chili-chips-ba/openPCIE/0.doc/text/README.md

# Text versions of project documents

Plain-text (Markdown) versions of openPCIE documents that are otherwise only available as PDF, PowerPoint, draw.io or KiCad files. They let text-based tools, including the assistant on the openPCIE product page, read the content.

| File | Generated from |
|---|---|
| `openPCIE_backplane_presentation.md` | `1.pcb/0.doc/OpenPCIE backplane presentation.pptx` (slide text) |
| `PCBA_Functional_Test_Procedure.md` | `1.pcb/0.doc/PCBA_Functional_Test_Procedure_RevB_LaTeX_Source.zip` (LaTeX source of the RevB PDF) |
| `openpci2-backplane_BOM.md` | `1.pcb/openpci2-backplane/openpci2-backplane.kicad_sch` (`kicad-cli` BOM export) |
| `openPCIE-BlockDiagram.md` | `1.pcb/0.doc/openPCIE-BlockDiagram.drawio` (text labels) |

These files are generated; edit the source documents instead. Figures and images are not included.
