chili-chips-ba/openPCIE/5.sim/models/cosim/README.md

# _VProc_ and _mem_model_ Co-simulation Components

The _VProc_ virtual processor and the _mem_model_ sparse memory model (part of _pcievhost_) components form the heart of the co-simulation for the _openPCIE_  top level simulation test bench. The `soc_cpu.VProc` is based on the virtual processor and the memory used by the running programs has access to the memory model's space. Logic can also access the memory model's address space with a provided HDL component. This component is also used in the PCIE interface driver block, and the code running on the _pcievhost_ VIP's _VProc_ also has access to the same memory via the API. Thus, these components are tied together tightly.

## _VProc_

The _VProc_ virtual processor is a VIP co-simulation component that allows a natively compiled user program to be “run” on an HDL processor component instantiated in the logic. C/C++ APIs are provided to initiate read and write transactions on the _VProc_ HDL bus, and for the
advancing simulation time.

<p align="center">VProc virtual processor</p>

_VProc_ has a generic memory mapped bus and this would normally be wrapped in a module to convert this to a standard bus or interconnect protocol, such as AXI or Avalon but, for _openPCIE_, the `soc_cpu.VPROC.picorv32` wrapper converts it to picorv32's native memory interface (`mem_valid`/`mem_ready`) with some simple logic. Multiple _VProc_ test programs components can be instantiated, each with a unique “node” number.

Since the simulator is _Vivado_, the connection between software and HDL is done using the SystemVerilog DPI-C interface. The details of connection between the HDL and running user code won’t be discussed here but suffice it to say that the user program is running in its own thread and the _VProc_ layer software provides both the API and the means to synchronise the user program with the simulation, keeping both in lock-step but allowing the user program to be free flowing code. For each instantiated _VProc_ node the user code has a specific “main” entry point of the form `VUserMain<n>`, where `<n>` is the _VProc_’s node number: e.g. `VUserMain0`, which must have C linkage for DPI requirements. The user programs are compiled into a library and, along with a _VProc_ code library, are linked into a shared object, _VProc.so_, which is loaded by the simulator at run time. There are both C and C++ low level APIs available to user programs and abbreviated versions are shown below.

<p align="center">VProc C and C++ API summary</p>

As well as basic read and write transactions methods, there is also a “tick” method. User programs run infinitely fast with respect to simulation time, so simulation time is advanced when a transaction method is called but can also be advanced with the `tick` method without a memory access transaction. Using these APIs directly gives the means to construct pure test programs that can run on the `soc_cpu.VPROC` component to drive the CSR registers in the core logic and instigate operations. A very simple program of this nature is shown below.

<p align="center">A simple VProc test program</p>

## _mem_model_

The _openPCIE_ test bench makes use of the [mem_model](https://github.com/wyvernSemi/mem_model) co-simulation component HDL. This consists of a sparse memory model , written in C as part of the [_pcievhost_](https://github.com/wyvernSemi/pcievhost) IP, with co-simulation capabilities via a `mem_model` HDL component with various Avalon style ports for memory mapped, burst and write functions. Code running in _VProc_ can access the C model directly via an API, with an abbreviated version shown below.

<p align="center">mem_model C API summary</p>

The write functions take `address` and `data` parameters and, for wider words, a little-endian flag (`le`) to select between endian
modes. The read functions take an `address` and (where appropriate) an `le` parameter and return the read value. All functions have a `node` parameter. Note that the “node” in the API functions is not the same as for _VProc_ but refers to individual address spaces. In almost all use cases this will be the same and is 0.

This model can also be accessed from the HDL using the `mem_model` HDL component, which may be instantiated any number of times, but always accesses the same memory. This allows multiple _VProc_ virtual processors and the simulated test bench logic to access a common memory space.

<p align="center">mem_model HDL component</p>

## VProc and mem_model integration into _openPCIE_

The `5.sim/models/cosim` directory contains library code for the *VProc* virtual processor and *mem_model* sparse memory model co-simulation verification IP, suitable for the Vivado logic simulation environment (other simulators are not supported at this time). This directory contains the HDL modules for the two components. The files that get compiled are `f_VProc.v` and `mem_model.sv`, which pull in the rest (`f_mem_model.v` and the Verilog header files) through `` `include`` inclusions. Thus only these two need to be listed and this directory included in the search path, which is what [`5.sim/tb.prj`](../../tb.prj) does:

```
sv work models/cosim/mem_model.sv
sv work models/cosim/f_VProc.v
```

The DPI software for both the models is pre-compiled into a static library as `lib/libcosimlnx.a` (with a `lib/libcosimwin.a` version for use with the MSYS2/mingw64 environment on Windows). The headers for the models are placed in the `include/` directory. To use the  models' APIs, the user code must include either the  `VProcClass.h` header for the *VProc* C++ API, or `VUser.h` for the *VProc* C API, and the `mem.h` header for the memory model C API. Note that the `VUser.h` and `mem.h` inclusions must be wrapped as C linkage if included in code that will be compiled as C++. E.g.:

```
extern "C" {
#include "VUser.h"
#include "mem.h"
}
```

This is only applicable when writing natively compiled simulation test code. When compiling the application code natively for *VProc*, the headers will be included correctly by the co-simulation hardware abstraction layer (HAL).

## More Information

More information on using these co-simulation models can be found in the [*VProc* manual](https://github.com/wyvernSemi/vproc/blob/master/doc/VProc.pdf) and [*mem_model* manual](https://github.com/wyvernSemi/mem_model/blob/main/doc/mem_model_manual.pdf).
