chili-chips-ba/openPCIE/5.sim/models/pcievhost/README.md

# The _pcievhost_ Verification IP

## Table of Contents

* [Introduction](#introduction)
* [The HDL Component](#the-hdl-component)
* [Link Traffic Display](#link-traffic-display)
* [The Pcie C Model](#the-pcie-c-model)
  * [Internal Architecture](#internal-architecture)
  * [User API Summary](#user-api-summary)
    * [Model Initialisation and Configuration](#model-initialisation-and-configuration)
    * [Transaction Layer Packet Generation](#transaction-layer-packet-generation)
    * [Data Link Layer Packet Generation](#data-link-layer-packet-generation)
    * [Ordered Set Generation](#ordered-set-generation)
    * [Internal Memory Access](#internal-memory-access)
    * [Internal Configuration Space Access](#internal-configuration-space-access)
    * [Receiving Data](#receiving-data)
* [Additionally Provided Functionality](#additionally-provided-functionality)
  * [C plus plus Support](#c-plus-plus-support)
  * [Running the Model as an Endpoint](#running-the-model-as-an-endpoint)
    * [Configuration Space Helper Structures](#configuration-space-helper-structures)
    * [Setting Up the Configuration Space](#setting-up-the-configuration-space)
  * [Model Limitations](#model-limitations)
    * [Endpoint Feature Limitations](#endpoint-feature-limitations)
    * [LTSSM Limitations](#ltssm-limitations)
    * [Model Verification](#model-verification)

## Introduction

The [_pcievhost_](https://github.com/wyvernSemi/pcievhost) VIP is a co-simulation element that runs a PCIe C model on a [_VProc_](https://github.com/wyvernSemi/vproc) virtual processor to drive lanes within a PCIe 1.1 or 2.0 link, with support for up to 16 lanes. The PCIe C model provides an API for generating PCIe traffic over the link with some additional helper functionality for modelling _some_ of the link training LTSSM features (not strictly part of the model). It also provides an internal sparse memory model as a target for MemRd and MemWr transactions and, when configured as an endpoint, a configuration space as a target for CfgRd and CfgWr transactions. Features of the API allow for the configuration space to be pre-programmed with valid configurations and a read-only mask overlay, though there is no support for 'special' functions like write one to clear etc.

More details of the model can be found in the [_Pcievhost_ manual](https://github.com/wyvernSemi/pcievhost/blob/master/doc/pcieVHost.pdf).

## The HDL component

A Verilog module for the _pcievhost_ model is provided in a `pcieVHost.v` file in the `5.sim/models/pcievhost/verilog/pcieVHost` directory. This is wrapped in some BFM Verilog, `pcieVHostPipex1.v`, in the same directory, which presents a single Link port, as PIPE TX and RX data signals. The diagram below shows the module's ports and parameters.

<p align=center>

</p>

The module's `pcieclk` clock and reset must be synchronous (i.e. the reset originate from the same clock domain) and the clock run at the PCIe raw bit rate $\div$ 10. So for GEN1 this is 250MHz (4000ps period) and GEN2 this is 500MHz (2000ps period). The module can convert from a sybol stream to wider PIPE widths of 16, 32 or 64, and these are converted between these widths and the symbol stream with internal logic and using a PIPE clock (`pclk`), which needs to be the `pcieclk` divided by the PIPE data width over 8. E.g. If a 64 bit PIPE data width, then the `pclk` frequency must be `pcieclk` / 8, or 31.25MHz (GEN1) or 62.5MHz (GEN2).

The model, by default, transfers 8b10b encoded data but can be configured in the software to generate unencoded and unscrambled data, where bits 7:0 are a byte value, and bit 8 is a 'K' symbol flag when set, and this configuration must be done for the _openpcie2-rc_ project.

The _pcieVHost_ component has four Parameters to configure the model. The first, `LinkWidth`, configures which lanes will be active and always starts from lane 0, defaulting to all 16 lanes. For _openpcie2-rc_, this is hardwired to 1 inside `pcieVHostPipex1`.  Note that the ports for the unused lanes are still present but can be left unconnected. The second parameter is `EndPoint`. This is used to enable endpoint features in the model and does so if set to a non-zero value, with 0 being the default setting. For _openpcie2-rc_, this should be set to 1. The thrid parameter is `NodeNum` which sets the node number of the internal _VProc_ component. Each instantiated _VProc_, whether part of a _pcievhost_ model, or not, must have a unique node number to associate itself with a particular user program. The default value for `NodeNum` is 8. Lastly, the `DataWidth` parameter sets the PIPE data port widths.

More details of the `PcieVhost` HDL component can be found in the [_pcievhost_ manual](https://github.com/wyvernSemi/pcievhost/blob/master/doc/pcieVHost.pdf).

## Link Traffic Display

The _pcievhost_ model has the capability to display link traffic to the console that the simulation is runing in, with control over the level of detail available, including disabling completely, and in which cycles it is turned on and off. It, by default, adds colour to distinguish between traffic flowing downstream from traffic flowing upstream, though the model can be configureed to disable this when, for example, runing in a GUI that can't interpret these formatting codes.

 A `ContDisps.hex` configuration file will be read by the software from a `hex` directory, below the local run directory. This allows control of displaying various PCIe layer data, from PHY, through DLL and TL, bit-mapped onto an 8 bit value. Each value is associated with a _decimal_ time stamp (in cycles) as to when the display value is enabled or not. A typical file might look like the following:

```
// Example ContDisps.hex file
// Copy to the appropriate test/hex directory, and edit as necessary.
//                      +8              +4              +2              +1
//  ,---> 11 - 8:    DispSwNoColour     DispSwEnIfEp   DispSwEnIfRc    DispSwTx
//  |,-->  7 - 4:    DispRawSym         DispPL         DispDL          DispTL
//  ||,->  3 - 0:    Unused             DispStop       DispFinish      DispAll
//  ||| ,-> Time (clock cycles, decimal)
//  ||| |                          
    370 000000000000
    002 009999999999
```
The file has two numbers on each active line, with the first hex number being the control values and the second a <u>decimal</u> value timestamp (in clock cycles) when the control should become active. For the controls, the top nibble controls enabling output for Endpoint and Root Complex links separately to allow for co-existence with other extenal link displays. So, bit 11 controls the colour formatting by enabling (when 0) or disabling (when 1). Disabling the formatting is useful if the output is sent to a simulator's GUI console which may not support the colour encoding and messes up the output. Bits 10 and 9 enable display if an endpoint end or root-complex end model respectively. By default, only received traffic is displayed but, if no other external traffic display is available, then transmitted data can be displayed if bit 8 is set.

The level of detail to display is controlled by bits 4 to 7. The bit 7 can enable display of raw data link data, without any processing, though generates a lot of output and is hard to interpret. Bits 6 dow to 4 control formatted output for the three main levels of PCIe traffic; namely physical, data link and transactions layers, bits 6 down to 4 controlling these respectively. The display will automatically indent higher layers if lower layers are enabled to allow easy distinguishing of the output.

The lowest nibble has some simulator control in bits 1 and 2, to either stop the simulation (without exiting) or finish the simulation (end and close). Bit 0 is a 'force all' control to display all layers of the link traffic, regardless of the other settings.

A fragment of some link display output, using the `ContDisps.hex` file example above, is shown in the diagram below:

<p align=center>
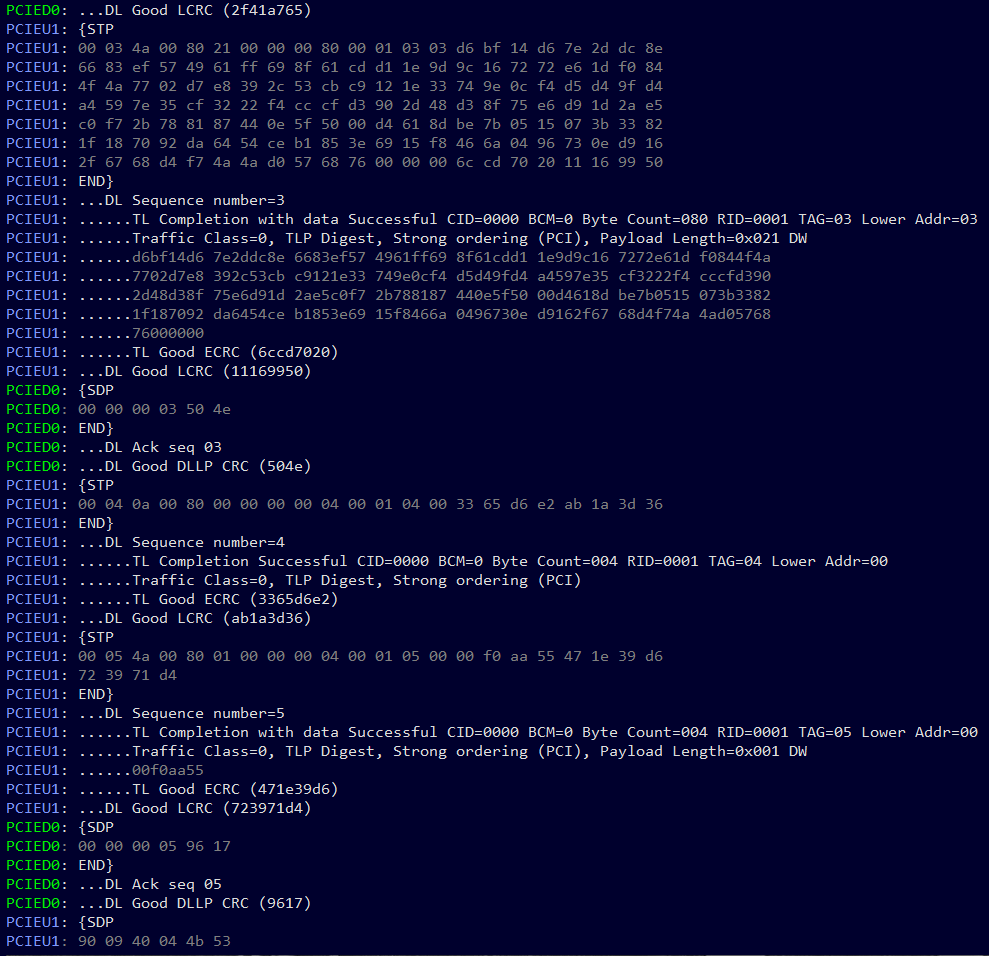
[picture p65: 5.sim/models/pcievhost/images/pcie_disp_terminal.png]

</p>

More details on the link display can be found in the [_pcievhost_ manual](https://github.com/wyvernSemi/pcievhost/blob/master/doc/pcieVHost.pdf).

## The PCIe C Model

### Internal Architecture

The diagram below summarises the core PCIe model functionality, along with the connection to a logic simulation via the _VProc_ co-simulation component.

<p align=center>
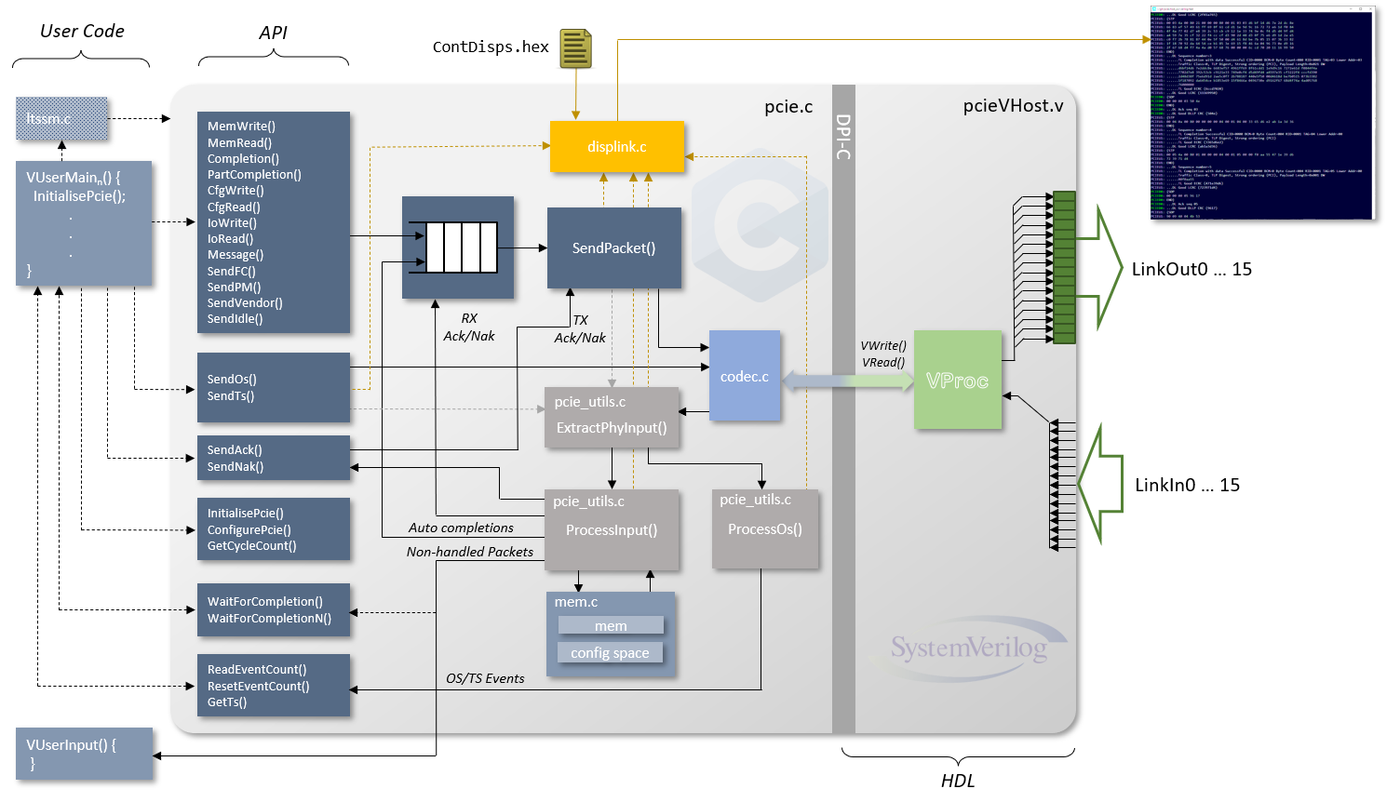
[picture p66: 5.sim/models/pcievhost/images/pcievhost_architecture.png]

</p>

On the left of the diagram are the two user supplied functions. The `VUserMain`<i>n</i> function is the main entry point for user code and this has access to the [model's API](#user-api-summary). Optionally, a user callback function can be registered (`VUserInput` in the diagram) that gets called to with non-handled packets (e.g. read completions) that are received over the link.

The left column of boxes are the various API functions available, categorised by function. The first group generate TLP or DLLP packets that get queued, before being sent to `SendPacket`. The non-automatic sending of ACKs and NAKs bypass the queue and are sent straight to the `SendPacket` function. The `SendPacket` function itself sends its TLP or DLLP packets to the `codec` which scrambles and encodes the data and drives the output on the link.

The `codec` code also process input data, decoding and descrambling, passing on to `ExtractPhyInput`. Training sequences and other ordered set data is sent to `ProcessOs` whilst TLPs and DLLPs are sent to `ProcessInput`. The API can read received OS event counts from the `ProcessOs` function. `ProcessInput` has access to the internal memory for MemRd and MemWr TLPs and (for endpoints) the config space for CfgRd and CfgWr TLPs. It will automatically generate (valid) completions for reads and add to the queue. All other TLPs are sent to any registed user callback.

### User API Summary

The _pcievhost_ model is a highly complex model and the API is quite large to match this. This document can only summarise the main features and usage and reference to the [_Pcievhost_ manual](https://github.com/wyvernSemi/pcievhost/blob/master/doc/pcieVHost.pdf) _must_ be made for the finer details of argumets and usage. The information below refers to the low level C model's API but a C++ class (`pcieModelClass`) is also provided which wraps the functions up into class methods which are slightly easier to use.

#### Model Initialisation and Configuration

| **API Function** | **Description** |
|---|---|
| `InitialisePcie` | Initialise the model |
| `ConfigurePcie` | Configure the model |
| `ConfigurePcieLtssm`  | Configure the model's LTSSM (part of the external LTSSM model, API defined in `ltssm.h`)|
| `PcieSeed` | Seed internal random number generator |

The `InitailsePcie` is called before any other function to initialise the model. The user can supply a pointer to a callback function which will be called with data for all unhandled received packets. Optionally a user supplied pointer may also be gived which is returned when the callback is called, allowing a user to store away key information for cross checking, verification or any other purpose. The model does not process this pointer itself.

The model is highly configurable with many different parameters which may be set, one at a time, using the `ConfigurePcie` and `ConfigurePcieLtssm` functions that take a type and, where applicable, value argument. .

##### Configuration via ConfigurePcie

The following table shows the valid configuration `type` settings and expected `value` for the use with the `ConfigurePcie(type, value)` function.

| **TYPE** |**VALUE**|**UNITS**| **Description** |
|---|---|---|---|
| CONFIG_FC_HDR_RATE | yes | cycles  | Rx Header consumption rate (default 4) |
| CONFIG_FC_DATA_RATE | yes | cycles  | Rx Data consumption rate (default 4) |
| CONFIG_ENABLE_FC | no | | Enable auto flow control (default) |
| CONFIG_DISABLE_FC | no | | Disable auto flow control |
| CONFIG_ENABLE_ACK | yes | cycles  | Enable auto acknowledges with processing rate (default rate 1) |
| CONFIG_DISABLE_ACK | no | | Disable auto acknowledges |
| CONFIG_ENABLE_MEM | no | | Enable internal memory (default) |
| CONFIG_DISABLE_MEM | no | | Disable internal memory |
| CONFIG_ENABLE_SKIPS | yes | cycles  | Enable regular Skip ordered sets, with interval (default interval 1180) |
| CONFIG_DISABLE_SKIPS | no | | Disable regular Skip ordered sets |
| CONFIG_DISABLE_SCRAMBLING | no | | Disable data scrambling |
| CONFIG_ENABLE_SCRAMBLING | no | | Enable data scrambling (default) |
| CONFIG_DISABLE_8B10B | no | | Disable 8b10b encoding and decoding |
| CONFIG_ENABLE_8B10B | no | | Enable 8b10b encoding and decoding (default) |
| CONFIG_DISABLE_ECRC_CMPL | no | | Disable ECRC auto-generation on completions for requests with ECRCs |
| CONFIG_ENABLE_ECRC_CMPL | no | | Enable ECRC auto-generation on completions for requests with ECRCs (default) |
| CONFIG_ENABLE_UR_CPL | no | | Enable auto unsupported request completions (default) |
| CONFIG_DISABLE_UR_CPL | no | | Disable auto unsupported request completions |
| CONFIG_ENABLE_INTERNAL_MEM | no | | Enable internal memory (default) |
| CONFIG_DISABLE_INTERNAL_MEM | no | | Disable internal memory (packets passed to user callback if registered) |
| CONFIG_ENABLE_DISPLINK_COLOUR  | no | | Enable colour formatting of link display output (default) |
| CONFIG_DISABLE_DISPLINK_COLOUR | no | | Disable colour formatting of link display output |
| CONFIG_POST_HDR_CR† | yes | credits | Initial advertised posted header credits (default 32) |
| CONFIG_POST_DATA_CR† | yes | credits | Initial advertised posted data credits (default 1K) |
| CONFIG_NONPOST_HDR_CR† | yes | credits | Initial advertised non-posted header credits (default 32) |
| CONFIG_NONPOST_DATA_CR† | yes | credits | Initial advertised non-posted data credits (default 1) |
| CONFIG_CPL_HDR_CR† | yes | credits | Initial advertised completion header credits (default ∞) |
| CONFIG_CPL_DATA_CR† | yes | credits | Initial advertised non-posted data credits (default ∞) |
| CONFIG_CPL_DELAY_RATE† | yes | cycles  | Auto completion delay rate (default 0) |
| CONFIG_CPL_DELAY_SPREAD† | yes | cycles  | Auto completion delay randomised spread (default 0) |

† Call immediately after `InitialisePcie()` to take effect from time 0

##### Configuration via ConfigurePcieLtssm

The following table shows the valid configuration `type` settings and expected `value` for use with the `ConfigurePcieLtssm(type, value)` function.

| **TYPE** |**VALUE**| **UNITS** | **Description** |
|---|---|---|---|
| CONFIG_LTSSM_LINKNUM†† |  yes | integer | Training sequence advertised link number (default 0) |
| CONFIG_LTSSM_N_FTS†† |  yes | integer | Training sequence number of fast training sequences (default 255) |
| CONFIG_LTSSM_TS_CTL†† |  yes | integer | Five bit TS control field (default 0) |
| CONFIG_LTSSM_DETECT_QUIET_TO†† |  yes | cycles | Detect quiet timeout (default 1500/6M, depending if `LTSSM_ABBREVIATED` defined or not) |
| CONFIG_LTSSM_POLL_ACTIVE_TO_COUNT†† |  yes | cycles | Polling active TX count (default 16/1024, depending if `LTSSM_ABBREVIATED` defined or not)|
| CONFIG_LTSSM_ENABLE_TESTS†† |  yes | bit mask  | Enable LTSSM test exceptions (default 0) |
| CONFIG_LTSSM_FORCE_TESTS†† |  yes | bit mask  | Force LTSSM test exceptions (default 0) |
| CONFIG_LTSSM_DISABLE_DISP_STATE†† |  yes | integer | Disable display of LTSSM state to console (default 0 = display state) |

†† Call before calling `InitLink()` to take effect in training sequences.

Further details of model configuration are to be found in the [_pcievhost_ manual](https://github.com/wyvernSemi/pcievhost/blob/master/doc/pcieVHost.pdf)

Internally, the model can generate random data and the generator can be seeded with `PcieSeed`. The internal code uses `PcieRand` to generate randome data, but this is also available as part of the API. Finally, the model keeps a count of cycles internally, and the value may be retrieved with `GetCycleCount`.

#### Transaction Layer Packet Generation

| **API Function** | **Description** |
|---|---|
| `MemWrite` | Generate a memory write transaction |
| `MemRead` | Generate a memory read transaction |
| `Completion` | Generate a Completion transaction |
| `PartCompletion` | Generate a partial completion transaction |
| `CfgWrite` | Generate a configuration space write transaction |
| `CfgRead` | Generate a configuration space read transaction  |
| `IoWrite` | Generate an IO write transaction |
| `IoRead` | Generate an IO read transaction |
| `Message` | Generation a message transaction |

The above functions are called with varying arguments (see the [_pcievhost_ manual](https://github.com/wyvernSemi/pcievhost/blob/master/doc/pcieVHost.pdf) for details) and all have a 'digest' version (e.g. `MemWriteDigest`) which have an additional argument to select whether a digest (i.e. an ECRC) is generated or not, with the above functions defaulting to generating a digest. There are also 'delay' versions of the `Completion` and `PartCompletion` function which will not send out the packets immediately but after some delay as configured during the model initialisation.

A user program can also wait for a completion to arrive, or a number of completions, with the `WaitForCompletion` and `WaitForCompletionN` functions.

#### Data Link Layer Packet Generation

| **API Function** | **Description** |
|---|---|
| `SendAck` | Send an acknowledgement packet |
| `SendNak` | Send an not-acknowledgement packet |
| `SendFC` | Send a flow control packet |
| `SendPM` | Send a power manegement packet |
| `SendVendor` | Send a vendor specific packet |

#### Ordered Set Generation

| **API Function** | **Description** |
|---|---|
| `SendIdle` | Send idle symbols on all active lanes |
| `SendOs` | Send an ordered set down all active lanes |
| `SendTs` | Send a training sequence ordered set on all active lanes | 

These functions generate ordered sets on the link lanes, with `SendTs` automatically generating lane numbers if not called to generate `PAD`. Internally the model keeps counts of the reception of training sequences on each lane and these can be read using the `ReadEventCount` function and, if required, the counts may be reset with `ResetEventCount`. To fetch the last training sequence processed on a given lane, the `GetTS` function can be used.

#### Internal Memory Access

| **API Function** | **Description** |
|---|---|
| `WriteRamByte` | Write a byte to internal memory |
| `WriteRamHWord` | Write a 16-bit half-word to internal memory |
| `WriteRamWord` | Write a 32-bit word to internal memory |
| `WriteRamDWord` | Write a 64-bit double word to internal memory |
| `ReadRamByte` | Read a byte from internal memory |
| `ReadRamHWord` | Read a 16-bit half-word from internal memory |
| `ReadRamWord` | Read a 32-bit word from internal memory |
| `ReadRamDWord` | Read a 64-bit double word from internal memory |
| `WriteRamByteBlock` | Write a block of bytes to internal memory  |
| `ReadRamByteBlock`  | Read a block of bytes from internal memory |

The _pcievhost_ model has an internal sparse memory model which can support a full 64-bit address space. This is used as a target for received MemWr and MemRd transactions. As well as accessing this space via PCIe transactions, the memory model has its own API functions to do reads and writes of bytes, 16-bit words, and 32-bit words, as well as reading and writing of multiple byte blocks.

#### Internal Configuration Space Access

| **API Function** | **Description** |
|---|---|
| `WriteConfigSpace` | Write a 32-bit value to the configuration space |
| `ReadConfigSpace` | Write a 32-bit value from the configuration space |
| `WriteConfigSpaceMask` | Write a 32-bit mask value to the configuration space mask (bits set to 1 become read only over PCIe) |
| `ReadConfigSpaceMask`  | Read a 32-bit value from the configuration space mask |

If a _pcievhost_ is configured as an endpoint it then has an internal 4096 by 32-bit configuration memory. By default this is blank, but CfgWr and CfgRd transactions can access this space. To configure this space the `WriteConfigSpace` (and its `ReadConfigSpace` counterpart) can be used to set up an valid configuration space settings. A shadow mask memory is also available, which defaults to all 0s, to set any number of bits to be read only. There is a one-to-one correspondence to the main configuration memory, but if a mask bit is set, then the corresponding config space bit becomes read only when accessed over the link with CfgWr transactions. The mask memory is set using the `WriteConfigSpaceMask` and can be inspected with `ReadConfigSpaceMask`.

#### Receiving Data

If a user callback function was registered when `InitialisePcie()` was called this will be invoked with any received packet that the model did not handle itself. The most common of these will be completion packets received for a memory or configuration read. When the callback is invoked the packet, via a point of type `pPkt_t` is passed in along with a status and, if a user pointer was passed in when registering the callback, this is also passed in.

The `status` value is bit map of error flags ORed together. The following table lists the possible bit seeting types, with `PKT_STATUS_GOOD` being a valueo fo 0.

|**Status Value** | **Packet type** |
|---|---|
|PKT_STATUS_GOOD | all |
|PKT_STATUS_BAD_LCRC | TLP and DLLP |
|PKT_STATUS_BAD_ECRC | TLP |
|PKT_STATUS_UNSUPPORTED | TLP completion  |
|PKT_STATUS_NULLIFIED | TLP |

The received packet is passed in with a pointer to a structure as defined below:

```C
typedef struct  pkt_struct {
    pPkt_t      NextPkt;     // Pointer to next packet to be sent
    PktData_t   *data;       // Pointer to a raw data packet, terminated by -1
    int         seq;         // DLL sequence number for packet (-1 for DLLP)
    int         Retry;
    uint32_t    TimeStamp;
    uint32_t    ByteCount;
} sPkt_t;
```
The `NextPtr` can be ignored by the callback, but the `data` argument is a pointer to a set of byte values representing the whole raw packet. Each byte value is of `PktData_t` type, which is not an 8-bit type, so cannot be overlaid as an array of `char`, for instance. The last byte in teh packet is followed by a -1 to mark the end of the data. The `seq` field gives the sequence number of the received packet and the `Retry` field is a count ofthe number of retries for the packet that have already occured. A `Timestamp` field provides a clock cycle count for the time the packet was fuly received and passed to the callback. Finally, a `ByteCount` gives the size of the payload for the packet (in bytes), which can be 0.

A set of helper macros are avilable to process the raw packet data. To extract the payload data, for example the `GET_TLP_PAYLOAD_PTR(pkt)` returns a pointer to the beginning of the payload data (if any), taking care of whether the packet has a 3 or 4 word header. Using this, along with the `ByteCount` value, the data can be extracted from the packet. Some highlights from the set of available macros are given below :

|**Macro** |**Description** |
|---|---|
| GET_TLP_TYPE(pkt) | Get the type code of the TLP packet (as defined in `pci_express.h`) |
| GET_TLP_ADDRESS(pkt) | Get a TLP's address of as `uint64_t` |
| GET_TLP_FBE(pkt) | Get a TLP packet's first byte enable value |
| GET_TLP_LBE(pkt) | Get aTLP packet's last byte enable value |
| GET_TLP_RID(pkt) | Get a TLP packet's requester ID |
| GET_TLP_TAG(pkt) | Get a TLP packet's tag value |
| TLP_HAS_DIGEST(pkt)  | Flag if a TLP has an ECRC digest |
| TLP_IS_POSTED(pkt) | Flag if a TLP is a posied request |

The TLP packet types defined (in `pci_express.h`) are as shown in the table below:
| **TYPE** | **Description** |
|---|---|
|TL_MRD32 | A memory read request with a 32-bit address |
|TL_MRD64 | A memory read request with a 64-bit address |
|TL_MRDLCK32 | A locked memory read request with a 32-bit address |
|TL_MRDLCK64 | A locked memory read request with a 64-bit address |
|TL_MWR32 | A memory write with a 32-bit address |
|TL_MWR64 | A memory write with a 64-bit address |
|TL_IORD | A memory I/O read request |
|TL_IOWR | A memory I/O write |
|TL_CFGRD0 | A Type 0 configuration space read request |
|TL_CFGWR0 | A Type 0 configuration space write |
|TL_CFGRD1 | A Type 1 configuration space read request |
|TL_CFGWR1 | A Type 1 configuration space write |
|TL_MSG | A message with no payload |
|TL_MSGD | A message with payload |
|TL_CPL | A completion with no payload |
|TL_CPLD | A completion with payload |
|TL_CPLLK | A locked access completion with no payload |
|TL_CPLDLK | A locked access completion with payload |

Once a packet has been processed it is <u>vital</u> that the packet passed in to the callback is freed. A `DISCARD_PACKET(pkt)` macro is provided for this purpose, freeing all required memory. This is usually the last line of the callback function as all data will be lost at this point. If any of the data is to be retained it must be copied from the packet before calling this macro. This is what the optional user point might be used for (if one registered on the call to `InitialisePcie()`), where it it might be a point to a queue, and the relevant parts of the packeted added to the queue to be processed by the main part of the program.

A simple example callback function for a _pcievhost_ configured as a root complex, is shown below:

```C
 void VUserInput_0(pPkt_t pkt, int status, void* usrptr)
{
    int idx;

    // Is a DLLP
    if (pkt->seq == DLLP_SEQ_ID)
    {
        DebugVPrint("---> VUserInput_0 received DLLP\n");
    }
    // A TLP
    else
    {
        DebugVPrint("---> VUserInput_0 received TLP sequence %d of %d bytes at %d\n",
                       pkt->seq, GET_TLP_LENGTH(pkt->data), pkt->TimeStamp);

        // If a completion, extract the TPL payload data and display
        if (pkt->ByteCount)
        {
            // Get a pointer to the start of the payload data
            pPktData_t payload = GET_TLP_PAYLOAD_PTR(pkt->data);

            // Display the data
            DebugVPrint("---> ");
            for (idx = 0; idx < pkt->ByteCount; idx++)
            {
                DebugVPrint("%02x ", payload[idx]);
                if ((idx % 16) == 15)
                {
                    DebugVPrint("\n---> ");
                }
            }

            if ((idx % 16) != 0)
            {
                DebugVPrint("\n");
            }
        }
    }

    // Once packet is finished with, the allocated space *must* be freed.
    // All input packets have their own memory space to avoid overwrites
    // with shared buffers.
    DISCARD_PACKET(pkt);
}
```
An equivalent callback function for a _pcievhost_ configured as an endpoint woUld be much simpler, or even one not registered at all if the model has all the internal memory and auto-completion features enabled (the default). If a callback is registered, only unhandled packets would be sent to the function, such as message packets and I/O access packets.

## Additionally Provided Functionality

The _pcievhost_ model was originally designed as a Root Complex PCIe 1.1 and 2.0 traffic generator, with the API features as described above. In that sense it did not have higher level features. In particular it did not have link training and status state machine (LTSSM) features or data link layer initialistion code. <i><b>Partial</b></i> implementations now form part of the model for demonstration and education purposes. These use the API from above to go through an abbreviated link training and a DLL initialisation using the following API functions:

| **API Function** | **Description** |
|---|---|
| `InitLink` | Go through an LTSSM link training sequence (part of the separate LTSSM model, defined in `ltssm.h`) |
| `InitFC` | Initialise DLL flow control credits |

These functions only provide enough functionality to go through an initialisation that has no exception conditions. The LTSSM also only goes through one training sequence and can't, as yet, go through the Recovery state, and retrain at a higher generation (i.e. from GEN1 to GEN2). The LTSSM has various states that are long to execute due to various TS event counts and cycle times. The model's demonstration `ltssm.c` code can be complied for an 'abbreviated' power up by defining `LTSSM_ABBREVIATED` when compiling the code. This reduces the `Polling.Active` TX count from 1024 to 16 and the `Detect.Quite` timeout count from 12ms to 1500 cycles.

All the hooks are in place for the other paths through the LTSSM, but these are not implemented and the LTSSM was never meant to be part of the _pcievhost_ model but provided as a guide to coding one and as a reference example. The DLL initialisation is simpler and there are no outstanding features for the implementation at this time. Again,this is demonstration and example code only.

### C plus plus Support

In addition to the C API functions described above, there is support for C++ via an API class, declared in `pcieModelClass.h` (the implementation is compiled into the supplied library), called `pcieModelClass`, that wraps up the low level C functions. It is basically a one-to-one mapping of the C functions to methods in the class, but with some defaulted values and the need to supply the node number abstracted away, being set on construction of the class object. Note that the LTSSM model is implemented in separate source files (`ltssm.c` and `ltssm.h`) and the API for this (consisting of the `ConfigurePcieLtssm()` and `initLink()` functions) is not part of `pcieModeClass`.

```C++
class pcieModelClass
{
public:
               pcieModelClass       (const unsigned nodeIn) : node (nodeIn) {};

    // TLP generation
    pPktData_t memWrite             (const uint64_t addr, const PktData_t *data, const int length, const int tag,
                                     const uint32_t rid, const bool queue = false, const bool digest = false);

    pPktData_t memRead              (const uint64_t addr, const int length, const int tag, const uint32_t rid,
                                    const bool queue = false, const bool digest = false);

    pPktData_t completion           (const uint64_t addr, const PktData_t *data, const int status, const int fbe, const int lbe,
                                     const int length,  const int tag, const uint32_t cid, const uint32_t rid,
                                     const bool queue = false, const bool digest = false);

    pPktData_t partCompletion       (const uint64_t addr, const PktData_t *data, const int status, const int fbe, const int lbe,
                                     const int rlength, const int length, const int tag, const uint32_t cid, const uint32_t rid,
                                     const bool queue = false, const bool digest = false);

    pPktData_t cfgWrite             (const uint64_t addr, const PktData_t *data, const int length, const int tag,
                                    const uint32_t rid, const bool queue = false, const bool digest = false);

    pPktData_t cfgRead              (const uint64_t addr, const int length, const int tag, const uint32_t rid,
                                     const bool queue = false, const bool digest = false);

    pPktData_t ioWrite              (const uint64_t addr, const PktData_t *data, const int length, const int tag,
                                     const uint32_t rid, const bool queue = false, const bool digest = false);

    pPktData_t ioRead               (const uint64_t addr, const int length, const int tag, const uint32_t rid,
                                     const bool queue = false, const bool digest = false);

    pPktData_t message              (const int code, const PktData_t *data, const int length, const int tag, const uint32_t rid,
                                    const bool queue = false, const bool digest = false);

    // Flow control initialisation
    void       initFc               (void);

    // Queue flushing
    void       sendPacket           (void)

    // Dllps
    void       sendAck              (const int seq);
    void       sendNak              (const int seq);
    void       sendFC               (const int type,  const int vc,    const int hdrfc, const int datafc, const bool queue);
    void       sendPM               (const int type,  const bool queue = false);

    void       sendVendor           (const bool queue = false);
    void       sendVendor           (const int data,  const bool queue = false);

    // Physical layer Ordered sets etc.
    void       sendIdle             (const int ticks = 1);
    void       sendOs               (const int type);
    void       sendTs               (const int identifier, const int lane_num, const int link_num, const int n_fts,
                                     const int control, const bool is_gen2 = false);

    void       waitForCompletion    (const uint32_t count = 1);
    void       initialisePcie       (const callback_t    cb_func, void *usrptr);
    void       registerOsCallback   (const os_callback_t cb_func);
    uint32_t   getCycleCount        (void);
    void       configurePcie        (const config_t type, const int value = 0);

    // Physical layer event routines
    int        resetEventCount      (const int type);
    int        readEventCount       (const int type, uint32_t *ts_data);
    TS_t       getTS                (const int lane);

    // Miscellaneous support routines
    uint32_t   pcieRand             (void);
    void       pcieSeed             (const uint32_t seed);
    void       setTxEnabled         (void);
    void       setTxDisabled        (void);
    void       getPcieVersionStr    (char* sbuf, const int bufsize);

    // Memory access
    void       writeRamByteBlock    (const uint64_t addr, const PktData_t* const data, const int fbe, const int lbe,
                                     const int length);
    int        readRamByteBlock     (const uint64_t addr, PktData_t* const data, const int length);

    void       writeRamByte         (const uint64_t addr, const uint32_t data);
    void       writeRamHWord        (const uint64_t addr, const uint32_t data, const int little_endian = 0);
    void       writeRamWord         (const uint64_t addr, const uint32_t data, const int little_endian = 0);
    void       writeRamDWord        (const uint64_t addr, const uint64_t data, const int little_endian = 0);
    uint32_t   readRamByte          (const uint64_t addr);
    uint32_t   readRamHWord         (const uint64_t addr, const int little_endian = 0);
    uint32_t   readRamWord          (const uint64_t addr, const int little_endian = 0);
    uint64_t   readRamDWord         (const uint64_t addr, const int little_endian = 0);

    // Configuration space access
    void       writeConfigSpace     (const uint32_t addr, const uint32_t data);
    uint32_t   readConfigSpace      (const uint32_t addr);
    void       writeConfigSpaceMask (const uint32_t addr, const uint32_t data);
    uint32_t   readConfigSpaceMask  (const uint32_t addr);

private:
    unsigned node;
};
```

### Running the Model as an Endpoint

The _pcievhost_ VIP was originally designed to generate PCIe traffic as a root complex. The addition of endpoint features was to allow a target for the main root complex model to be tested. This mainly consisted of the addition of a configuration space memory and for out generation of completions for both the internal memory model and  the configuratiion space. As such, the user program on the end point does not need to do very much if it does not need to instigate transactions but only respond. The code fragment below shows an abbreviated program running on a _pcievhost_ model.

```C
#include <stdio.h>
#include <stdlib.h>
#include "pcieModelClass.h"
#include "ltssm.h"

static void VUserInput_1(pPkt_t pkt, int status, void* usrptr)
{
  /* Do stuff here with input */
}

static void ConfigureType0PcieCfg (pcieModelClass *pcie)
{
  /* Initialise the configuration space and mask here */
}

extern "C" void VUserMain1(int node)
{
    // Create a pcie model API object for this node 
    pcieModelClass *pcie = new pcieModelClass(node);

    // Initialise PCIe VHost, with input callback function and no user pointer.
    pcie->initialisePcie(VUserInput_1, NULL);

    // Configure the model for PIPE operation
    pcie->configurePcie(CONFIG_DISABLE_SCRAMBLING);
    pcie->configurePcie(CONFIG_DISABLE_8B10B);

    // Configure LTSSM for full timings (longer link training simulation time)
    ConfigurePcieLtssm(CONFIG_LTSSM_DETECT_QUIET_TO,      6000000, node);
    ConfigurePcieLtssm(CONFIG_LTSSM_POLL_ACTIVE_TO_COUNT, 1024,    node);

    // Make sure the link is out of electrical idle
    VWrite(LINK_STATE, 0, 0, node);

    // Use node number as seed
    pcie->pcieSeed(node);

    // Construct an endpoint PCIe configuration space
    ConfigureType0PcieCfg(pcie);

    // Initialise the link for 16 lanes
    InitLink(16, node);

    // Initialise flow control
    pcie->initFc();

    // Send out idles forever
    while (true)
    {
        pcie->sendIdle(100);
    }
}
```

Here the model is initialised, registering a user callback function (`VUserInput_1`) for receiving data. The model is then configured with any required settings to override defaults, before configuring the LTSSM. A low level _VProc_ API call is made to get the link out of electrical idle state before configuring the model. After this a seed is set for random data generation before calling a local function to set up the endpoint configuration space. The link training is then invoked before initialising the DLL flow control. From this point on, a loop continuously calls `SendIdle` for sending idles over the link. The model will respond to received transactions, overriding the idles with, for example, completions for MemRd transactions, and all the DLL ACKs and flow control DLLP packets etc. In this sense, unless transactions are to be instigated from the endpoint, no further programming is required.

#### Configuration Space Helper Structures

The _pcievhost_ model provides some basic helper structures to allow the building up of a valid endpoint Type 0 configuration space, in the `pci_express.h` header. These are limited to the PCI compatible region and comprise the minimal capability structures. For each type of capability a structure is defined with each of the fields, and a matching uinion is also defined with the structure and an array of 32-bit words to metch the size of the capability.

| **Structure** | **Union** | **Description** |
|---|---|---|
| `cfg_spc_type0_struct_t` | `cfg_spc_type0_t` | Type 0 configuration space |
| `cfg_spc_pcie_caps_struct_t` | `cfg_spc_pcie_caps_t` | PCIe capabilities |
| `cfg_spc_msi_caps_struct_t` | `cfg_spc_msi_caps_t` | Message Signalled Interrupt cpabilities | 
| `cfg_spc_pwr_mgmnt_caps_struct_t` | `cfg_spc_pwr_mgmnt_caps_t`  | Power Management capabilities |

The individual fields of the structure can be filled in and then the word buffer used with `WriteConfigSpace` to update the model. The next section provides examples of their use.

#### Setting Up the Configuration Space

In the previous example for an endpoint program the `ConfigureType0PcieCfg` function was left blank for brevity purposes. By default, the configuration space acts just like a 4K &times; 32bit memory space initilaised to 0. Configurations writes will have all bits written to the word addressed and subsequent reads will read back the value written. In order to configure for a model of a real configuration space the pcie model's API provides the aforementions methods and some structures to aid constructing capabilities. The use of thmode's features does require understanding of PCIe configuration space requirements but an example is given below for a <u>minimal</u> Type 0 configuration space for a proprietary network card with no PCIe extended capabilities. For more information about PCIe configurations spaces see the [PCIe Primer](https://drive.google.com/file/d/1CECftcznLwcKDADtjpHhW13-IBHTZVXx) Part 4).

```C
static void ConfigureType0PcieCfg (pcieModelClass *pcie)
{
    unsigned        next_cap_ptr = 0;
    
    // -------------------------------------
    // PCI compatible header
    // -------------------------------------
    
    cfg_spc_type0_t     type0;
    cfg_spc_type0_t     type0_mask;
    cfg_spc_pcie_caps_t pcie_caps;
    cfg_spc_pcie_caps_t pcie_caps_mask;
    cfg_spc_msi_caps_t  msi_caps;
    cfg_spc_msi_caps_t  msi_caps_mask;
    pwr_mgmnt_caps_t    pwr_mgmnt_caps;
    pwr_mgmnt_caps_t    pwr_mgmnt_caps_mask;

    // Default to all zeros and read-only
    for (int idx = 0; idx < (CFG_PCI_HDR_SIZE_BYTES/4); idx++)
    {
        type0.words[idx]      = 0x00000000;
        type0_mask.words[idx] = 0xffffffff;
    }

    next_cap_ptr += CFG_PCI_HDR_SIZE_BYTES;

    // Construct PCI compatible structure value, and set writable bits where appropriate
    type0.type0_struct.vendor_id               = 0x14fc;
    type0.type0_struct.device_id               = 0x0002;
    type0.type0_struct.command                 = 0x0006;     type0_mask.type0_struct.command = 0xfab8;
    type0.type0_struct.status                  = 0x0010;
    type0.type0_struct.revision_id             = 0x01;
    type0.type0_struct.prog_if                 = 0x00;       // don't care
    type0.type0_struct.subclass                = 0x80;       // other
    type0.type0_struct.class_code              = 0x02;       // network controller
    type0.type0_struct.cache_line_size         = 0x00;       type0_mask.type0_struct.cache_line_size = 0x00; 
    type0.type0_struct.bar[0]                  = 0x00000008; type0_mask.type0_struct.bar[0]          = 0x00000fff; // 32-bit, prefetchable, 4K
    type0.type0_struct.bar[1]                  = 0x00000008; type0_mask.type0_struct.bar[1]          = 0x000003ff; // 32-bit, prefetchable, 1K
    type0.type0_struct.bar[2]                  = 0x00000000;
    type0.type0_struct.bar[3]                  = 0x00000000;
    type0.type0_struct.bar[4]                  = 0x00000000;
    type0.type0_struct.bar[5]                  = 0x00000000;
    type0.type0_struct.expansion_rom_base_addr = 0x00000000; type0_mask.type0_struct.expansion_rom_base_addr = 0x000007fe;
    type0.type0_struct.capabilities_ptr        = next_cap_ptr;

    // Update config space and mask with values
    for (int idx = 0; idx < (CFG_PCI_HDR_SIZE_BYTES/4); idx++)
    {
        pcie->writeConfigSpace     (next_cap_ptr - CFG_PCI_HDR_SIZE_BYTES + idx*4, type0.words[idx]);
        pcie->writeConfigSpaceMask (next_cap_ptr - CFG_PCI_HDR_SIZE_BYTES + idx*4, type0_mask.words[idx]);
    }
    
    // -------------------------------------
    // PCIe capability
    // -------------------------------------

    // Default to all zeros and read-only
    for (int idx = 0; idx < (CFG_PCIE_CAPS_SIZE_BYTES/4); idx++)
    {
        pcie_caps.words[idx]      = 0x00000000;
        pcie_caps_mask.words[idx] = 0xffffffff;
    }

    next_cap_ptr += CFG_PCIE_CAPS_SIZE_BYTES;

    pcie_caps.pcie_caps_struct.cap_id         = 0x10;
    pcie_caps.pcie_caps_struct.next_cap_ptr   = next_cap_ptr;
    pcie_caps.pcie_caps_struct.device_caps    = 0x00000001;   // max payload = 256 bytes
    pcie_caps.pcie_caps_struct.device_control = 0x2810;       pcie_caps_mask.pcie_caps_struct.device_control = 0x0000;
    pcie_caps.pcie_caps_struct.link_caps      = 0x0003fc12;   
    pcie_caps.pcie_caps_struct.link_control   = 0x0000;       pcie_caps_mask.pcie_caps_struct.link_control   = 0xf004;
    pcie_caps.pcie_caps_struct.link_status    = 0x0091;       
    pcie_caps.pcie_caps_struct.link_control2  = 0x0002;       pcie_caps_mask.pcie_caps_struct.link_control2  = 0xe06f;

    for (int idx = 0; idx < (CFG_PCIE_CAPS_SIZE_BYTES/4); idx++)
    {
        pcie->writeConfigSpace     (next_cap_ptr - CFG_PCIE_CAPS_SIZE_BYTES + idx*4, pcie_caps.words[idx]);
        pcie->writeConfigSpaceMask (next_cap_ptr - CFG_PCIE_CAPS_SIZE_BYTES + idx*4, pcie_caps_mask.words[idx]);
    }
    
    // -------------------------------------
    // MSI capability
    // -------------------------------------

    // Default to all zeros and read-only
    for (int idx = 0; idx < (CFG_MSI_CAPS_SIZE_BYTES/4); idx++)
    {
        msi_caps.words[idx]      = 0x00000000;
        msi_caps_mask.words[idx] = 0xffffffff;
    }

    next_cap_ptr += CFG_MSI_CAPS_SIZE_BYTES;

    msi_caps.msi_caps_struct.cap_id           = 0x05;
    msi_caps.msi_caps_struct.next_cap_ptr     = next_cap_ptr;
    msi_caps.msi_caps_struct.mess_control     = 0x0080;     msi_caps_mask.msi_caps_struct.mess_control = 0xff8e;
    msi_caps.msi_caps_struct.mess_addr_lo     = 0x00000000; msi_caps_mask.msi_caps_struct.mess_addr_lo = 0x00000003;
    msi_caps.msi_caps_struct.mess_addr_hi     = 0x00000000; msi_caps_mask.msi_caps_struct.mess_addr_hi = 0x00000000;
    msi_caps.msi_caps_struct.mess_data        = 0x0000;     msi_caps_mask.msi_caps_struct.mess_data    = 0x0000;
    msi_caps.msi_caps_struct.mask             = 0x00000000; msi_caps_mask.msi_caps_struct.mask         = 0x00000000;
    msi_caps.msi_caps_struct.pending          = 0x00000000;

    for (int idx = 0; idx < (CFG_MSI_CAPS_SIZE_BYTES/4); idx++)
    {
        pcie->writeConfigSpace     (next_cap_ptr - CFG_MSI_CAPS_SIZE_BYTES + idx*4, msi_caps.words[idx]);
        pcie->writeConfigSpaceMask (next_cap_ptr - CFG_MSI_CAPS_SIZE_BYTES + idx*4, msi_caps_mask.words[idx]);
    }

    // -------------------------------------
    // Power managment capability
    // -------------------------------------

    // Default to all zeros and read-only
    for (int idx = 0; idx < (CFG_PWR_MGMT_CAPS_SIZE_BYTES/4); idx++)
    {
        pwr_mgmnt_caps.words[idx]      = 0x00000000;
        pwr_mgmnt_caps_mask.words[idx] = 0xffffffff;
    }

    next_cap_ptr += CFG_PWR_MGMT_CAPS_SIZE_BYTES;

    pwr_mgmnt_caps.pwr_mgmnt_caps_struct.cap_id                        = 0x01;
    pwr_mgmnt_caps.pwr_mgmnt_caps_struct.next_cap_ptr                  = 0x00; // last capability
    pwr_mgmnt_caps.pwr_mgmnt_caps_struct.pwr_mgmnt_caps                = 0x0003;
    pwr_mgmnt_caps.pwr_mgmnt_caps_struct.pwr_mgmnt_control_status      = 0x0008;
    pwr_mgmnt_caps_mask.pwr_mgmnt_caps_struct.pwr_mgmnt_control_status = 0xe0fc;

    for (int idx = 0; idx < (CFG_PWR_MGMT_CAPS_SIZE_BYTES/4); idx++)
    {
        pcie->writeConfigSpace     (next_cap_ptr - CFG_PWR_MGMT_CAPS_SIZE_BYTES + idx*4, pwr_mgmnt_caps.words[idx]);
        pcie->writeConfigSpaceMask (next_cap_ptr - CFG_PWR_MGMT_CAPS_SIZE_BYTES + idx*4, pwr_mgmnt_caps_mask.words[idx]);
    }
}
```

### Model Limitations

The _pcievhost_ model was originally conceived as a PCIe traffic pattern generator for driving an endpoint design to bridge the gap in development before a commercial sign-off VIP was made available to compliance check the implementation. The API reflects this functionality, allowing any combination of PHY, DLL and TLP patterns to be generated in order to drive an endpoint DUT. It is not a model of a root complex or an endpoint implementation, and user code must be written to drive sequences of patterns for meaningful and valid communication. Beyond this various additional functions are provided _in a limited capacity_.

#### Endpoint Feature Limitations

Endpoint features have been added to provide a target for the original _pcievhost_ model to be tested. These include an internal memory model as a target for MemRd and MemWr transactions and a configurations space as a target for CfgRd and CfgWr transactions. The configuration space can be programed, using the API, with valid config space patterns and a mask programmed to make various bits read-only. More sophisticaled register bit operatoins, such as write one to clear, are not supported.

The configurations space, by default, has no programmed pattern and must be configured in the user program running on the model using the API functions (see the example in the [Setting Up the Configuration Space](#setting-up-the-configuration-space) section).

#### LTSSM Limitations

The link training and status state machine (LTSSM) does not form part of the _pcievhost_ model proper. A _limited_ implementation is provide, as an example, in the `ltssm.c` file, and this provides enough functionality to go from electrical idle to the L0 powered up state for a given generation speed. What it does not currently do is:

  * Support any expection, error or timeout roots through the LTSSM
  * Support switching speeds through Recovery and retrain automatically
  * Switch to lower power states
  * Switch to directed states such as Disabled, Loopback or Hot Reset
  * Auto reverse lanes
  * Auto invert lane polarity
  * Auto limit link width

Hooks for all of these states are present in the code, but would need development for a full implementation. Lane width is controlled through a parameter and fixed for simulation. For GEN1 to GEN2 switching a means would also be needed to switch clock speeds at the appropriate sub-state in the LTSSM.

#### Model Verification

The _pcievhost_ model's original deployment was to drive an endpoint implementation which operated as a 16 lane GEN1 device, or an 8 lane GEN2 device. Almost all testing has been done at these widths and speeds. Support for different widths are fully implemented and tested using two _pcieVHost_ modules back to back, one as an RC and the other as an EP.
