chili-chips-ba/openPCIE/0.doc/artwork/pcie2rootc.phex.pdf

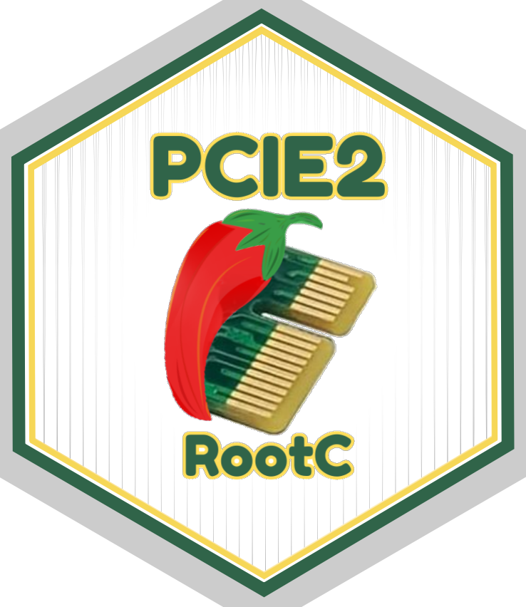
[picture p101: figure]
