chili-chips-ba/openPCIE/0.doc/artwork/openpcie.sticker.png

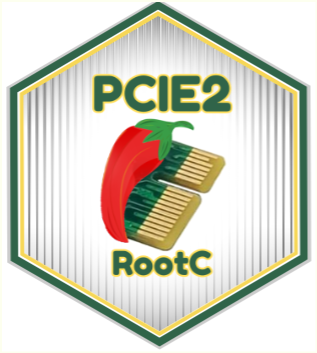
0.doc/artwork/openpcie.sticker.png
