chili-chips-ba/openPCIE/0.doc/artwork/pcie2rootc.BW.png

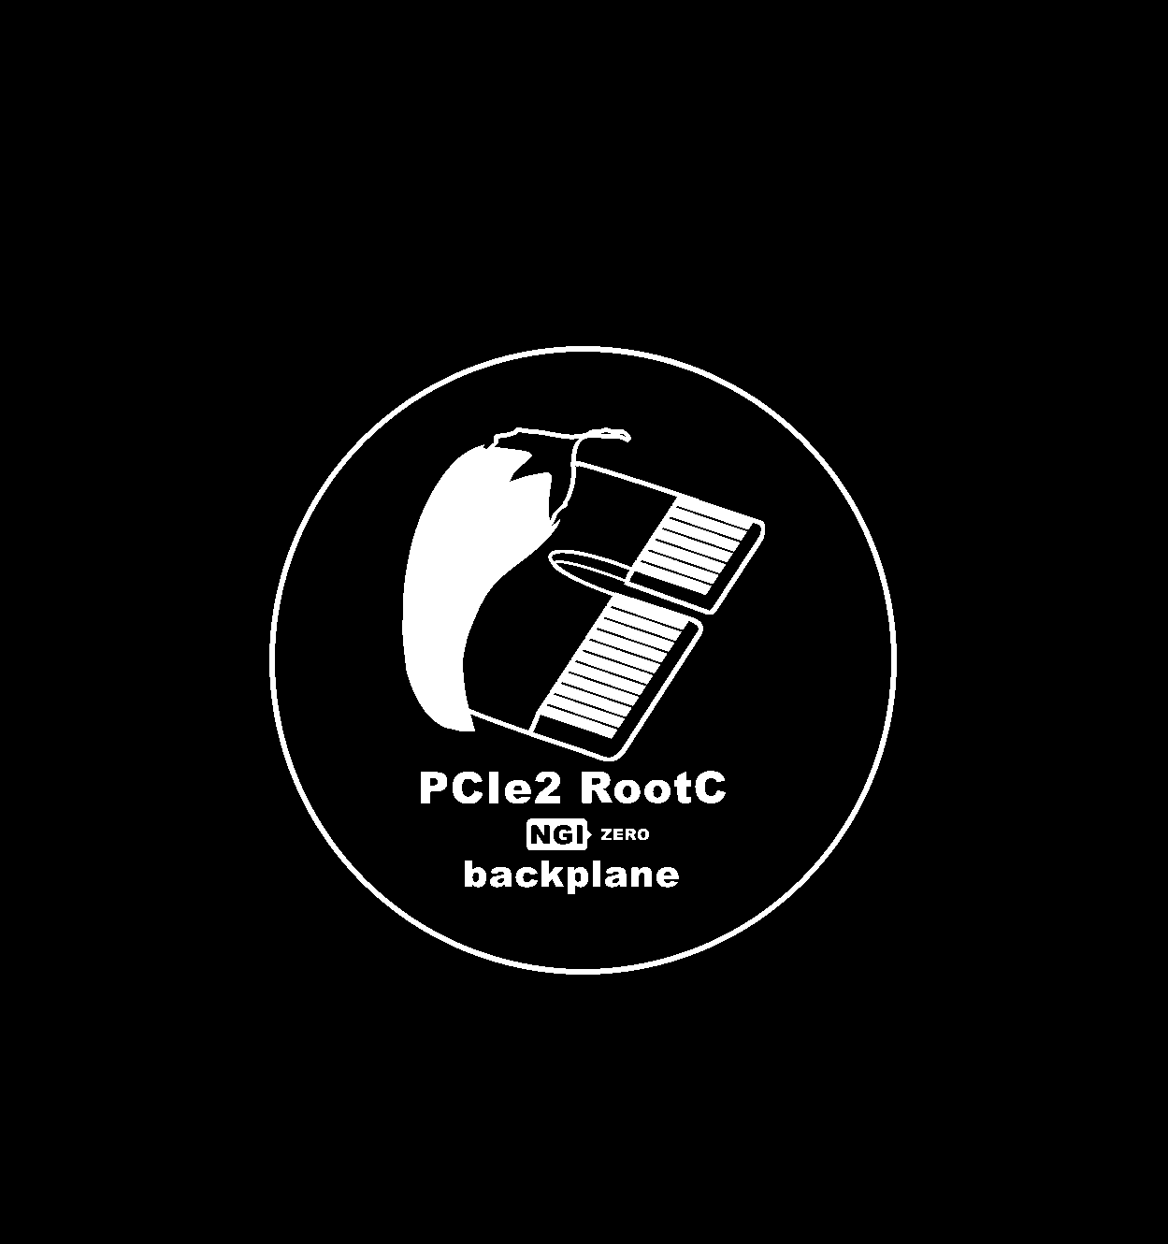
0.doc/artwork/pcie2rootc.BW.png
