chili-chips-ba/openPCIE/0.doc/artwork/pcie2rootc.hex.2.png

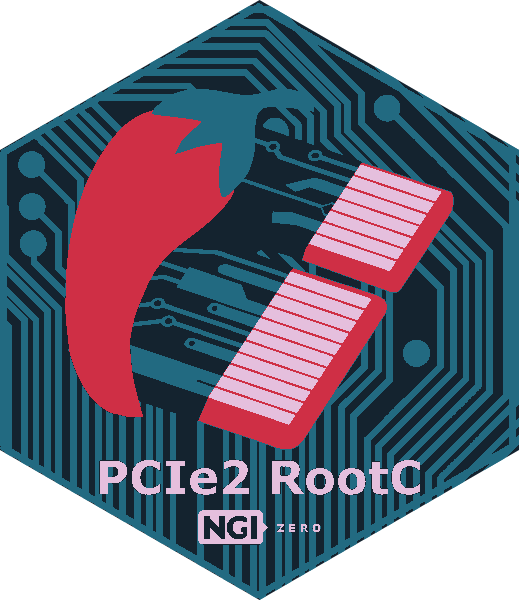
0.doc/artwork/pcie2rootc.hex.2.png
