chili-chips-ba/openPCIE/0.doc/artwork/pcie-edge-connector.png

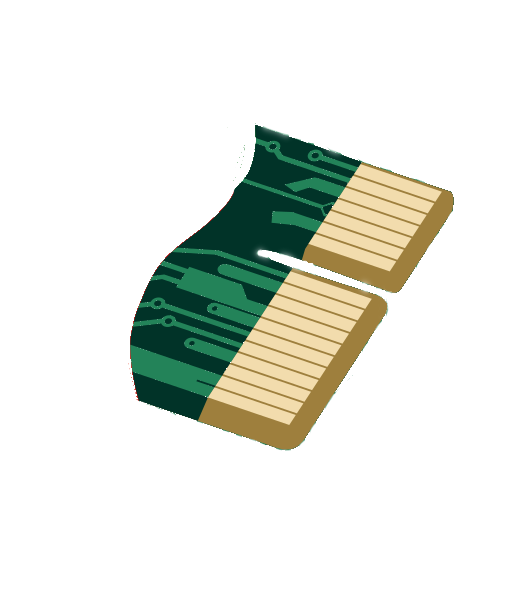
0.doc/artwork/pcie-edge-connector.png
