chili-chips-ba/openPCIE/0.doc/pictures/Physical Address fc500000 Assigned to PCIe Device.png

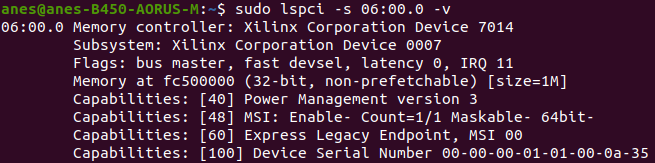
0.doc/pictures/Physical Address fc500000 Assigned to PCIe Device.png
