chili-chips-ba/openPCIE/1.pcb/0.doc/images/2.Conn--No-restrictions.jpg

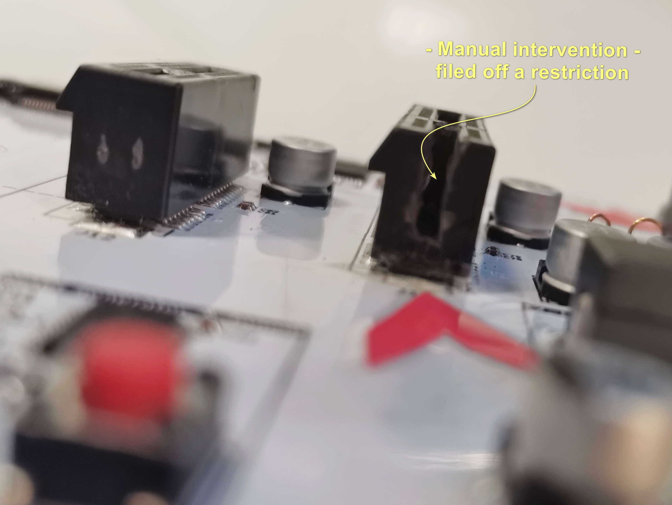
1.pcb/0.doc/images/2.Conn--No-restrictions.jpg
