chili-chips-ba/openPCIE/1.pcb/0.doc/images/ASM1184e-1-current-without-clock.jpg

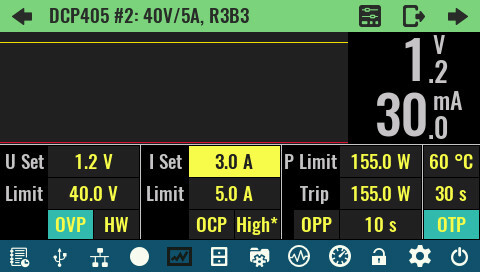
1.pcb/0.doc/images/ASM1184e-1-current-without-clock.jpg
