chili-chips-ba/openPCIE/1.pcb/0.doc/images/ASM1184e-3-temp-with-external-1V2.PNG

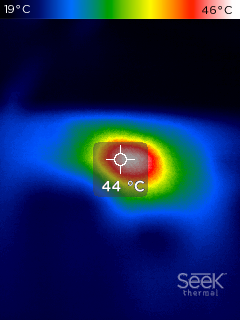
1.pcb/0.doc/images/ASM1184e-3-temp-with-external-1V2.PNG
