chili-chips-ba/openPCIE/1.pcb/0.doc/images/ASM1184e-4--Lifted-LDO-leg.jpg

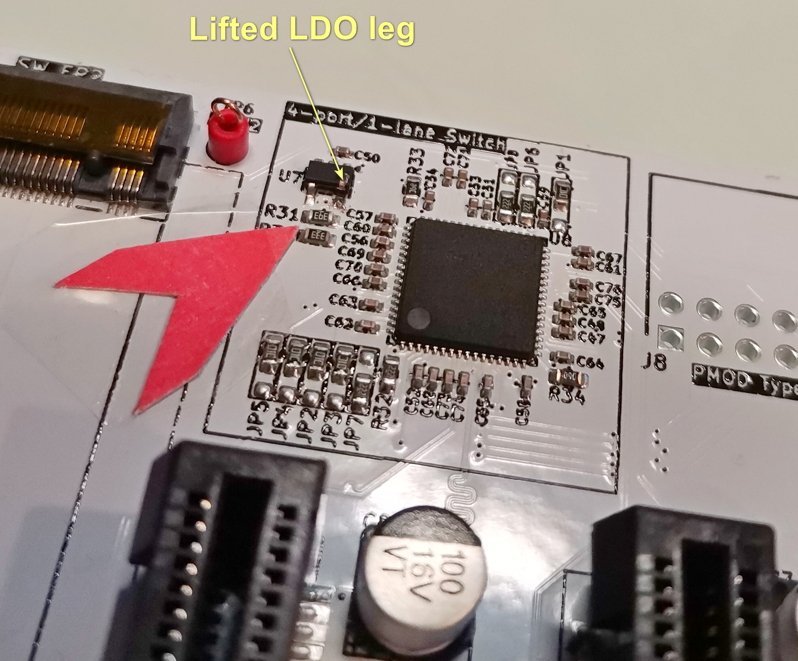
1.pcb/0.doc/images/ASM1184e-4--Lifted-LDO-leg.jpg
