chili-chips-ba/openPCIE/1.pcb/0.doc/images/ASM1184e-5--New-1V2-supply.jpg

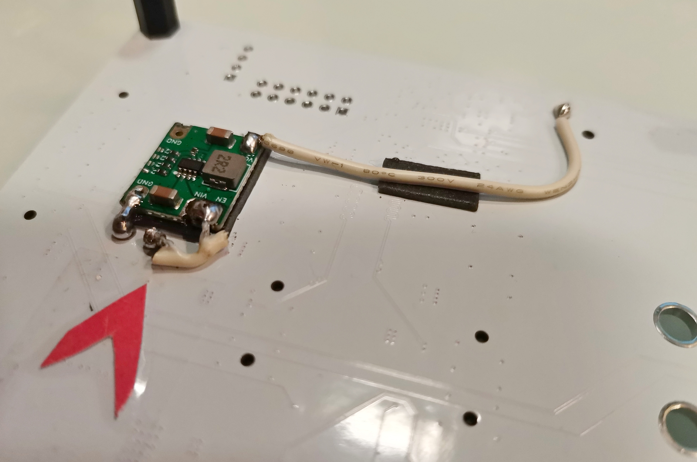
1.pcb/0.doc/images/ASM1184e-5--New-1V2-supply.jpg
