chili-chips-ba/openPCIE/1.pcb/0.doc/images/ASM1184e-bad-breakout.png

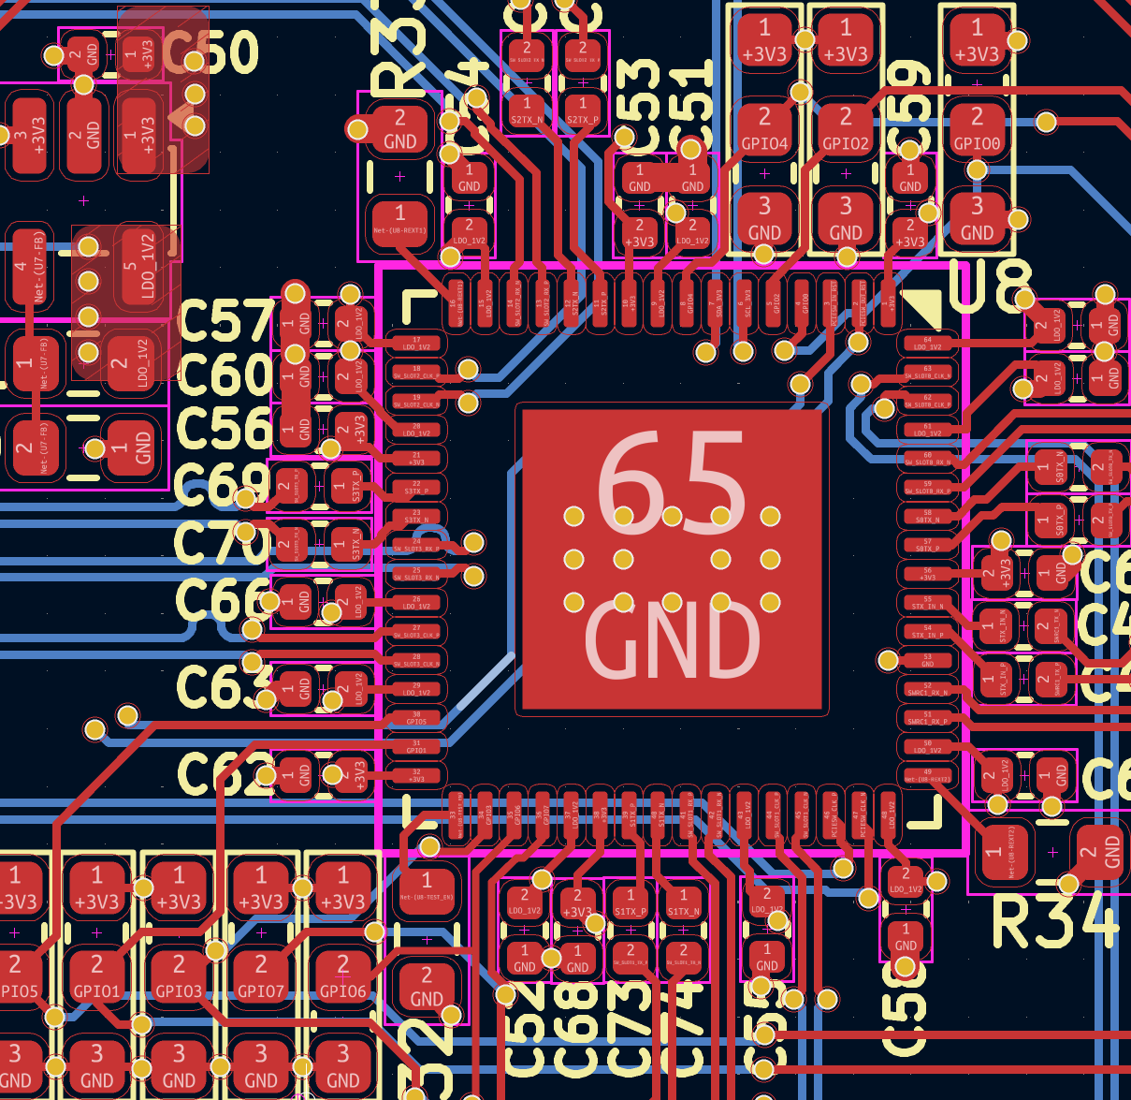
1.pcb/0.doc/images/ASM1184e-bad-breakout.png
