chili-chips-ba/openPCIE/1.pcb/0.doc/images/ASM1184e-chip.JPG

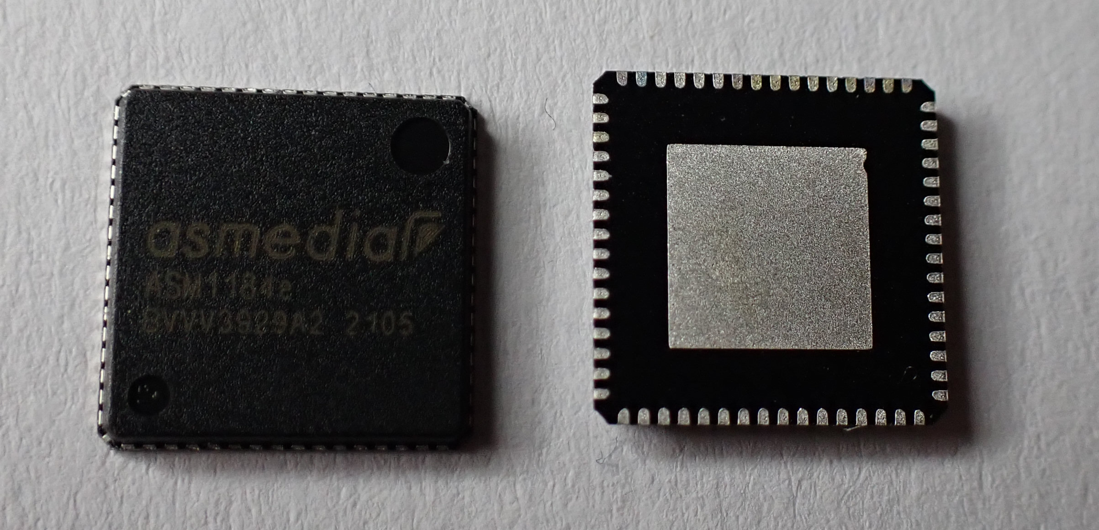
1.pcb/0.doc/images/ASM1184e-chip.JPG
