chili-chips-ba/openPCIE/1.pcb/0.doc/images/ASM1184e-good-breakout.png

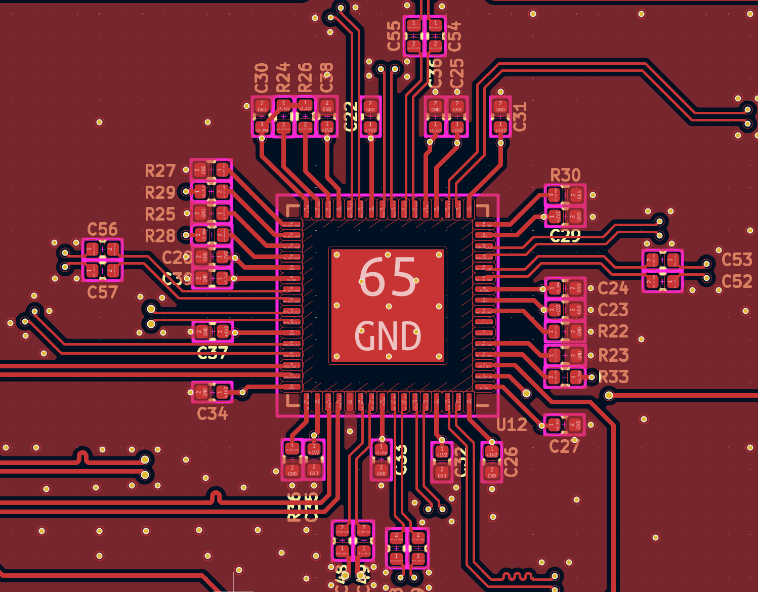
1.pcb/0.doc/images/ASM1184e-good-breakout.png
