chili-chips-ba/openPCIE/1.pcb/0.doc/images/ASM1184e-heat-sink-is-not-enough.jpg

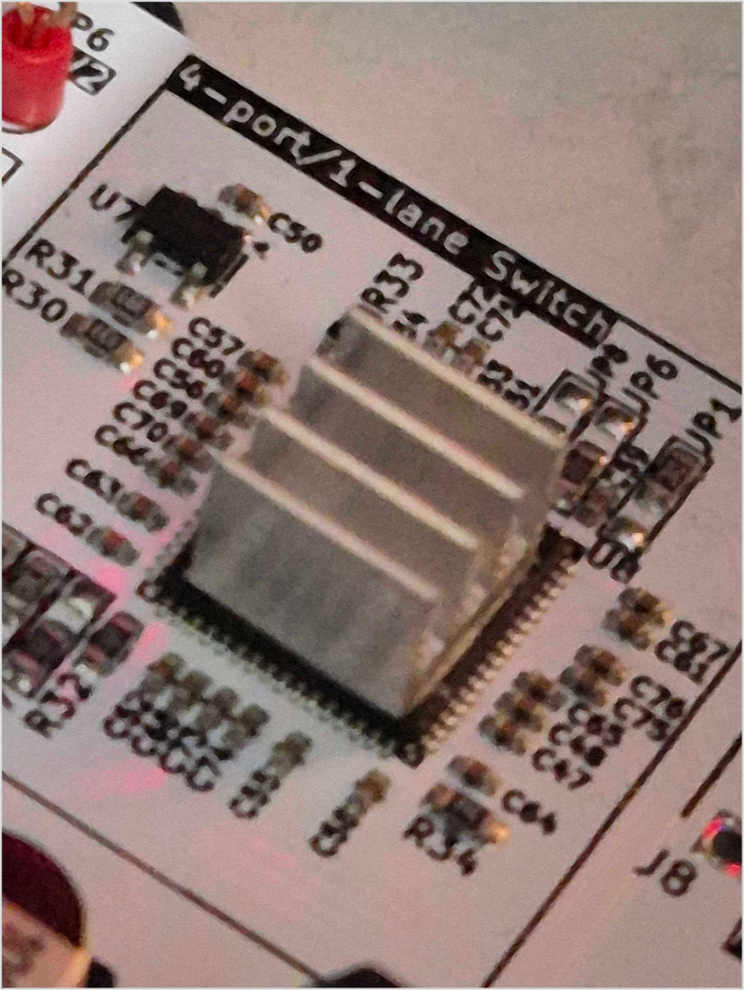
1.pcb/0.doc/images/ASM1184e-heat-sink-is-not-enough.jpg
