chili-chips-ba/openPCIE/1.pcb/0.doc/images/ASM1184e-temp-1-without-clock.PNG

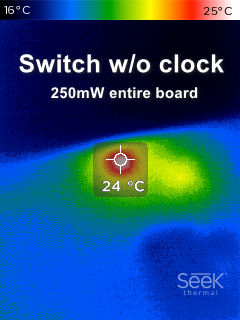
1.pcb/0.doc/images/ASM1184e-temp-1-without-clock.PNG
