chili-chips-ba/openPCIE/1.pcb/0.doc/images/ASM1184e-temp-2-with-clock.1st-round.PNG

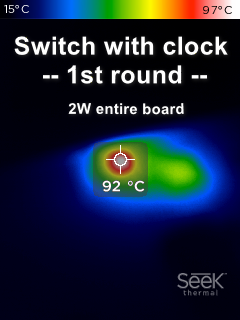
1.pcb/0.doc/images/ASM1184e-temp-2-with-clock.1st-round.PNG
