chili-chips-ba/openPCIE/1.pcb/0.doc/images/ASM1184e-temp-3-with-clock.2nd-round.PNG

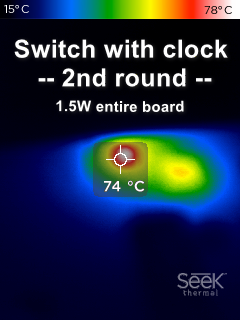
1.pcb/0.doc/images/ASM1184e-temp-3-with-clock.2nd-round.PNG
