chili-chips-ba/openPCIE/1.pcb/0.doc/images/ASM1184e-temp-4-LDO-is-hotter.PNG

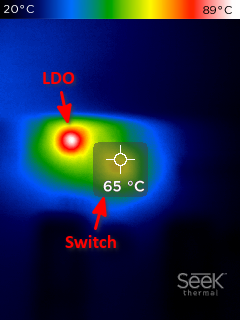
1.pcb/0.doc/images/ASM1184e-temp-4-LDO-is-hotter.PNG
