chili-chips-ba/openPCIE/1.pcb/0.doc/images/CM4-IO-with-PCIE-M2.jpg

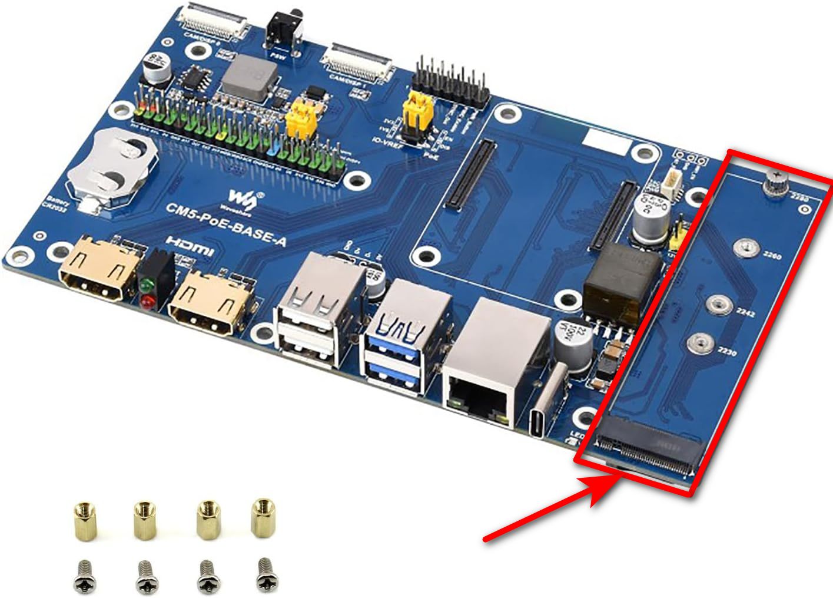
1.pcb/0.doc/images/CM4-IO-with-PCIE-M2.jpg
