chili-chips-ba/openPCIE/1.pcb/0.doc/images/Conn-open-end-PCIE-Slot.png

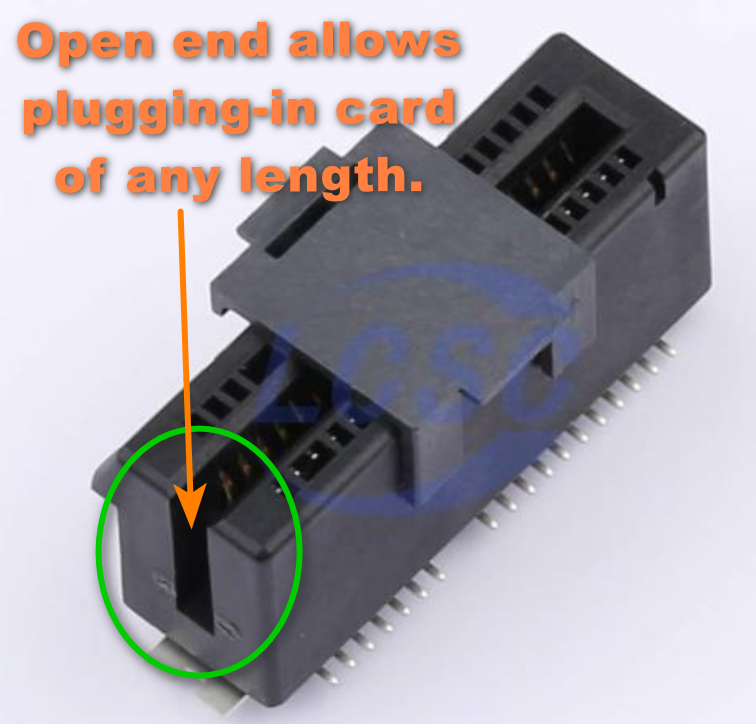
1.pcb/0.doc/images/Conn-open-end-PCIE-Slot.png
