chili-chips-ba/openPCIE/1.pcb/0.doc/images/incident-and-reflected-wave-ems.png

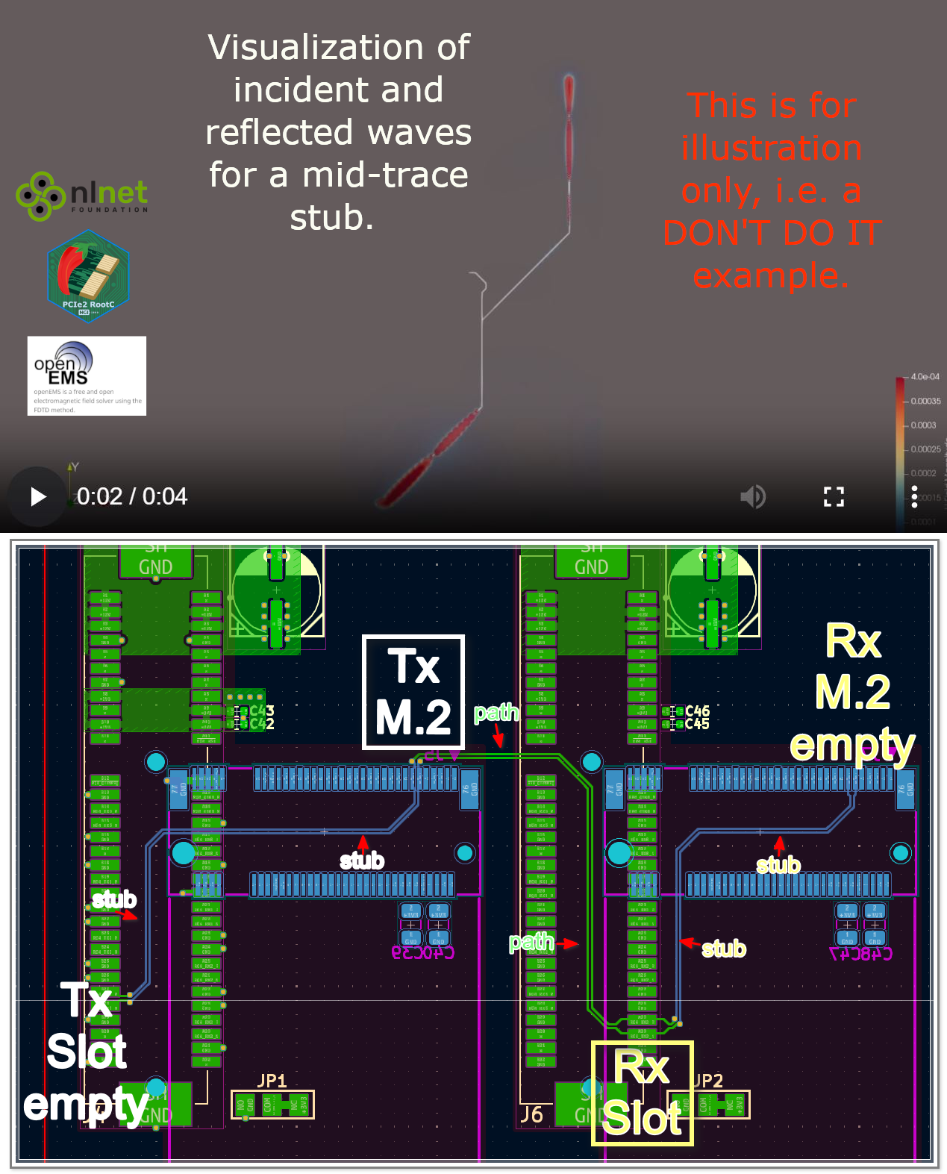
1.pcb/0.doc/images/incident-and-reflected-wave-ems.png
