chili-chips-ba/openPCIE/1.pcb/0.doc/images/Mini360-BuckModule.jpg

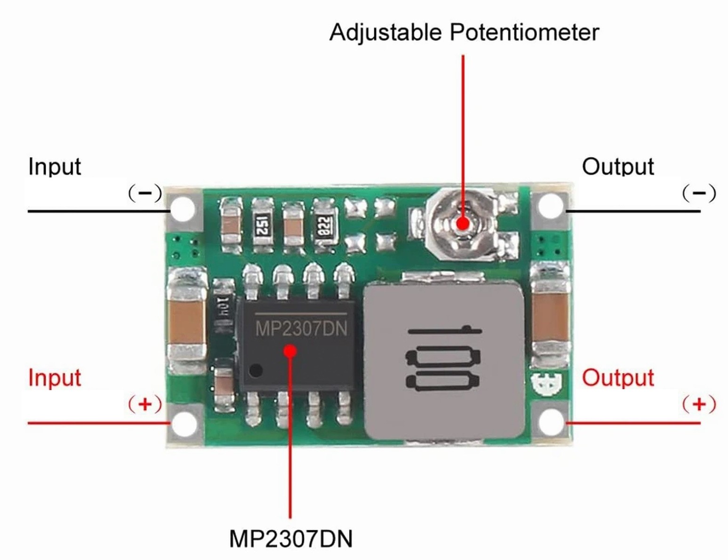
1.pcb/0.doc/images/Mini360-BuckModule.jpg
