chili-chips-ba/openPCIE/1.pcb/0.doc/images/OCuLink.1.JPG

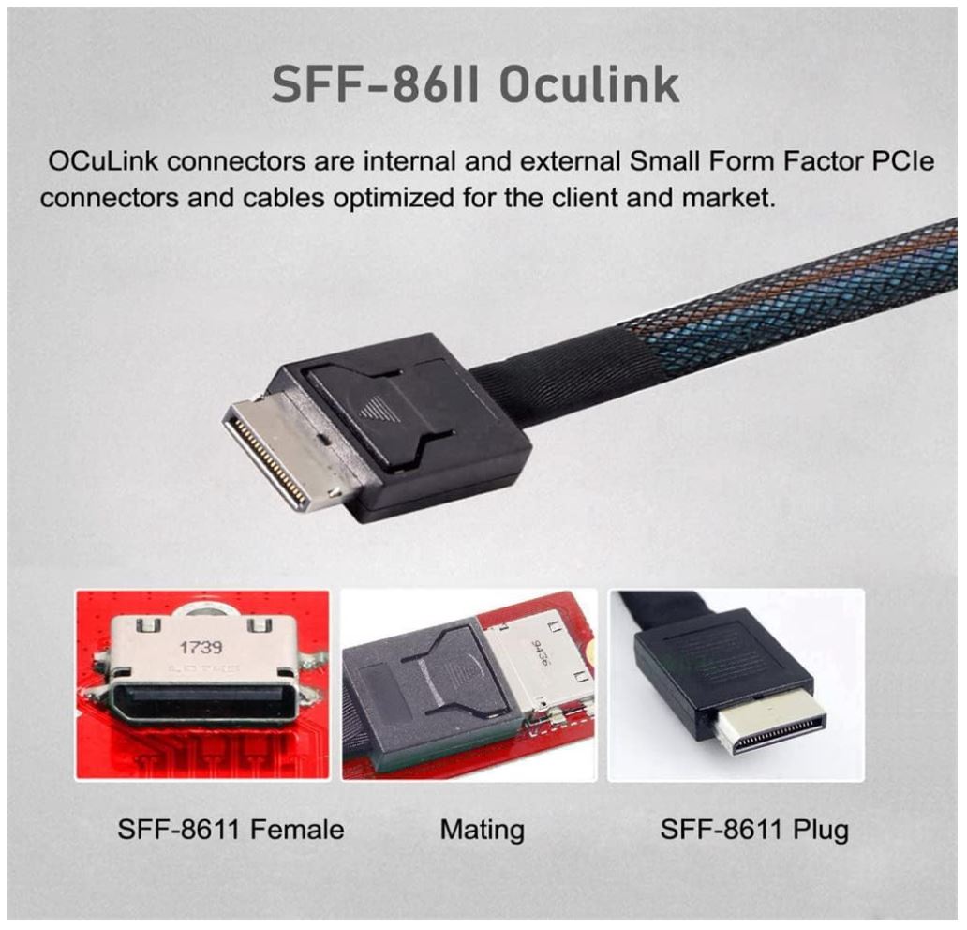
1.pcb/0.doc/images/OCuLink.1.JPG
