chili-chips-ba/openPCIE/1.pcb/0.doc/images/Proto.2026-01-07.1.jpg

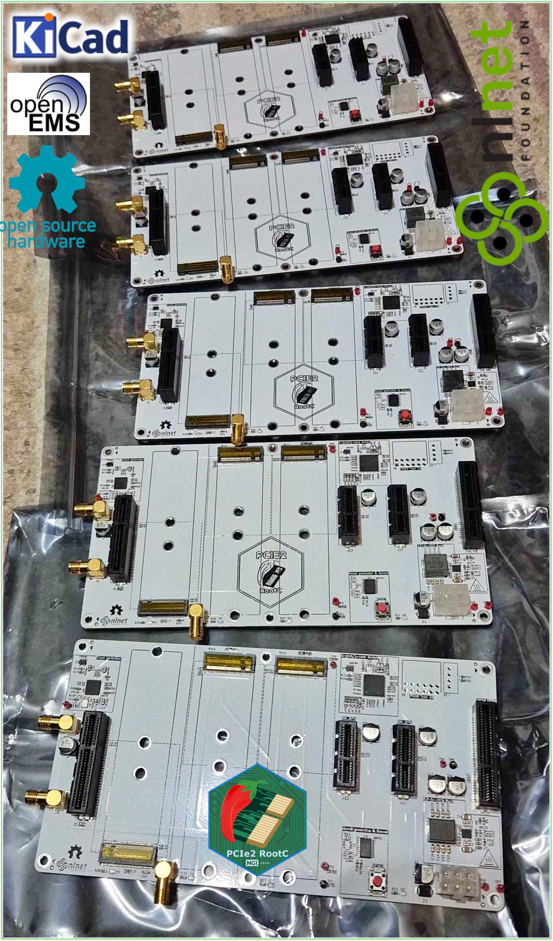
1.pcb/0.doc/images/Proto.2026-01-07.1.jpg
