chili-chips-ba/openPCIE/1.pcb/0.doc/images/Proto.2026-01-07.2.png

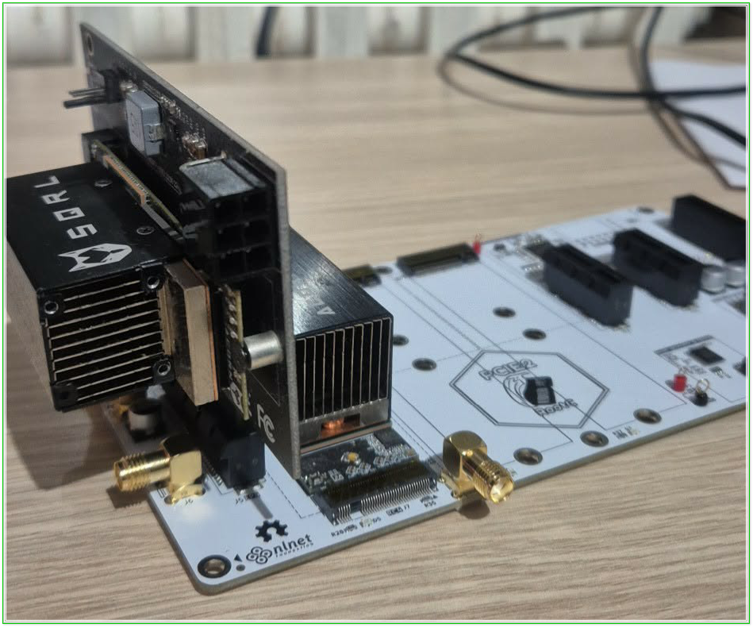
1.pcb/0.doc/images/Proto.2026-01-07.2.png
