chili-chips-ba/openPCIE/1.pcb/0.doc/images/Proto.2026-01-12.DirecTalk.jpg

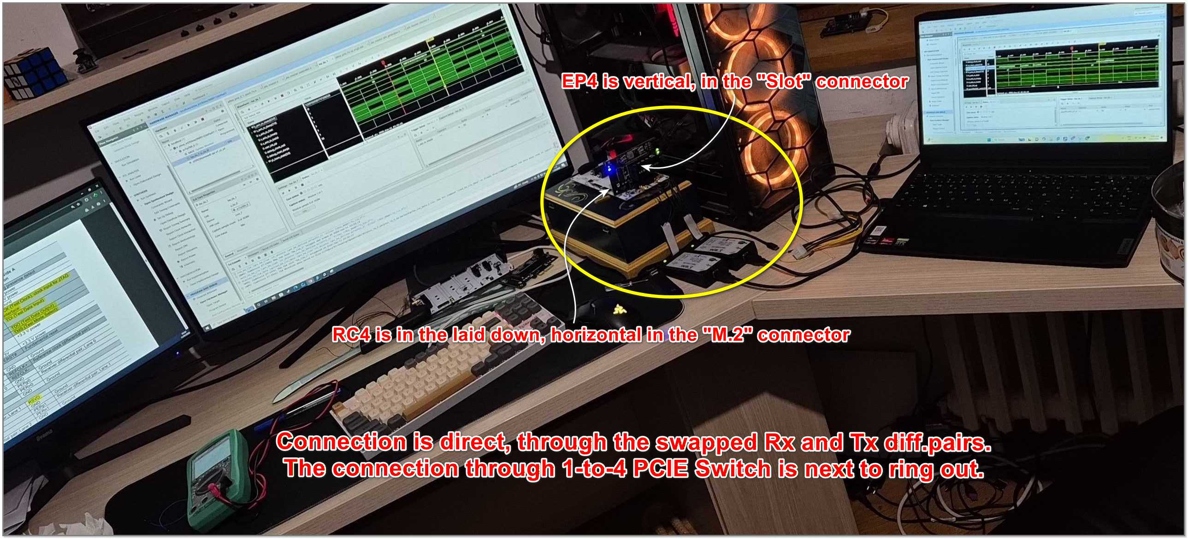
1.pcb/0.doc/images/Proto.2026-01-12.DirecTalk.jpg
