chili-chips-ba/openPCIE/1.pcb/0.doc/images/RPI5-PCIE.JPG

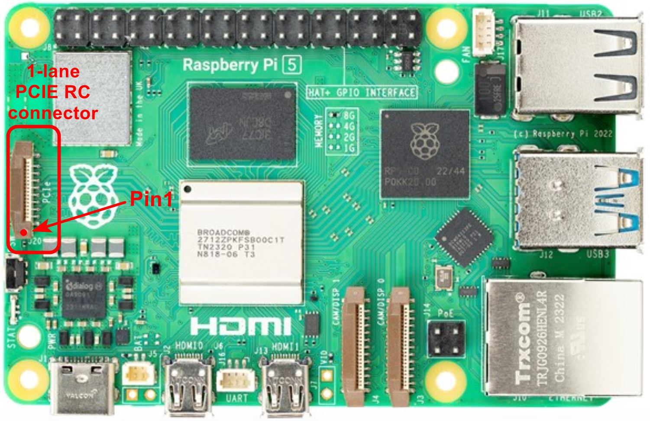
1.pcb/0.doc/images/RPI5-PCIE.JPG
