chili-chips-ba/openPCIE/1.pcb/0.doc/openPCIE3-backplane.DiodesInc.png

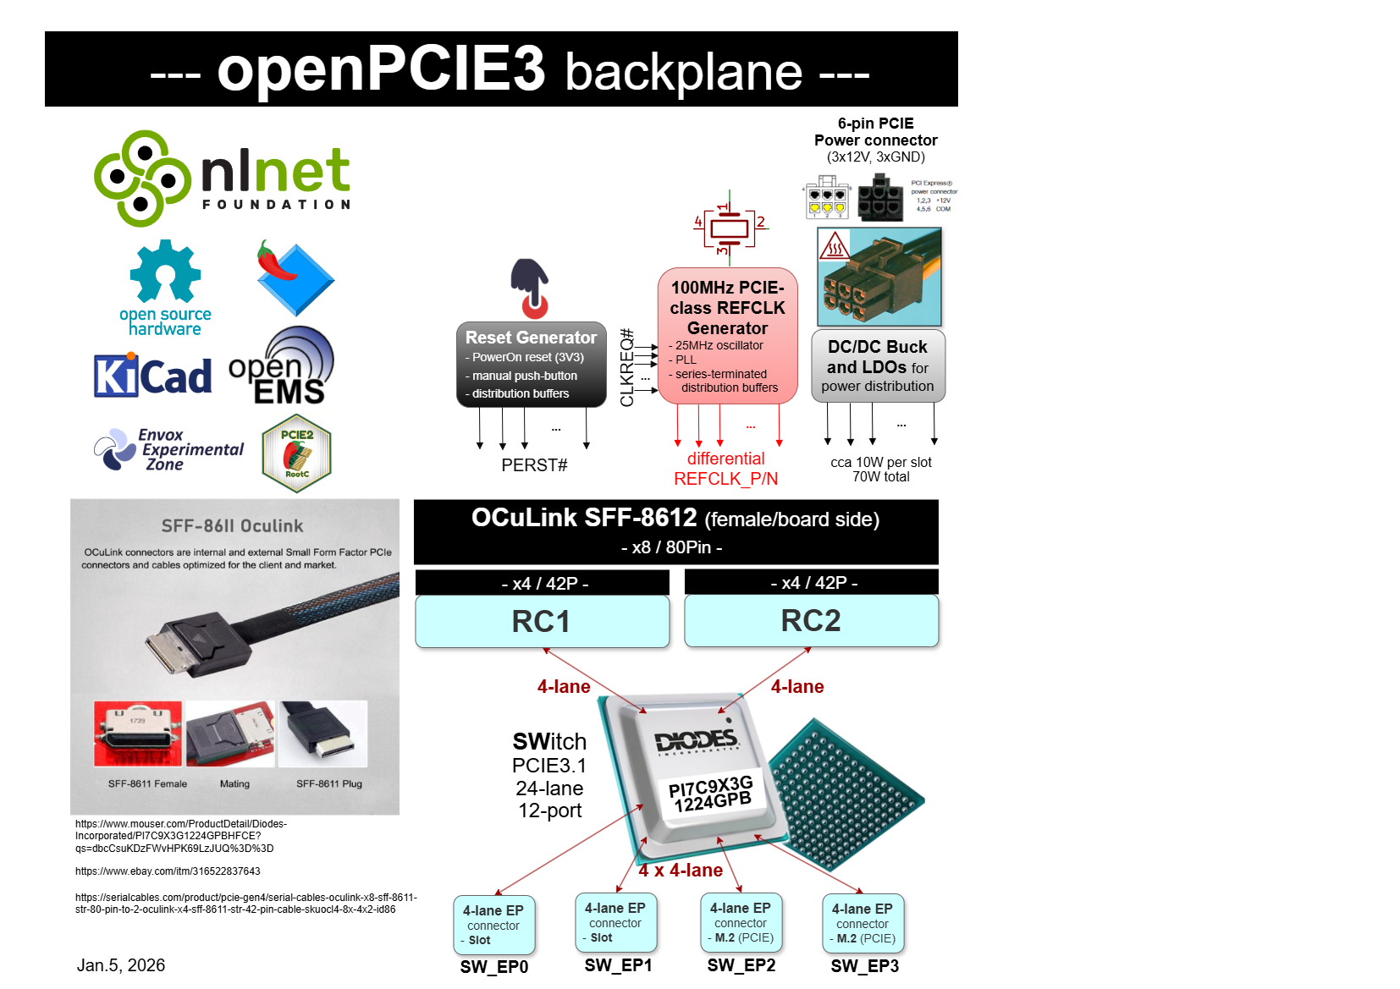
1.pcb/0.doc/openPCIE3-backplane.DiodesInc.png
