chili-chips-ba/openPCIE/1.pcb/KiCad-library/chili-chips-lib/3dmodels/WLCSP9_1P2X1P2_ONS.step

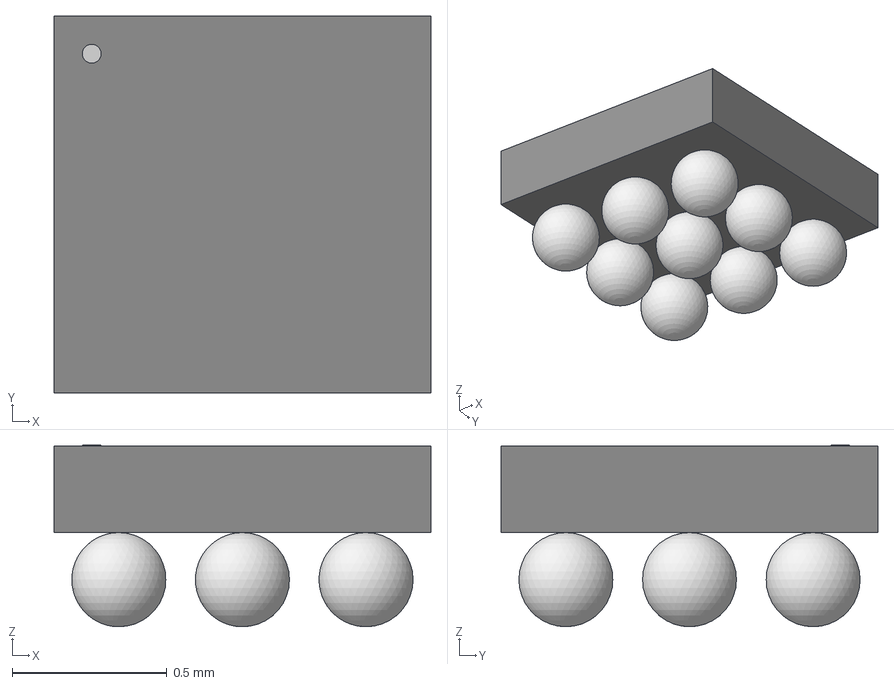
[picture p147: CAD file, 2026-09-09]
1.pcb/KiCad-library/chili-chips-lib/3dmodels/WLCSP9_1P2X1P2_ONS.step
1.22 x 1.22 x 0.587 mm
