chili-chips-ba/openPCIE/1.pcb/KiCad-library/EEZ-Kicad-libraries/3dmodels/FUSE_20x5mm.step

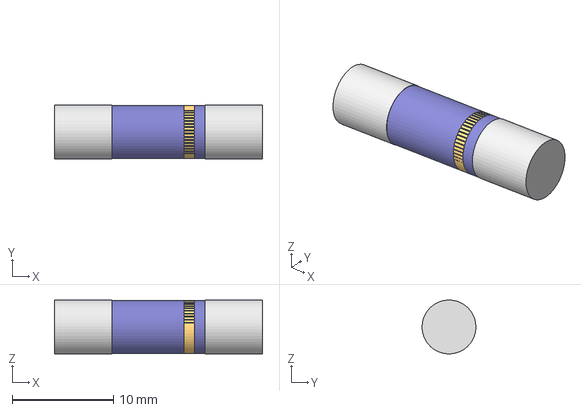
[picture p148: CAD file, 2026-10-06]
1.pcb/KiCad-library/EEZ-Kicad-libraries/3dmodels/FUSE_20x5mm.step
20.5 x 5.31 x 5.30 mm
