chili-chips-ba/openPCIE/1.pcb/KiCad-library/chili-chips-lib/3dmodels/SOD882_NEX.step

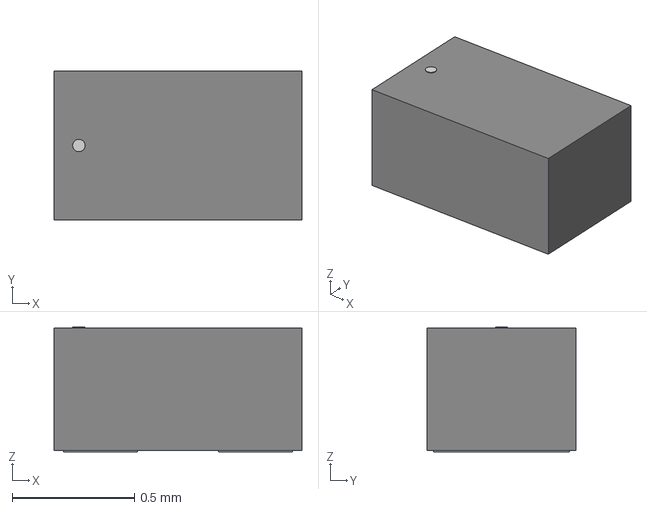
[picture p149: CAD file, 2026-09-09]
1.pcb/KiCad-library/chili-chips-lib/3dmodels/SOD882_NEX.step
1.02 x 0.61 x 0.511 mm
