chili-chips-ba/openPCIE/1.pcb/KiCad-library/EEZ-Kicad-libraries/3dmodels/PW0024A.stp

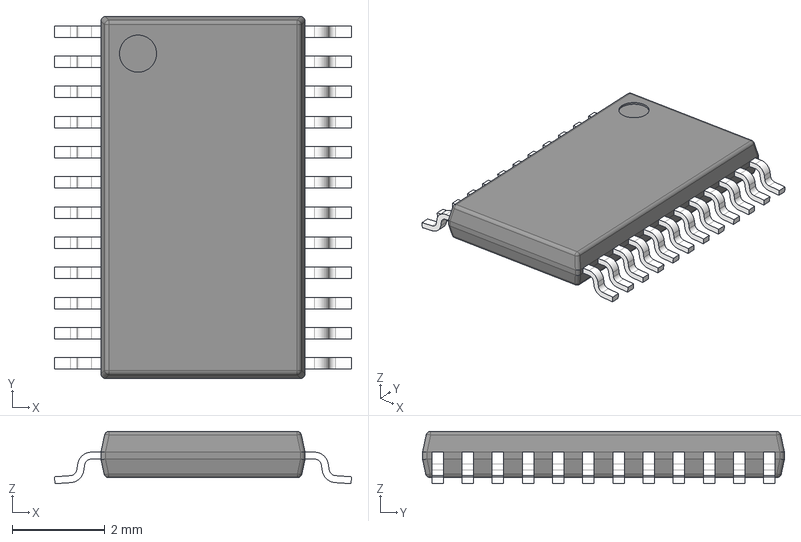
[picture p150: CAD file, 2026-10-06]
1.pcb/KiCad-library/EEZ-Kicad-libraries/3dmodels/PW0024A.stp
6.40 x 7.80 x 1.13 mm
BODY-TSSOP
LEAD-TSSOP x 24
PIN1
