chili-chips-ba/openPCIE/1.pcb/KiCad-library/chili-chips-lib/3dmodels/MPL-AL5030-1R5.stp

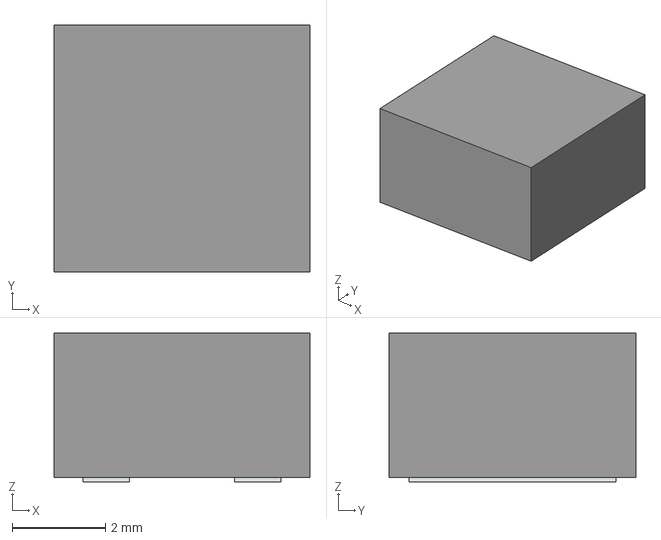
[picture p151: CAD file, 2026-09-09]
1.pcb/KiCad-library/chili-chips-lib/3dmodels/MPL-AL5030-1R5.stp
5.50 x 5.30 x 3.20 mm
Pins
