chili-chips-ba/openPCIE/1.pcb/KiCad-library/chili-chips-lib/3dmodels/USON-8L_3X2_APY.step

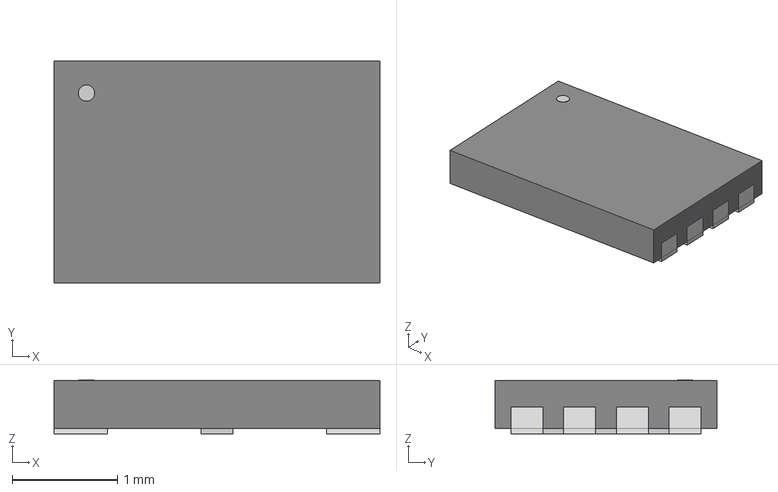
[picture p152: CAD file, 2026-09-09]
1.pcb/KiCad-library/chili-chips-lib/3dmodels/USON-8L_3X2_APY.step
3.10 x 2.11 x 0.511 mm
