chili-chips-ba/openPCIE/1.pcb/KiCad-library/EEZ-Kicad-libraries/3dmodels/SOIC127P600X265-16N.step

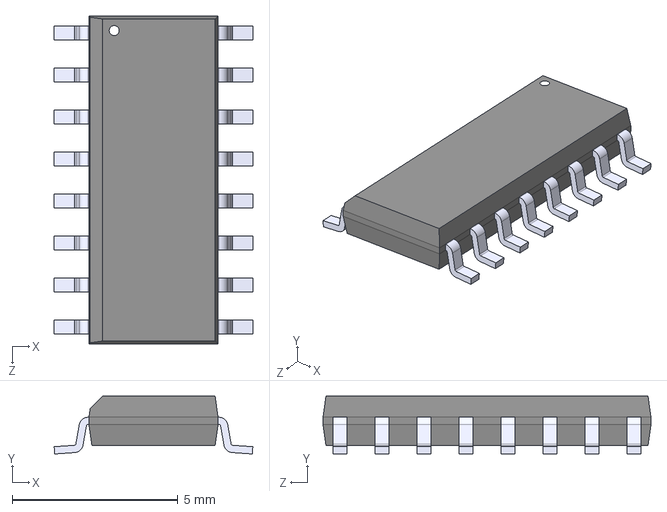
[picture p153: CAD file, 2026-10-06]
1.pcb/KiCad-library/EEZ-Kicad-libraries/3dmodels/SOIC127P600X265-16N.step
6.00 x 1.75 x 9.90 mm
