chili-chips-ba/openPCIE/1.pcb/KiCad-library/chili-chips-lib/3dmodels/DRL0006A.stp

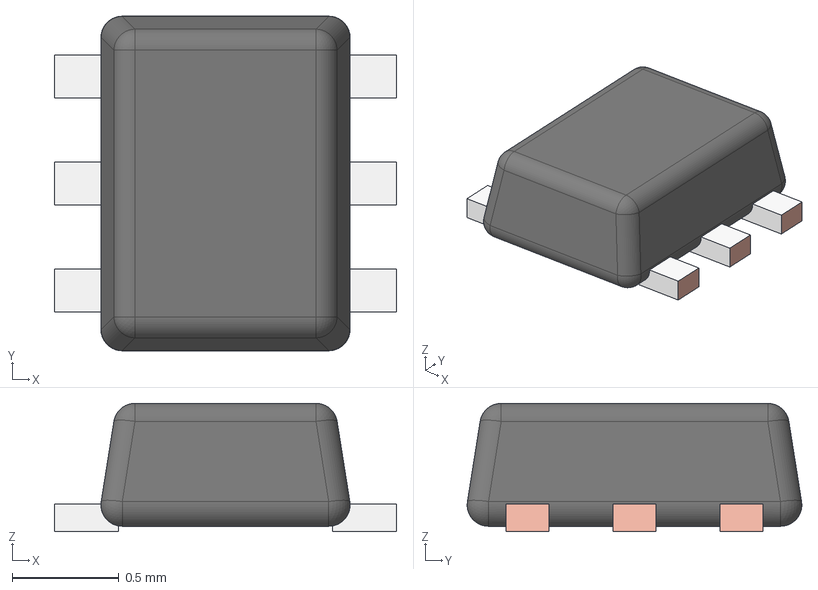
[picture p154: CAD file, 2026-09-09]
1.pcb/KiCad-library/chili-chips-lib/3dmodels/DRL0006A.stp
1.60 x 1.57 x 0.6 mm
FRAME-DRL0006A
BODY-SOT
PIN1-ID
