chili-chips-ba/openPCIE/1.pcb/KiCad-library/EEZ-Kicad-libraries/3dmodels/SOD-323_1P8X1P35_ONS.step

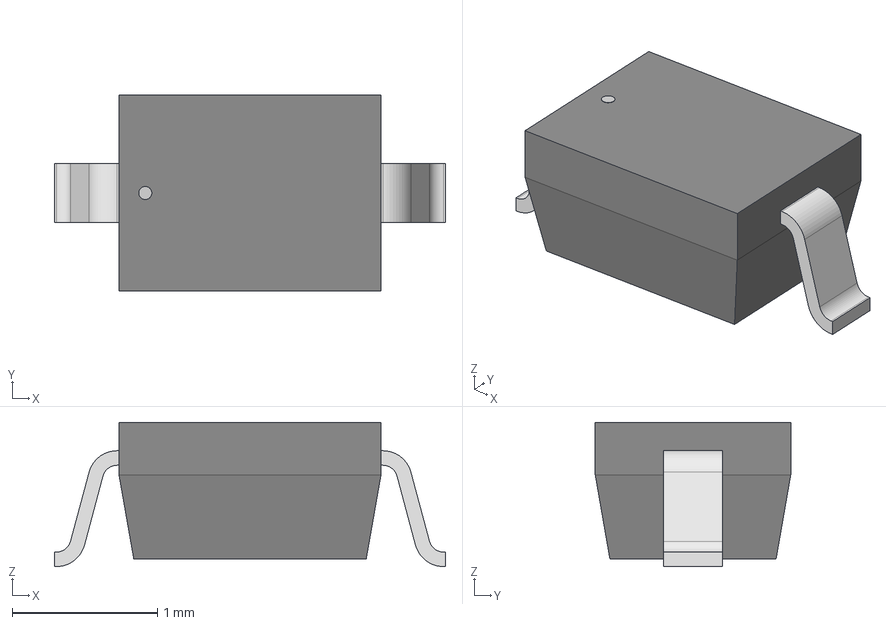
[picture p155: CAD file, 2026-10-06]
1.pcb/KiCad-library/EEZ-Kicad-libraries/3dmodels/SOD-323_1P8X1P35_ONS.step
2.69 x 1.35 x 0.993 mm
