chili-chips-ba/openPCIE/1.pcb/KiCad-library/chili-chips-lib/3dmodels/SP0201B-ULC-01UTG.stp

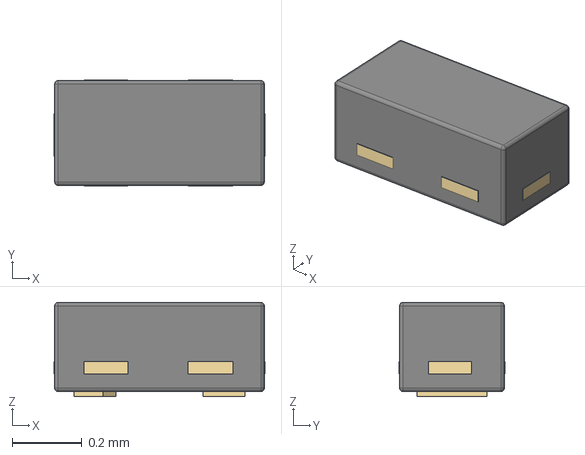
[picture p156: CAD file, 2026-09-09]
1.pcb/KiCad-library/chili-chips-lib/3dmodels/SP0201B-ULC-01UTG.stp
0.604 x 0.303 x 0.27 mm
