chili-chips-ba/openPCIE/1.pcb/KiCad-library/chili-chips-lib/3dmodels/TS3USB30ERSWR.step

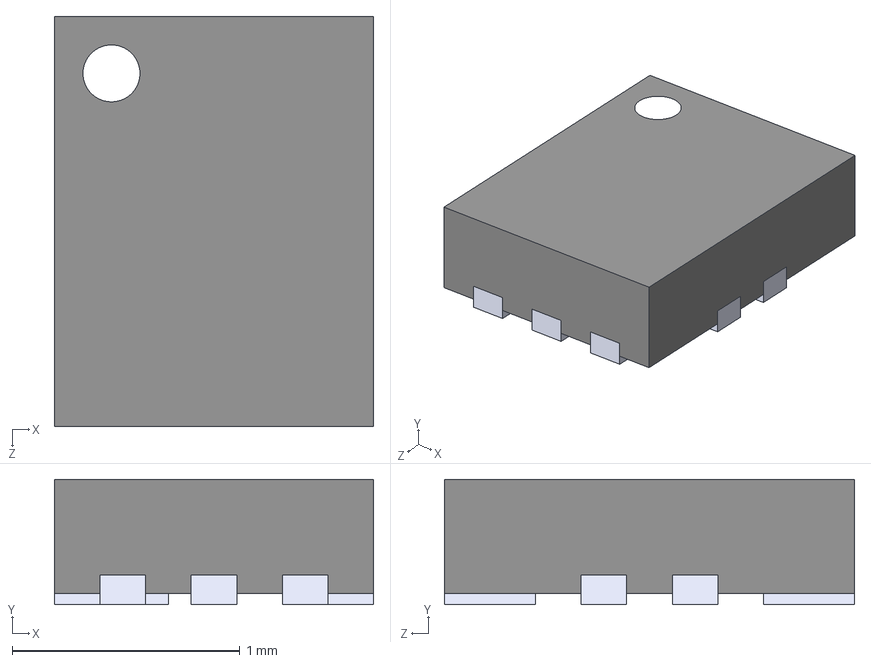
[picture p157: CAD file, 2026-09-09]
1.pcb/KiCad-library/chili-chips-lib/3dmodels/TS3USB30ERSWR.step
1.40 x 0.55 x 1.80 mm
