chili-chips-ba/openPCIE/1.pcb/KiCad-library/EEZ-Kicad-libraries/3dmodels/RUK0020B.stp

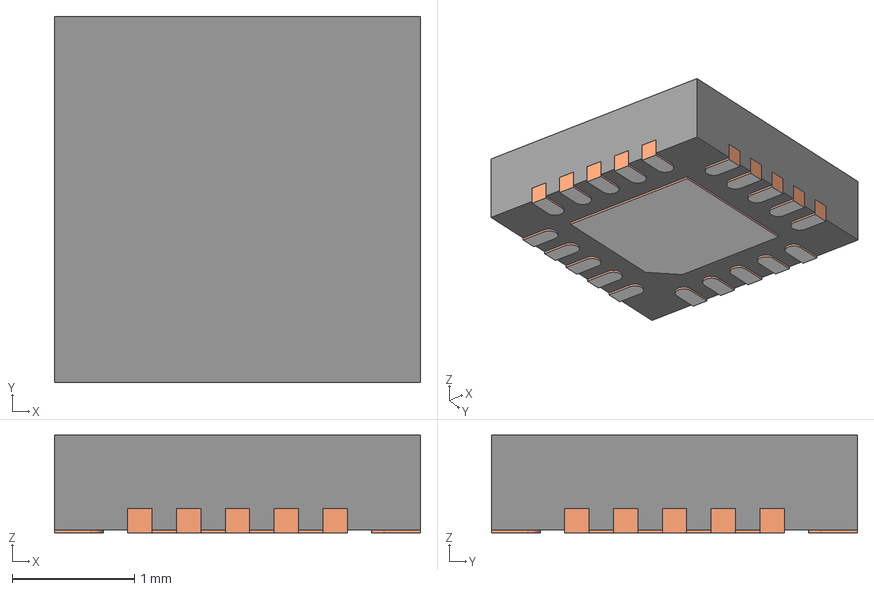
[picture p158: CAD file, 2026-10-06]
1.pcb/KiCad-library/EEZ-Kicad-libraries/3dmodels/RUK0020B.stp
3.00 x 3.00 x 0.8 mm
BODY-QFN
FRAME-RUK0020B
PIN1-ID
