chili-chips-ba/openPCIE/1.pcb/KiCad-library/chili-chips-lib/3dmodels/ECAP8X12_5.stp

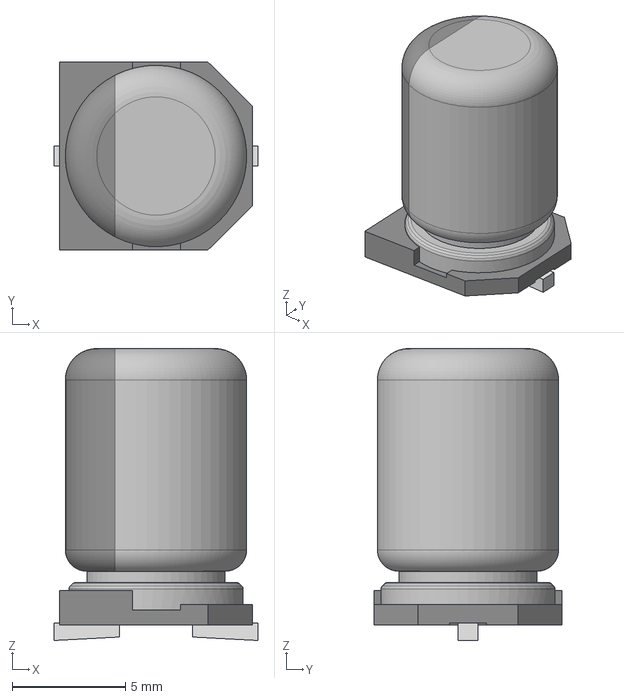
[picture p159: CAD file, 2026-09-09]
1.pcb/KiCad-library/chili-chips-lib/3dmodels/ECAP8X12_5.stp
9.00 x 8.30 x 12.9 mm
