chili-chips-ba/openPCIE/1.pcb/KiCad-library/chili-chips-lib/3dmodels/HUQFN16_2_4x1_6x0_5_NXP.step

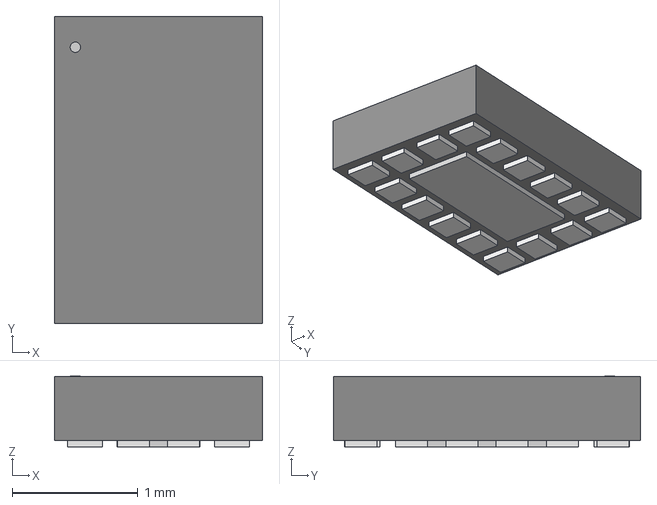
[picture p160: CAD file, 2026-09-09]
1.pcb/KiCad-library/chili-chips-lib/3dmodels/HUQFN16_2_4x1_6x0_5_NXP.step
1.65 x 2.44 x 0.561 mm
