chili-chips-ba/openPCIE/1.pcb/KiCad-library/EEZ-Kicad-libraries/3dmodels/USB1135-15-9-L-B.stp

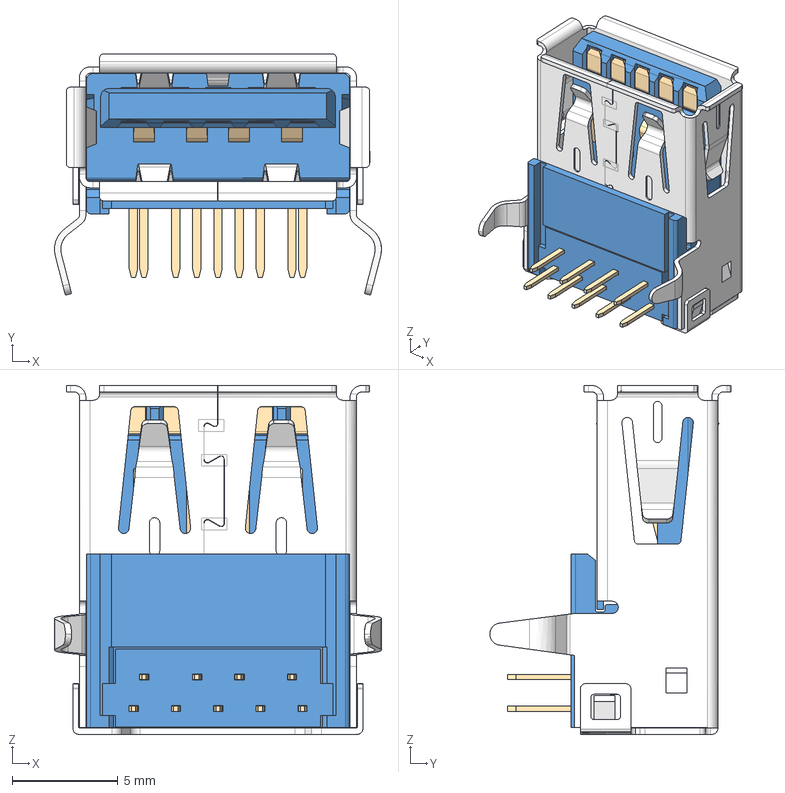
[picture p161: CAD file, 2026-10-06]
1.pcb/KiCad-library/EEZ-Kicad-libraries/3dmodels/USB1135-15-9-L-B.stp
15.5 x 11.4 x 16.5 mm
USB1135-15-9-L-B_PART5
USB1135-15-9-L-B_PART4
USB1135-15-9-L-B_PART3
USB1135-15-9-L-B_PART2
USB1135-15-9-L-B_PART1
