chili-chips-ba/openPCIE/1.pcb/KiCad-library/chili-chips-lib/3dmodels/RQY0009A.stp

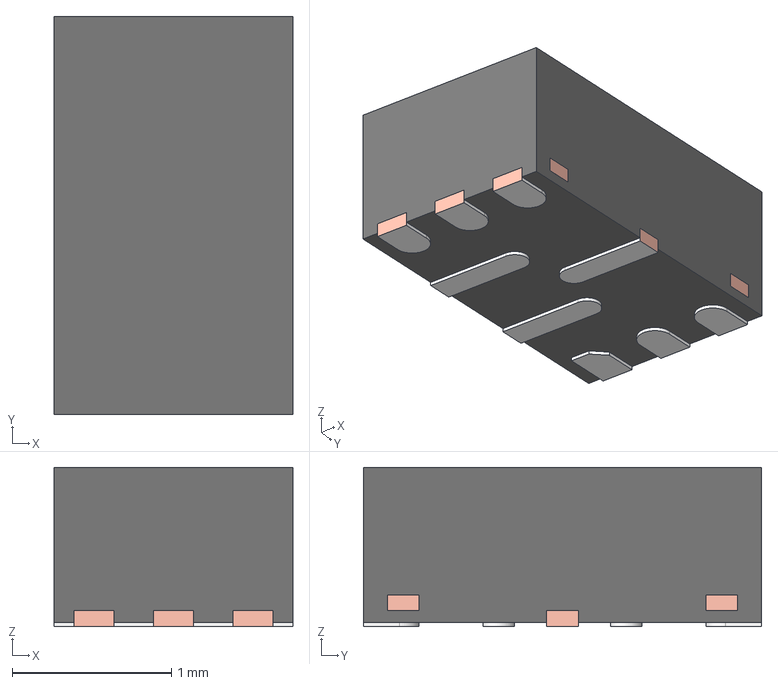
[picture p162: CAD file, 2026-09-09]
1.pcb/KiCad-library/chili-chips-lib/3dmodels/RQY0009A.stp
1.50 x 2.50 x 1.00 mm
FRAME
MOLD
