chili-chips-ba/openPCIE/1.pcb/KiCad-library/EEZ-Kicad-libraries/3dmodels/SOT23-5L_STM.step

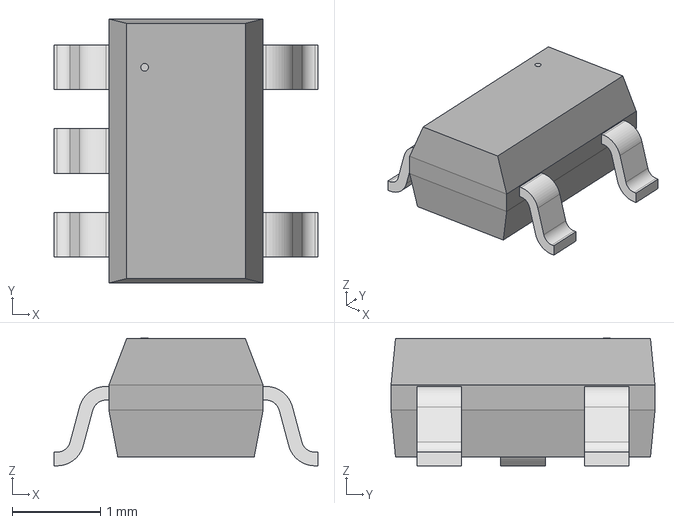
[picture p163: CAD file, 2026-10-06]
1.pcb/KiCad-library/EEZ-Kicad-libraries/3dmodels/SOT23-5L_STM.step
3.00 x 3.00 x 1.45 mm
