chili-chips-ba/openPCIE/1.pcb/KiCad-library/chili-chips-lib/3dmodels/DQE8.STEP

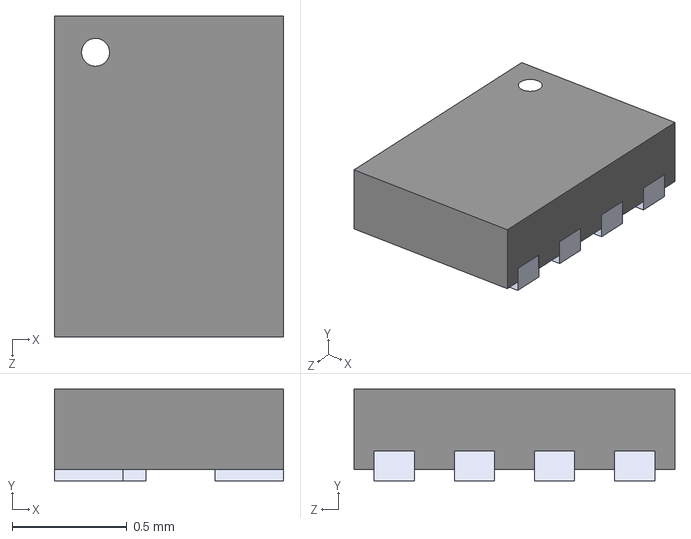
[picture p164: CAD file, 2026-09-09]
1.pcb/KiCad-library/chili-chips-lib/3dmodels/DQE8.STEP
1.00 x 0.4 x 1.40 mm
