chili-chips-ba/openPCIE/1.pcb/KiCad-library/EEZ-Kicad-libraries/3dmodels/L_0805_2012Metric.step

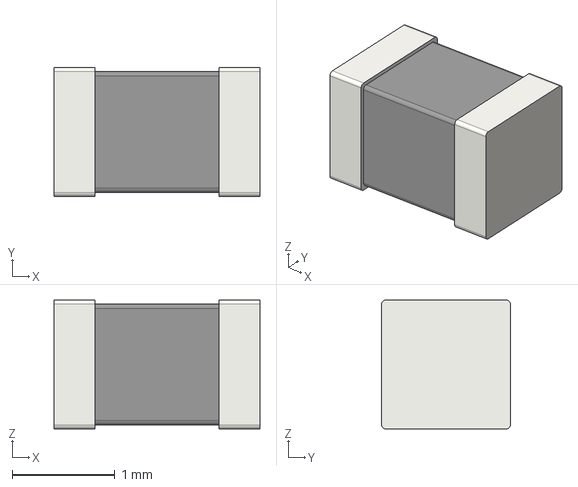
[picture p165: CAD file, 2026-10-06]
1.pcb/KiCad-library/EEZ-Kicad-libraries/3dmodels/L_0805_2012Metric.step
2.00 x 1.25 x 1.25 mm
