chili-chips-ba/openPCIE/1.pcb/KiCad-library/chili-chips-lib/3dmodels/LED_LM301Z_SAM.step

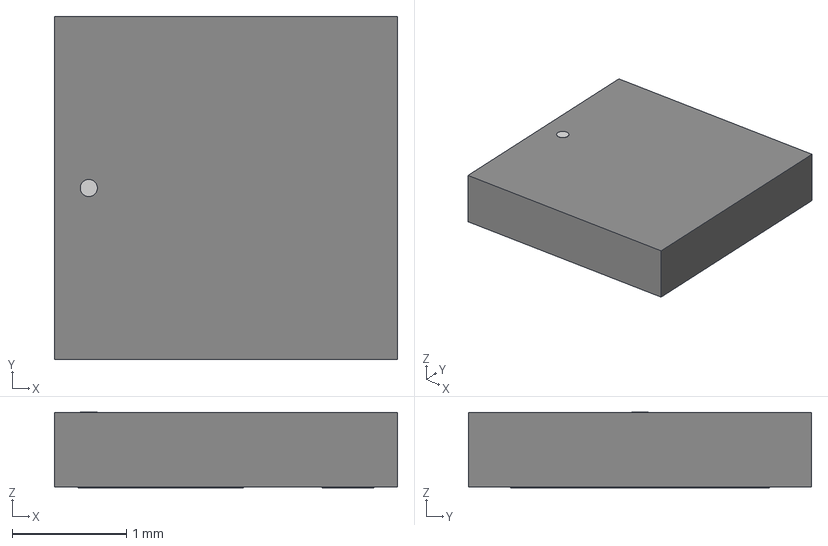
[picture p166: CAD file, 2026-09-09]
1.pcb/KiCad-library/chili-chips-lib/3dmodels/LED_LM301Z_SAM.step
3.00 x 3.00 x 0.663 mm
