chili-chips-ba/openPCIE/1.pcb/KiCad-library/EEZ-Kicad-libraries/3dmodels/SOP65P490X110-8N.step

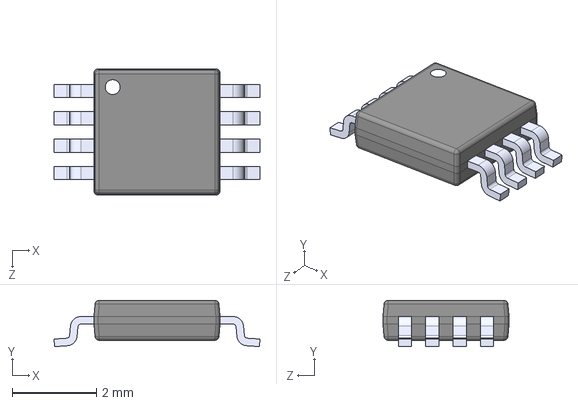
[picture p167: CAD file, 2026-10-06]
1.pcb/KiCad-library/EEZ-Kicad-libraries/3dmodels/SOP65P490X110-8N.step
4.90 x 1.10 x 3.00 mm
