chili-chips-ba/openPCIE/1.pcb/KiCad-library/chili-chips-lib/3dmodels/SOT-23-3.step

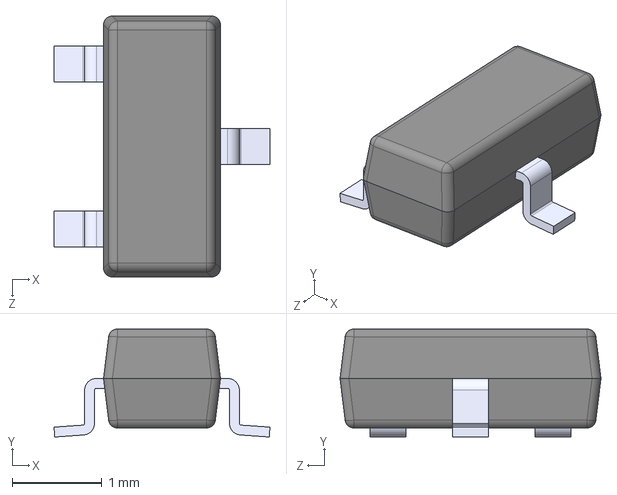
[picture p168: CAD file, 2026-09-09]
1.pcb/KiCad-library/chili-chips-lib/3dmodels/SOT-23-3.step
2.40 x 1.20 x 2.90 mm
