chili-chips-ba/openPCIE/1.pcb/KiCad-library/chili-chips-lib/3dmodels/ABM8G-30.000MHZ-18-D2Y-T.step

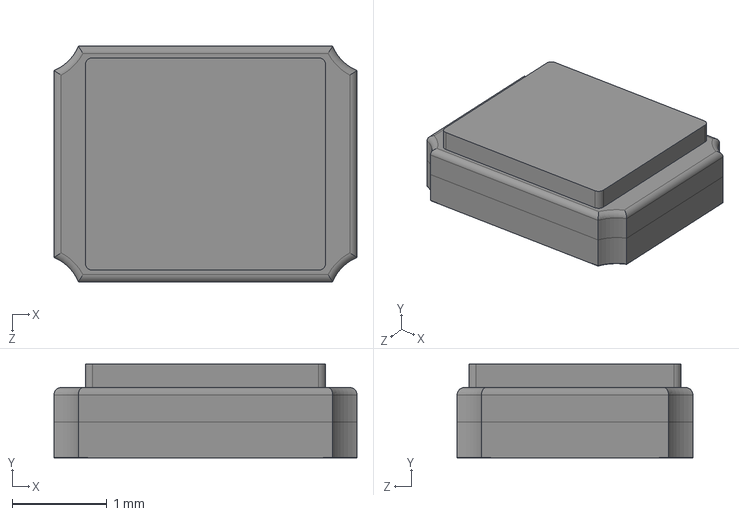
[picture p170: CAD file, 2026-09-09]
1.pcb/KiCad-library/chili-chips-lib/3dmodels/ABM8G-30.000MHZ-18-D2Y-T.step
3.20 x 0.991 x 2.49 mm
