chili-chips-ba/openPCIE/1.pcb/KiCad-library/EEZ-Kicad-libraries/3dmodels/sdr0403.stp

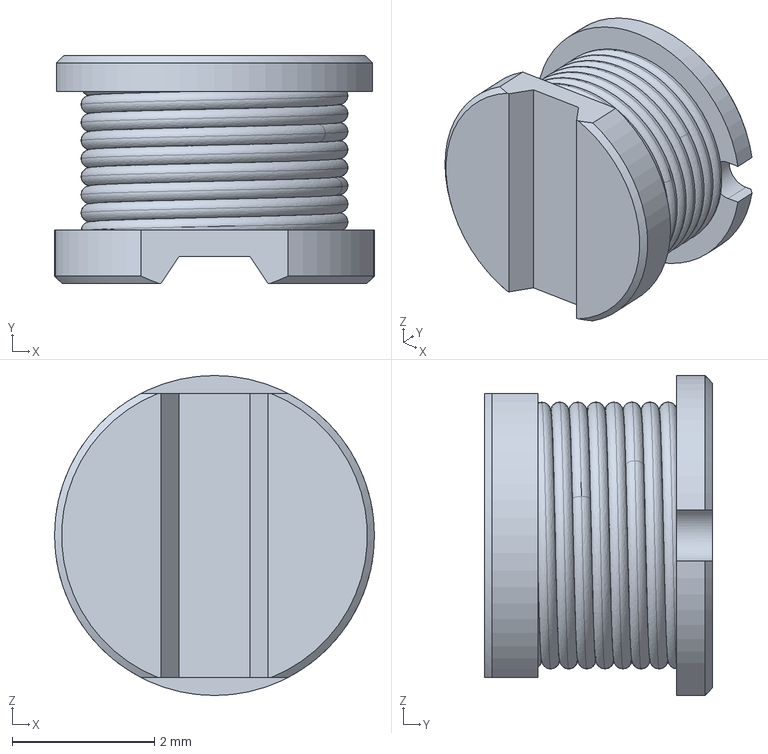
[picture p171: CAD file, 2026-10-06]
1.pcb/KiCad-library/EEZ-Kicad-libraries/3dmodels/sdr0403.stp
4.50 x 3.20 x 4.50 mm
