chili-chips-ba/openPCIE/1.pcb/KiCad-library/chili-chips-lib/3dmodels/TSX-3225_25.0000MF20X-AJ3.step

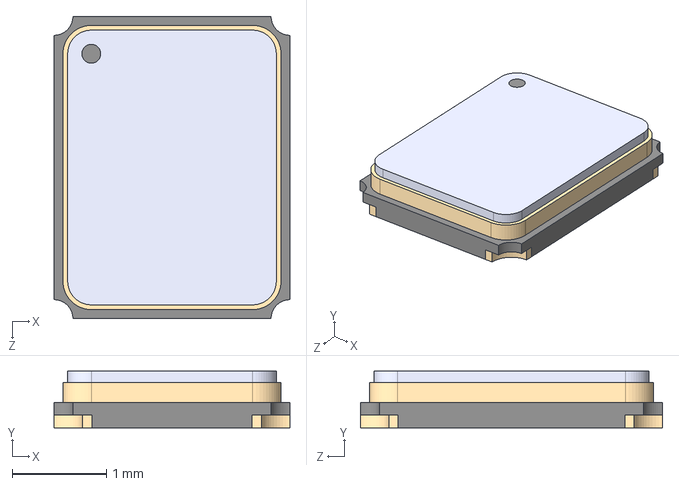
[picture p172: CAD file, 2026-09-09]
1.pcb/KiCad-library/chili-chips-lib/3dmodels/TSX-3225_25.0000MF20X-AJ3.step
2.50 x 0.6 x 3.20 mm
