chili-chips-ba/openPCIE/1.pcb/KiCad-library/EEZ-Kicad-libraries/3dmodels/TL1100CF160Q--3DModel-STEP-56544.STEP

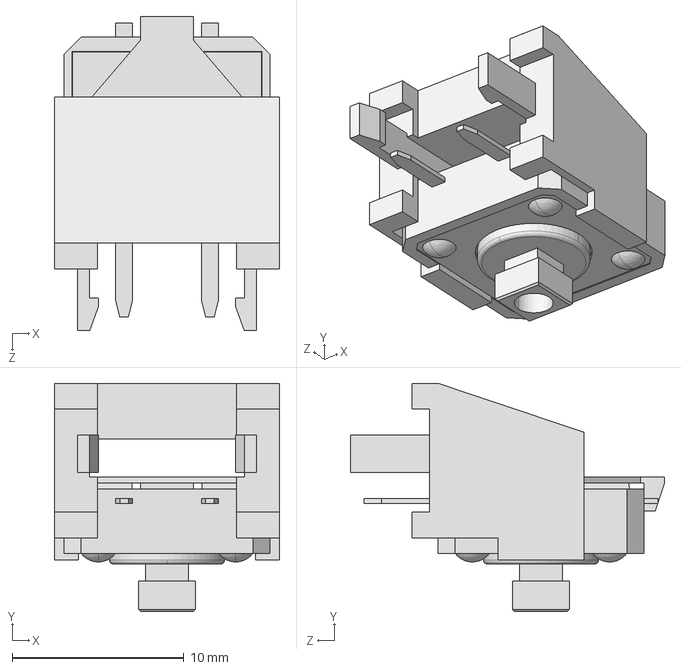
[picture p173: CAD file, 2026-10-06]
1.pcb/KiCad-library/EEZ-Kicad-libraries/3dmodels/TL1100CF160Q--3DModel-STEP-56544.STEP
13.1 x 13.3 x 18.3 mm
