chili-chips-ba/openPCIE/1.pcb/KiCad-library/EEZ-Kicad-libraries/3dmodels/EEE-FK1H470P.STEP

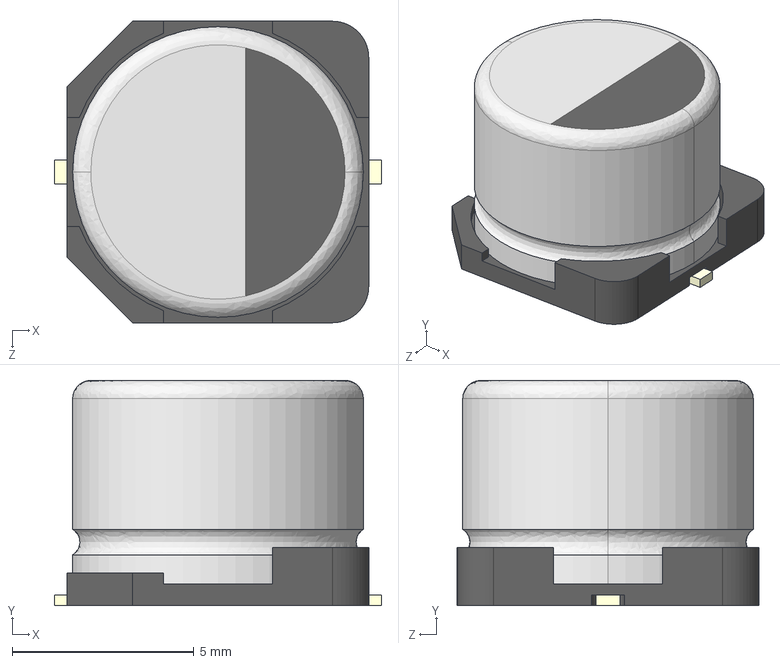
[picture p174: CAD file, 2026-10-06]
1.pcb/KiCad-library/EEZ-Kicad-libraries/3dmodels/EEE-FK1H470P.STEP
9.00 x 6.20 x 8.30 mm
