chili-chips-ba/openPCIE/1.pcb/KiCad-library/chili-chips-lib/3dmodels/DRY0006A.stp

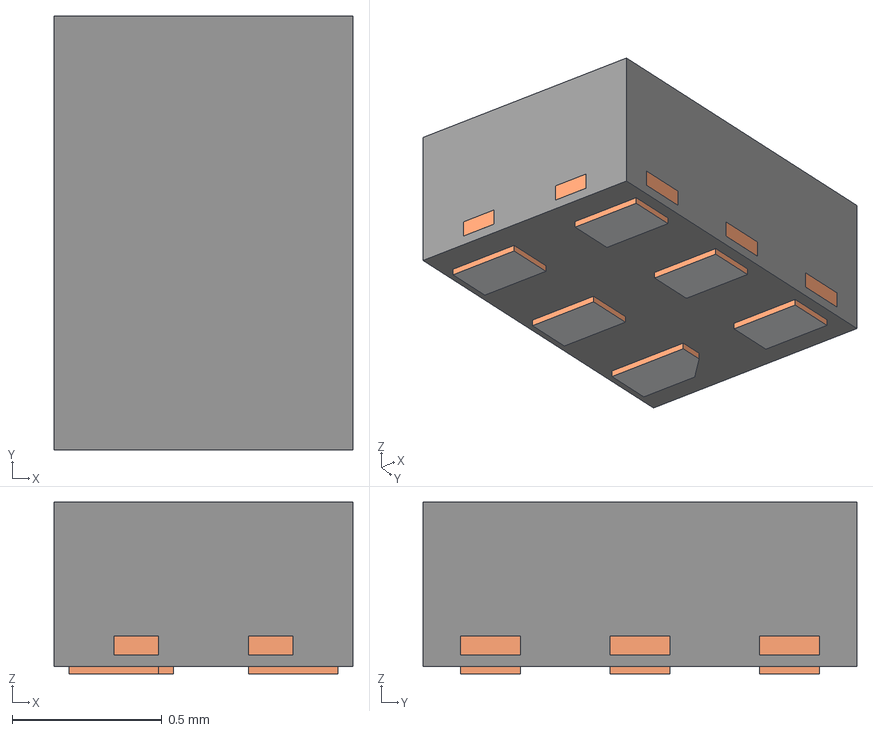
[picture p175: CAD file, 2026-09-09]
1.pcb/KiCad-library/chili-chips-lib/3dmodels/DRY0006A.stp
1.00 x 1.45 x 0.575 mm
BODY-SON
FRAME-DRY0006A
PIN1-ID
