chili-chips-ba/openPCIE/1.pcb/KiCad-library/EEZ-Kicad-libraries/3dmodels/B4P-VH_LF__SN_.step

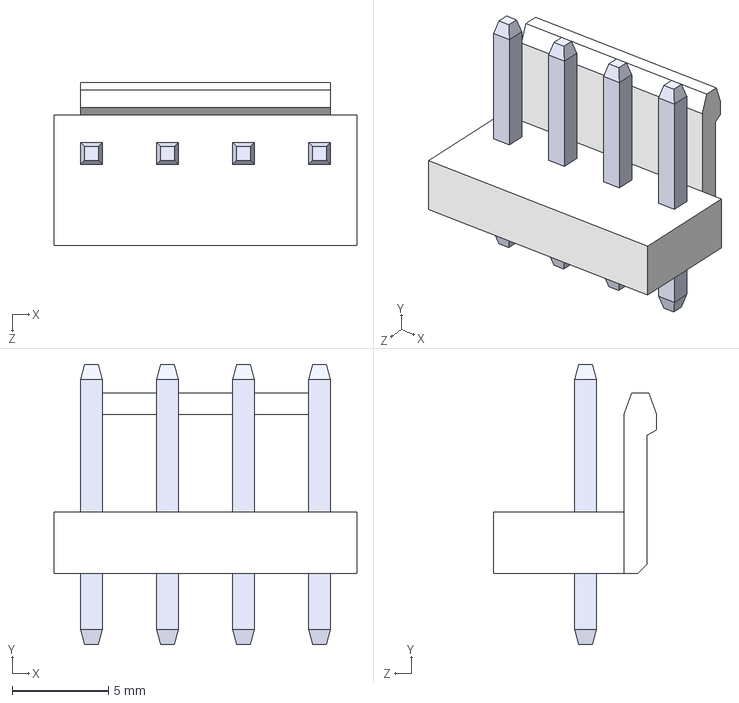
[picture p176: CAD file, 2026-10-06]
1.pcb/KiCad-library/EEZ-Kicad-libraries/3dmodels/B4P-VH_LF__SN_.step
15.8 x 14.6 x 8.50 mm
BxP-VH_4
pin x 4
