chili-chips-ba/openPCIE/1.pcb/KiCad-library/EEZ-Kicad-libraries/3dmodels/TSSOP-28_FEEB_LIT.step

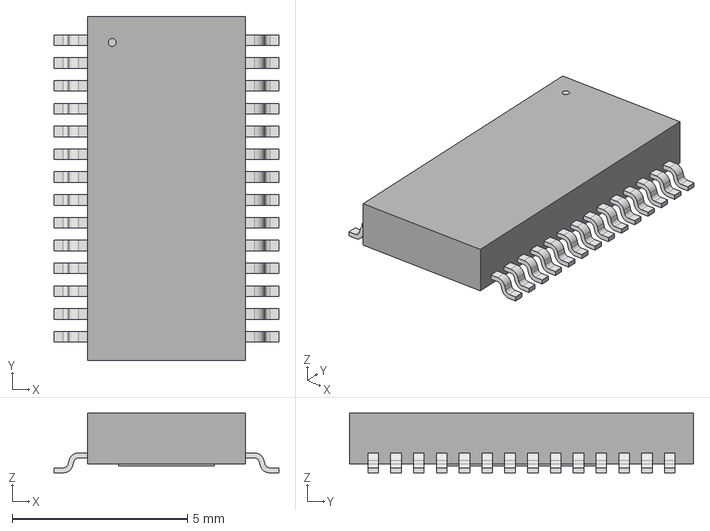
[picture p177: CAD file, 2026-10-06]
1.pcb/KiCad-library/EEZ-Kicad-libraries/3dmodels/TSSOP-28_FEEB_LIT.step
6.40 x 9.80 x 1.70 mm
