chili-chips-ba/openPCIE/1.pcb/KiCad-library/EEZ-Kicad-libraries/3dmodels/IND_DLW21S_0805_MUR.step

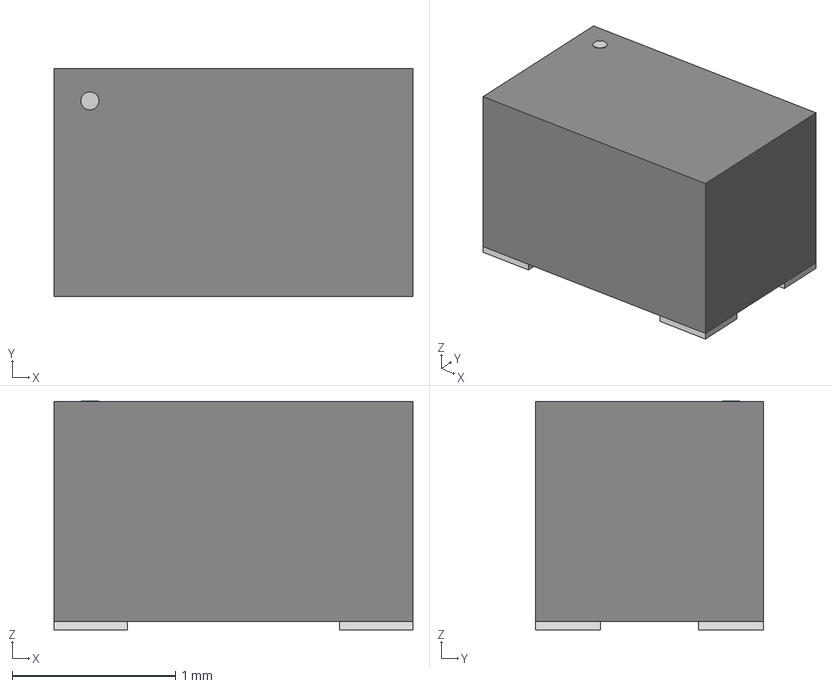
[picture p178: CAD file, 2026-10-06]
1.pcb/KiCad-library/EEZ-Kicad-libraries/3dmodels/IND_DLW21S_0805_MUR.step
2.20 x 1.40 x 1.40 mm
