chili-chips-ba/openPCIE/1.pcb/KiCad-library/chili-chips-lib/3dmodels/ECS-2520MVLC-250-CN-TR.step

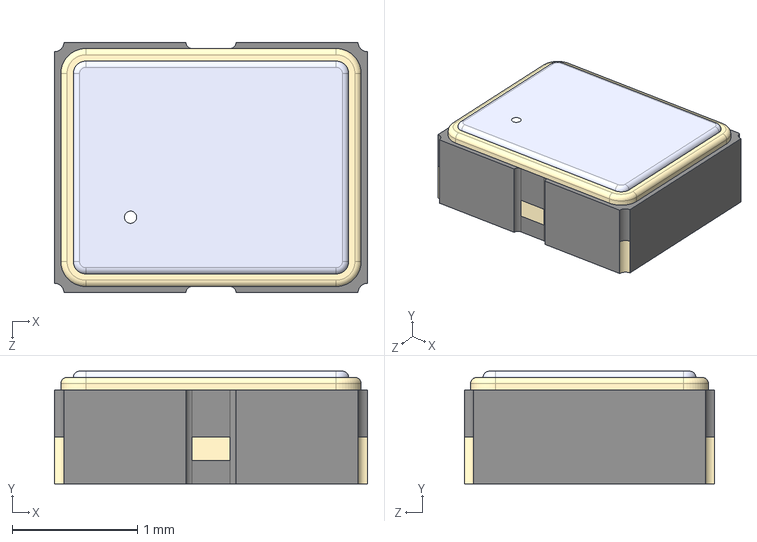
[picture p179: CAD file, 2026-09-09]
1.pcb/KiCad-library/chili-chips-lib/3dmodels/ECS-2520MVLC-250-CN-TR.step
2.50 x 0.9 x 2.00 mm
