chili-chips-ba/openPCIE/1.pcb/KiCad-library/EEZ-Kicad-libraries/3dmodels/NCP781BMNADJTAG.step

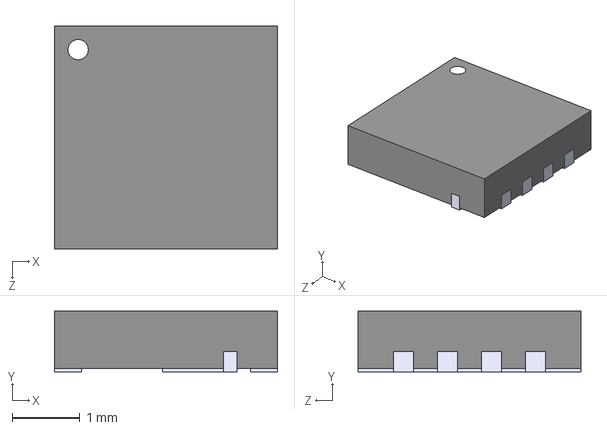
[picture p180: CAD file, 2026-10-06]
1.pcb/KiCad-library/EEZ-Kicad-libraries/3dmodels/NCP781BMNADJTAG.step
3.30 x 0.9 x 3.30 mm
