chili-chips-ba/openPCIE/1.pcb/KiCad-library/chili-chips-lib/3dmodels/DO-214AA.STEP

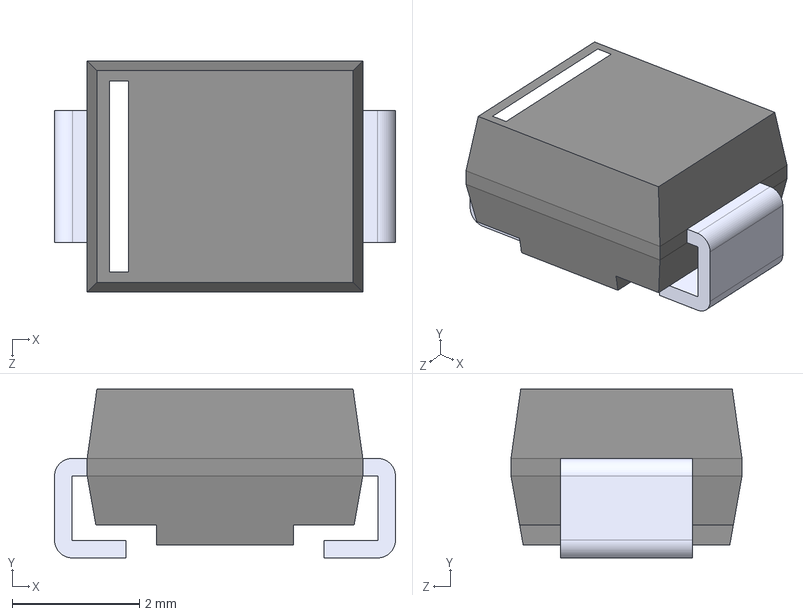
[picture p181: CAD file, 2026-09-09]
1.pcb/KiCad-library/chili-chips-lib/3dmodels/DO-214AA.STEP
5.35 x 2.65 x 3.62 mm
