chili-chips-ba/openPCIE/1.pcb/KiCad-library/chili-chips-lib/3dmodels/1269AS-H-2R2M_P2.step

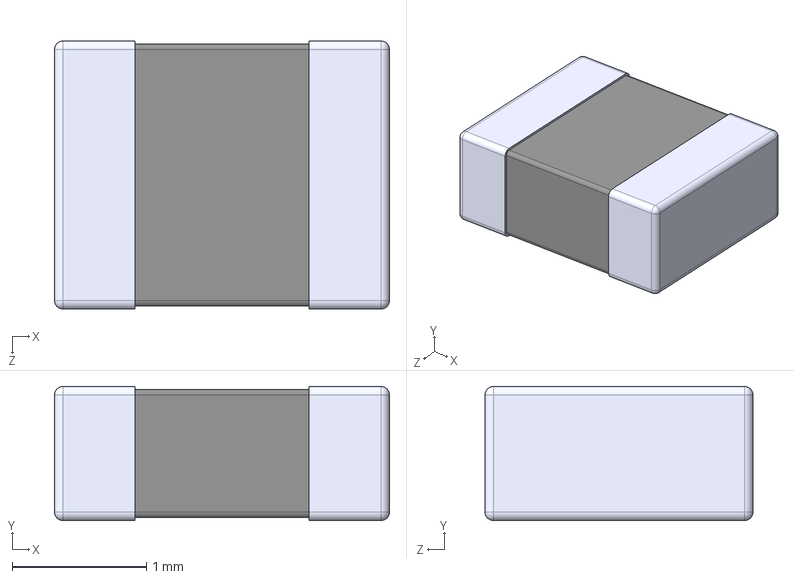
[picture p182: CAD file, 2026-09-09]
1.pcb/KiCad-library/chili-chips-lib/3dmodels/1269AS-H-2R2M_P2.step
2.50 x 1.00 x 2.00 mm
