chili-chips-ba/openPCIE/1.pcb/KiCad-library/EEZ-Kicad-libraries/3dmodels/c-6-146494-4-c-3d.stp

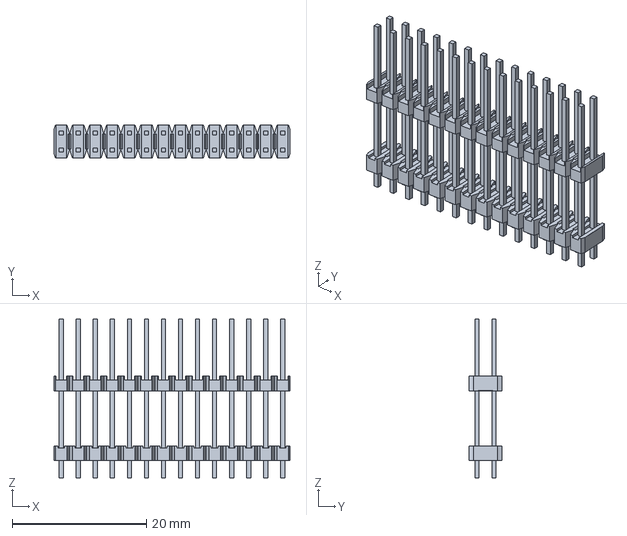
[picture p183: CAD file, 2026-10-06]
1.pcb/KiCad-library/EEZ-Kicad-libraries/3dmodels/c-6-146494-4-c-3d.stp
35.2 x 4.88 x 23.6 mm
