chili-chips-ba/openPCIE/1.pcb/KiCad-library/chili-chips-lib/3dmodels/BK13H-60DS2-0.35V10_3D_STP.stp

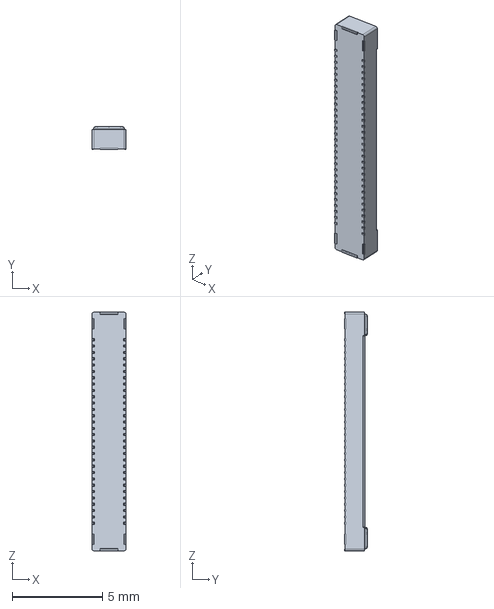
[picture p184: CAD file, 2026-09-09]
1.pcb/KiCad-library/chili-chips-lib/3dmodels/BK13H-60DS2-0.35V10_3D_STP.stp
1.90 x 1.25 x 13.2 mm
