chili-chips-ba/openPCIE/1.pcb/KiCad-library/EEZ-Kicad-libraries/3dmodels/B3FS-4052P.step

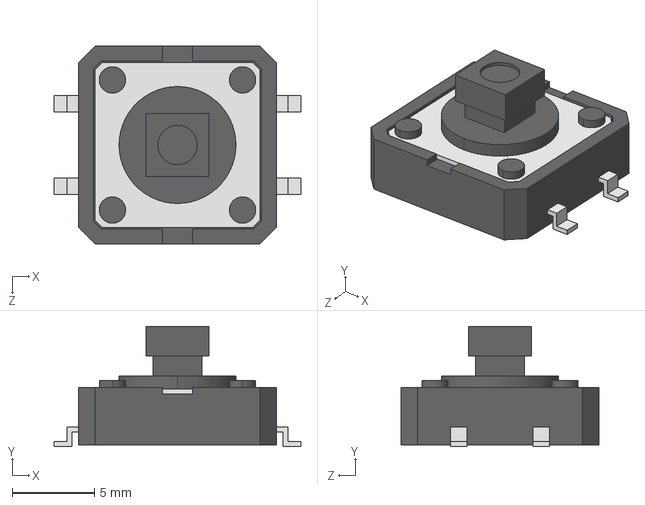
[picture p185: CAD file, 2026-10-06]
1.pcb/KiCad-library/EEZ-Kicad-libraries/3dmodels/B3FS-4052P.step
15.0 x 7.30 x 12.0 mm
