chili-chips-ba/openPCIE/1.pcb/KiCad-library/chili-chips-lib/3dmodels/CJS-1200TB.stp

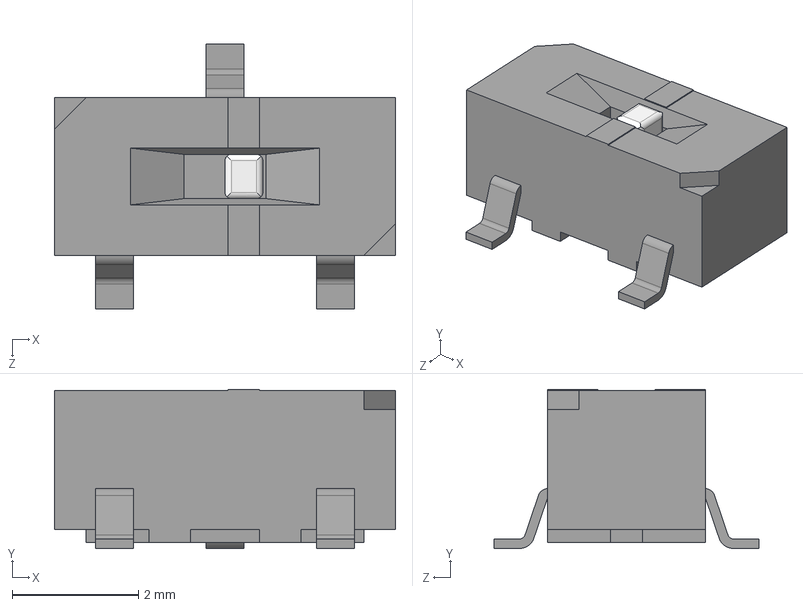
[picture p186: CAD file, 2026-09-09]
1.pcb/KiCad-library/chili-chips-lib/3dmodels/CJS-1200TB.stp
5.40 x 2.52 x 4.20 mm
CJS Slider_s^CJS-1200TB(2)_CJS-1200TB
CJS_c_12^CJS-1200TB(2)_CJS-1200TB
