chili-chips-ba/openPCIE/1.pcb/KiCad-library/EEZ-Kicad-libraries/3dmodels/ABS07AIG-32.768KHZ-6-D-T.stp

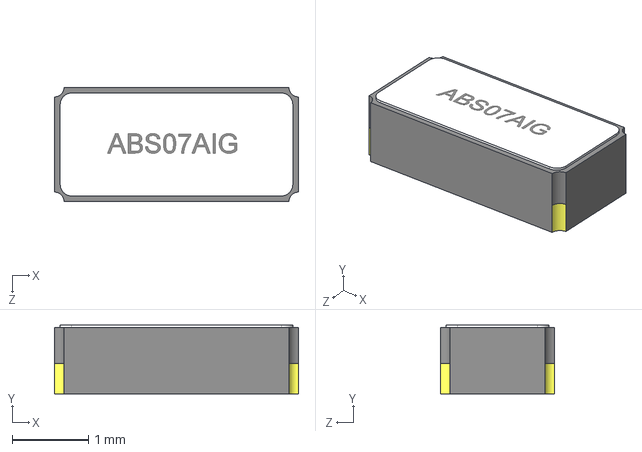
[picture p187: CAD file, 2026-10-06]
1.pcb/KiCad-library/EEZ-Kicad-libraries/3dmodels/ABS07AIG-32.768KHZ-6-D-T.stp
3.20 x 0.901 x 1.50 mm
