chili-chips-ba/openPCIE/1.pcb/KiCad-library/chili-chips-lib/3dmodels/FT4232H-56Q.step

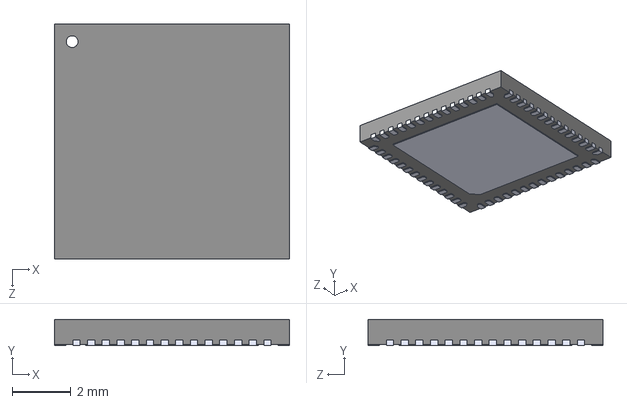
[picture p188: CAD file, 2026-09-09]
1.pcb/KiCad-library/chili-chips-lib/3dmodels/FT4232H-56Q.step
8.00 x 0.9 x 8.00 mm
