chili-chips-ba/openPCIE/1.pcb/KiCad-library/EEZ-Kicad-libraries/3dmodels/PSMN0R9-25YLC,115.STEP

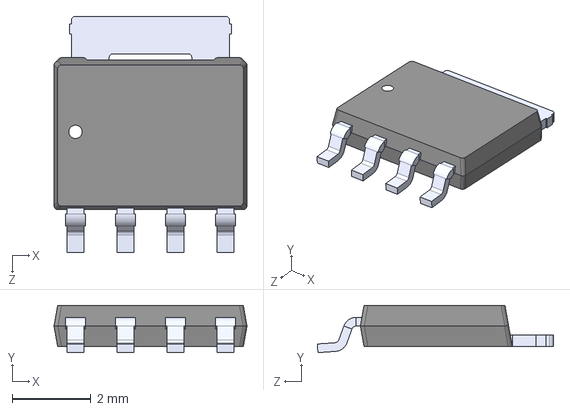
[picture p189: CAD file, 2026-10-06]
1.pcb/KiCad-library/EEZ-Kicad-libraries/3dmodels/PSMN0R9-25YLC,115.STEP
4.90 x 1.20 x 6.00 mm
