chili-chips-ba/openPCIE/1.pcb/KiCad-library/EEZ-Kicad-libraries/3dmodels/RS-20_ADI.step

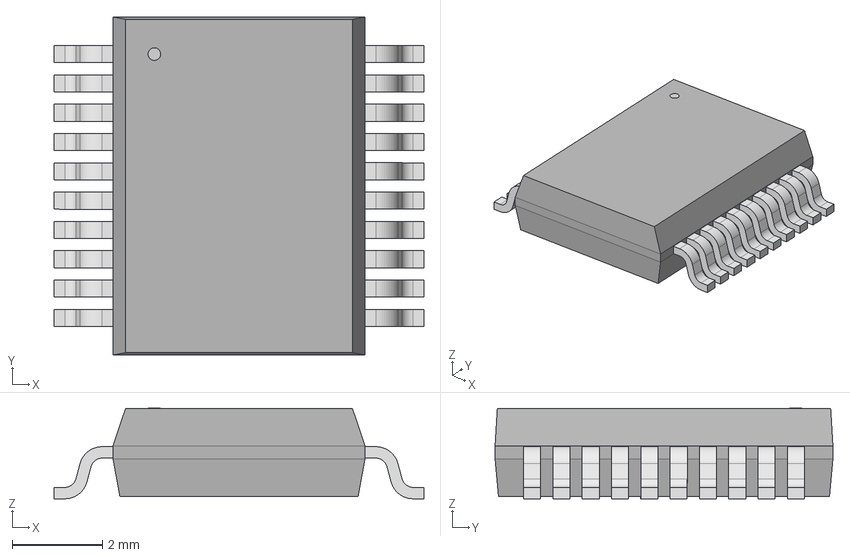
[picture p190: CAD file, 2026-10-06]
1.pcb/KiCad-library/EEZ-Kicad-libraries/3dmodels/RS-20_ADI.step
8.20 x 7.49 x 2.01 mm
