chili-chips-ba/openPCIE/1.pcb/KiCad-library/EEZ-Kicad-libraries/3dmodels/ECMF4-2450A60N10.stp

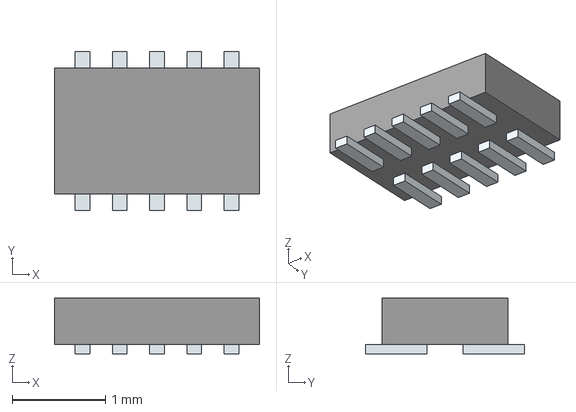
[picture p191: CAD file, 2026-10-06]
1.pcb/KiCad-library/EEZ-Kicad-libraries/3dmodels/ECMF4-2450A60N10.stp
2.20 x 1.71 x 0.6 mm
Pins
