chili-chips-ba/openPCIE/1.pcb/KiCad-library/chili-chips-lib/3dmodels/DX07S024JJ2R1300.step

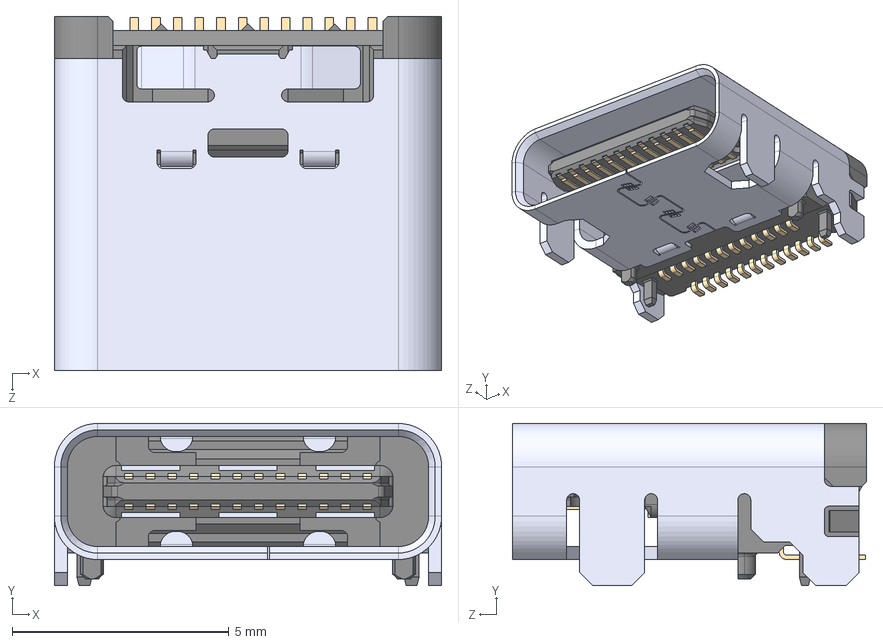
[picture p192: CAD file, 2026-09-09]
1.pcb/KiCad-library/chili-chips-lib/3dmodels/DX07S024JJ2R1300.step
8.94 x 3.74 x 8.17 mm
