chili-chips-ba/openPCIE/1.pcb/KiCad-library/chili-chips-lib/3dmodels/LSF0102GSX.step

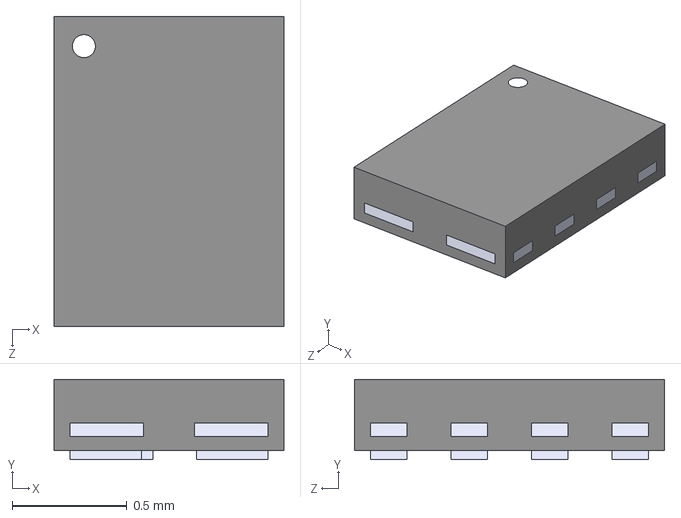
[picture p193: CAD file, 2026-09-09]
1.pcb/KiCad-library/chili-chips-lib/3dmodels/LSF0102GSX.step
1.00 x 0.35 x 1.35 mm
