chili-chips-ba/openPCIE/1.pcb/KiCad-library/EEZ-Kicad-libraries/3dmodels/SOT223.STEP

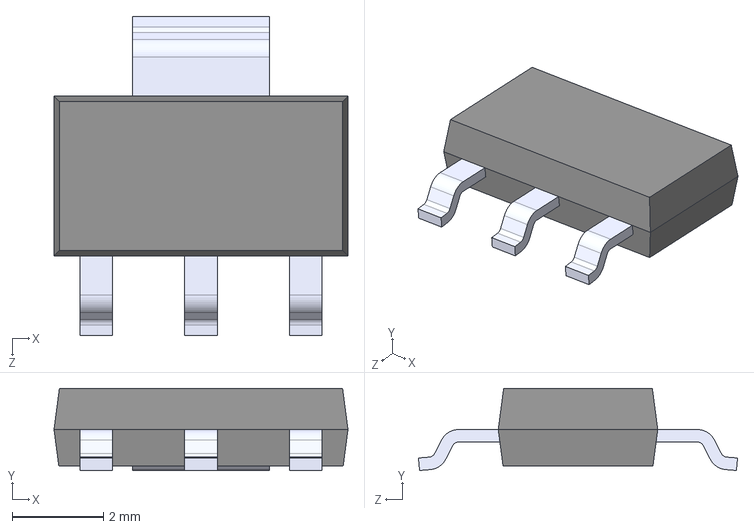
[picture p194: CAD file, 2026-10-06]
1.pcb/KiCad-library/EEZ-Kicad-libraries/3dmodels/SOT223.STEP
6.45 x 1.80 x 7.00 mm
