chili-chips-ba/openPCIE/1.pcb/KiCad-library/chili-chips-lib/3dmodels/DA7217-00U32.stp

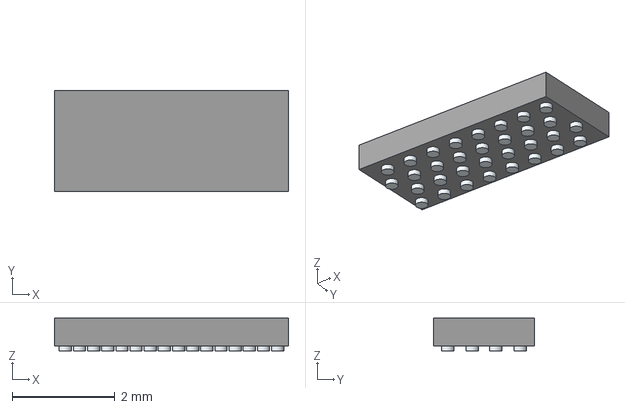
[picture p195: CAD file, 2026-09-09]
1.pcb/KiCad-library/chili-chips-lib/3dmodels/DA7217-00U32.stp
4.54 x 1.96 x 0.639 mm
Pins
