chili-chips-ba/openPCIE/1.pcb/KiCad-library/EEZ-Kicad-libraries/3dmodels/PAG0064A.stp

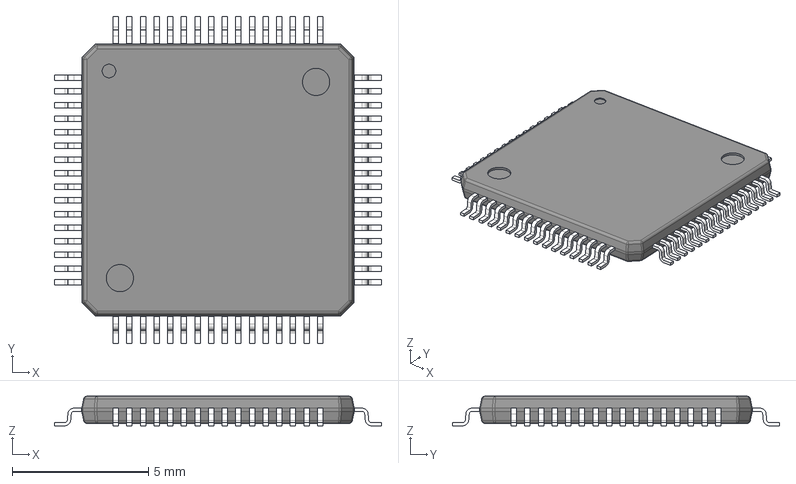
[picture p196: CAD file, 2026-10-06]
1.pcb/KiCad-library/EEZ-Kicad-libraries/3dmodels/PAG0064A.stp
12.0 x 12.0 x 1.09 mm
BODY_VEC64A
LEAD_VEC64A x 64
