chili-chips-ba/openPCIE/1.pcb/KiCad-library/chili-chips-lib/3dmodels/RHB0032E.stp

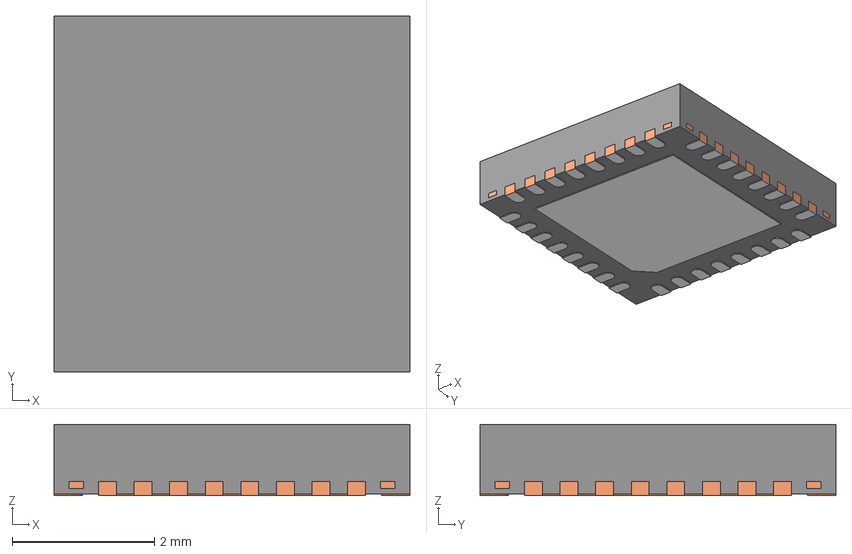
[picture p197: CAD file, 2026-09-09]
1.pcb/KiCad-library/chili-chips-lib/3dmodels/RHB0032E.stp
5.00 x 5.00 x 1.00 mm
BODY-QFN
FRAME-RHB0032E
PIN1-ID
