chili-chips-ba/openPCIE/1.pcb/KiCad-library/EEZ-Kicad-libraries/3dmodels/LQFP48-7x7mm.step

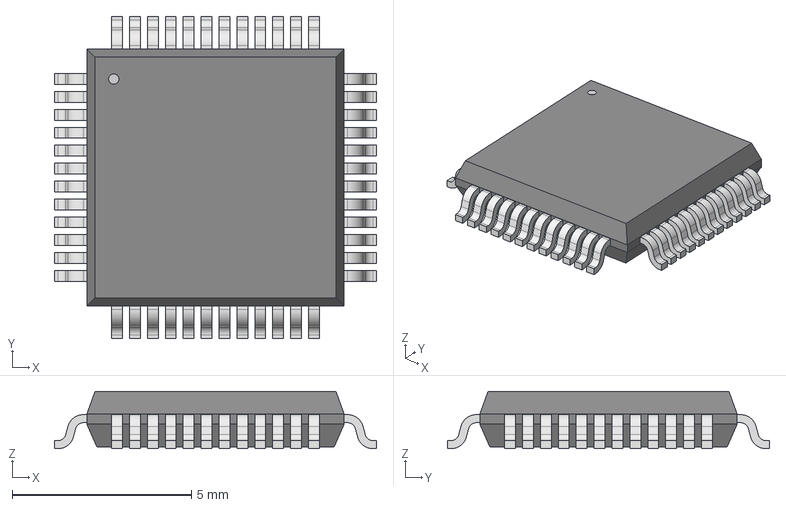
[picture p198: CAD file, 2026-10-06]
1.pcb/KiCad-library/EEZ-Kicad-libraries/3dmodels/LQFP48-7x7mm.step
8.99 x 8.99 x 1.60 mm
