chili-chips-ba/openPCIE/1.pcb/KiCad-library/chili-chips-lib/3dmodels/TDFN-6.step

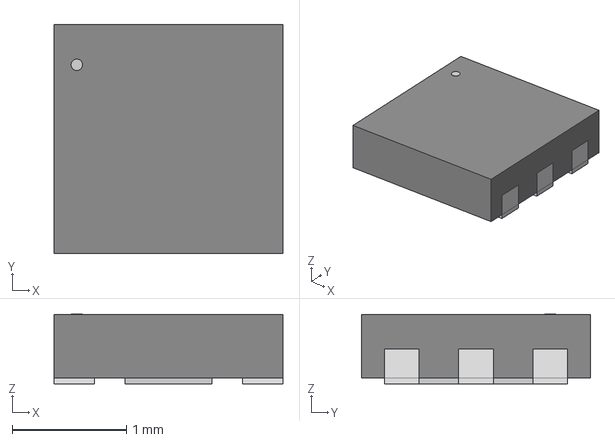
[picture p199: CAD file, 2026-09-09]
1.pcb/KiCad-library/chili-chips-lib/3dmodels/TDFN-6.step
2.01 x 2.01 x 0.612 mm
