chili-chips-ba/openPCIE/1.pcb/KiCad-library/chili-chips-lib/3dmodels/SON50P200X300X100-9N.step

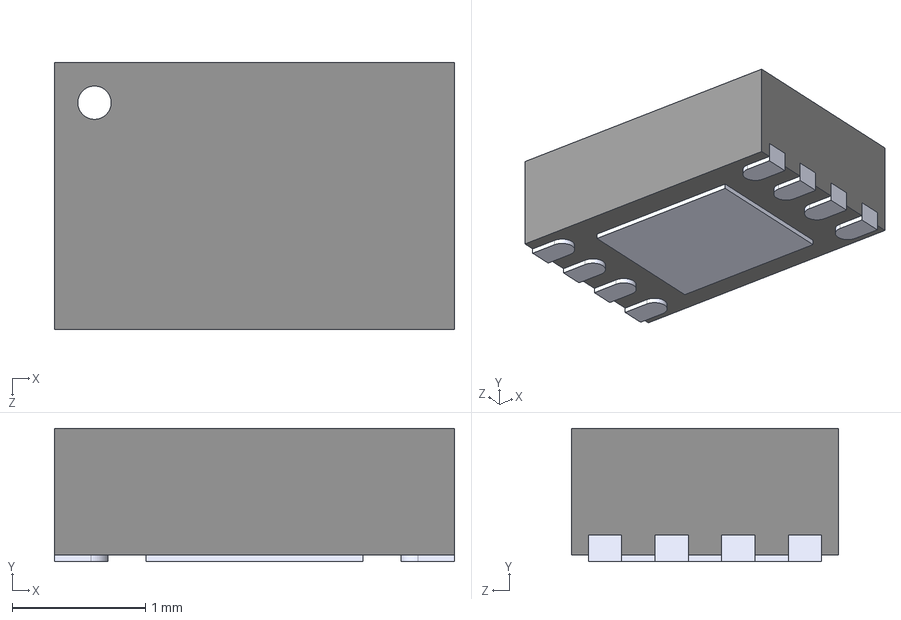
[picture p200: CAD file, 2026-09-09]
1.pcb/KiCad-library/chili-chips-lib/3dmodels/SON50P200X300X100-9N.step
3.00 x 1.00 x 2.00 mm
