chili-chips-ba/openPCIE/1.pcb/KiCad-library/EEZ-Kicad-libraries/3dmodels/PinHeader_1x03_P2.54mm_Vertical.step

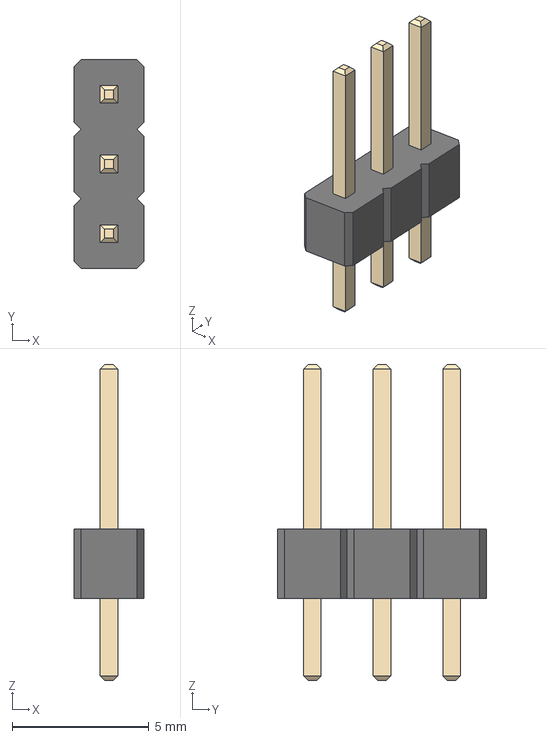
[picture p201: CAD file, 2026-10-06]
1.pcb/KiCad-library/EEZ-Kicad-libraries/3dmodels/PinHeader_1x03_P2.54mm_Vertical.step
2.54 x 7.62 x 11.5 mm
