chili-chips-ba/openPCIE/1.pcb/KiCad-library/chili-chips-lib/3dmodels/W25Q64JWZPIQ.stp

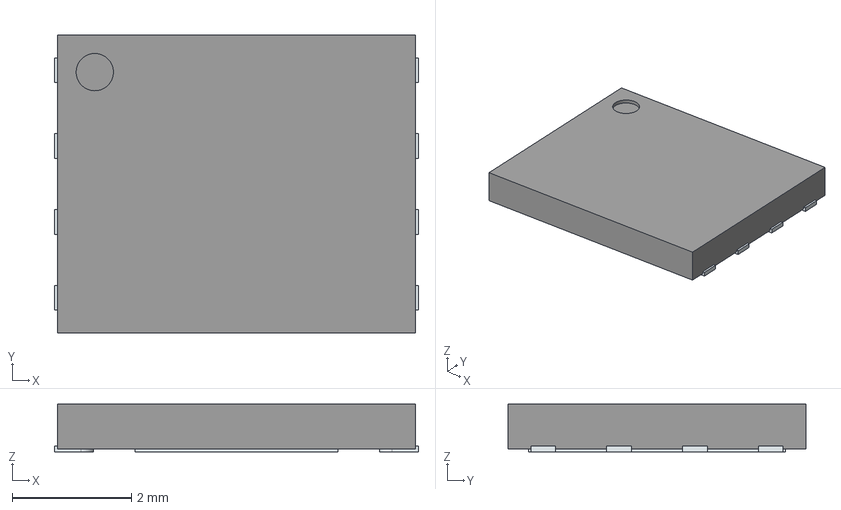
[picture p202: CAD file, 2026-09-09]
1.pcb/KiCad-library/chili-chips-lib/3dmodels/W25Q64JWZPIQ.stp
6.10 x 5.00 x 0.8 mm
ThermalPin
PinsArrayLR
