chili-chips-ba/openPCIE/1.pcb/KiCad-library/EEZ-Kicad-libraries/3dmodels/U_SOT765-1_NEX.step

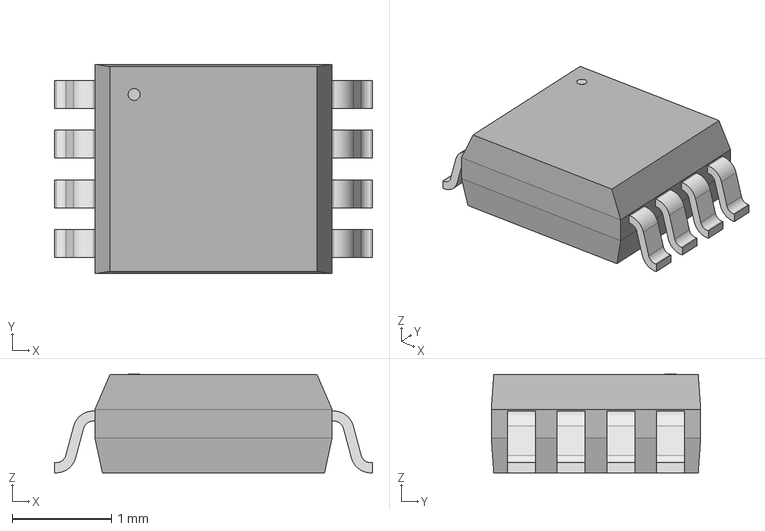
[picture p203: CAD file, 2026-10-06]
1.pcb/KiCad-library/EEZ-Kicad-libraries/3dmodels/U_SOT765-1_NEX.step
3.20 x 2.11 x 0.993 mm
