chili-chips-ba/openPCIE/1.pcb/KiCad-library/chili-chips-lib/3dmodels/TQFN32_ZHQ_DIO.step

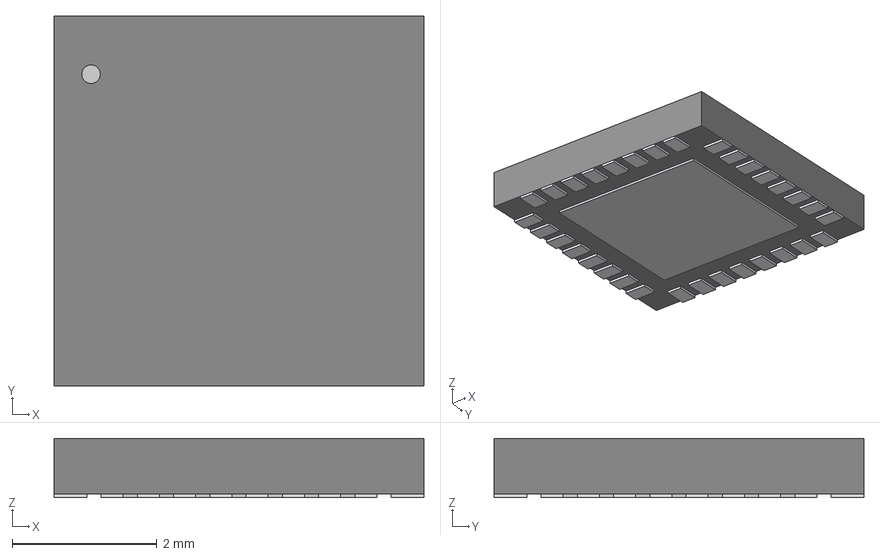
[picture p204: CAD file, 2026-09-09]
1.pcb/KiCad-library/chili-chips-lib/3dmodels/TQFN32_ZHQ_DIO.step
5.11 x 5.11 x 0.815 mm
