chili-chips-ba/openPCIE/1.pcb/KiCad-library/EEZ-Kicad-libraries/3dmodels/TO220FP.STEP

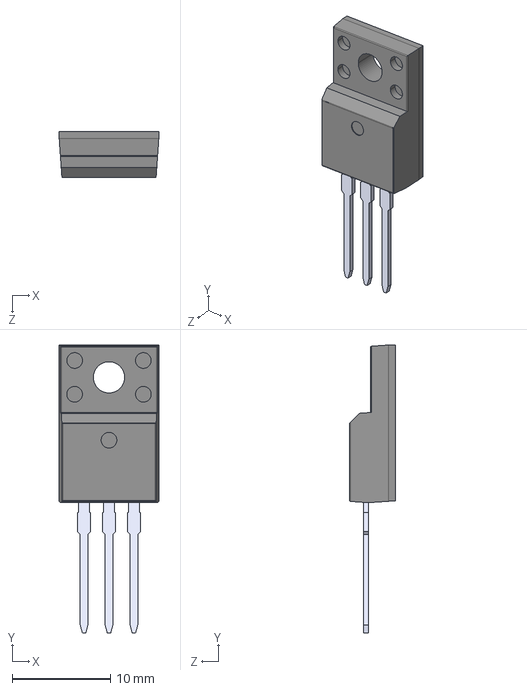
[picture p205: CAD file, 2026-10-06]
1.pcb/KiCad-library/EEZ-Kicad-libraries/3dmodels/TO220FP.STEP
10.2 x 29.4 x 4.70 mm
