chili-chips-ba/openPCIE/1.pcb/KiCad-library/chili-chips-lib/3dmodels/20TQFN-ZB_PI3USB302-A_DIO.step

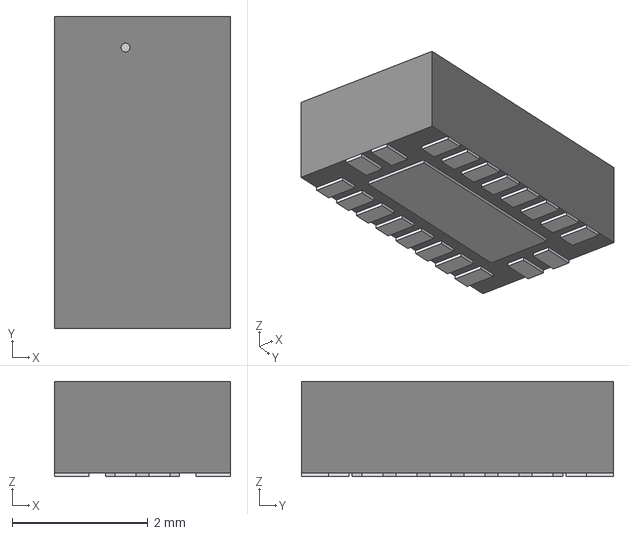
[picture p206: CAD file, 2026-09-09]
1.pcb/KiCad-library/chili-chips-lib/3dmodels/20TQFN-ZB_PI3USB302-A_DIO.step
2.59 x 4.60 x 1.40 mm
