chili-chips-ba/openPCIE/1.pcb/KiCad-library/EEZ-Kicad-libraries/3dmodels/RN112-x-02.stp

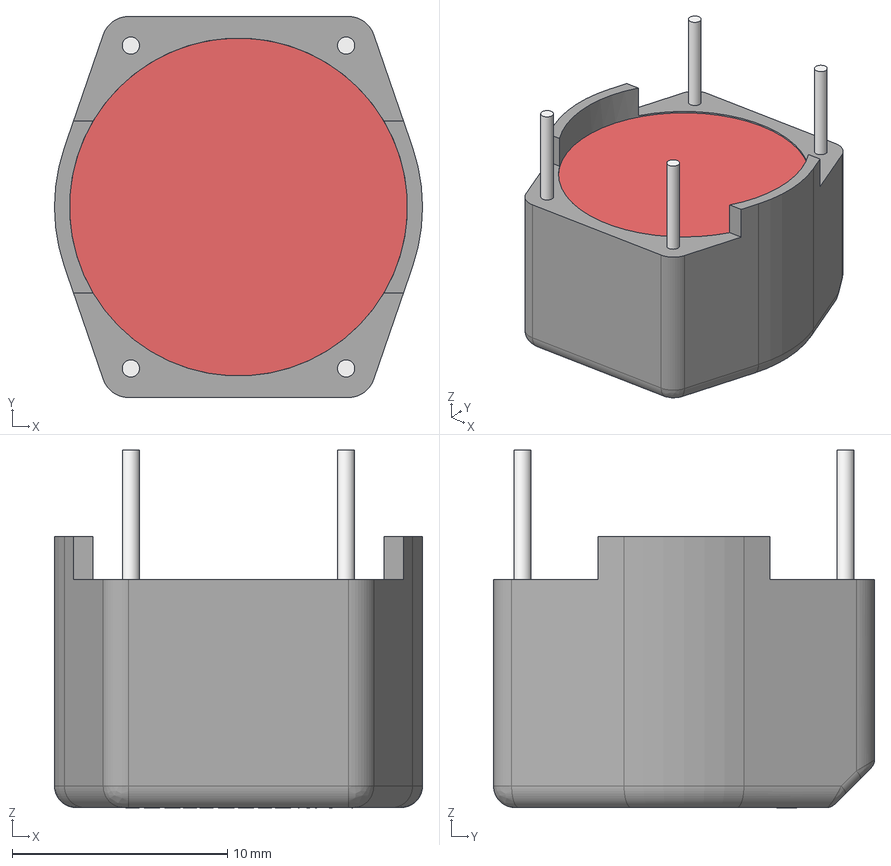
[picture p207: CAD file, 2026-10-06]
1.pcb/KiCad-library/EEZ-Kicad-libraries/3dmodels/RN112-x-02.stp
17.1 x 17.7 x 16.6 mm
