chili-chips-ba/openPCIE/1.pcb/KiCad-library/chili-chips-lib/3dmodels/ICS-41351.step

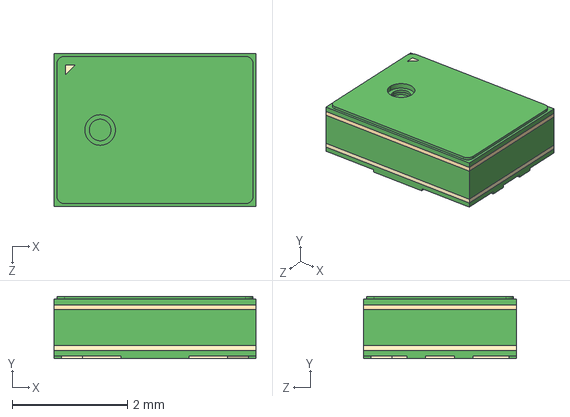
[picture p208: CAD file, 2026-09-09]
1.pcb/KiCad-library/chili-chips-lib/3dmodels/ICS-41351.step
3.50 x 1.08 x 2.65 mm
