chili-chips-ba/openPCIE/1.pcb/KiCad-library/EEZ-Kicad-libraries/3dmodels/pwr220t-35-2r20j.stp

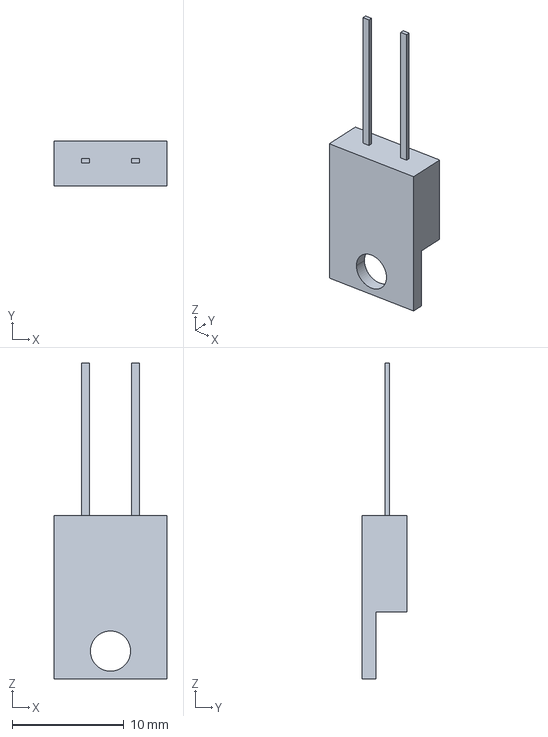
[picture p209: CAD file, 2026-10-06]
1.pcb/KiCad-library/EEZ-Kicad-libraries/3dmodels/pwr220t-35-2r20j.stp
10.1 x 4.00 x 28.3 mm
