chili-chips-ba/openPCIE/1.pcb/KiCad-library/EEZ-Kicad-libraries/3dmodels/ER-TFT050-6 (simplified).step

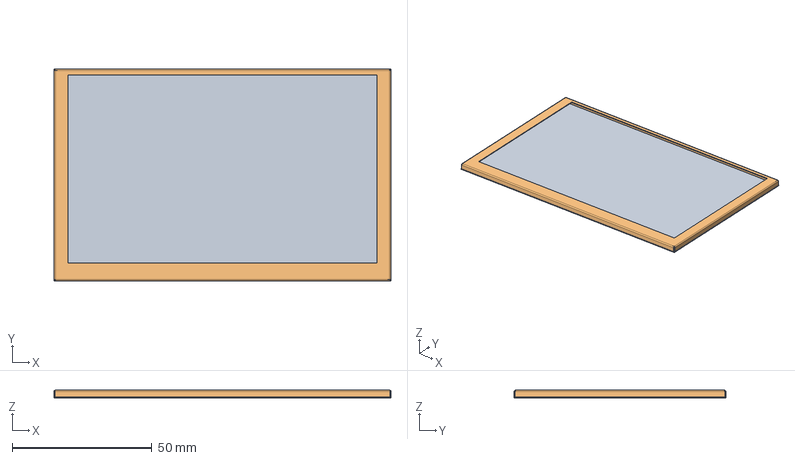
[picture p210: CAD file, 2026-10-06]
1.pcb/KiCad-library/EEZ-Kicad-libraries/3dmodels/ER-TFT050-6 (simplified).step
120.7 x 75.8 x 2.80 mm
