chili-chips-ba/openPCIE/1.pcb/KiCad-library/chili-chips-lib/3dmodels/QFN-24_4X4X0_9_NXP.step

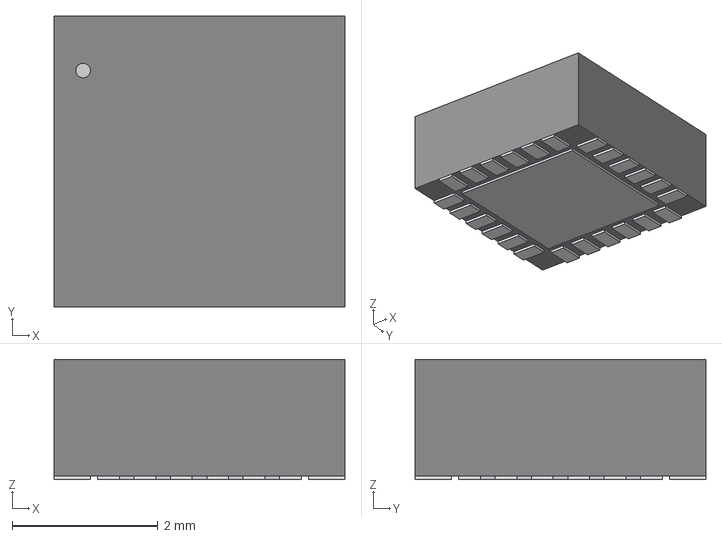
[picture p211: CAD file, 2026-09-09]
1.pcb/KiCad-library/chili-chips-lib/3dmodels/QFN-24_4X4X0_9_NXP.step
4.00 x 4.00 x 1.65 mm
