chili-chips-ba/openPCIE/1.pcb/KiCad-library/EEZ-Kicad-libraries/3dmodels/supercap.step

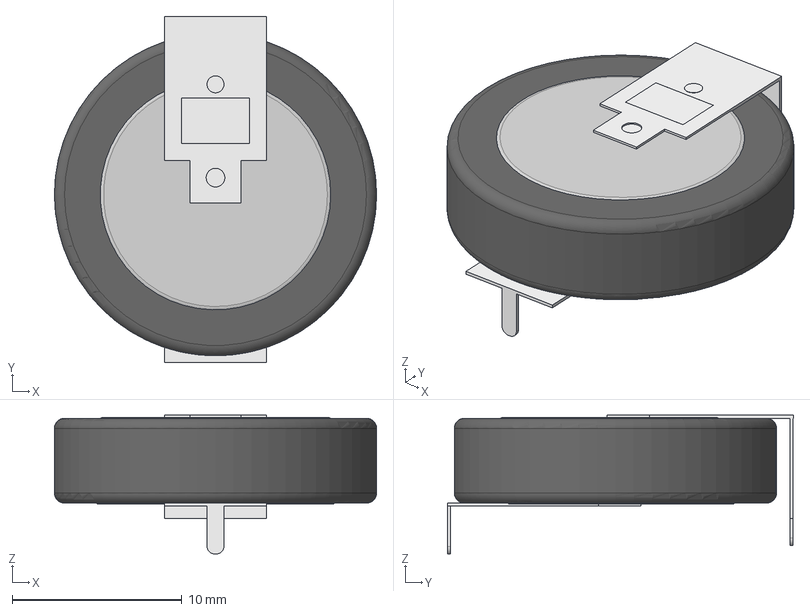
[picture p212: CAD file, 2026-10-06]
1.pcb/KiCad-library/EEZ-Kicad-libraries/3dmodels/supercap.step
19.0 x 20.4 x 8.19 mm
Zylinder003
Würfel008
Würfel007
