chili-chips-ba/openPCIE/1.pcb/KiCad-library/chili-chips-lib/3dmodels/SOD-953_ONS.step

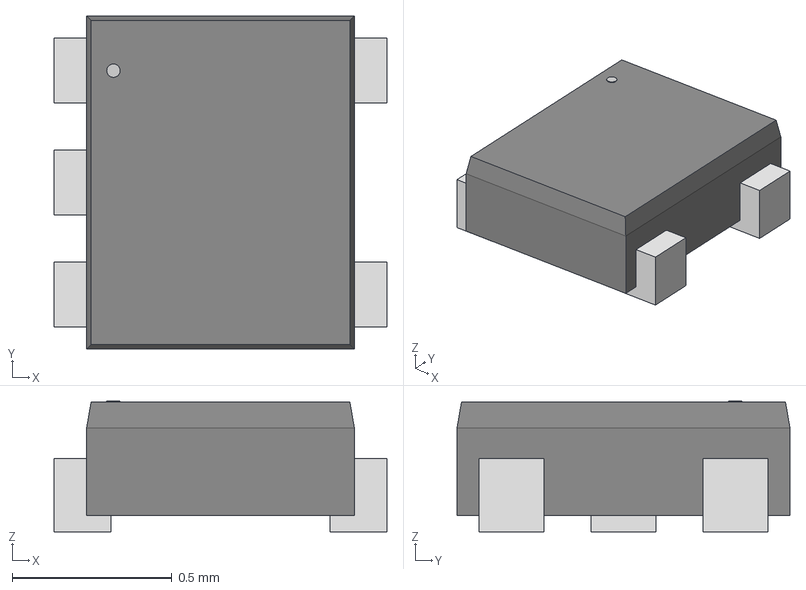
[picture p213: CAD file, 2026-09-09]
1.pcb/KiCad-library/chili-chips-lib/3dmodels/SOD-953_ONS.step
1.04 x 1.04 x 0.409 mm
