chili-chips-ba/openPCIE/1.pcb/KiCad-library/EEZ-Kicad-libraries/3dmodels/TO-236AB_NEX.step

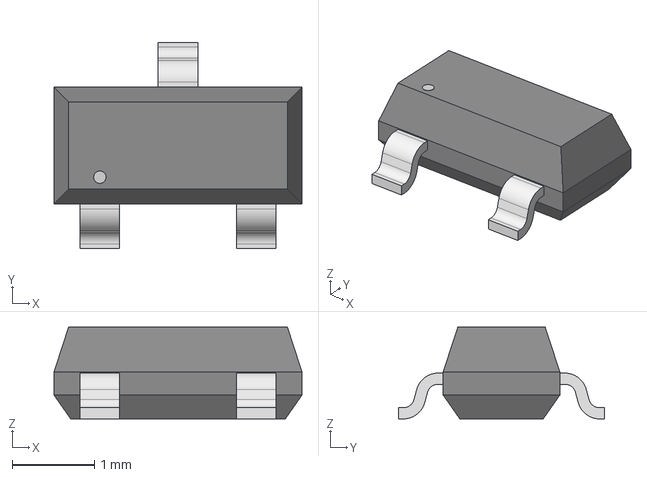
[picture p214: CAD file, 2026-10-06]
1.pcb/KiCad-library/EEZ-Kicad-libraries/3dmodels/TO-236AB_NEX.step
3.02 x 2.51 x 1.12 mm
