chili-chips-ba/openPCIE/1.pcb/KiCad-library/chili-chips-lib/3dmodels/SOD993.step

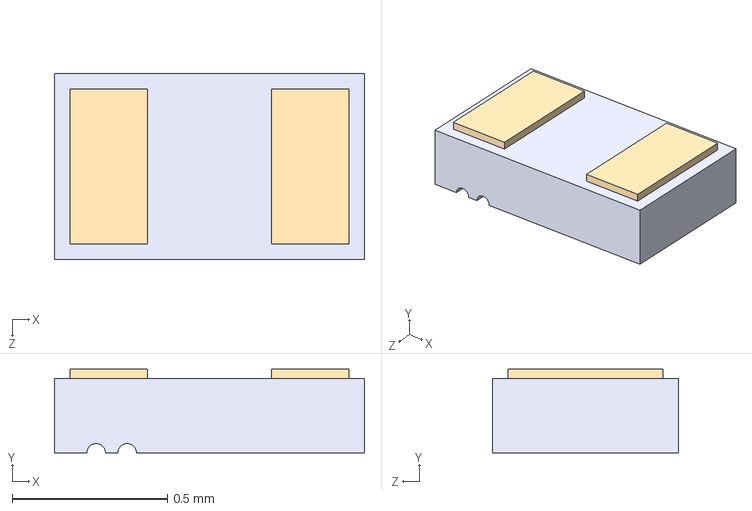
[picture p215: CAD file, 2026-09-09]
1.pcb/KiCad-library/chili-chips-lib/3dmodels/SOD993.step
1.00 x 0.27 x 0.6 mm
