chili-chips-ba/openPCIE/1.pcb/KiCad-library/EEZ-Kicad-libraries/3dmodels/MLP14_2P5X2P5_ONS.step

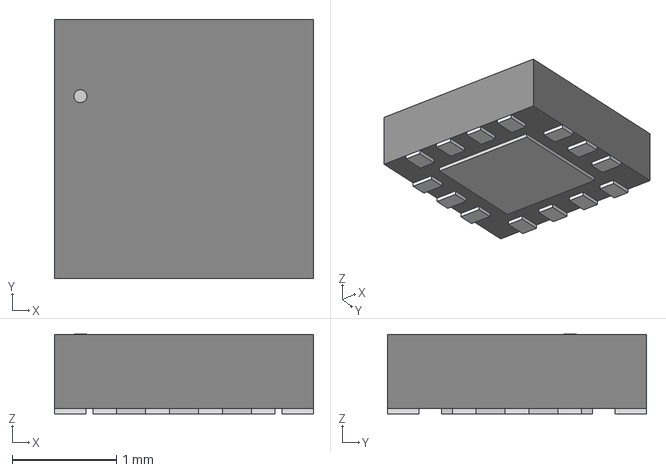
[picture p216: CAD file, 2026-10-06]
1.pcb/KiCad-library/EEZ-Kicad-libraries/3dmodels/MLP14_2P5X2P5_ONS.step
2.49 x 2.49 x 0.765 mm
