chili-chips-ba/openPCIE/1.pcb/KiCad-library/chili-chips-lib/3dmodels/VFQFN-48.STEP

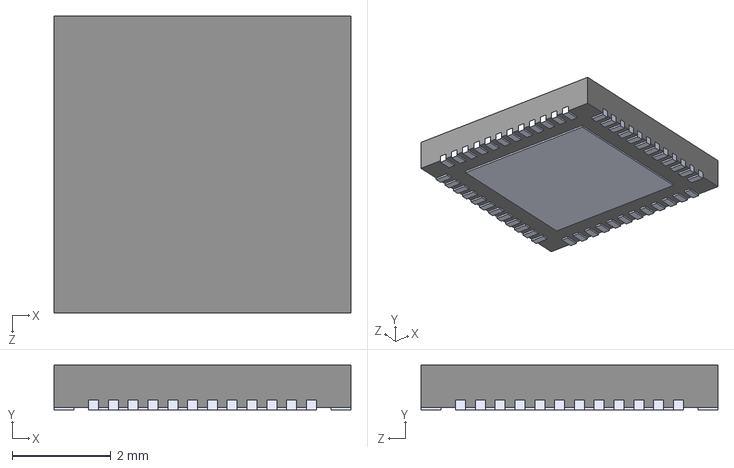
[picture p217: CAD file, 2026-09-09]
1.pcb/KiCad-library/chili-chips-lib/3dmodels/VFQFN-48.STEP
6.00 x 0.9 x 6.00 mm
