chili-chips-ba/openPCIE/1.pcb/KiCad-library/chili-chips-lib/3dmodels/ECS-120-10-36B-CWY-TR3.step

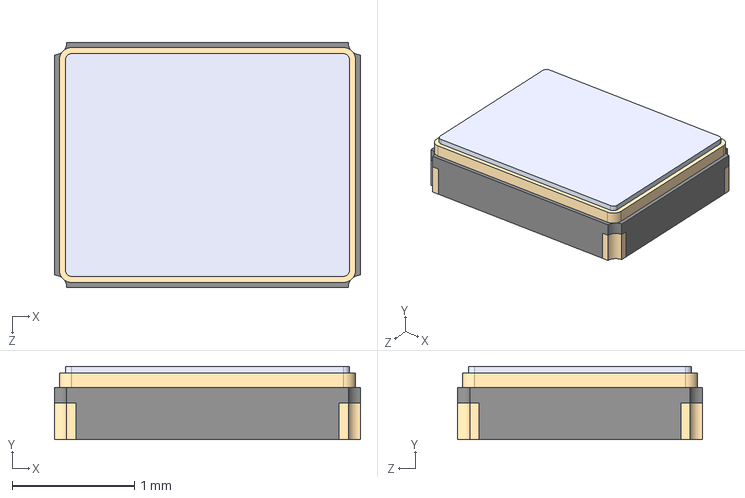
[picture p219: CAD file, 2026-09-09]
1.pcb/KiCad-library/chili-chips-lib/3dmodels/ECS-120-10-36B-CWY-TR3.step
2.50 x 0.6 x 2.00 mm
