chili-chips-ba/openPCIE/1.pcb/KiCad-library/chili-chips-lib/3dmodels/SKRPABE010.step

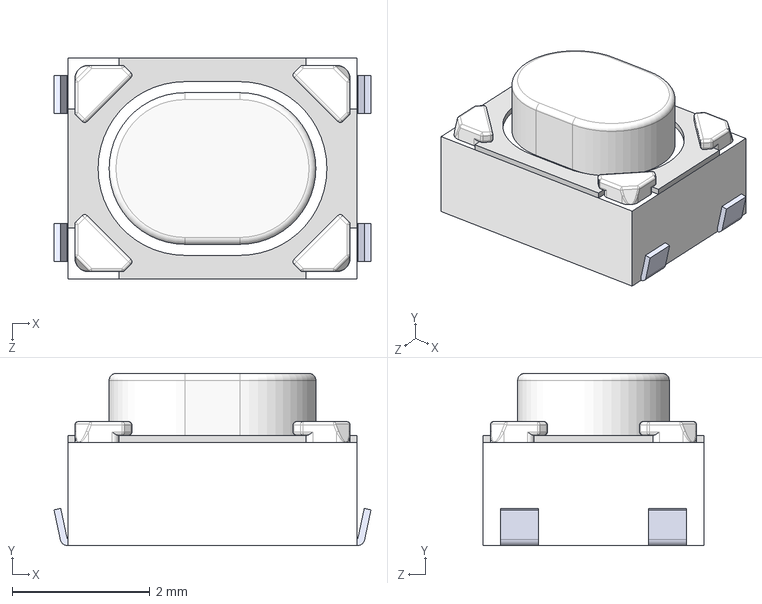
[picture p220: CAD file, 2026-09-09]
1.pcb/KiCad-library/chili-chips-lib/3dmodels/SKRPABE010.step
4.60 x 2.50 x 3.20 mm
