chili-chips-ba/openPCIE/1.pcb/KiCad-library/chili-chips-lib/3dmodels/IND_DFE322520F_MUR.step

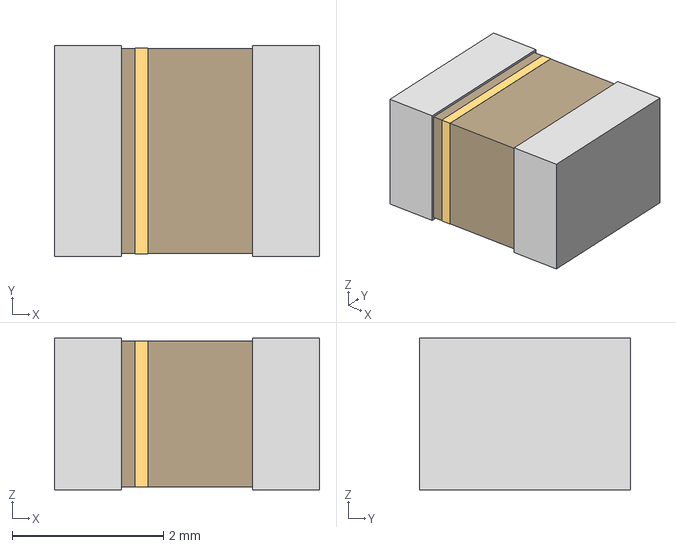
[picture p221: CAD file, 2026-09-09]
1.pcb/KiCad-library/chili-chips-lib/3dmodels/IND_DFE322520F_MUR.step
3.51 x 2.79 x 2.01 mm
