chili-chips-ba/openPCIE/1.pcb/KiCad-library/EEZ-Kicad-libraries/3dmodels/571-0500.step

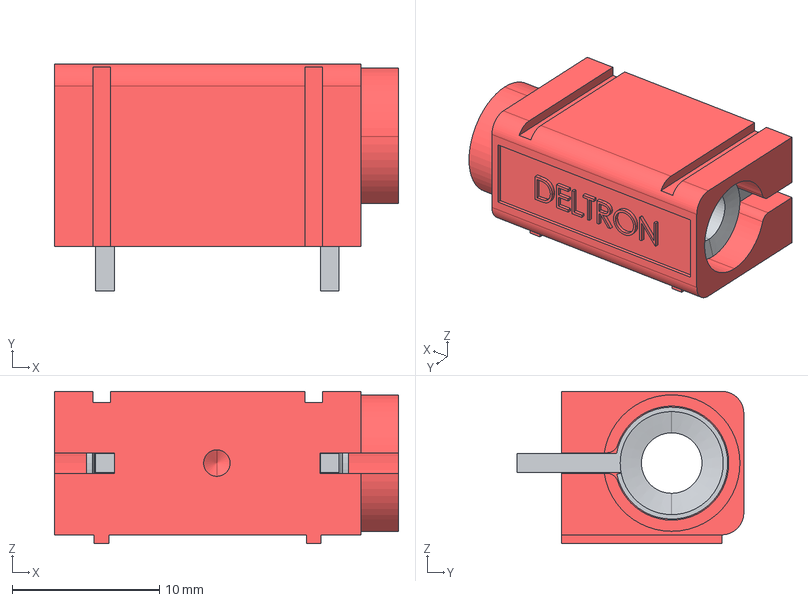
[picture p222: CAD file, 2026-10-06]
1.pcb/KiCad-library/EEZ-Kicad-libraries/3dmodels/571-0500.step
23.4 x 15.4 x 10.3 mm
571-002-9110_deformed
571-003-9210_Short x 2
