chili-chips-ba/openPCIE/1.pcb/KiCad-library/chili-chips-lib/3dmodels/LSF0204RUTR.step

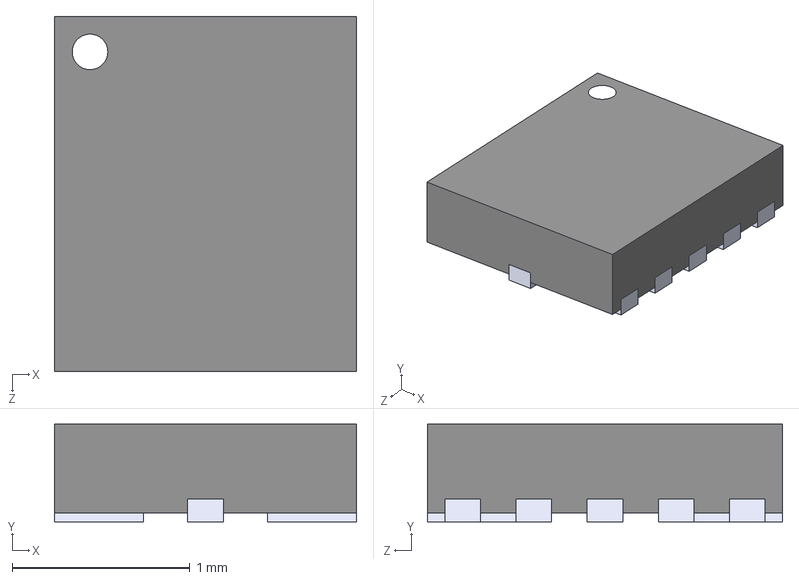
[picture p223: CAD file, 2026-09-09]
1.pcb/KiCad-library/chili-chips-lib/3dmodels/LSF0204RUTR.step
1.70 x 0.55 x 2.00 mm
