chili-chips-ba/openPCIE/1.pcb/KiCad-library/EEZ-Kicad-libraries/3dmodels/C_1210_3225Metric.step

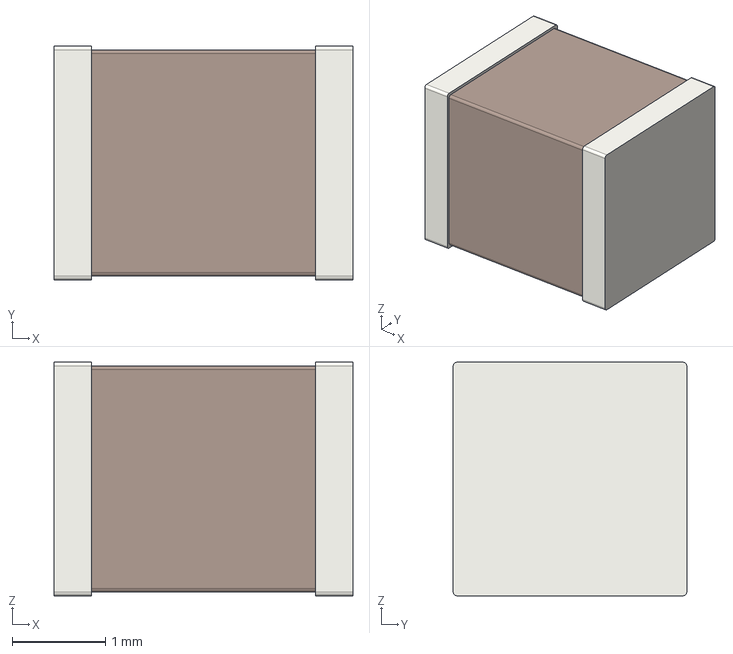
[picture p224: CAD file, 2026-10-06]
1.pcb/KiCad-library/EEZ-Kicad-libraries/3dmodels/C_1210_3225Metric.step
3.20 x 2.50 x 2.50 mm
