chili-chips-ba/openPCIE/1.pcb/KiCad-library/chili-chips-lib/3dmodels/df13-2p-1_25ds_25_.stp

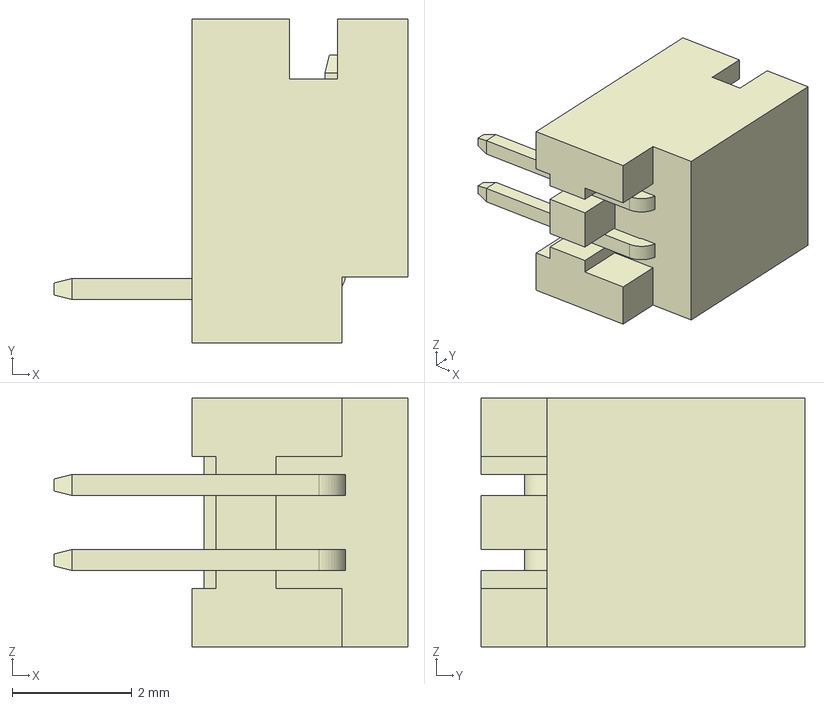
[picture p225: CAD file, 2026-09-09]
1.pcb/KiCad-library/chili-chips-lib/3dmodels/df13-2p-1_25ds_25_.stp
5.90 x 5.40 x 4.15 mm
