chili-chips-ba/openPCIE/1.pcb/KiCad-library/EEZ-Kicad-libraries/3dmodels/TAS2505IRGER.step

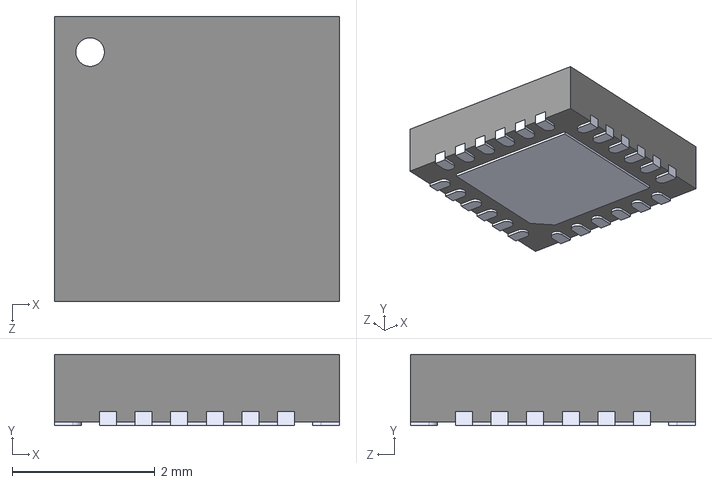
[picture p226: CAD file, 2026-10-06]
1.pcb/KiCad-library/EEZ-Kicad-libraries/3dmodels/TAS2505IRGER.step
4.00 x 1.00 x 4.00 mm
