chili-chips-ba/openPCIE/1.pcb/KiCad-library/chili-chips-lib/3dmodels/IND_SRP4030FA_BRN.step

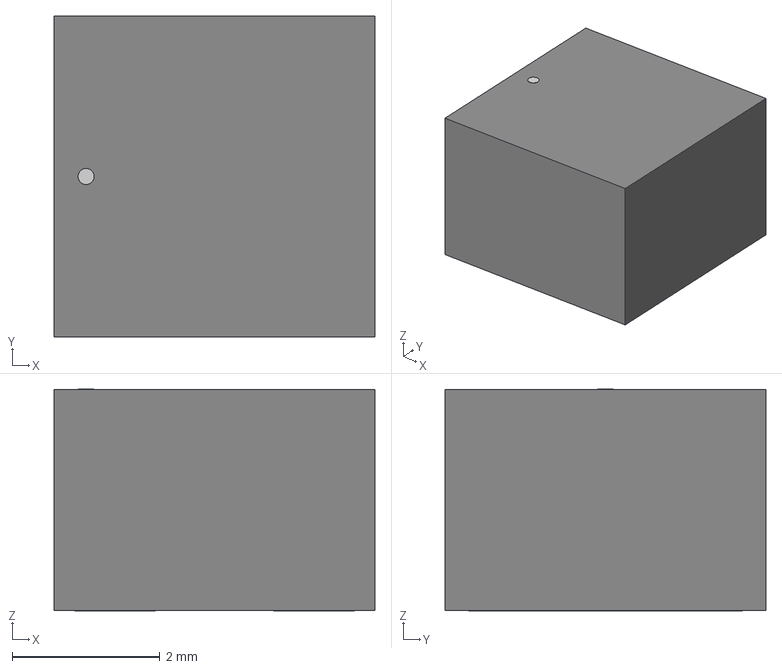
[picture p227: CAD file, 2026-09-09]
1.pcb/KiCad-library/chili-chips-lib/3dmodels/IND_SRP4030FA_BRN.step
4.34 x 4.34 x 3.00 mm
