chili-chips-ba/openPCIE/1.pcb/KiCad-library/EEZ-Kicad-libraries/3dmodels/TBP03R1-350-03BE.step

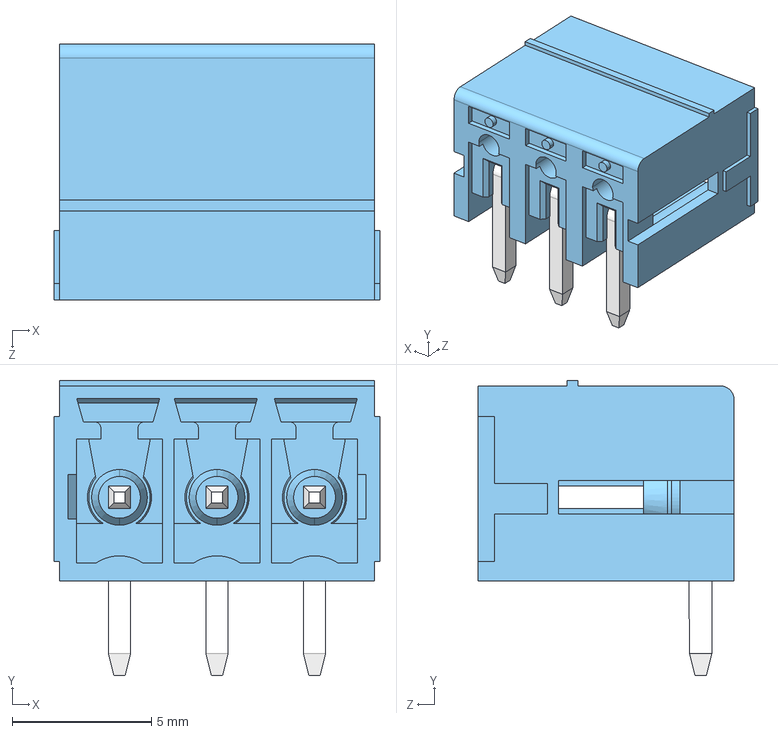
[picture p228: CAD file, 2026-10-06]
1.pcb/KiCad-library/EEZ-Kicad-libraries/3dmodels/TBP03R1-350-03BE.step
11.7 x 10.6 x 9.20 mm
