chili-chips-ba/openPCIE/1.pcb/KiCad-library/EEZ-Kicad-libraries/3dmodels/Same_Sky_PJ-002BH-SMT-TR.step

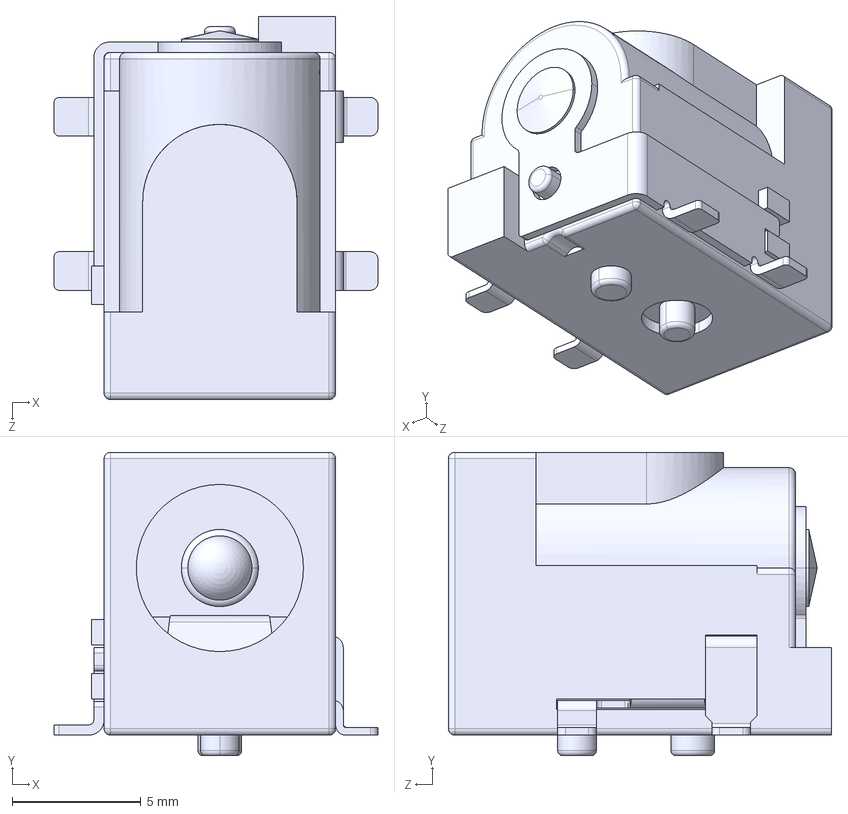
[picture p229: CAD file, 2026-10-06]
1.pcb/KiCad-library/EEZ-Kicad-libraries/3dmodels/Same_Sky_PJ-002BH-SMT-TR.step
12.6 x 11.8 x 14.9 mm
