chili-chips-ba/openPCIE/1.pcb/KiCad-library/EEZ-Kicad-libraries/3dmodels/SOD-123_ONS.step

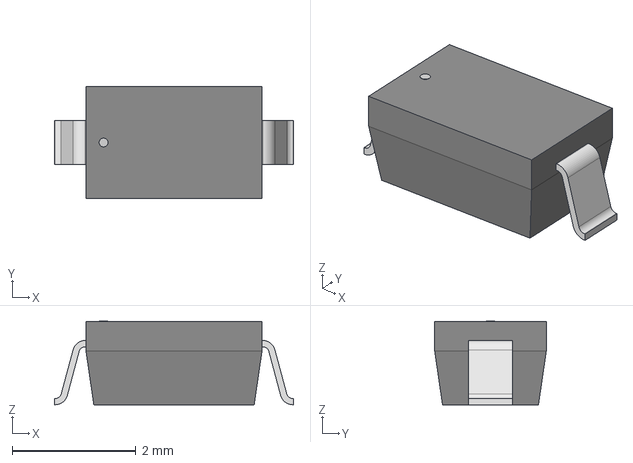
[picture p230: CAD file, 2026-10-06]
1.pcb/KiCad-library/EEZ-Kicad-libraries/3dmodels/SOD-123_ONS.step
3.86 x 1.80 x 1.35 mm
