chili-chips-ba/openPCIE/1.pcb/KiCad-library/chili-chips-lib/3dmodels/QFN76_FTD.step

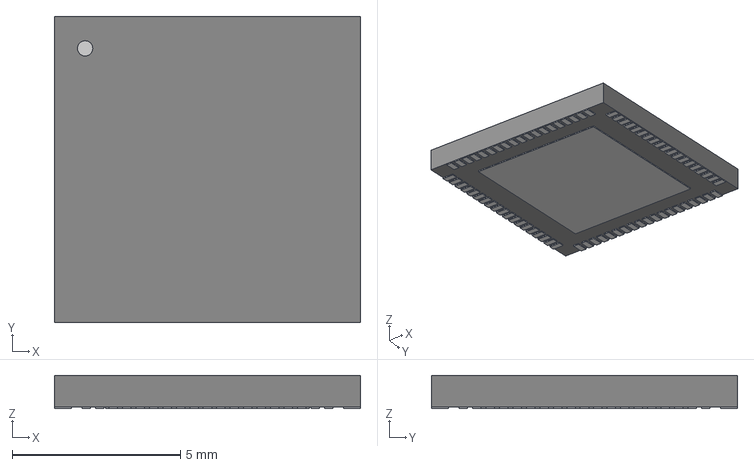
[picture p231: CAD file, 2026-09-09]
1.pcb/KiCad-library/chili-chips-lib/3dmodels/QFN76_FTD.step
9.09 x 9.09 x 0.993 mm
