chili-chips-ba/openPCIE/1.pcb/KiCad-library/EEZ-Kicad-libraries/3dmodels/BGA153_MX52LM_MAC.step

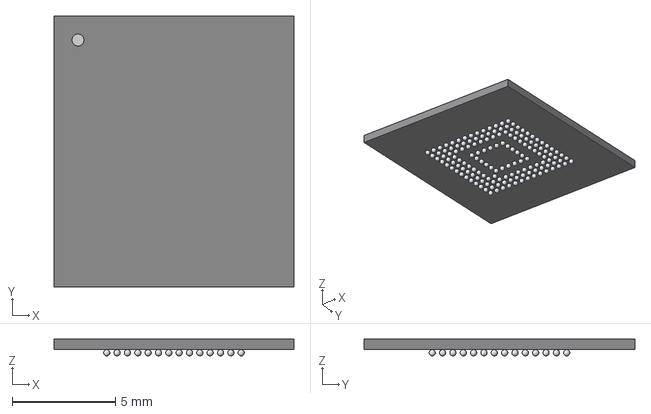
[picture p232: CAD file, 2026-10-06]
1.pcb/KiCad-library/EEZ-Kicad-libraries/3dmodels/BGA153_MX52LM_MAC.step
11.6 x 13.1 x 0.815 mm
