chili-chips-ba/openPCIE/1.pcb/KiCad-library/chili-chips-lib/3dmodels/B320-13-F.stp

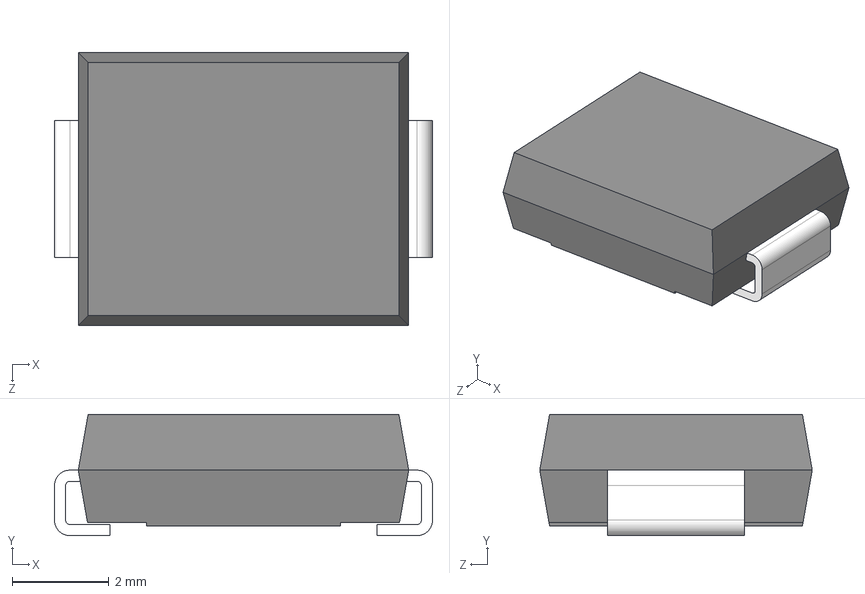
[picture p233: CAD file, 2026-09-09]
1.pcb/KiCad-library/chili-chips-lib/3dmodels/B320-13-F.stp
7.80 x 2.50 x 5.62 mm
SMBJ58CA-13-F_2
SMBJ58CA-13-F
SMBJ58CA-13-F_1
