chili-chips-ba/openPCIE/1.pcb/KiCad-library/EEZ-Kicad-libraries/3dmodels/R_1206_3216Metric.step

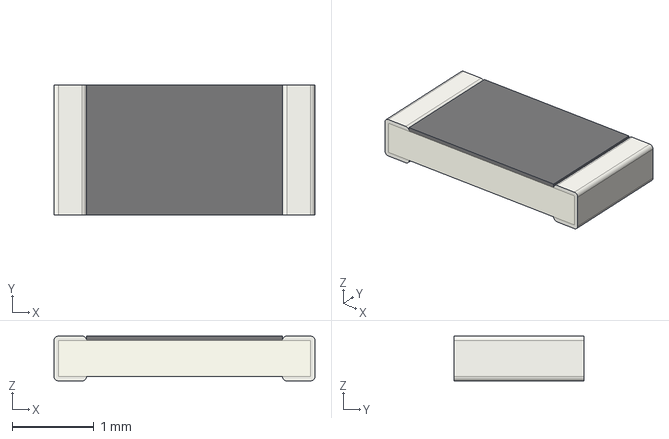
[picture p234: CAD file, 2026-10-06]
1.pcb/KiCad-library/EEZ-Kicad-libraries/3dmodels/R_1206_3216Metric.step
3.20 x 1.60 x 0.55 mm
