chili-chips-ba/openPCIE/1.pcb/KiCad-library/chili-chips-lib/3dmodels/MMICT5848-00-012.step

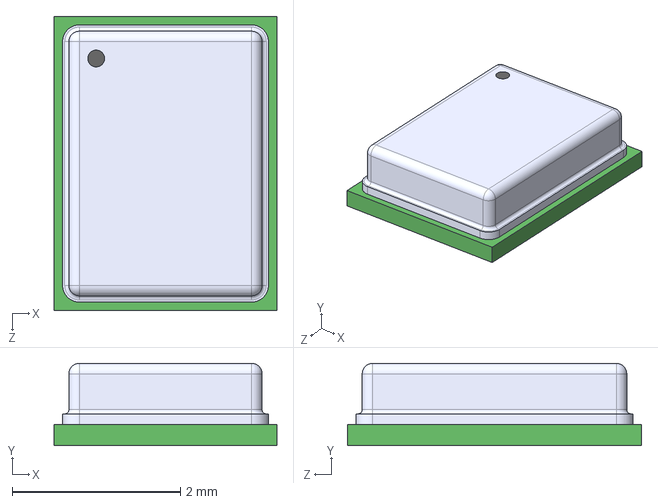
[picture p235: CAD file, 2026-09-09]
1.pcb/KiCad-library/chili-chips-lib/3dmodels/MMICT5848-00-012.step
2.65 x 0.98 x 3.50 mm
