chili-chips-ba/openPCIE/1.pcb/KiCad-library/EEZ-Kicad-libraries/3dmodels/TSSOP20_ST_MCH.step

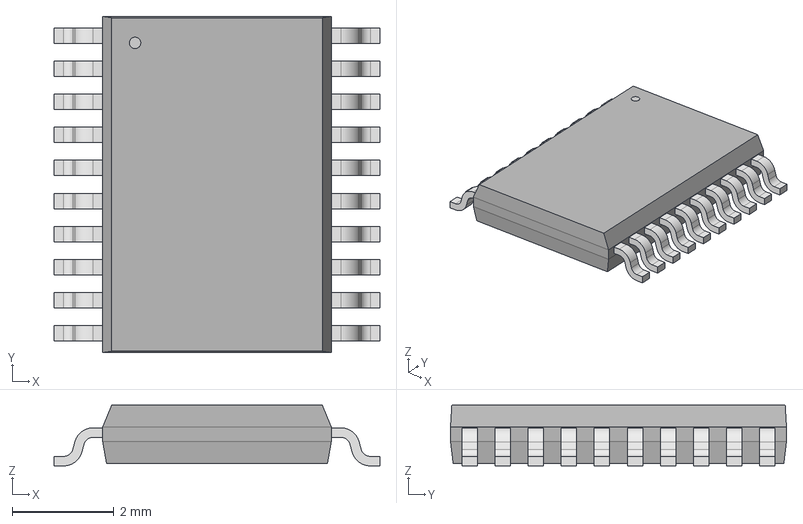
[picture p236: CAD file, 2026-10-06]
1.pcb/KiCad-library/EEZ-Kicad-libraries/3dmodels/TSSOP20_ST_MCH.step
6.40 x 6.60 x 1.20 mm
