chili-chips-ba/openPCIE/1.pcb/KiCad-library/EEZ-Kicad-libraries/3dmodels/TBP03R1-350-08BE.step

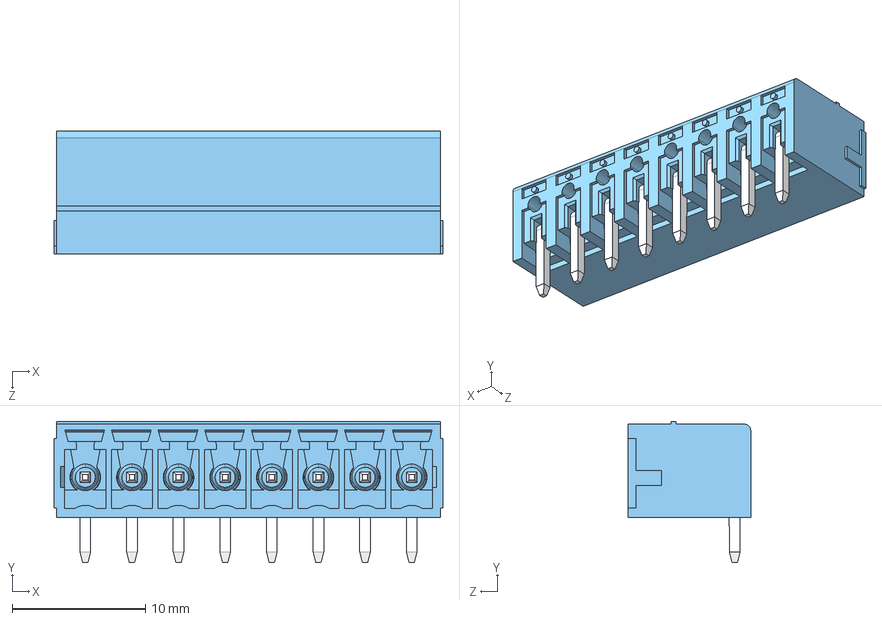
[picture p237: CAD file, 2026-10-06]
1.pcb/KiCad-library/EEZ-Kicad-libraries/3dmodels/TBP03R1-350-08BE.step
29.2 x 10.6 x 9.20 mm
