chili-chips-ba/openPCIE/1.pcb/KiCad-library/chili-chips-lib/3dmodels/B3B-PH-K-S--3DModel-STEP-56544.STEP

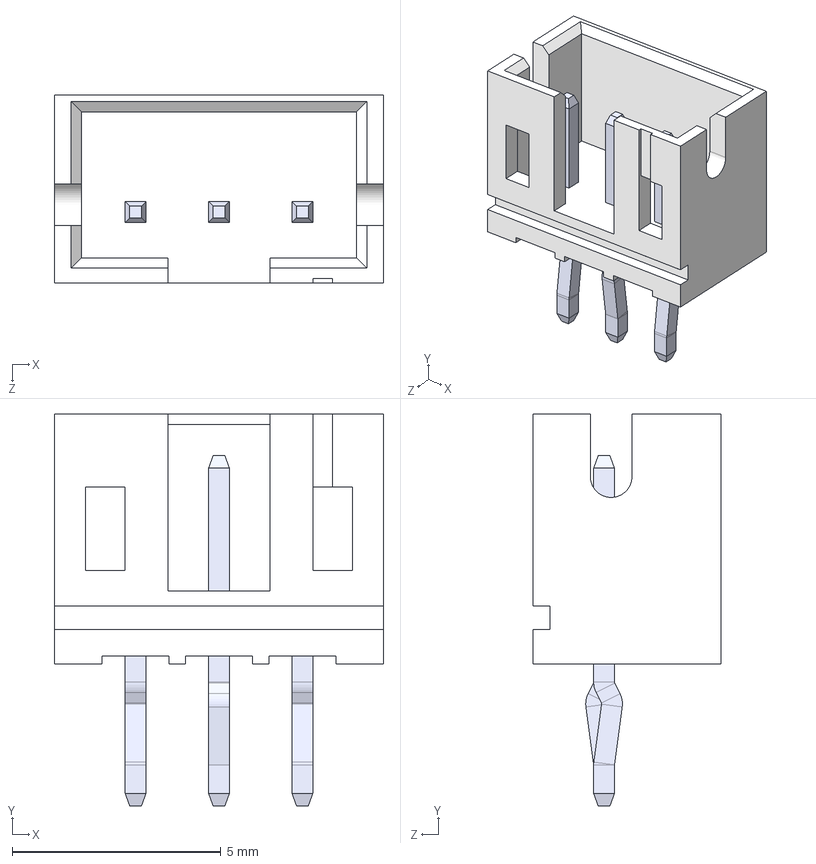
[picture p238: CAD file, 2026-09-09]
1.pcb/KiCad-library/chili-chips-lib/3dmodels/B3B-PH-K-S--3DModel-STEP-56544.STEP
7.90 x 9.40 x 4.50 mm
pin x 3
