chili-chips-ba/openPCIE/1.pcb/KiCad-library/EEZ-Kicad-libraries/3dmodels/PCAL9714HNMP.stp

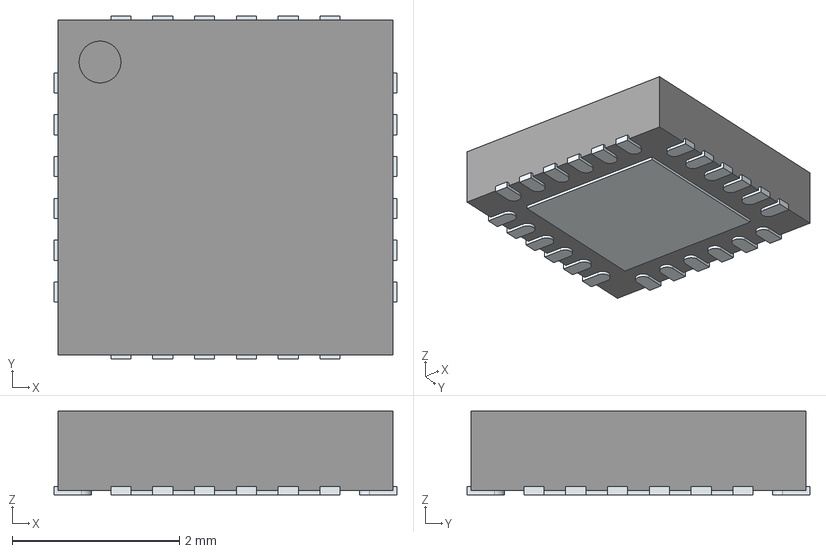
[picture p239: CAD file, 2026-10-06]
1.pcb/KiCad-library/EEZ-Kicad-libraries/3dmodels/PCAL9714HNMP.stp
4.10 x 4.10 x 1.00 mm
ThermalPin
PinsArrayLR
PinsArrayTB
