chili-chips-ba/openPCIE/1.pcb/KiCad-library/chili-chips-lib/3dmodels/CP-8-21_ADI.step

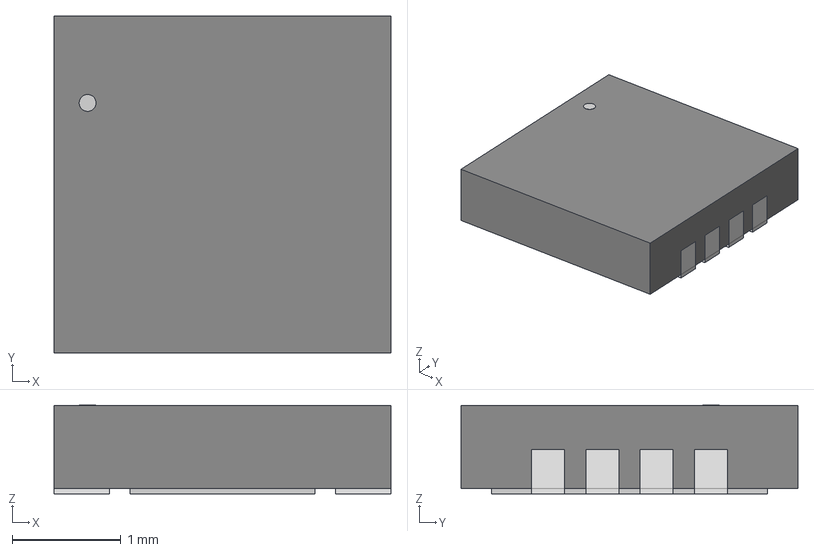
[picture p240: CAD file, 2026-09-09]
1.pcb/KiCad-library/chili-chips-lib/3dmodels/CP-8-21_ADI.step
3.10 x 3.10 x 0.815 mm
