chili-chips-ba/openPCIE/1.pcb/KiCad-library/chili-chips-lib/3dmodels/218-4LPSJ.stp

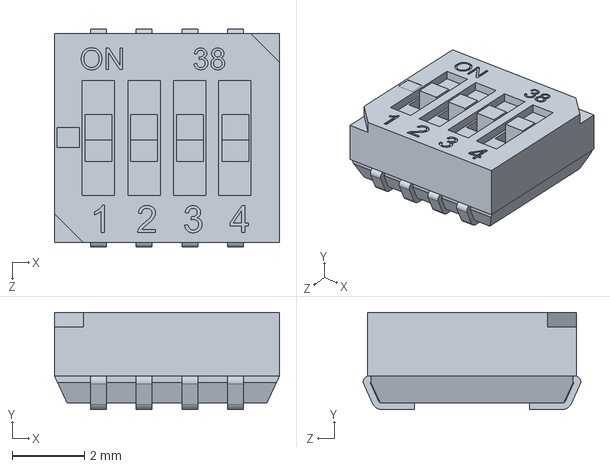
[picture p241: CAD file, 2026-09-09]
1.pcb/KiCad-library/chili-chips-lib/3dmodels/218-4LPSJ.stp
6.25 x 2.70 x 6.04 mm
