chili-chips-ba/openPCIE/1.pcb/KiCad-library/EEZ-Kicad-libraries/3dmodels/PPTC052LFBN-RC--3DModel-STEP-269445.STEP

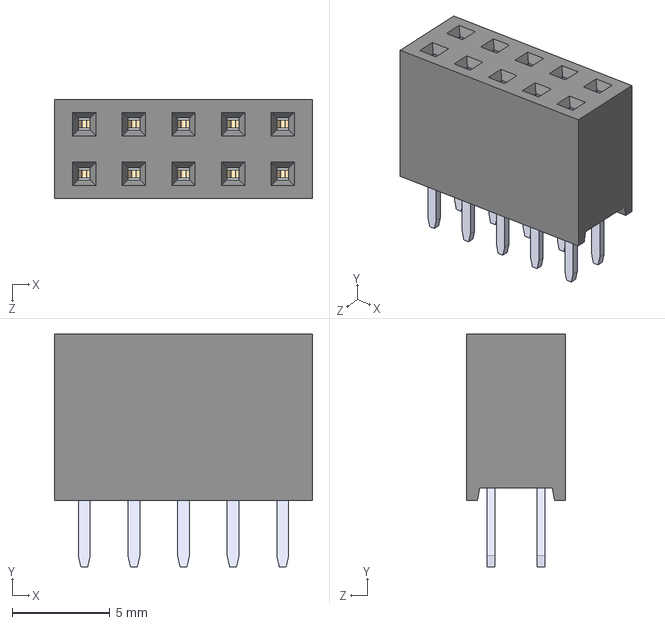
[picture p242: CAD file, 2026-10-06]
1.pcb/KiCad-library/EEZ-Kicad-libraries/3dmodels/PPTC052LFBN-RC--3DModel-STEP-269445.STEP
13.2 x 11.9 x 5.08 mm
2 row tin body_05
2 row tin pins x 5
