chili-chips-ba/openPCIE/1.pcb/KiCad-library/chili-chips-lib/3dmodels/5-1775444-3.step

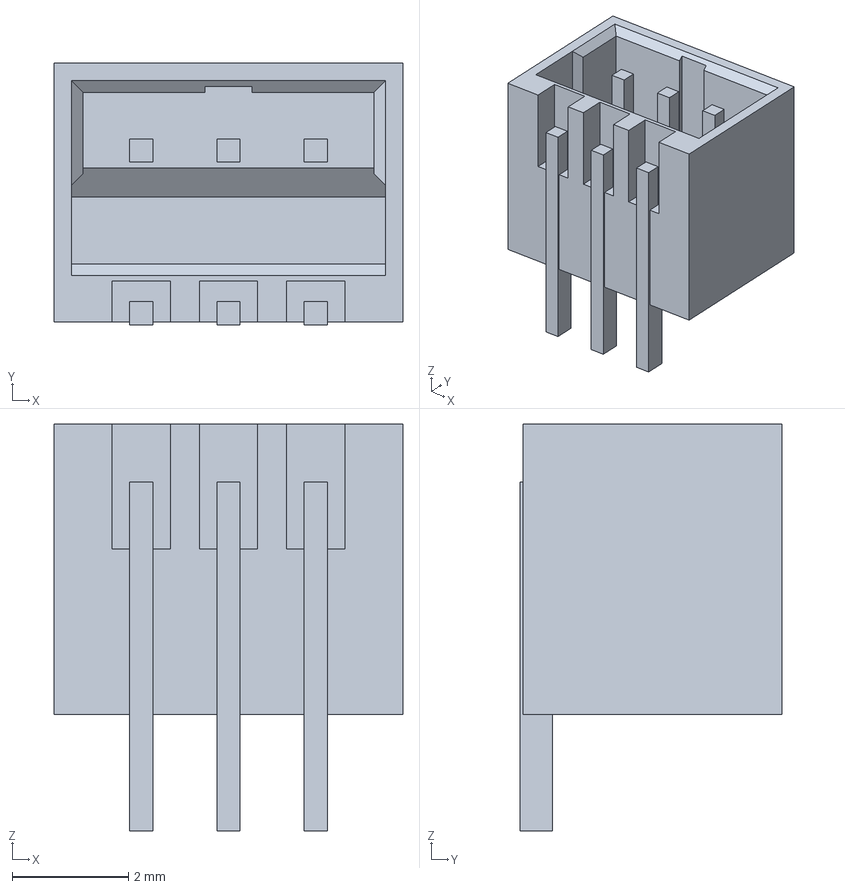
[picture p243: CAD file, 2026-09-09]
1.pcb/KiCad-library/chili-chips-lib/3dmodels/5-1775444-3.step
6.00 x 4.50 x 7.00 mm
