chili-chips-ba/openPCIE/1.pcb/KiCad-library/EEZ-Kicad-libraries/3dmodels/OKW_00010463_A1024068.step

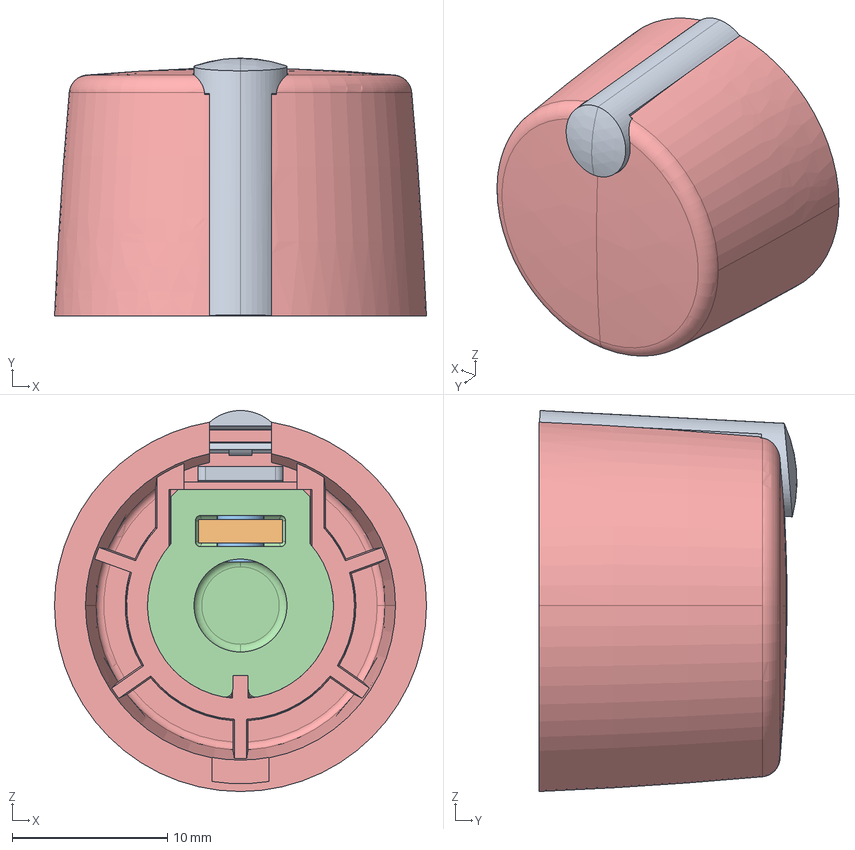
[picture p244: CAD file, 2026-10-06]
1.pcb/KiCad-library/EEZ-Kicad-libraries/3dmodels/OKW_00010463_A1024068.step
24.0 x 16.6 x 24.6 mm
00007427 - Pin_Default
00010457 - Vierkantmutter M3, DIN 562-04, verzinkt
00010241 - Gewindestift m Innensechskant M3 x 4mm
00007417 - Adapter ø6mm_Default
00007421 - Knopfkörper ø24_Default
