chili-chips-ba/openPCIE/1.pcb/KiCad-library/chili-chips-lib/3dmodels/APA2107.STEP

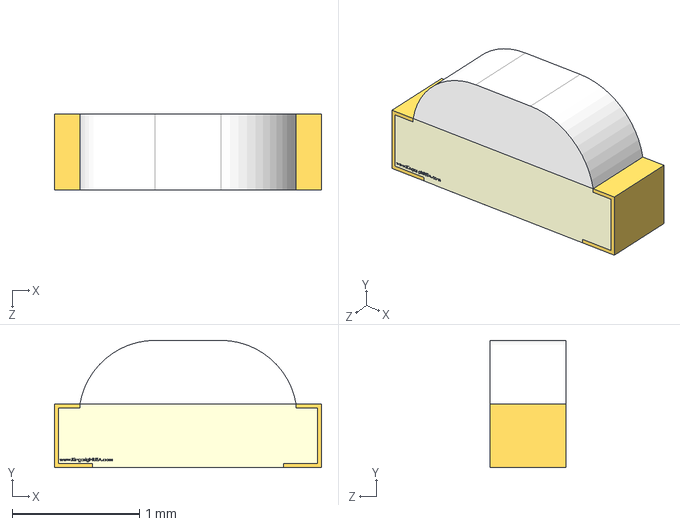
[picture p245: CAD file, 2026-09-09]
1.pcb/KiCad-library/chili-chips-lib/3dmodels/APA2107.STEP
2.10 x 1.00 x 0.6 mm
