chili-chips-ba/openPCIE/1.pcb/KiCad-library/chili-chips-lib/3dmodels/PTS645SK43SMTR92LFS.stp

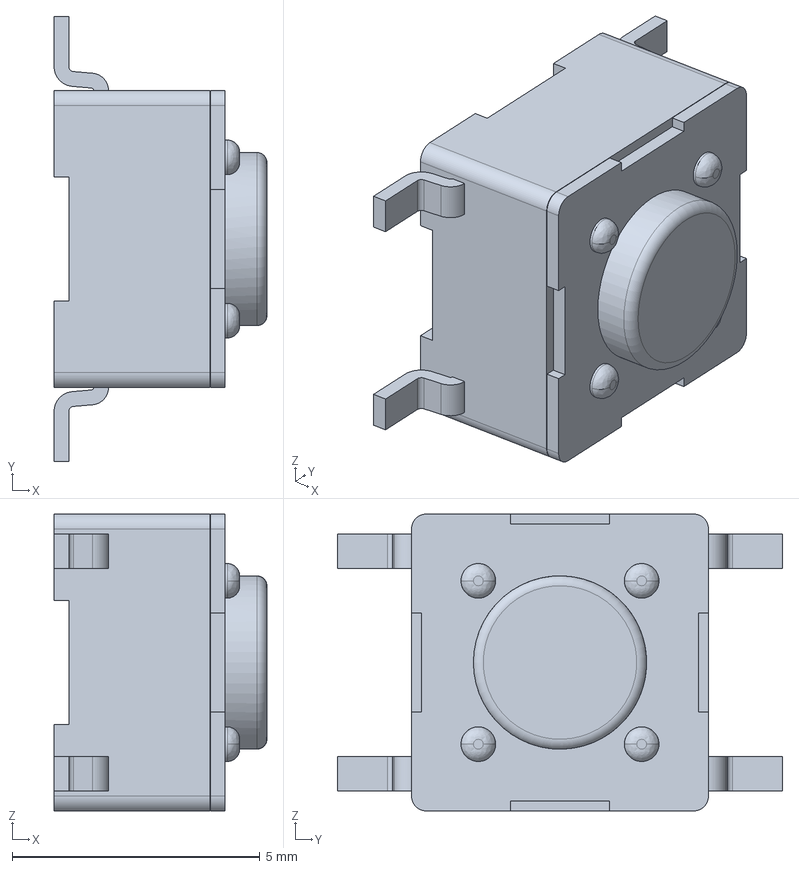
[picture p246: CAD file, 2026-09-09]
1.pcb/KiCad-library/chili-chips-lib/3dmodels/PTS645SK43SMTR92LFS.stp
4.30 x 9.00 x 6.00 mm
