chili-chips-ba/openPCIE/1.pcb/KiCad-library/EEZ-Kicad-libraries/3dmodels/39-30-1020.stp

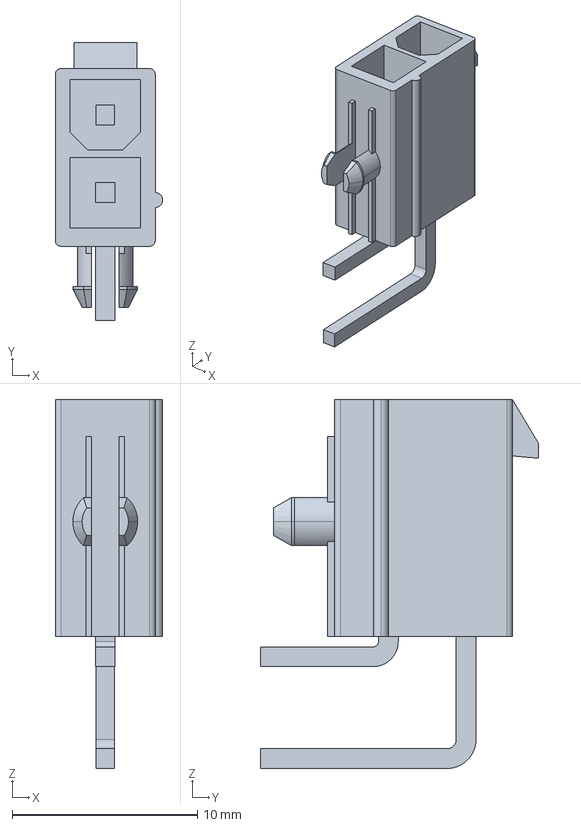
[picture p247: CAD file, 2026-10-06]
1.pcb/KiCad-library/EEZ-Kicad-libraries/3dmodels/39-30-1020.stp
5.80 x 15.0 x 19.9 mm
