chili-chips-ba/openPCIE/1.pcb/KiCad-library/chili-chips-lib/3dmodels/DSF0006A.stp

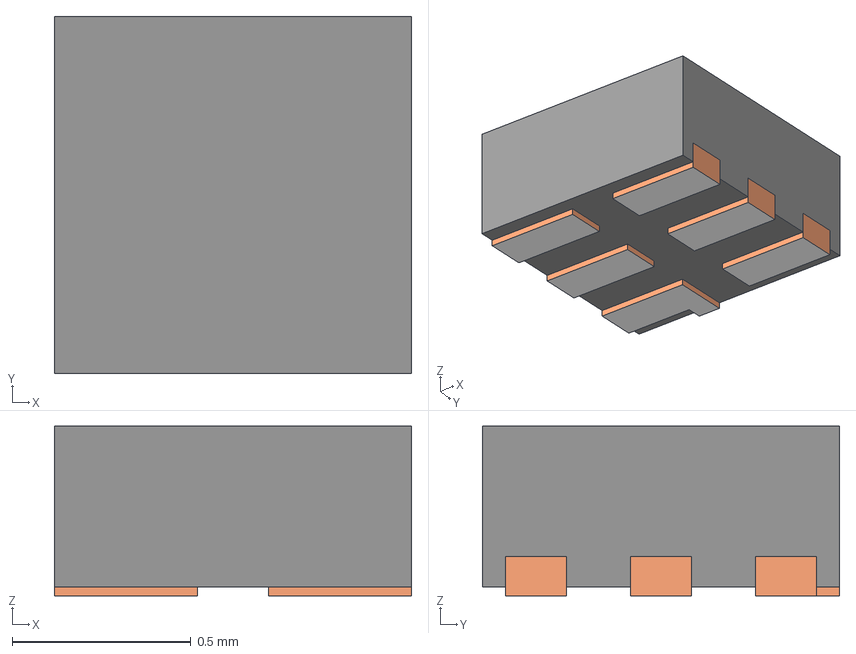
[picture p248: CAD file, 2026-09-09]
1.pcb/KiCad-library/chili-chips-lib/3dmodels/DSF0006A.stp
1.00 x 1.00 x 0.475 mm
BODY-SON
FRAME-DSF0006A
