chili-chips-ba/openPCIE/1.pcb/KiCad-library/chili-chips-lib/3dmodels/VCB0010A.stp

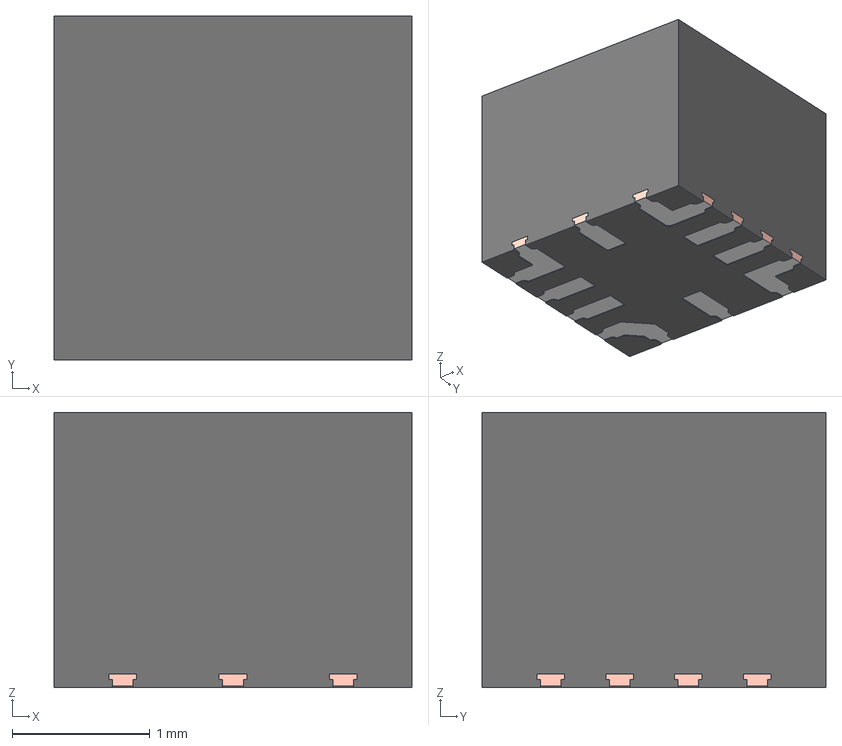
[picture p249: CAD file, 2026-09-09]
1.pcb/KiCad-library/chili-chips-lib/3dmodels/VCB0010A.stp
2.60 x 2.50 x 2.00 mm
VCB0010A_FRAME
VCB0010A_BODY
VCB0010A_PIN1_AREA
