chili-chips-ba/openPCIE/1.pcb/KiCad-library/EEZ-Kicad-libraries/3dmodels/EE2-5TNU-L.stp

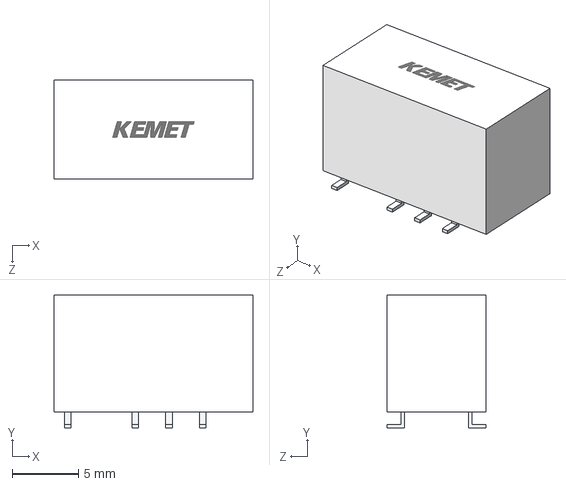
[picture p250: CAD file, 2026-10-06]
1.pcb/KiCad-library/EEZ-Kicad-libraries/3dmodels/EE2-5TNU-L.stp
15.0 x 10.0 x 7.50 mm
