chili-chips-ba/openPCIE/1.pcb/KiCad-library/chili-chips-lib/3dmodels/IHLP1212BZER3R3M11.step

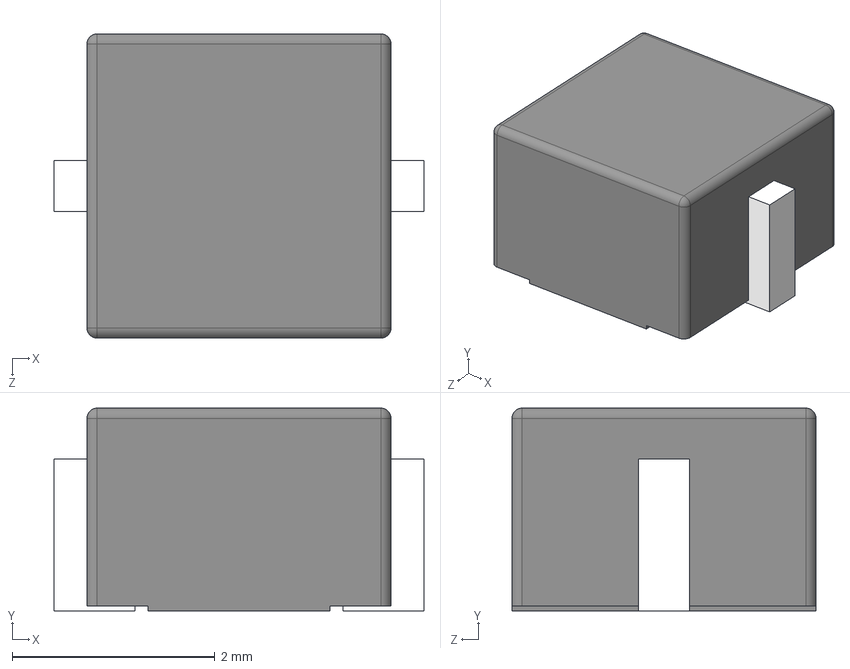
[picture p251: CAD file, 2026-09-09]
1.pcb/KiCad-library/chili-chips-lib/3dmodels/IHLP1212BZER3R3M11.step
3.65 x 2.00 x 3.00 mm
