chili-chips-ba/openPCIE/1.pcb/KiCad-library/EEZ-Kicad-libraries/3dmodels/WE-MAIA-4020 (rev1).stp

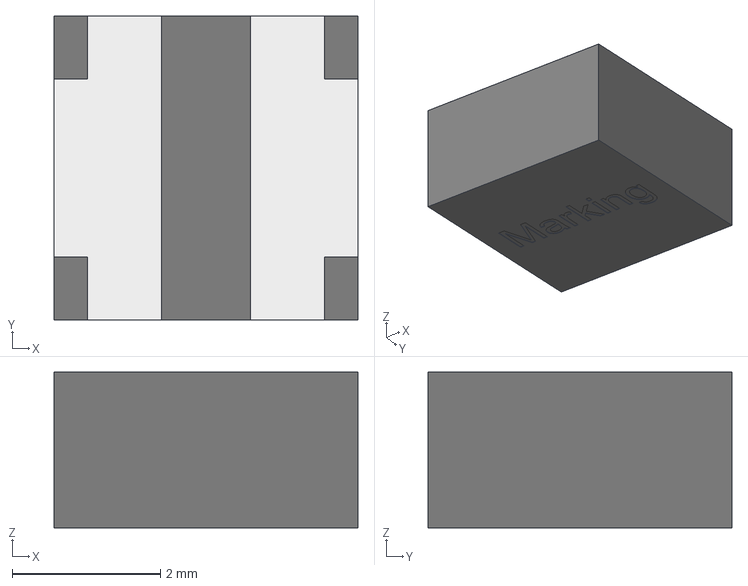
[picture p252: CAD file, 2026-10-06]
1.pcb/KiCad-library/EEZ-Kicad-libraries/3dmodels/WE-MAIA-4020 (rev1).stp
4.10 x 4.10 x 2.10 mm
body_SSMC_403020
land_pattern_SSMC_403020 x 2
