chili-chips-ba/openPCIE/1.pcb/KiCad-library/chili-chips-lib/3dmodels/DTR0012A.stp

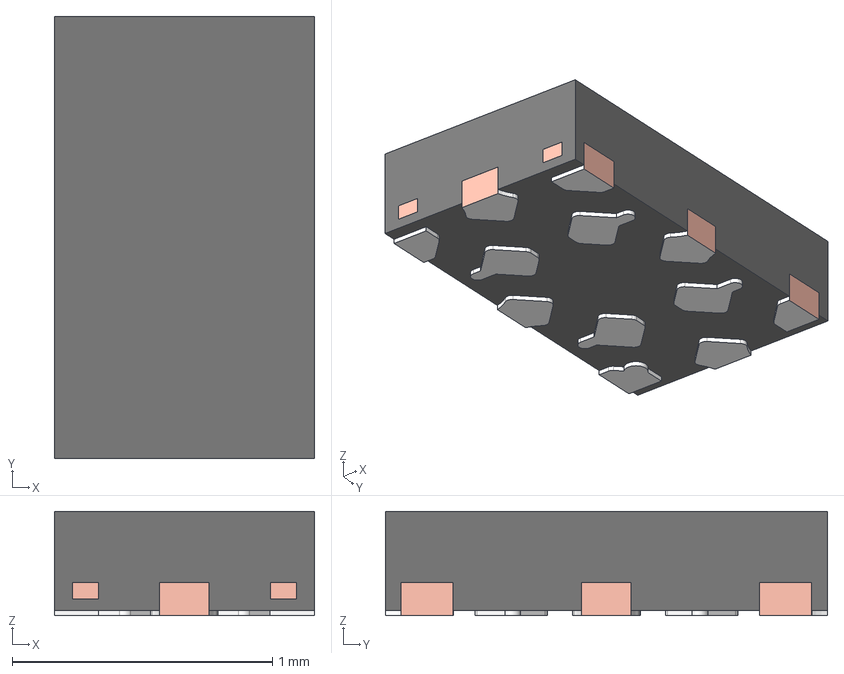
[picture p253: CAD file, 2026-09-09]
1.pcb/KiCad-library/chili-chips-lib/3dmodels/DTR0012A.stp
1.00 x 1.70 x 0.4 mm
FRAME
MOLD
