chili-chips-ba/openPCIE/1.pcb/KiCad-library/EEZ-Kicad-libraries/3dmodels/TPS3851G18SDRBT.step

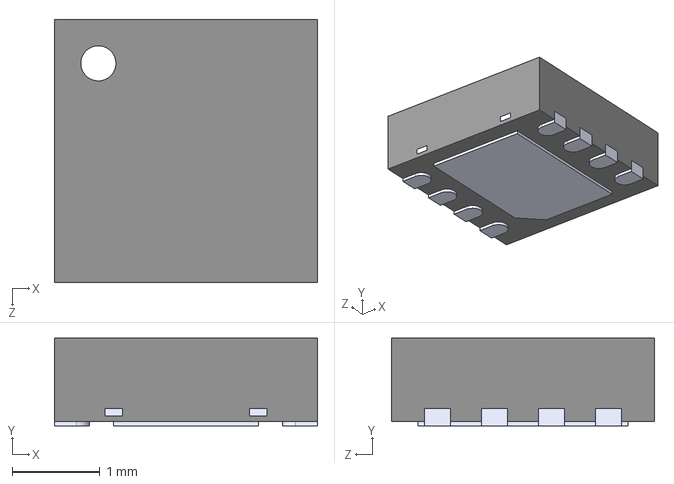
[picture p255: CAD file, 2026-10-06]
1.pcb/KiCad-library/EEZ-Kicad-libraries/3dmodels/TPS3851G18SDRBT.step
3.00 x 1.00 x 3.00 mm
