chili-chips-ba/openPCIE/1.pcb/KiCad-library/chili-chips-lib/3dmodels/TSOP-6_318G-02_ONS.step

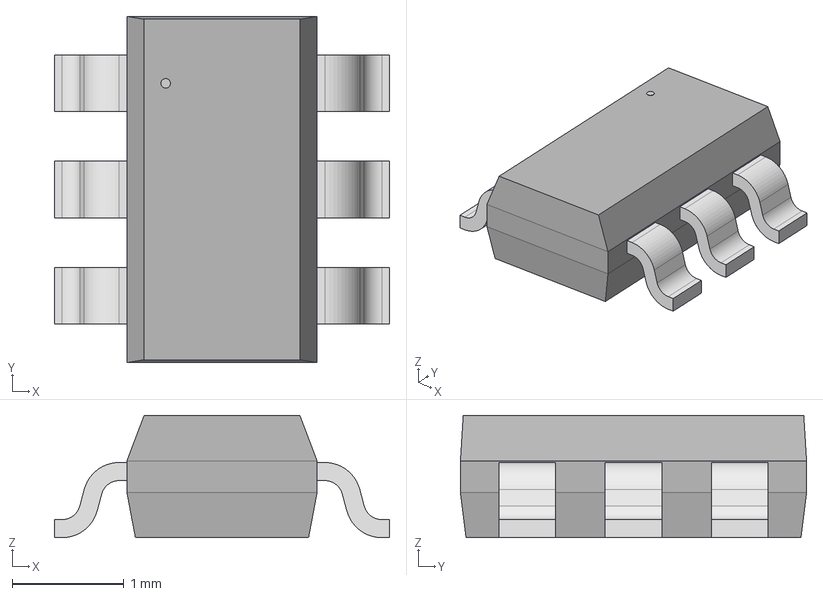
[picture p256: CAD file, 2026-09-09]
1.pcb/KiCad-library/chili-chips-lib/3dmodels/TSOP-6_318G-02_ONS.step
3.00 x 3.10 x 1.09 mm
