chili-chips-ba/openPCIE/1.pcb/KiCad-library/EEZ-Kicad-libraries/3dmodels/PinHeader_1x02_P2.54mm_Vertical.step

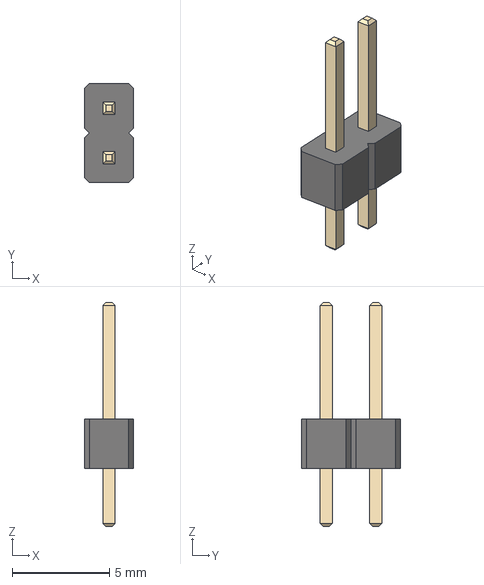
[picture p257: CAD file, 2026-10-06]
1.pcb/KiCad-library/EEZ-Kicad-libraries/3dmodels/PinHeader_1x02_P2.54mm_Vertical.step
2.54 x 5.08 x 11.5 mm
