chili-chips-ba/openPCIE/1.pcb/KiCad-library/chili-chips-lib/3dmodels/LMK1C1104DQFR--3DModel-STEP-56544.STEP

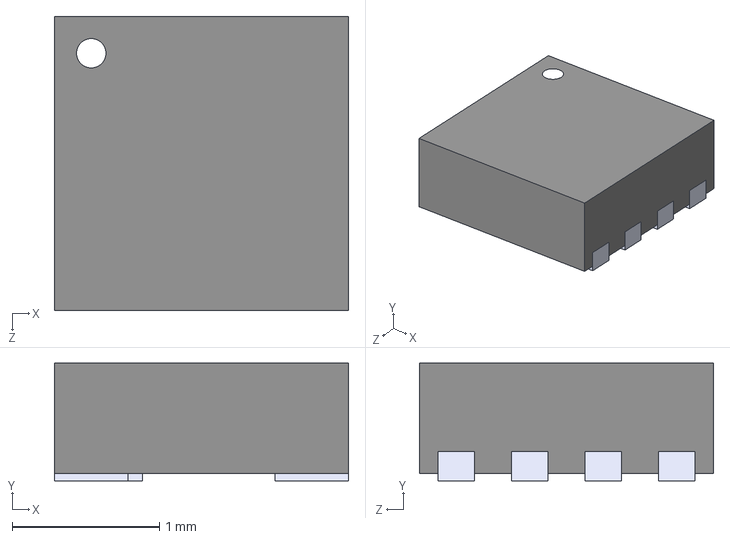
[picture p258: CAD file, 2026-09-09]
1.pcb/KiCad-library/chili-chips-lib/3dmodels/LMK1C1104DQFR--3DModel-STEP-56544.STEP
2.00 x 0.8 x 2.00 mm
