chili-chips-ba/openPCIE/1.pcb/KiCad-library/EEZ-Kicad-libraries/3dmodels/VFBGA63_9X11_MAC.step

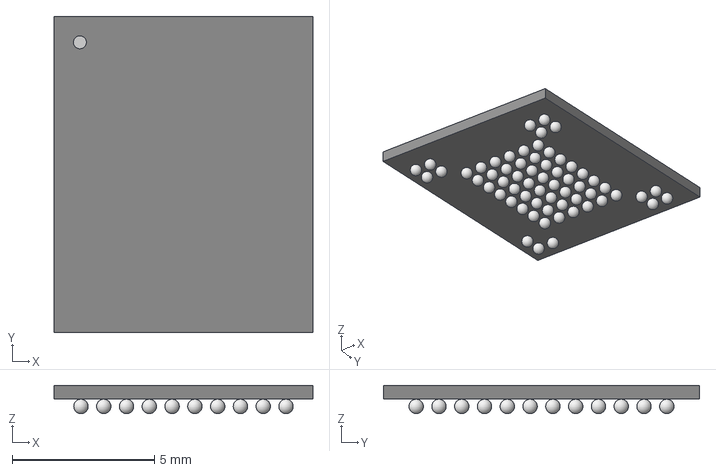
[picture p259: CAD file, 2026-10-06]
1.pcb/KiCad-library/EEZ-Kicad-libraries/3dmodels/VFBGA63_9X11_MAC.step
9.09 x 11.1 x 0.993 mm
