chili-chips-ba/openPCIE/1.pcb/KiCad-library/chili-chips-lib/3dmodels/FBGA225_EFI.step

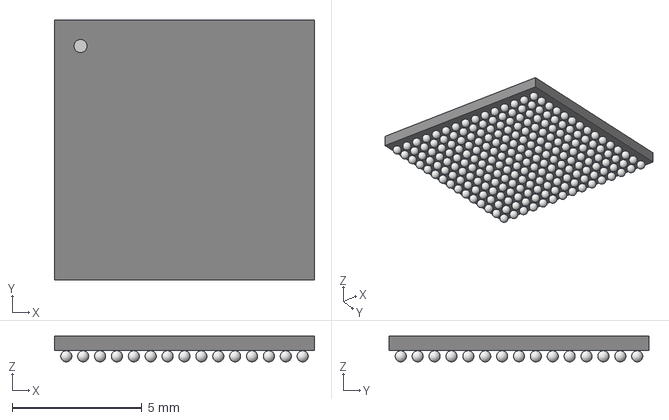
[picture p260: CAD file, 2026-09-09]
1.pcb/KiCad-library/chili-chips-lib/3dmodels/FBGA225_EFI.step
10.0 x 10.0 x 0.993 mm
