chili-chips-ba/openPCIE/1.pcb/KiCad-library/EEZ-Kicad-libraries/3dmodels/R46KF247050N0K.step

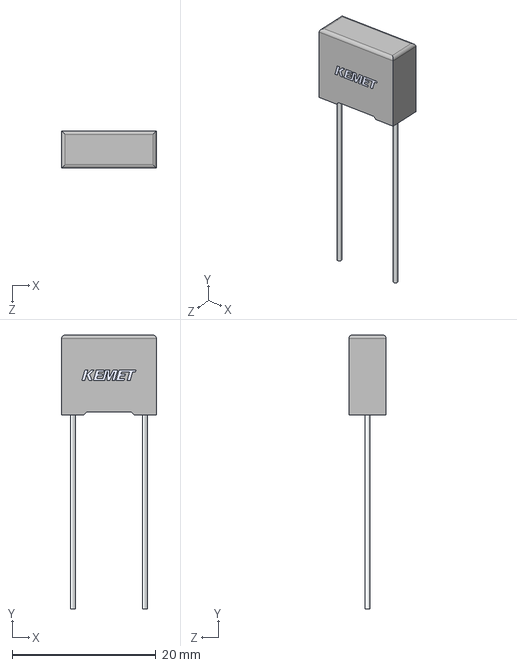
[picture p261: CAD file, 2026-10-06]
1.pcb/KiCad-library/EEZ-Kicad-libraries/3dmodels/R46KF247050N0K.step
13.2 x 38.1 x 5.20 mm
