chili-chips-ba/openPCIE/1.pcb/KiCad-library/chili-chips-lib/3dmodels/XDFN6_1P25X1P25_ONS.step

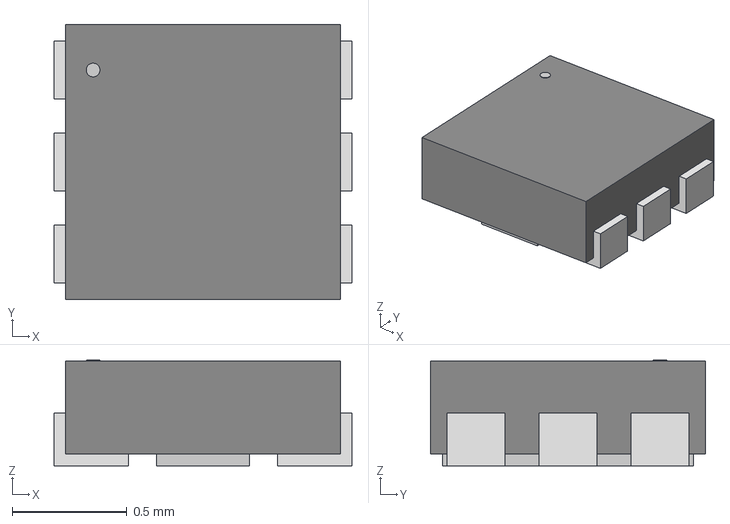
[picture p262: CAD file, 2026-09-09]
1.pcb/KiCad-library/chili-chips-lib/3dmodels/XDFN6_1P25X1P25_ONS.step
1.30 x 1.19 x 0.46 mm
