chili-chips-ba/openPCIE/1.pcb/KiCad-library/chili-chips-lib/3dmodels/DSBGA30_YBG_TEX.step

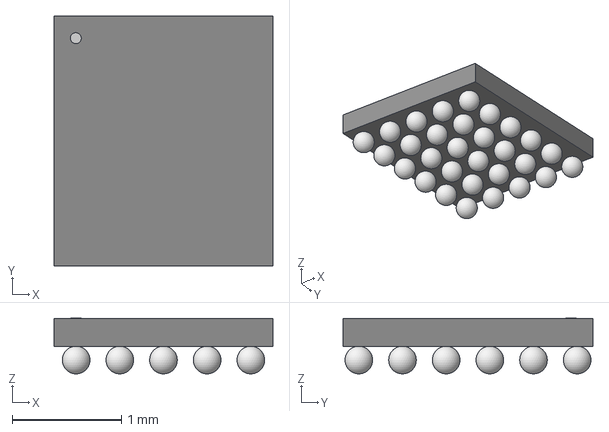
[picture p263: CAD file, 2026-09-09]
1.pcb/KiCad-library/chili-chips-lib/3dmodels/DSBGA30_YBG_TEX.step
2.01 x 2.29 x 0.511 mm
