chili-chips-ba/openPCIE/1.pcb/KiCad-library/EEZ-Kicad-libraries/3dmodels/TSSOP-16.STEP

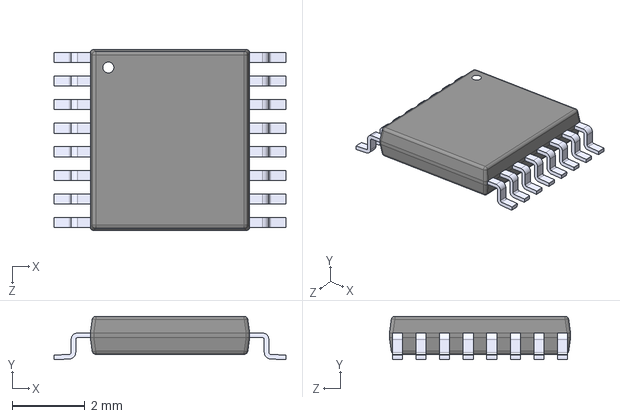
[picture p264: CAD file, 2026-10-06]
1.pcb/KiCad-library/EEZ-Kicad-libraries/3dmodels/TSSOP-16.STEP
6.40 x 1.20 x 5.00 mm
