chili-chips-ba/openPCIE/1.pcb/KiCad-library/chili-chips-lib/3dmodels/NXB0106BQX.step

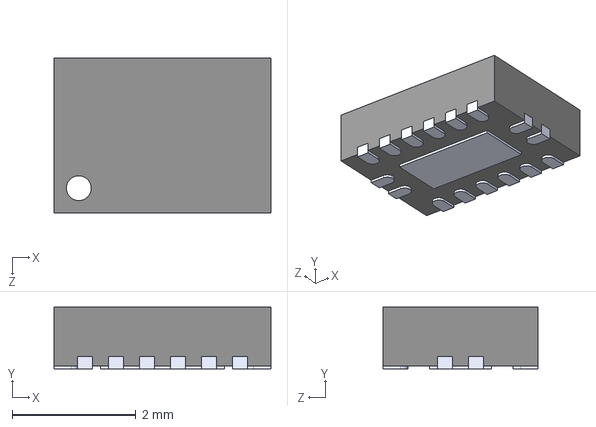
[picture p265: CAD file, 2026-09-09]
1.pcb/KiCad-library/chili-chips-lib/3dmodels/NXB0106BQX.step
3.50 x 1.00 x 2.50 mm
