chili-chips-ba/openPCIE/1.pcb/KiCad-library/EEZ-Kicad-libraries/3dmodels/PTVS22VP1UP_115.step

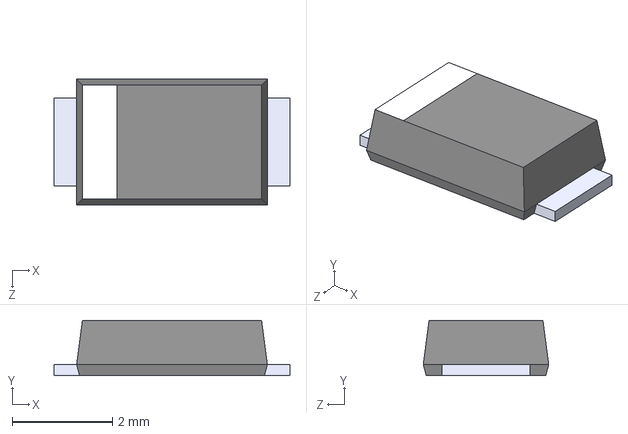
[picture p266: CAD file, 2026-10-06]
1.pcb/KiCad-library/EEZ-Kicad-libraries/3dmodels/PTVS22VP1UP_115.step
4.70 x 1.10 x 2.50 mm
