chili-chips-ba/openPCIE/1.pcb/KiCad-library/chili-chips-lib/3dmodels/SON50P160X160X60-6N.step

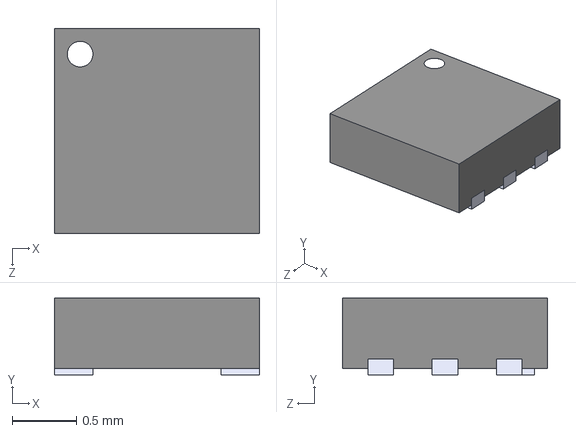
[picture p267: CAD file, 2026-09-09]
1.pcb/KiCad-library/chili-chips-lib/3dmodels/SON50P160X160X60-6N.step
1.60 x 0.6 x 1.60 mm
