chili-chips-ba/openPCIE/1.pcb/KiCad-library/EEZ-Kicad-libraries/3dmodels/DK1A-L2-5V-F.step

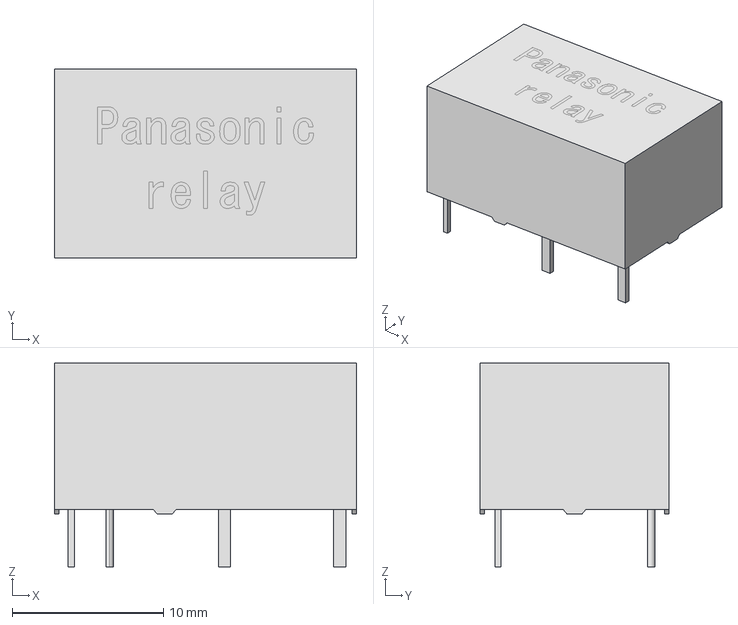
[picture p268: CAD file, 2026-10-06]
1.pcb/KiCad-library/EEZ-Kicad-libraries/3dmodels/DK1A-L2-5V-F.step
20.0 x 12.5 x 13.5 mm
