chili-chips-ba/openPCIE/1.pcb/KiCad-library/chili-chips-lib/3dmodels/S2B-PH-K-S_LF__SN_.step

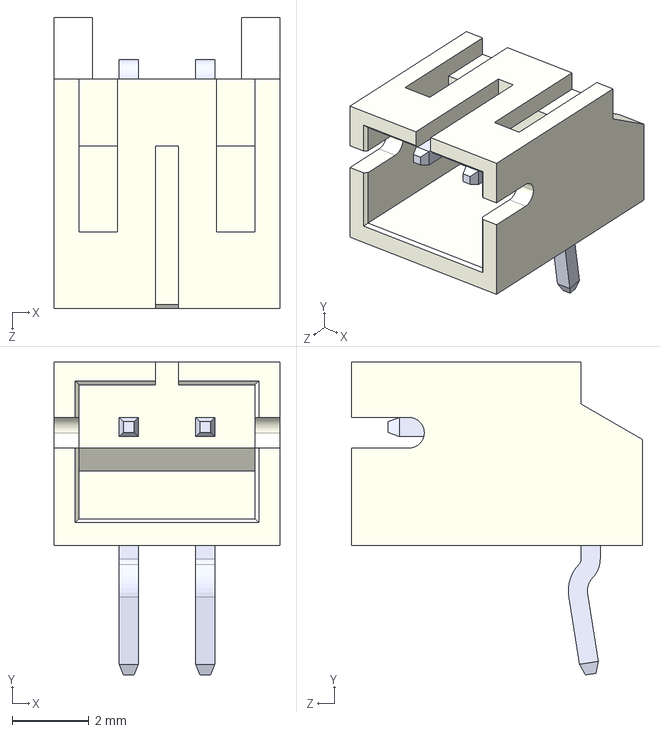
[picture p269: CAD file, 2026-09-09]
1.pcb/KiCad-library/chili-chips-lib/3dmodels/S2B-PH-K-S_LF__SN_.step
5.90 x 8.18 x 7.60 mm
