chili-chips-ba/openPCIE/1.pcb/KiCad-library/EEZ-Kicad-libraries/3dmodels/pf0030-pc.stp

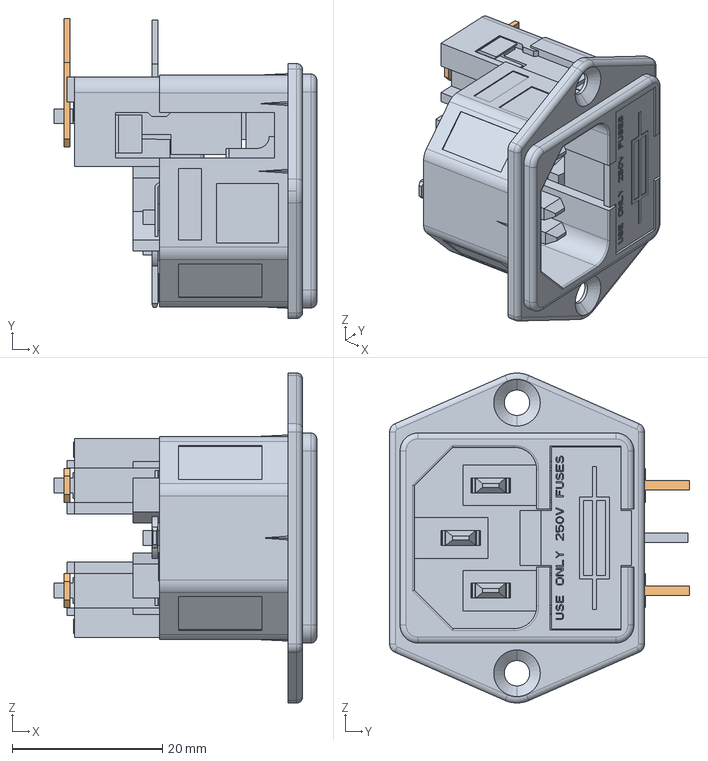
[picture p270: CAD file, 2026-10-06]
1.pcb/KiCad-library/EEZ-Kicad-libraries/3dmodels/pf0030-pc.stp
35.0 x 39.9 x 43.9 mm
