chili-chips-ba/openPCIE/1.pcb/KiCad-library/chili-chips-lib/3dmodels/KEYSTONE_5000.stp

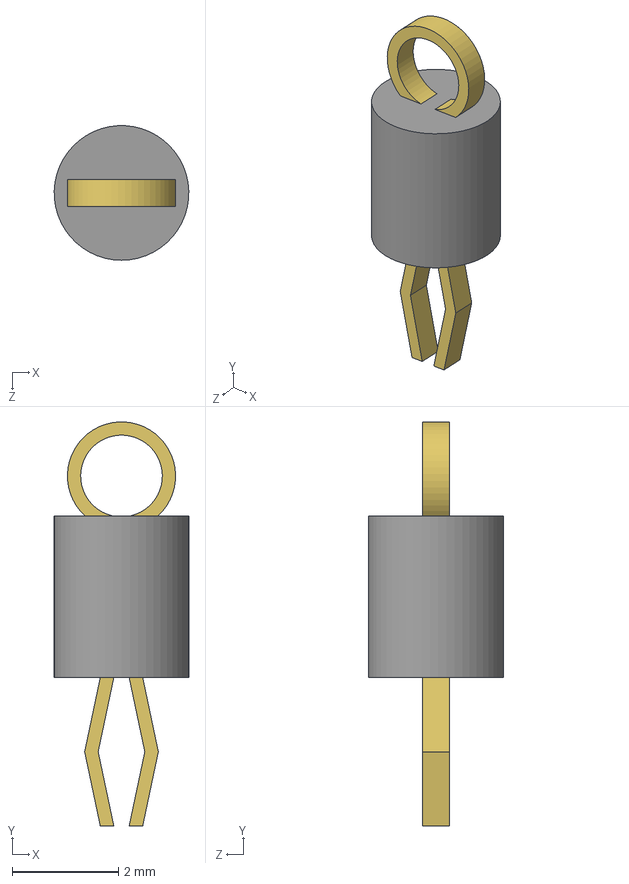
[picture p271: CAD file, 2026-09-09]
1.pcb/KiCad-library/chili-chips-lib/3dmodels/KEYSTONE_5000.stp
2.54 x 7.62 x 2.54 mm
