chili-chips-ba/openPCIE/1.pcb/KiCad-library/EEZ-Kicad-libraries/3dmodels/IND_XAL5020_COC.step

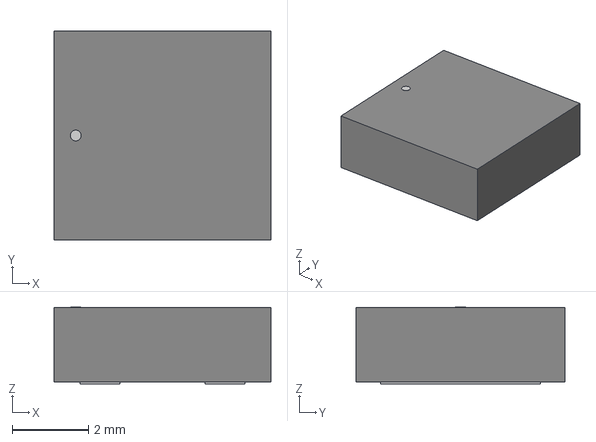
[picture p272: CAD file, 2026-10-06]
1.pcb/KiCad-library/EEZ-Kicad-libraries/3dmodels/IND_XAL5020_COC.step
5.69 x 5.49 x 2.01 mm
