chili-chips-ba/openPCIE/1.pcb/KiCad-library/chili-chips-lib/3dmodels/EMI8041MUTAG.stp

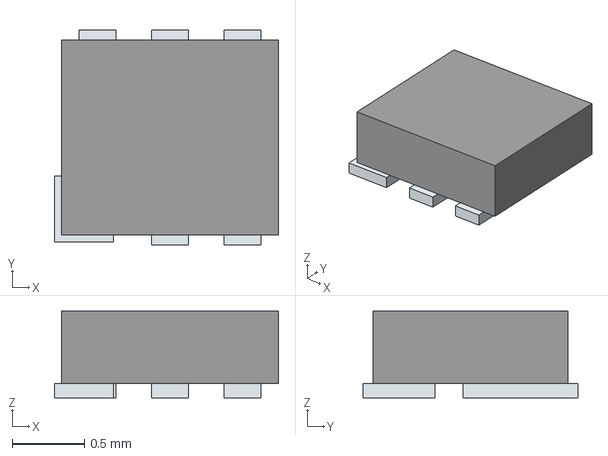
[picture p273: CAD file, 2026-09-09]
1.pcb/KiCad-library/chili-chips-lib/3dmodels/EMI8041MUTAG.stp
1.55 x 1.49 x 0.6 mm
Pins
