chili-chips-ba/openPCIE/1.pcb/KiCad-library/EEZ-Kicad-libraries/3dmodels/3214W-1-104E.step

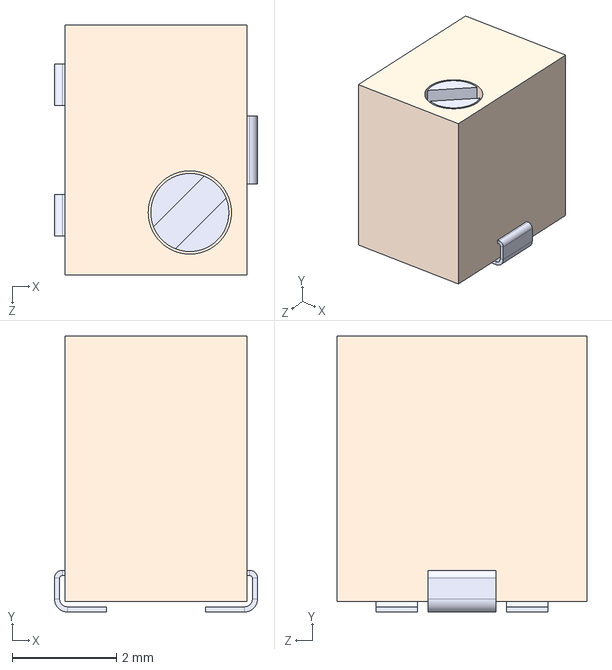
[picture p274: CAD file, 2026-10-06]
1.pcb/KiCad-library/EEZ-Kicad-libraries/3dmodels/3214W-1-104E.step
3.90 x 5.30 x 4.80 mm
