chili-chips-ba/openPCIE/1.pcb/KiCad-library/chili-chips-lib/3dmodels/XDFN10_2P5X1P3_ONS.step

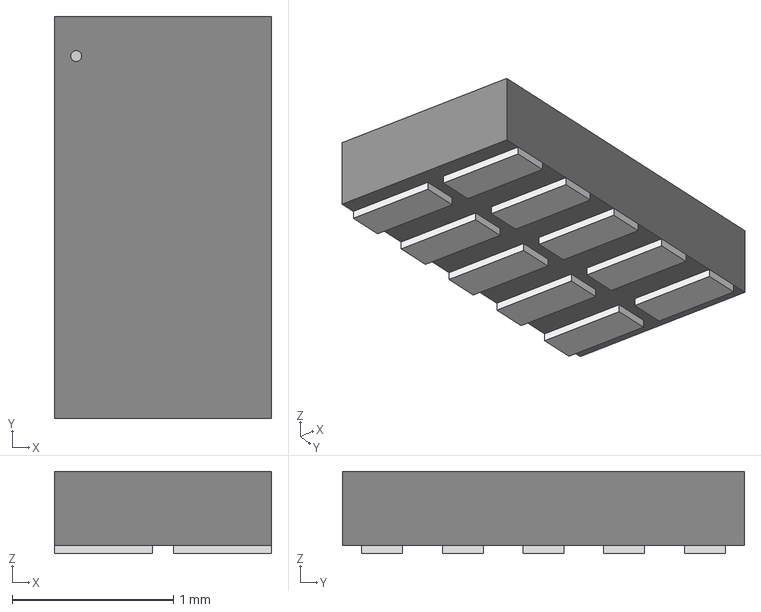
[picture p275: CAD file, 2026-09-09]
1.pcb/KiCad-library/chili-chips-lib/3dmodels/XDFN10_2P5X1P3_ONS.step
1.35 x 2.49 x 0.511 mm
