chili-chips-ba/openPCIE/1.pcb/KiCad-library/EEZ-Kicad-libraries/3dmodels/G6DN-1A-CF_DCXX.stp

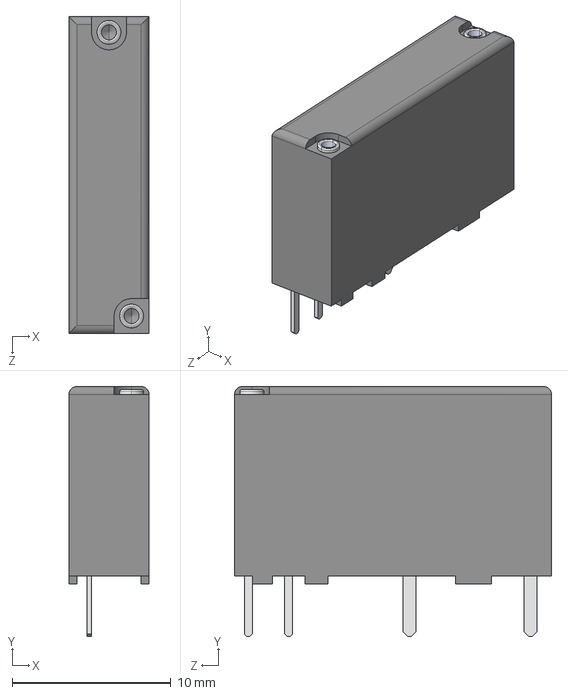
[picture p276: CAD file, 2026-10-06]
1.pcb/KiCad-library/EEZ-Kicad-libraries/3dmodels/G6DN-1A-CF_DCXX.stp
5.05 x 15.8 x 20.0 mm
