chili-chips-ba/openPCIE/1.pcb/KiCad-library/chili-chips-lib/3dmodels/SOIC_208MIL_WIN.step

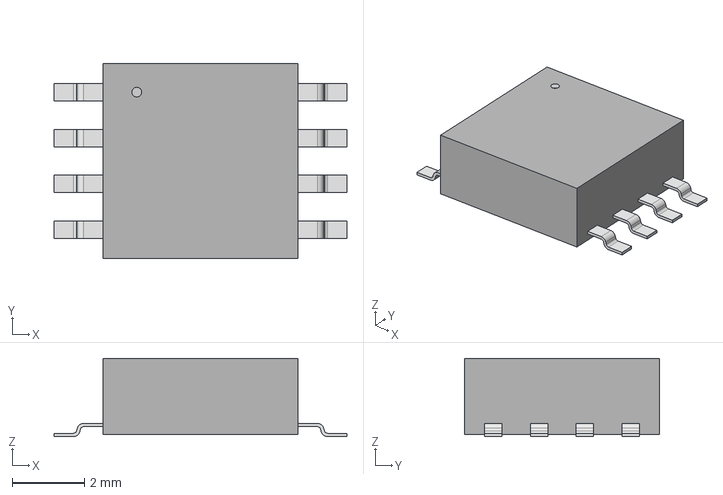
[picture p277: CAD file, 2026-09-09]
1.pcb/KiCad-library/chili-chips-lib/3dmodels/SOIC_208MIL_WIN.step
8.10 x 5.38 x 2.16 mm
