chili-chips-ba/openPCIE/1.pcb/KiCad-library/EEZ-Kicad-libraries/3dmodels/IRFP250N.step

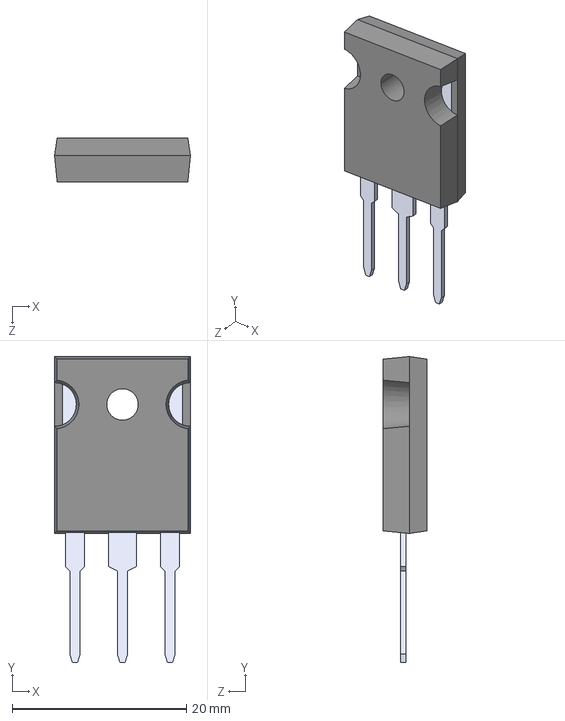
[picture p278: CAD file, 2026-10-06]
1.pcb/KiCad-library/EEZ-Kicad-libraries/3dmodels/IRFP250N.step
15.6 x 35.1 x 5.00 mm
