chili-chips-ba/openPCIE/1.pcb/2.test-results/2025-12-17/test (5).jpg

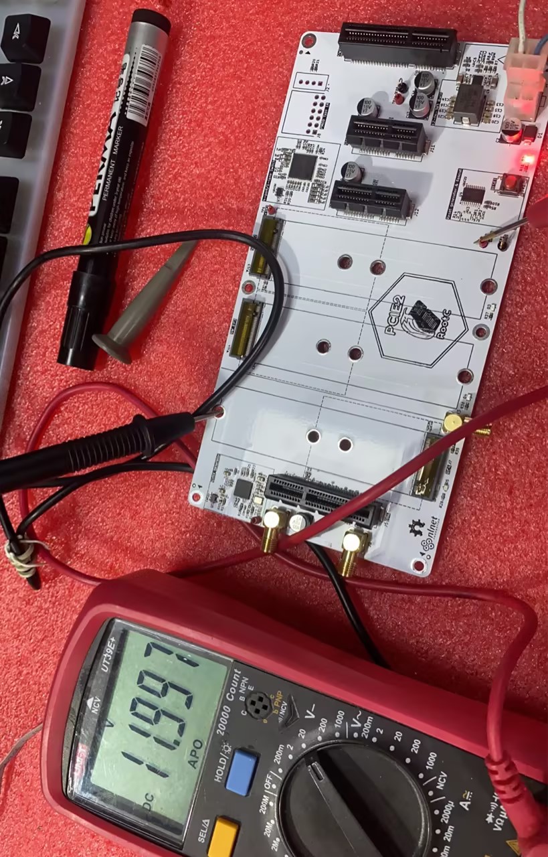
1.pcb/2.test-results/2025-12-17/test (5).jpg
