chili-chips-ba/openPCIE/1.pcb/2.test-results/2025-12-17/test (10).jpg

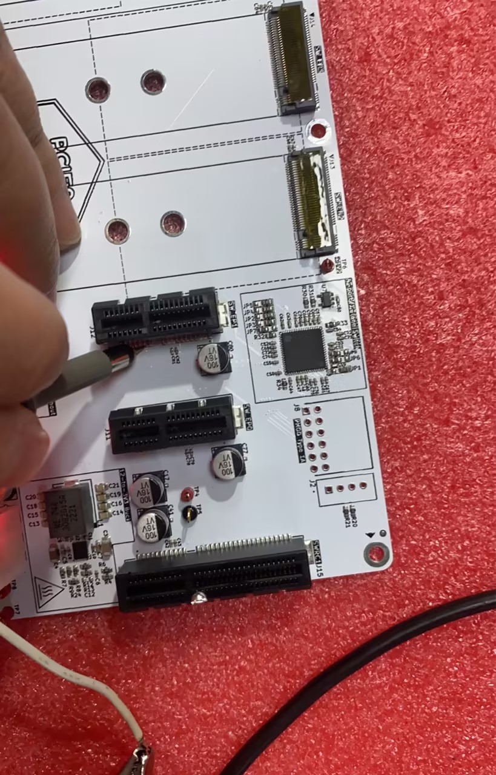
1.pcb/2.test-results/2025-12-17/test (10).jpg
