chili-chips-ba/openPCIE/1.pcb/openpci2-backplane/openpci2-backplane.pdf

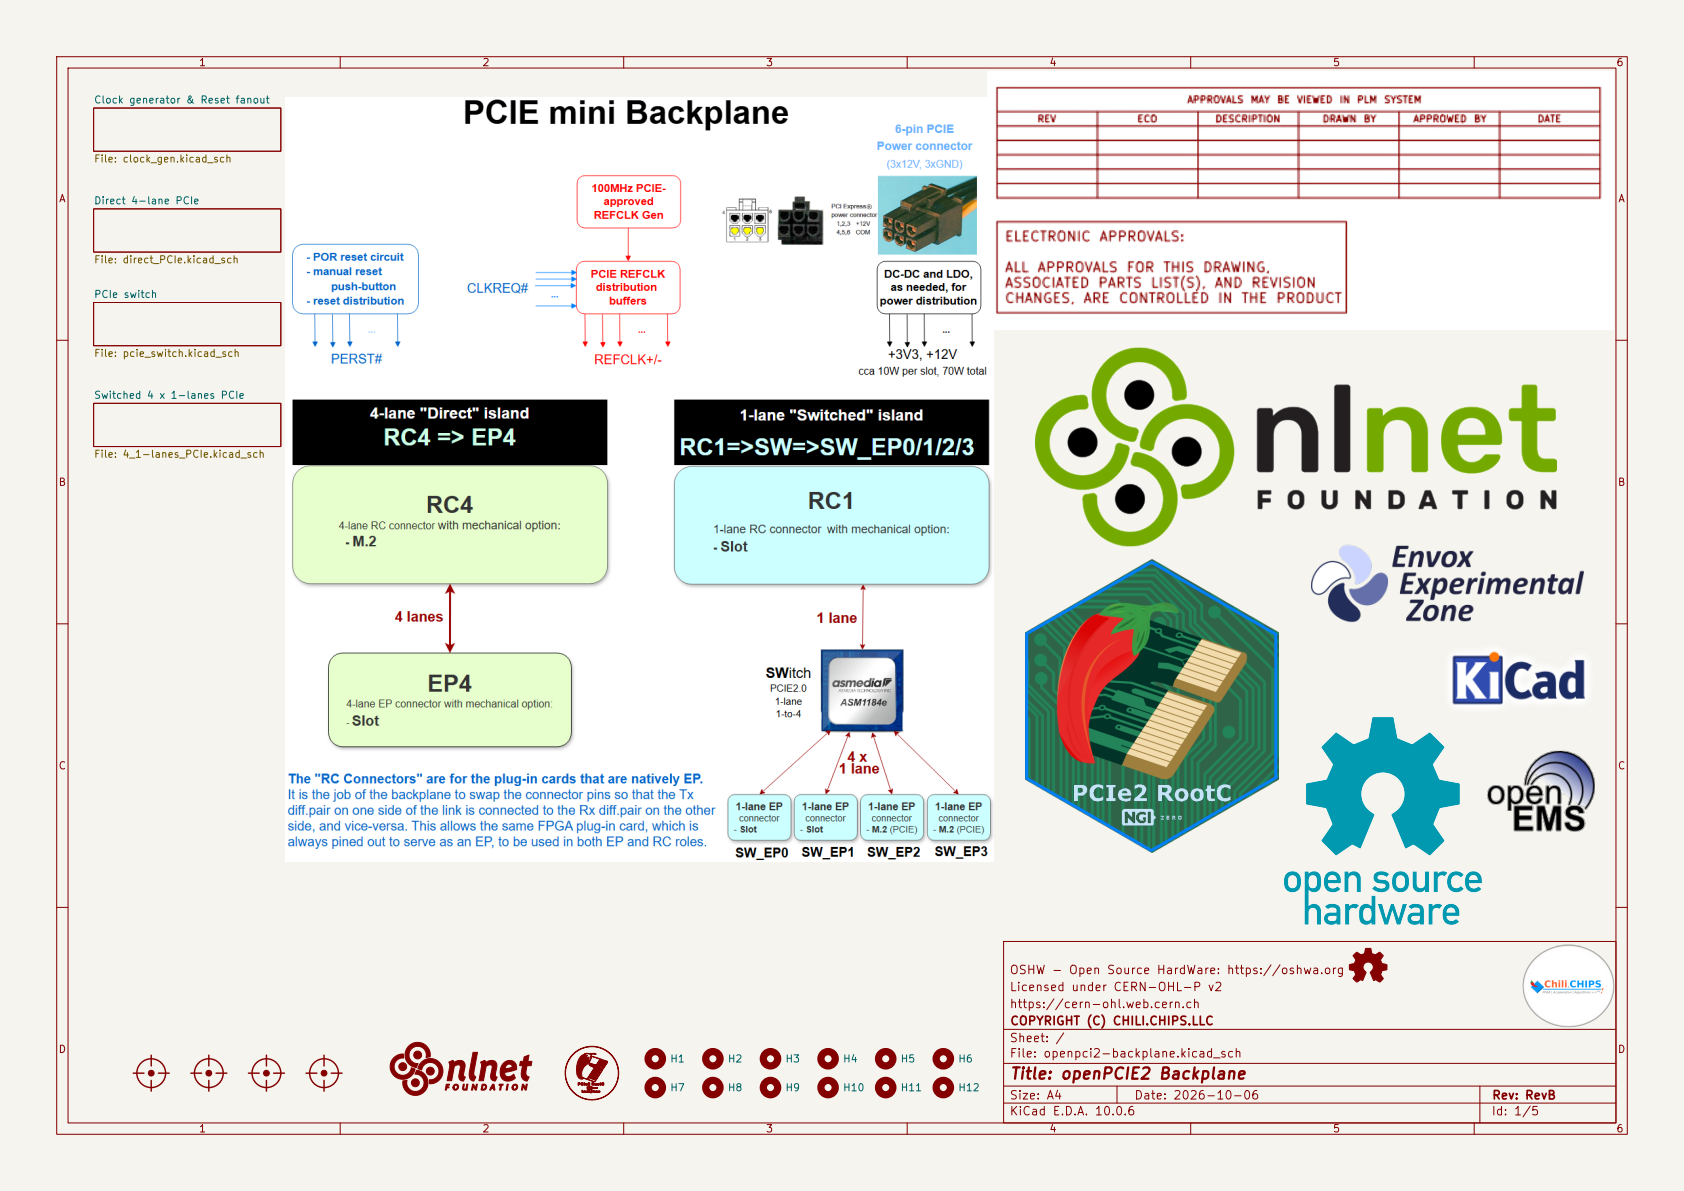
[picture p328: page 1]

Clock generator & Reset fanout File: clock_gen.kicad_sch Switched 4 x 1-lanes PCIe

File: 4_1-lanes_PCIe.kicad_sch Direct 4-lane PCIe

OSHW - Open Source HardWare: https://oshwa.org
Licensed under CERN-OHL-P v2
https://cern-ohl.web.cern.ch
COPYRIGHT (C) CHILI.CHIPS.LLC
Sheet: /
File: openpci2-backplane.kicad_sch
Title: openPCIE2 Backplane

Size: A4 | Rev: RevB
KiCad E.D.A. 10.0.6 | Id: 1/5

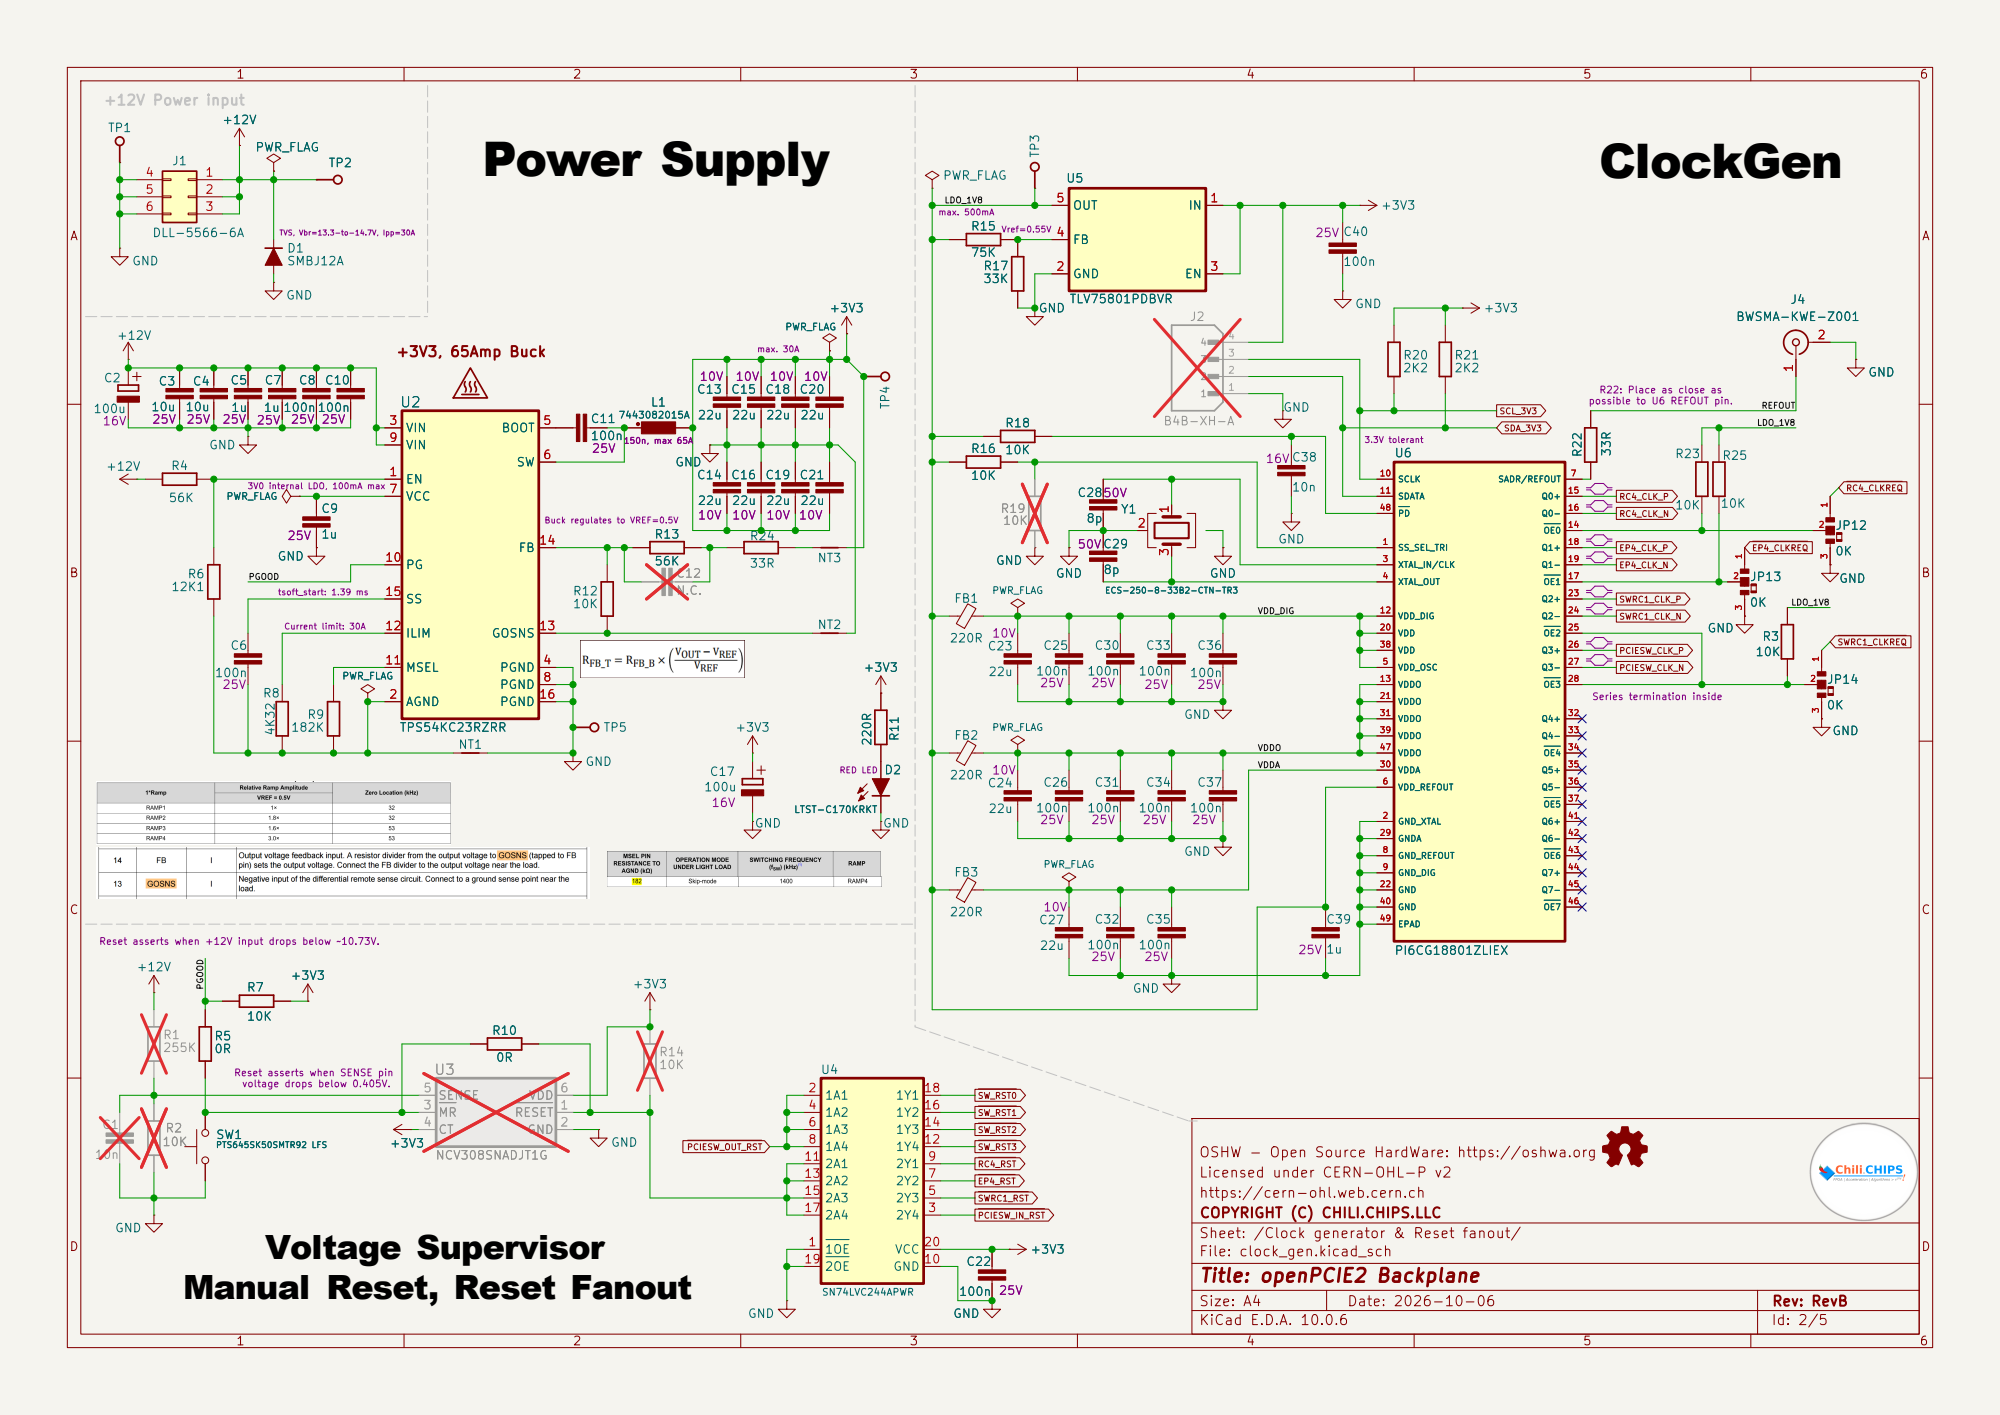
[picture p329: page 2]

TVS, Vbr=13.3-to-14.7V, Ipp=30A +12V Power input

R22: Place as close as possible to U6 REFOUT pin. PWR_FLAG

tsoft_start: 1.39 ms Reset asserts when SENSE pin

Voltage Supervisor
Manual Reset, Reset Fanout

OSHW - Open Source HardWare: https://oshwa.org
Licensed under CERN-OHL-P v2
https://cern-ohl.web.cern.ch
COPYRIGHT (C) CHILI.CHIPS.LLC
Sheet: /Clock generator & Reset fanout/
File: clock_gen.kicad_sch
Title: openPCIE2 Backplane

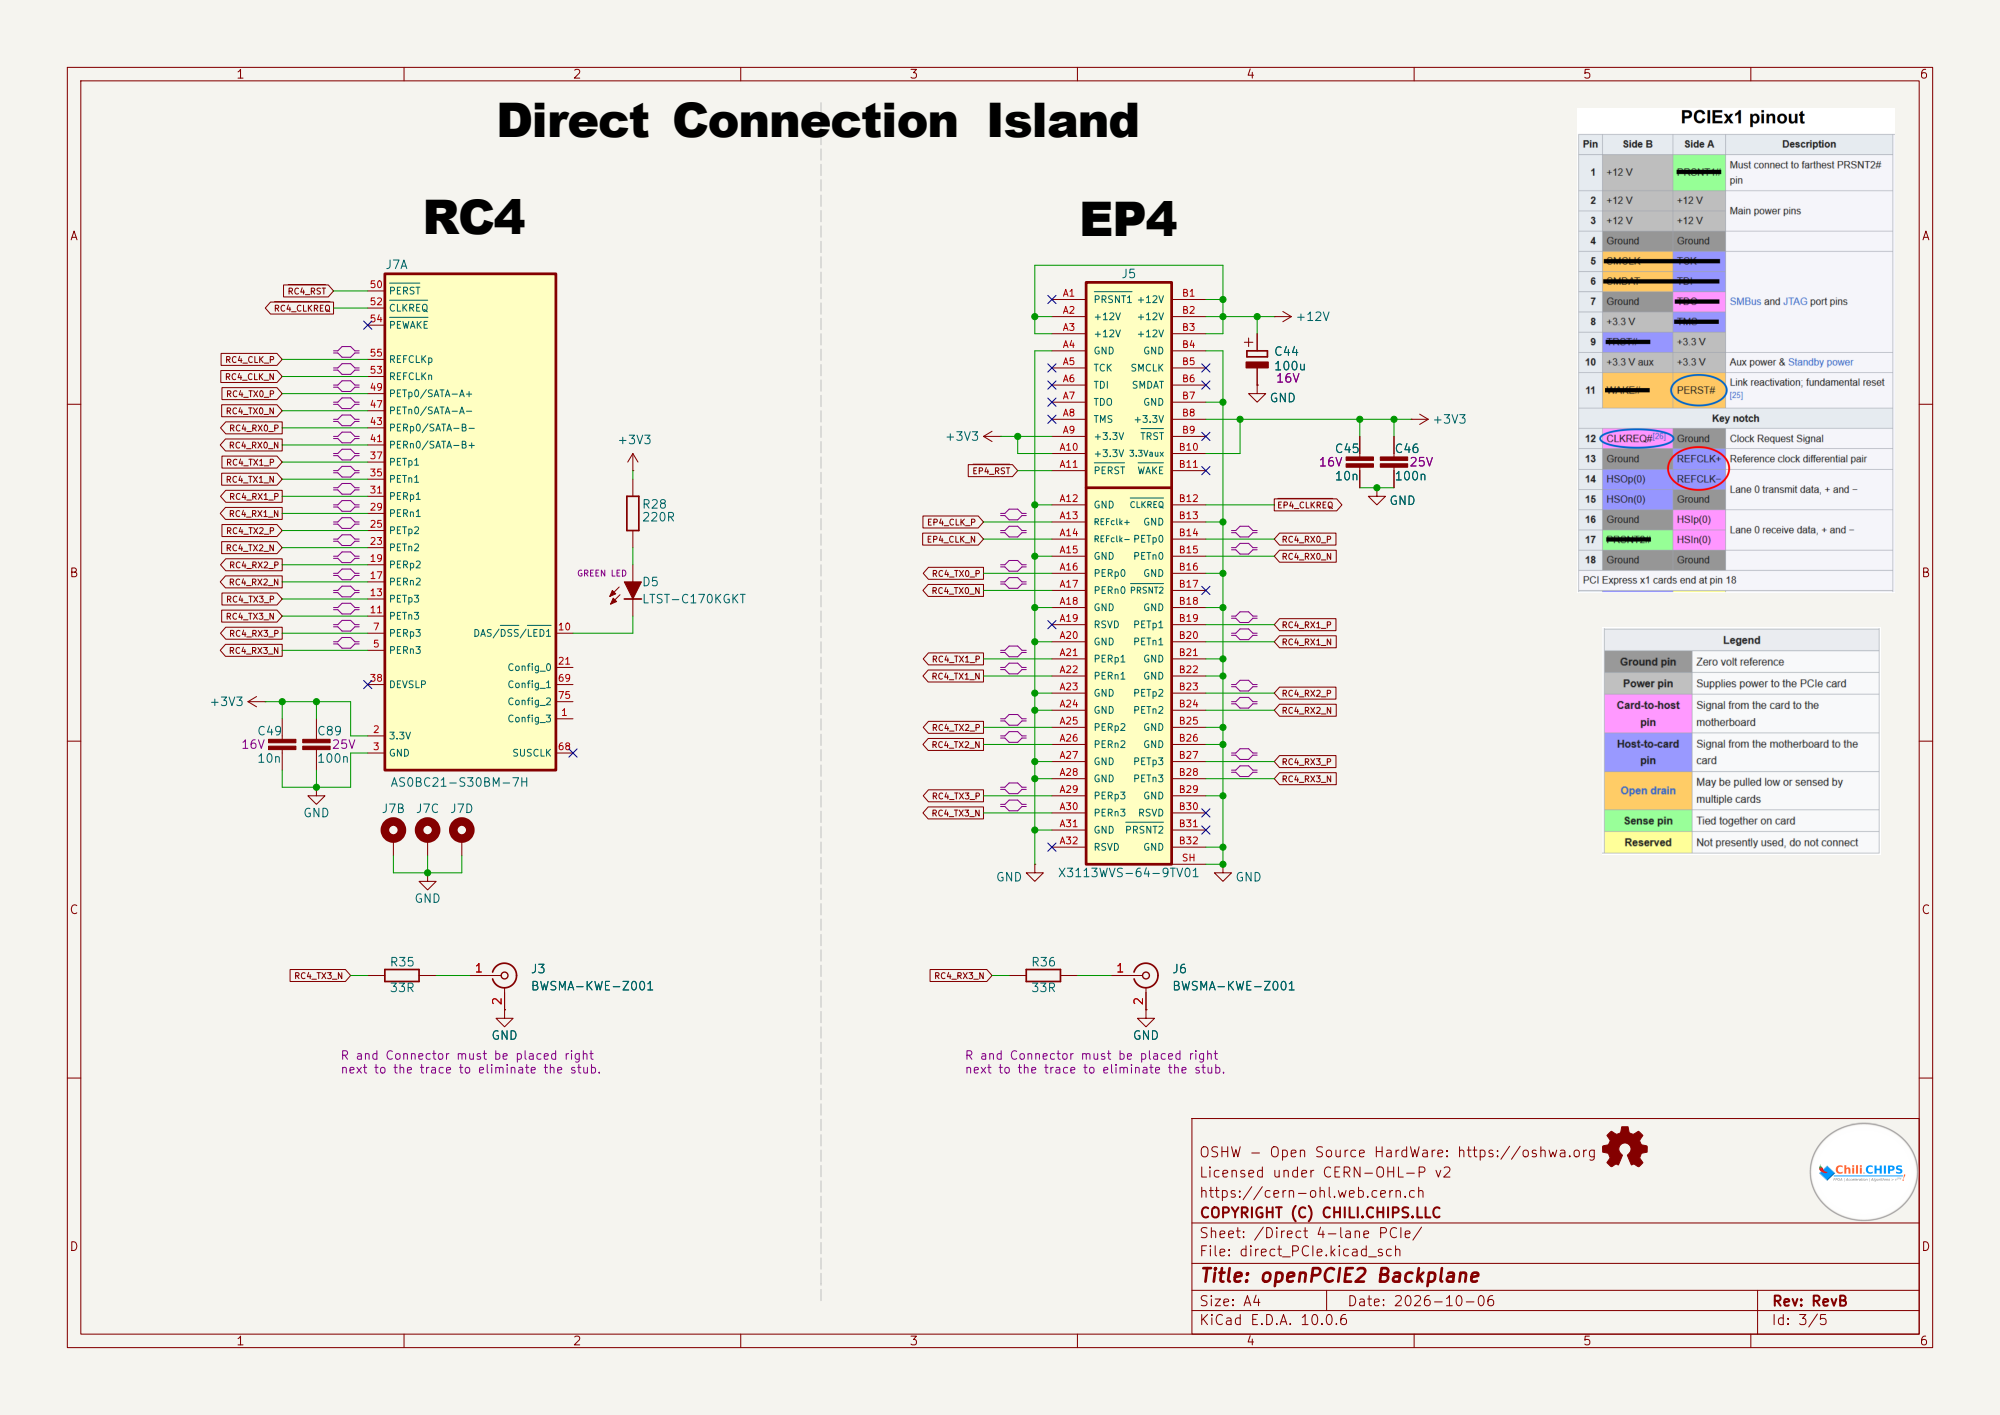
[picture p330: page 3]

OSHW - Open Source HardWare: https://oshwa.org
Licensed under CERN-OHL-P v2
https://cern-ohl.web.cern.ch
COPYRIGHT (C) CHILI.CHIPS.LLC
Sheet: /Direct 4-lane PCIe/
File: direct_PCIe.kicad_sch
Title: openPCIE2 Backplane

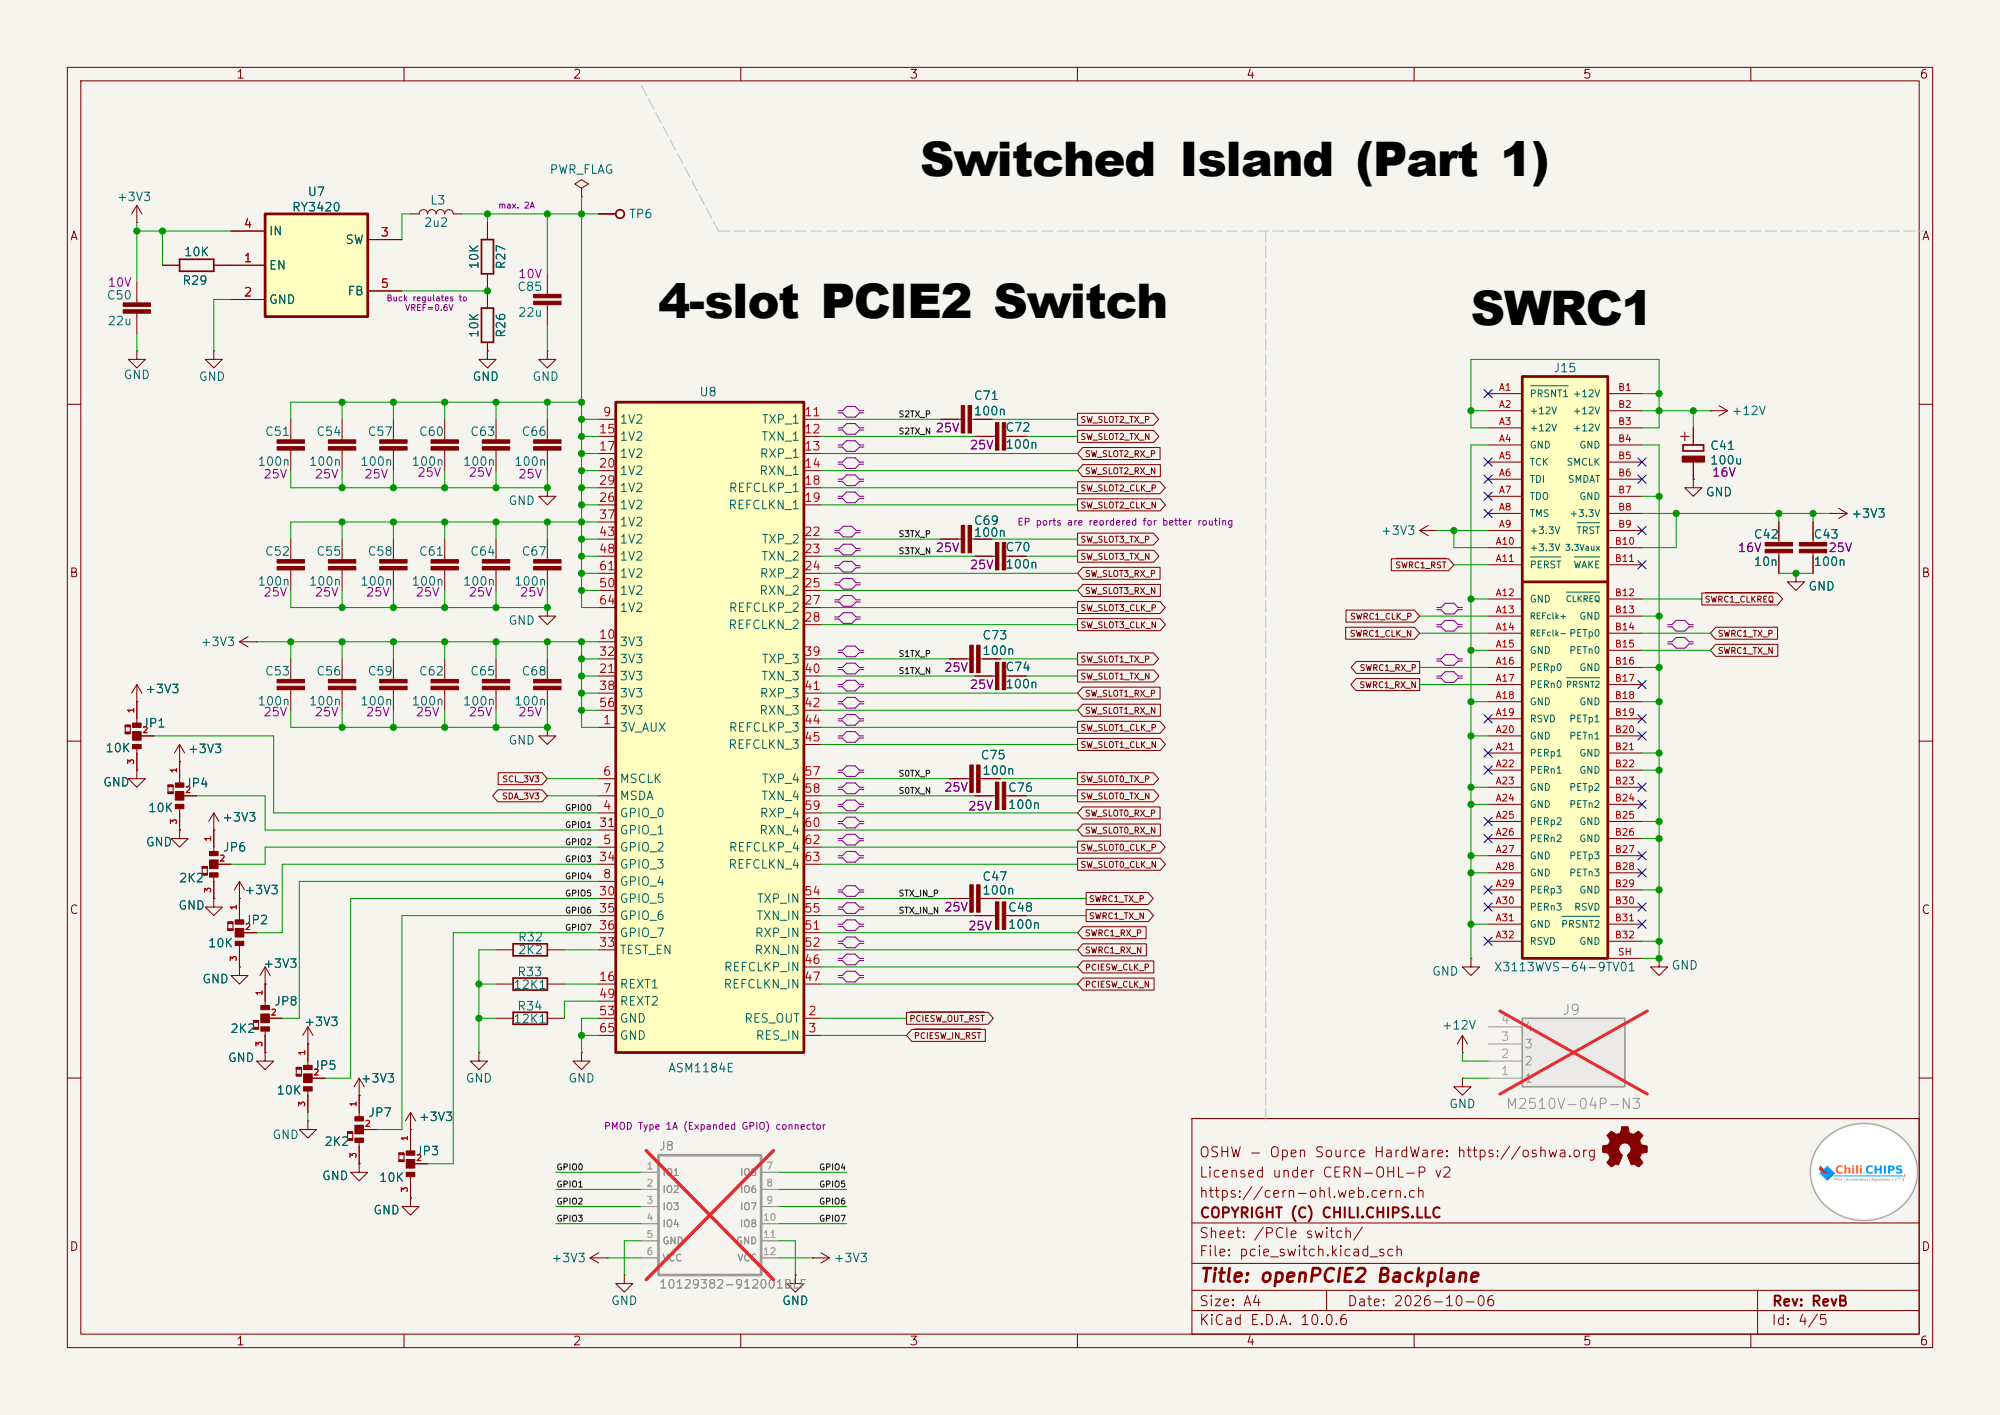
[picture p331: page 4]

PMOD Type 1A (Expanded GPIO) connector 4-slot PCIE2 Switch

EP ports are reordered for better routing

3V3 38 | | X3113WVS-64-9TV01 C61

1V2 48 REXT2 49 3V3 56 | 100n 25V 100n 25V C76 C76 25V 25V 100n C75 100n C75

3V3 21 | 100n 25V C73
3V3 32

OSHW - Open Source HardWare: https://oshwa.org
Licensed under CERN-OHL-P v2
https://cern-ohl.web.cern.ch
COPYRIGHT (C) CHILI.CHIPS.LLC
Sheet: /PCIe switch/
File: pcie_switch.kicad_sch
Title: openPCIE2 Backplane

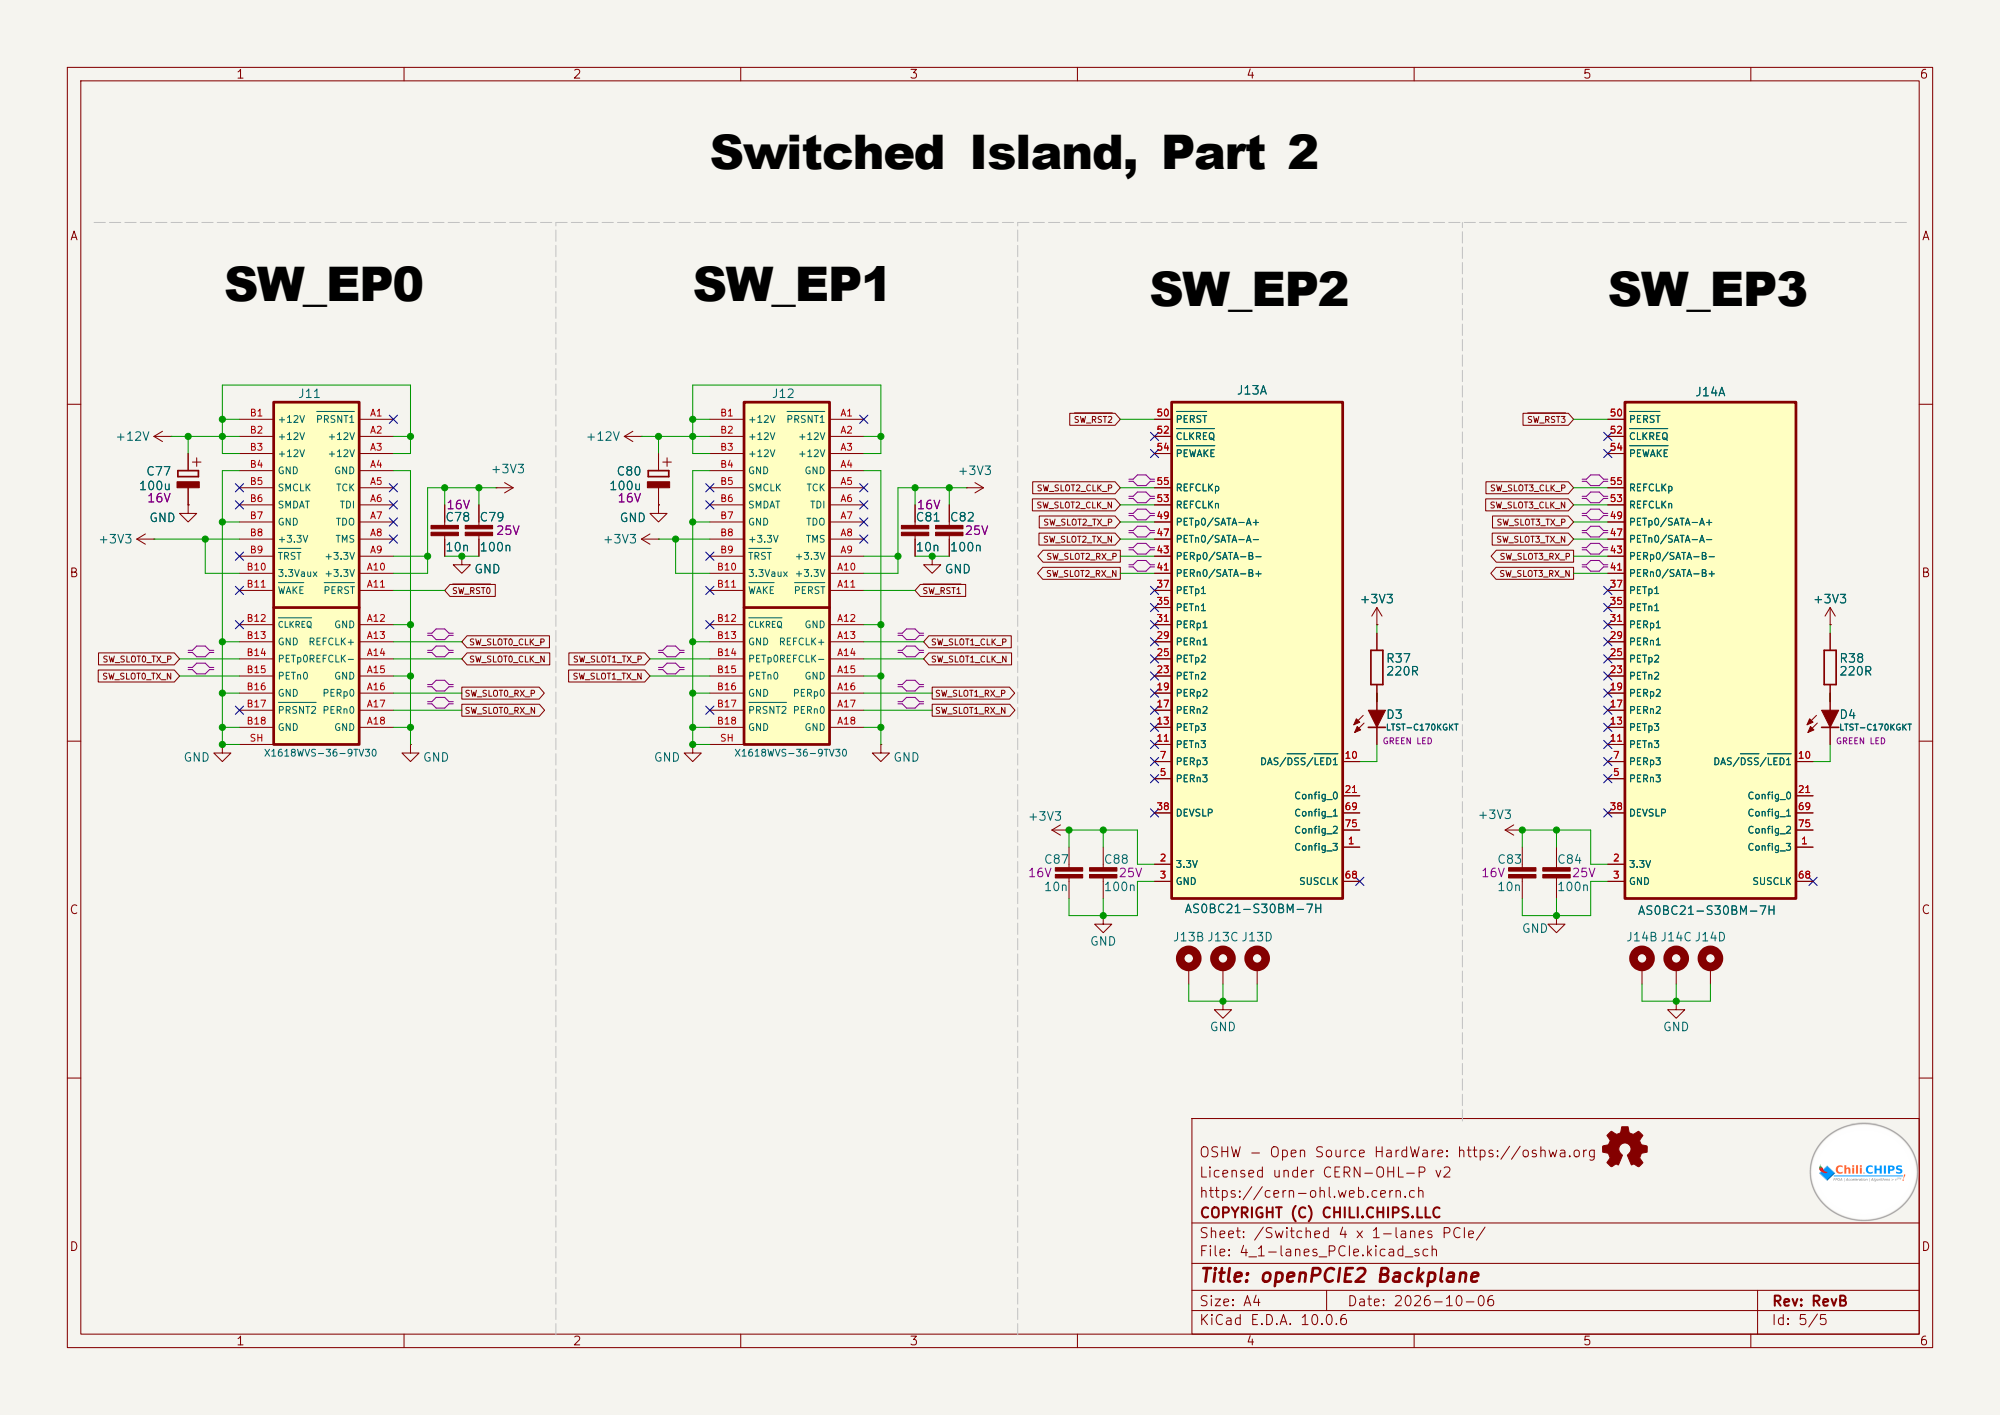
[picture p332: page 5]

OSHW - Open Source HardWare: https://oshwa.org
Licensed under CERN-OHL-P v2
https://cern-ohl.web.cern.ch
COPYRIGHT (C) CHILI.CHIPS.LLC
Sheet: /Switched 4 x 1-lanes PCIe/
File: 4_1-lanes_PCIe.kicad_sch
Title: openPCIE2 Backplane
