chili-chips-ba/openPCIE/1.pcb/0.doc/openPCIE backplane presentation.pdf

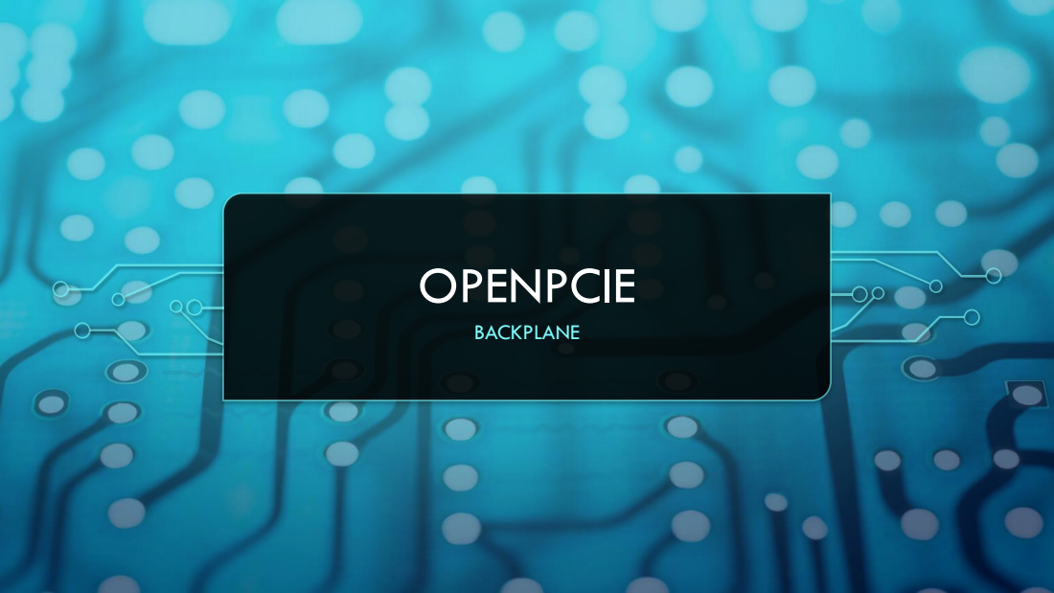
[picture p333: page 1]
OPENPCIE; BACKPLANE

# FUNCTIONALITY AND TOPOLOGY

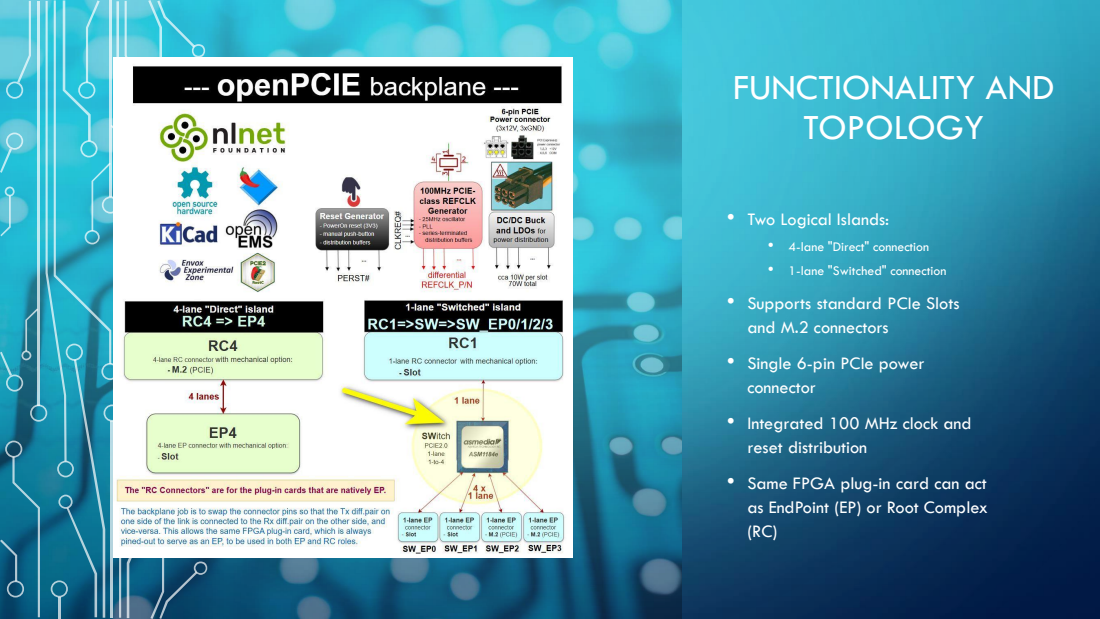
[picture p334: page 2]

• Two Logical Islands:

• 4-lane "Direct" connection

• 1-lane "Switched" connection
• Supports standard PCIe Slots
and M.2 connectors

• Single 6-pin PCIe power
connector

• Integrated 100 MHz clock and
reset distribution

• Same FPGA plug-in card can act
as EndPoint (EP) or Root Complex

# KICAD PCB LAYOUT

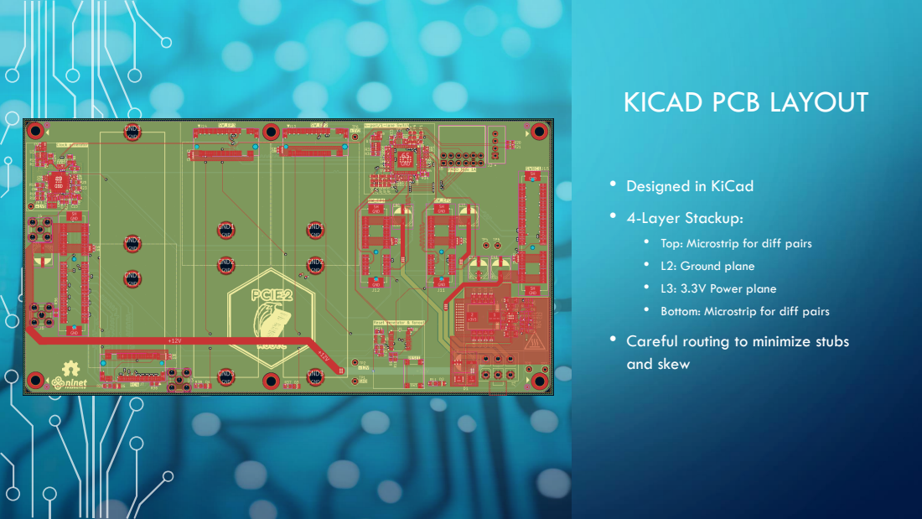
[picture p335: page 3]
• 4-Layer Stackup:

• Designed in KiCad

• Top: Microstrip for diff pairs
• L2: Ground plane
• L3: 3.3V Power plane
• Bottom: Microstrip for diff pairs
• Careful routing to minimize stubs
and skew

# 3D VIEW

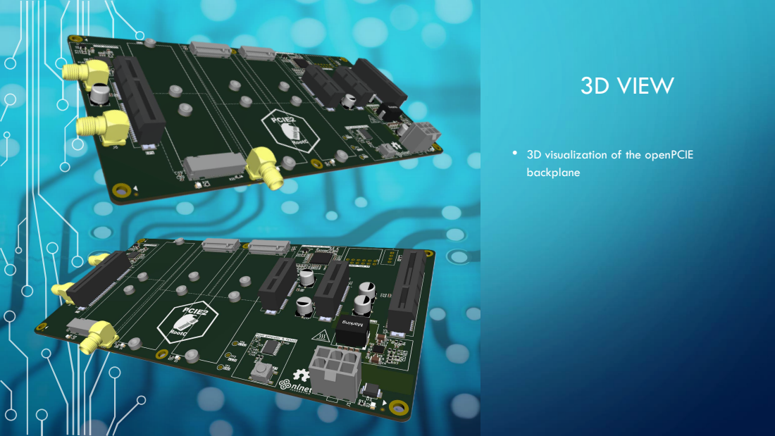
[picture p336: page 4]

• 3D visualization of the openPCIE
backplane

# MANUFACTURING AND TESTING PREPARATION

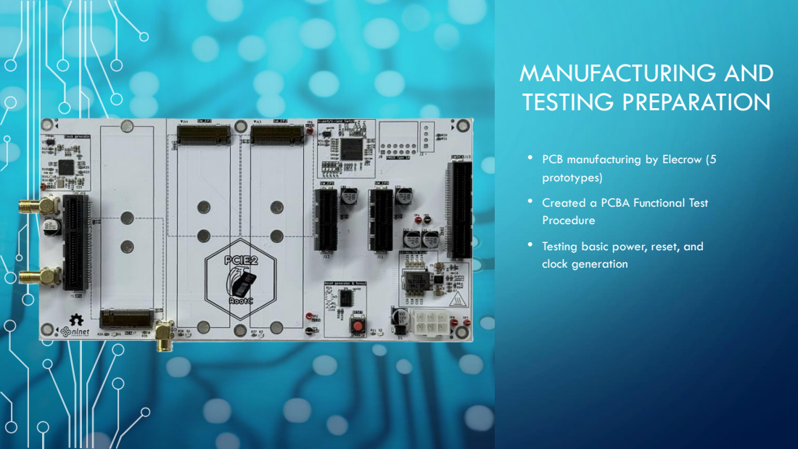
[picture p337: page 5]

• PCB manufacturing by Elecrow (5
prototypes)

• Created a PCBA Functional Test
Procedure

• Testing basic power, reset, and
clock generation

# FACTORY TEST RESULTS

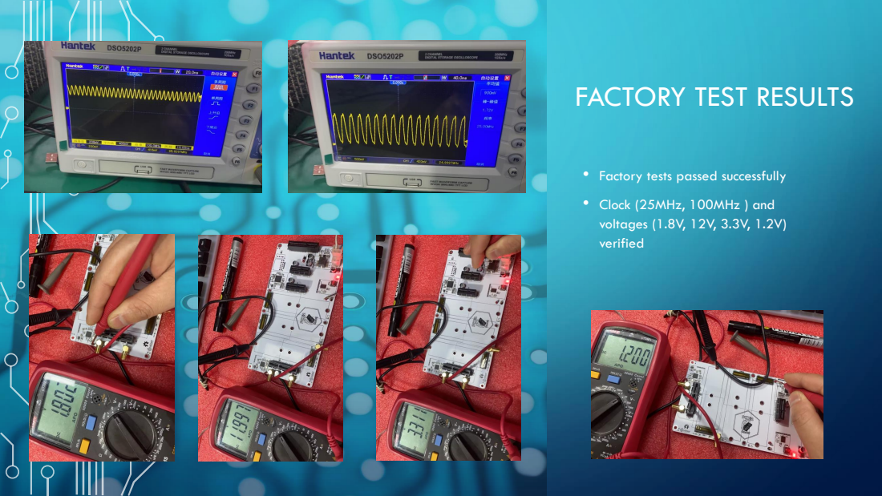
[picture p338: page 6]
• Clock (25MHz, 100MHz ) and; voltages (1.8V, 12V, 3.3V, 1.2V); verified

• Factory tests passed successfully

# BOARDS ARRIVAL

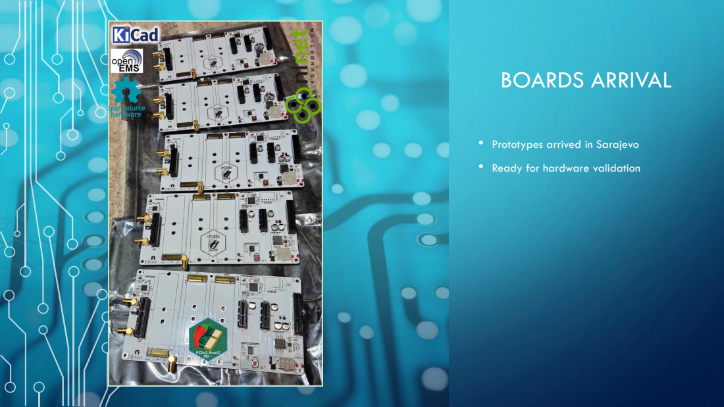
[picture p339: page 7]

• Prototypes arrived in Sarajevo

• Ready for hardware validation

# STARTING THE TESTS (DIRECT CONNECTION)

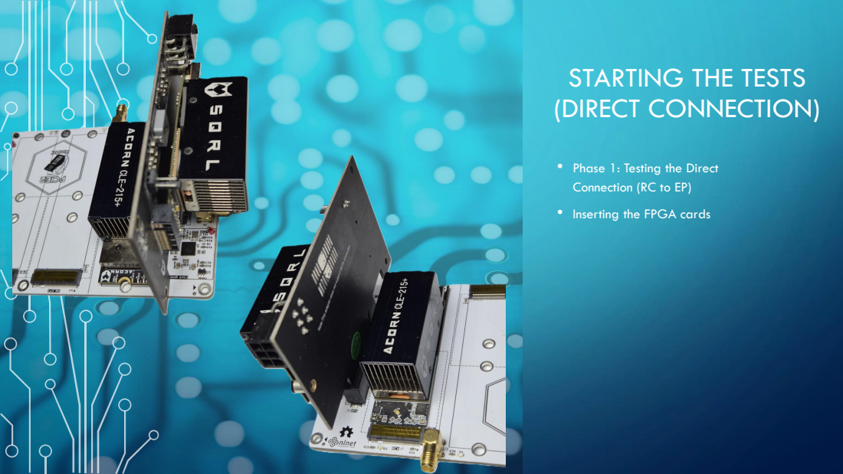
[picture p340: page 8]

• Phase 1: Testing the Direct
Connection (RC to EP)

• Inserting the FPGA cards

# THE CLKREQ PROBLEM

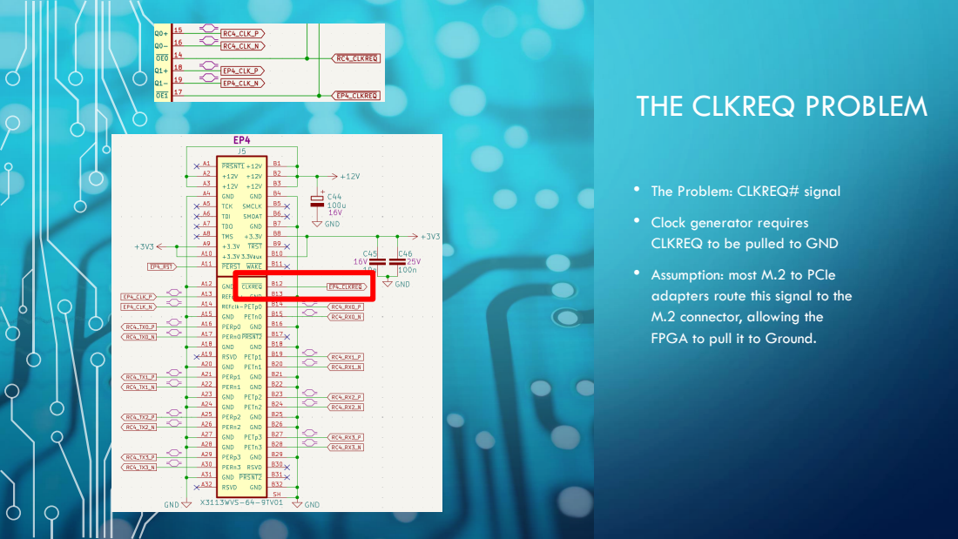
[picture p341: page 9]

• The Problem: CLKREQ# signal

• Clock generator requires
CLKREQ to be pulled to GND

• Assumption: most M.2 to PCIe
adapters route this signal to the
M.2 connector, allowing the
FPGA to pull it to Ground.

# HISTORY OF CLKREQ

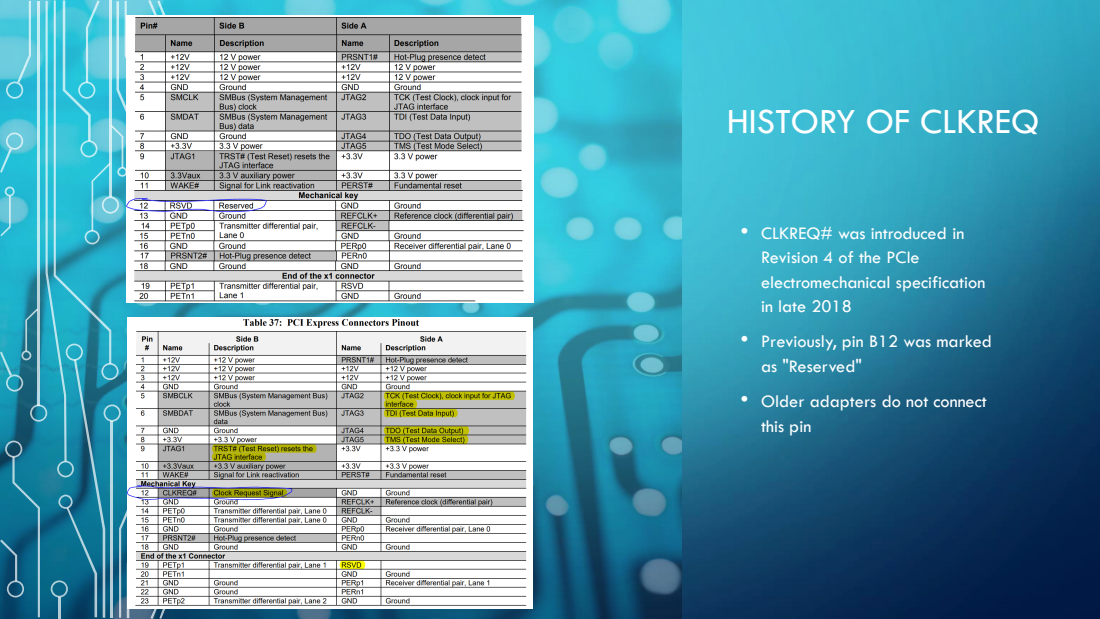
[picture p342: page 10]

• CLKREQ# was introduced in
Revision 4 of the PCIe
electromechanical specification
in late 2018

• Previously, pin B12 was marked
as "Reserved"

• Older adapters do not connect
this pin

# TEMPORARY FIX

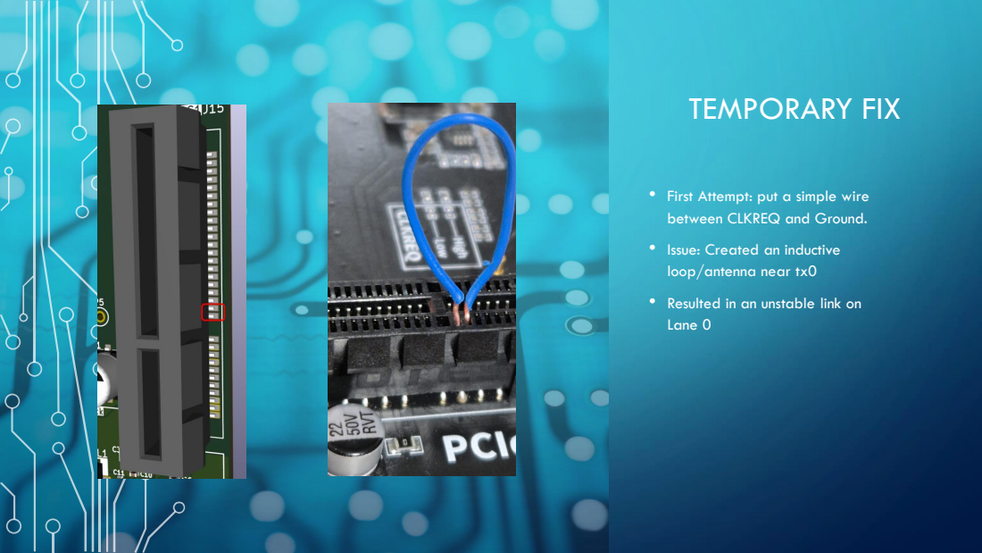
[picture p343: page 11]

• First Attempt: put a simple wire
between CLKREQ and Ground.

• Issue: Created an inductive
loop/antenna near tx0

• Resulted in an unstable link on
Lane 0

# THE PERMANENT FIX

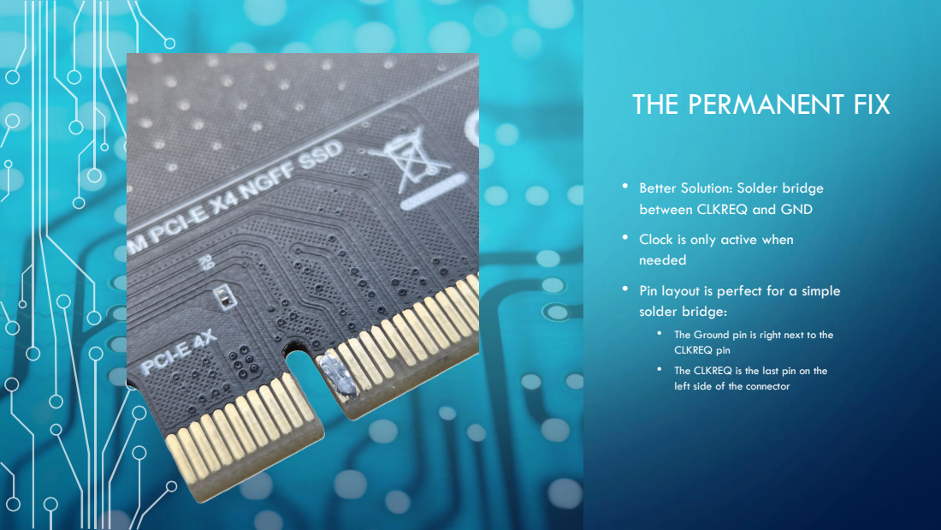
[picture p344: page 12]

• Better Solution: Solder bridge
between CLKREQ and GND

• Clock is only active when
needed

• Pin layout is perfect for a simple
solder bridge:

• The Ground pin is right next to the
CLKREQ pin
• The CLKREQ is the last pin on the
left side of the connector

# VERIFICATION ENVIRONMENT

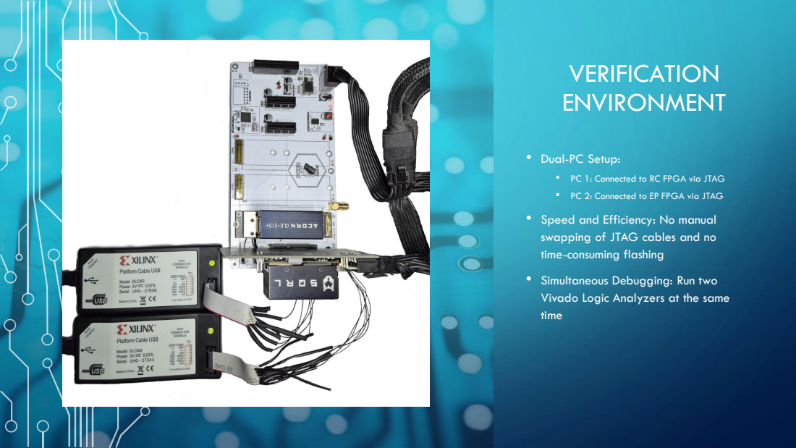
[picture p345: page 13]

• Dual-PC Setup:

• PC 1: Connected to RC FPGA via JTAG

• PC 2: Connected to EP FPGA via JTAG
• Speed and Efficiency: No manual
swapping of JTAG cables and no
time-consuming flashing

• Simultaneous Debugging: Run two
Vivado Logic Analyzers at the same
time

# TEST OBJECTIVE AND RESULTS

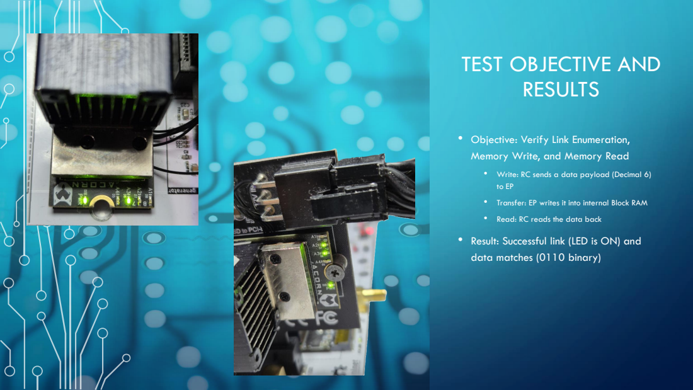
[picture p346: page 14]

• Objective: Verify Link Enumeration,

Memory Write, and Memory Read

• Write: RC sends a data payload (Decimal 6)
• Transfer: EP writes it into internal Block RAM

• Read: RC reads the data back

• Result: Successful link (LED is ON) and

data matches (0110 binary)

# SWITCH TESTING

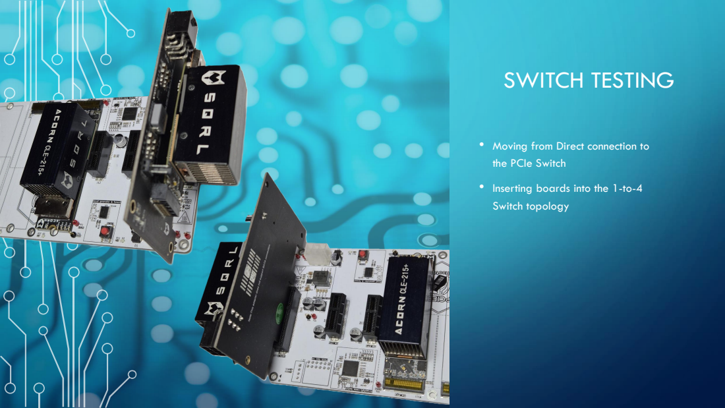
[picture p347: page 15]
Switch topology

• Moving from Direct connection to

the PCIe Switch

• Inserting boards into the 1-to-4

# THE SWITCH OVERHEATING

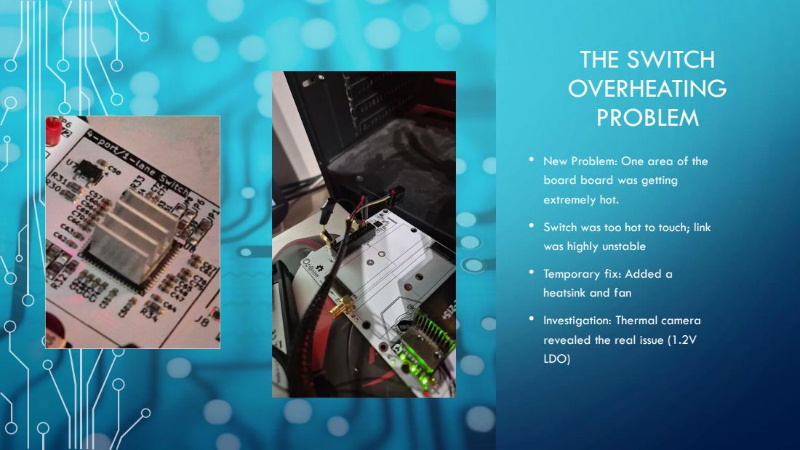
[picture p348: page 16]
PROBLEM

• New Problem: One area of the

board board was getting
extremely hot.

• Switch was too hot to touch; link

was highly unstable

• Temporary fix: Added a

heatsink and fan

• Investigation: Thermal camera

revealed the real issue (1.2V
LDO)

# THERMAL CAMERA ANALYSIS

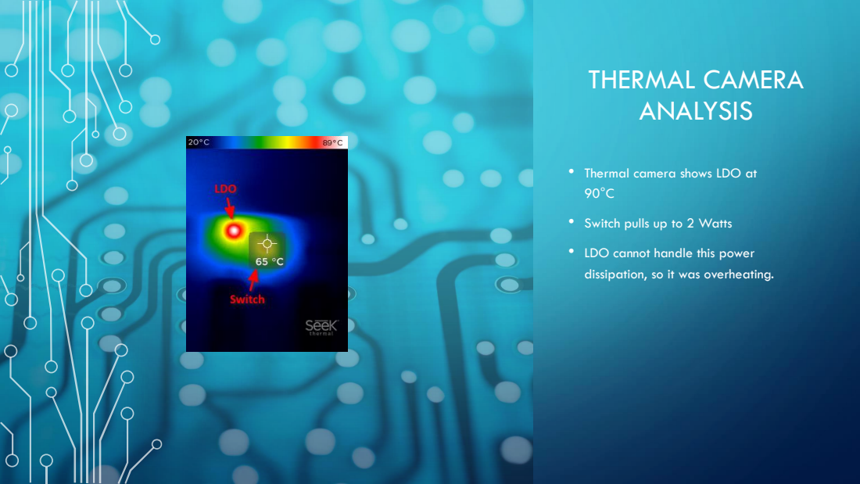
[picture p349: page 17]

• Thermal camera shows LDO at

• Switch pulls up to 2 Watts

• LDO cannot handle this power

dissipation, so it was overheating.

# TESTING THE BUCK CONVERTER

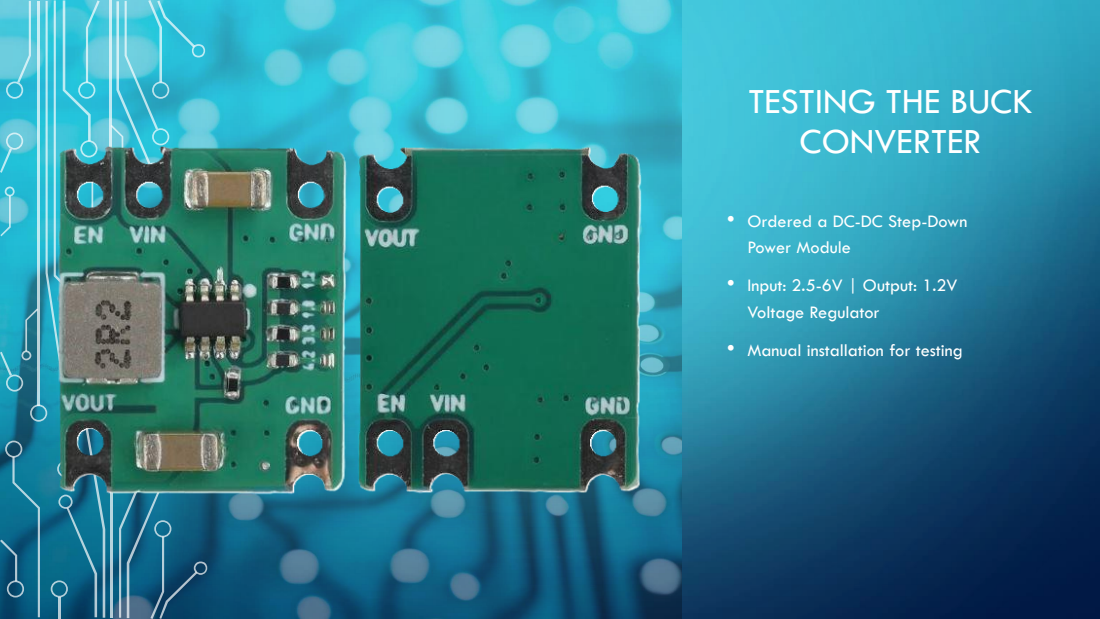
[picture p350: page 18]
Power Module; • Input: 2.5-6V | Output: 1.2V; Voltage Regulator

• Ordered a DC-DC Step-Down

• Manual installation for testing

# MANUAL BOARD MODIFICATION

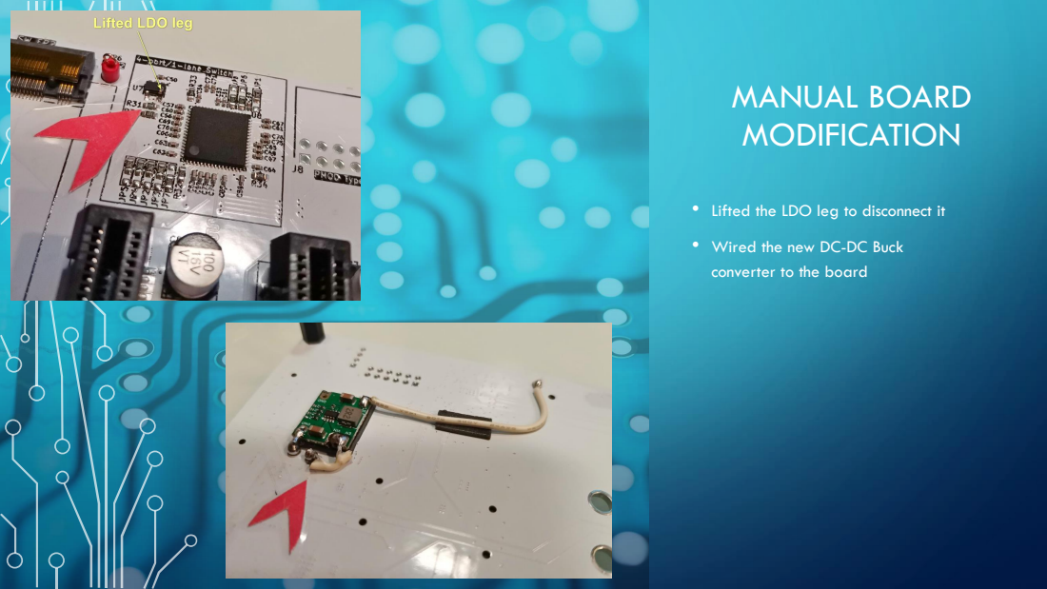
[picture p351: page 19]

• Lifted the LDO leg to disconnect it

• Wired the new DC-DC Buck

converter to the board

# TEMPERATURE RESULTS

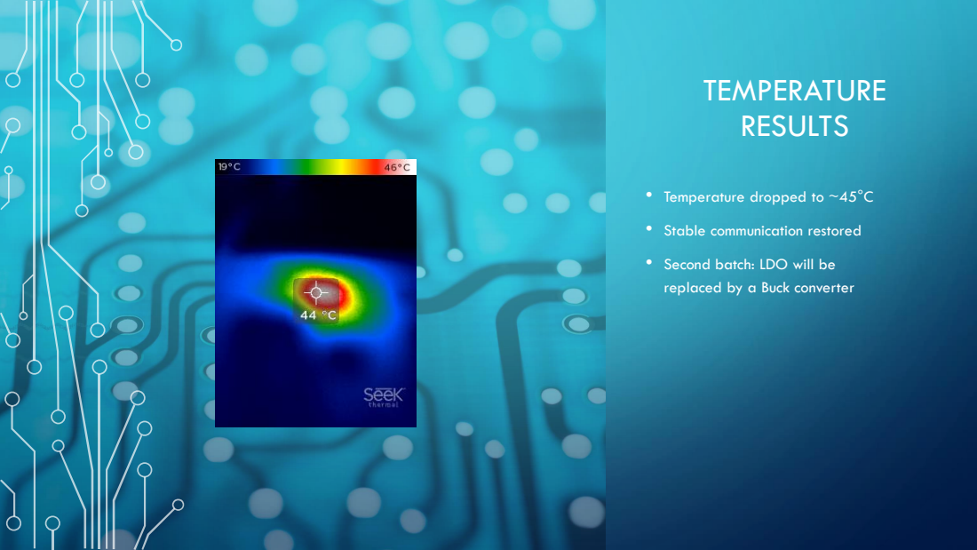
[picture p352: page 20]

• Temperature dropped to ~45°C

• Stable communication restored

• Second batch: LDO will be

replaced by a Buck converter

# FULLY POPULATED SWITCH

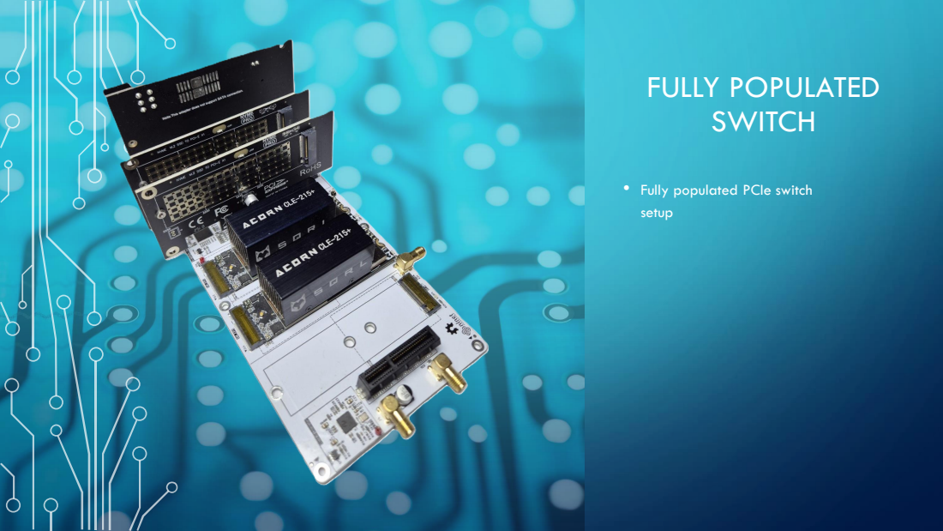
[picture p353: page 21]
setup

• Fully populated PCIe switch

# IMPROVEMENTS FOR THE SECOND BATCH

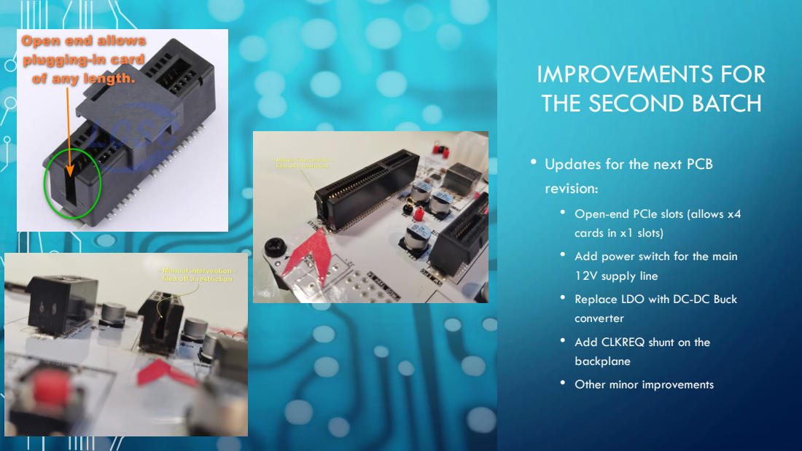
[picture p354: page 22]

• Updates for the next PCB
revision:

• Open-end PCIe slots (allows x4

cards in x1 slots)
• Add power switch for the main

12V supply line
• Replace LDO with DC-DC Buck

converter
• Add CLKREQ shunt on the

backplane
• Other minor improvements

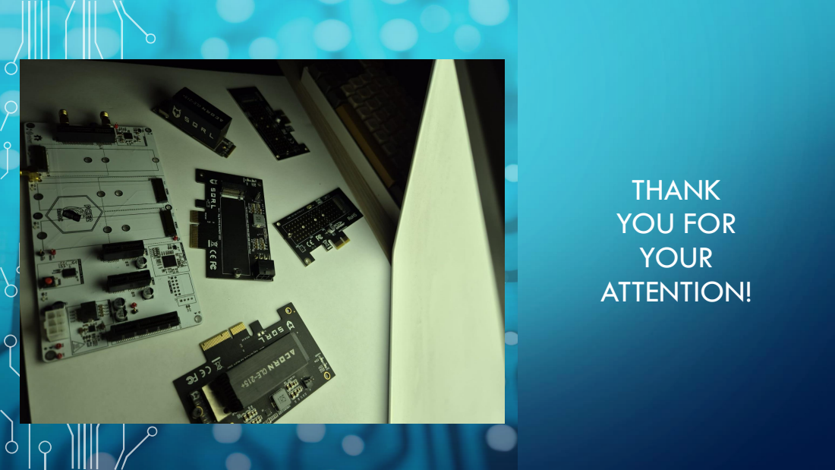
[picture p355: page 23]
THANK YOU FOR YOUR ATTENTION!
