chili-chips-ba/openPCIE/1.pcb/0.doc/openPCIE-BlockDiagram.pdf

# --- openPCIE backplane ---

July 27, 2025

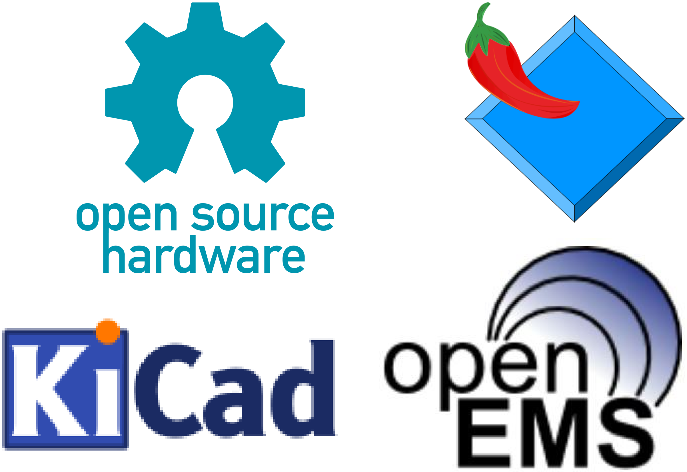
[picture p356: figure]
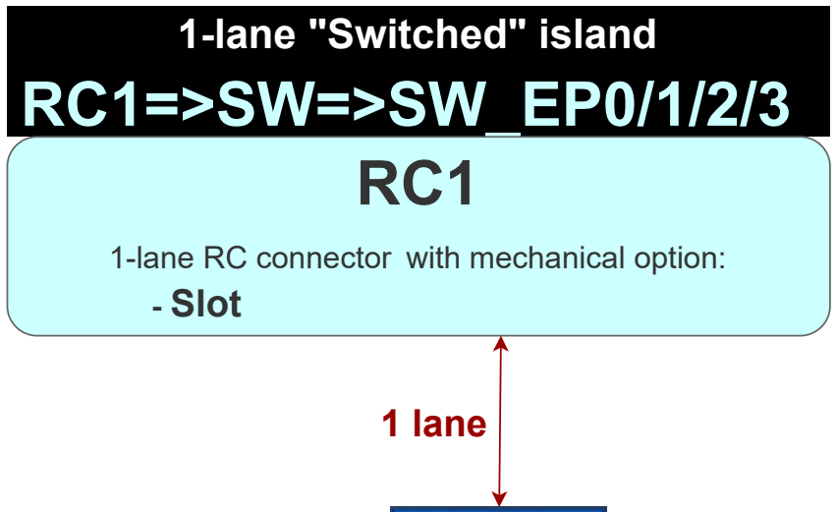
[picture p357: figure]
1-lane "Switched" island RC1=>SW=>SW_EP0/1/2/3 RC1; - Slot; 1 lane
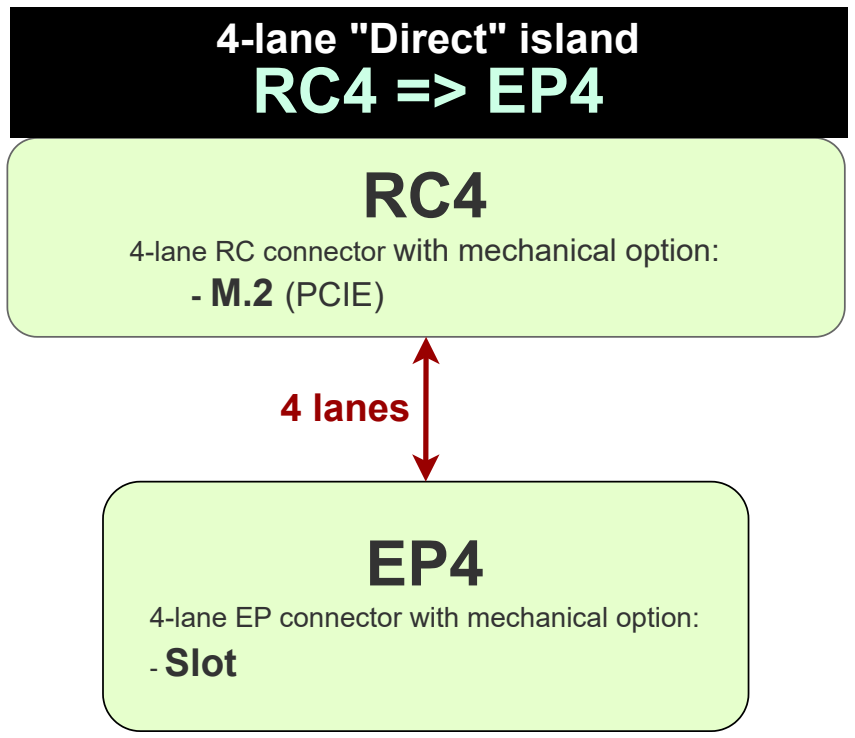
[picture p358: figure]
- M.2 (PCIE); 4-lane "Direct" island RC4 => EP4; - Slot; 4 lanes

4-lane RC connector with mechanical option:

4-lane EP connector with mechanical option:

The "RC Connectors" are for the plug-in cards that are natively EP.

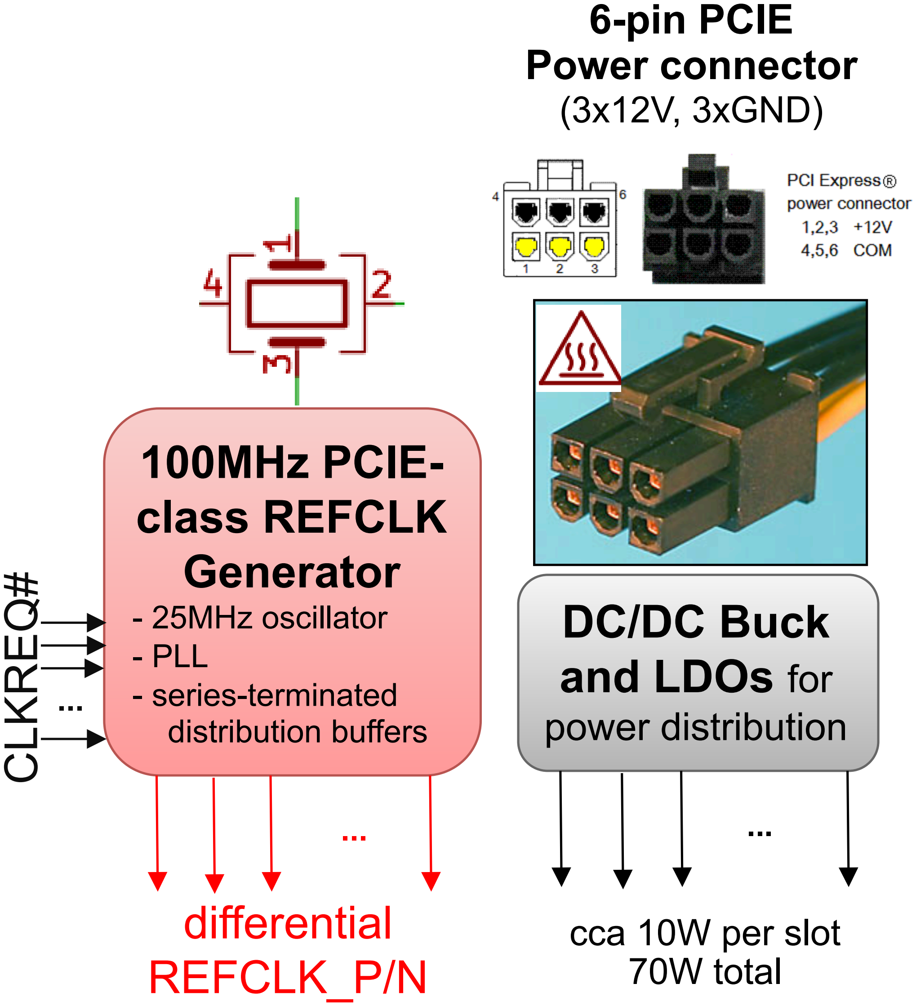
[picture p359: figure]
cca 10W per slot 70W total; differential REFCLK_P/N; 6-pin PCIE Power connector (3x12V, 3xGND); DC/DC Buck and LDOs for power distribution; 100MHz PCIE- class REFCLK Generator - 25MHz oscillator - PLL - series-terminated distribution buffers; CLKREQ#

1-lane RC connector with mechanical option:

The backplane job is to swap the connector pins so that the Tx diff.pair on one side of the link is connected to the Rx diff.pair on the other side, and vice-versa. This allows the same FPGA plug-in card, which is always pined-out to serve as an EP, to be used in both EP and RC roles.

SWitch
PCIE2.0
1-lane
1-to-4

### 4 x 1 lane

1-lane EP
connector
- Slot

1-lane EP
connector
- Slot

1-lane EP
connector
- M.2 (PCIE)

1-lane EP
connector
- M.2 (PCIE)
SW_EP0 SW_EP1 SW_EP2 SW_EP3

Reset Generator
- PowerOn reset (3V3)
- manual push-button
- distribution buffers

PERST#

## General PCIE topology

## PCIEx1 pinout

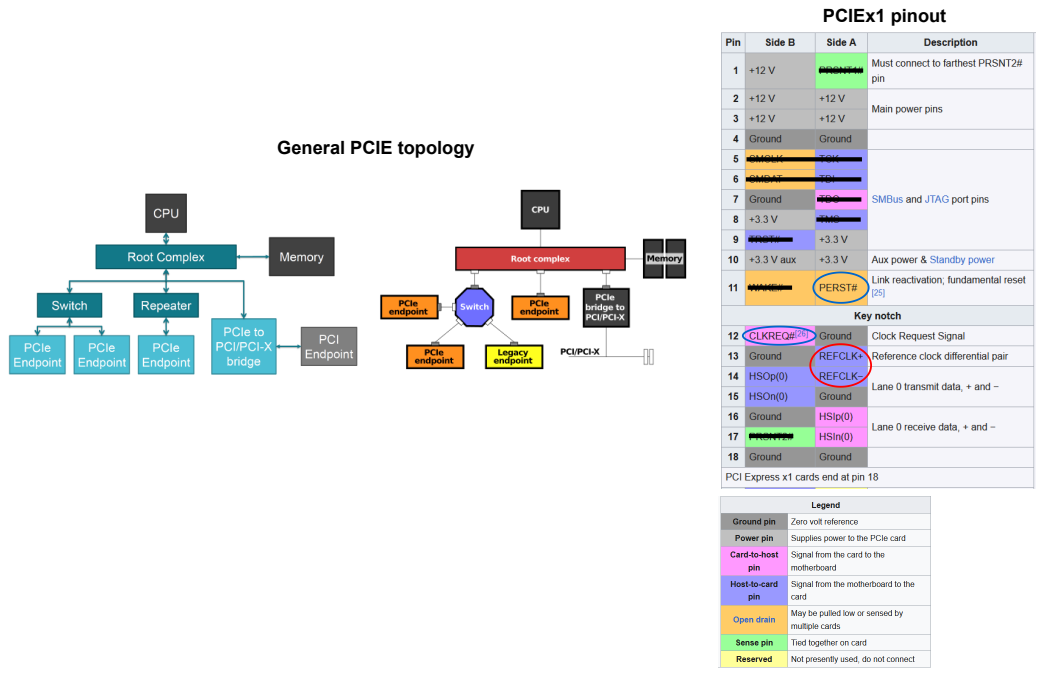
[picture p360: page 2]
