chili-chips-ba/openPCIE/1.pcb/openpci2-backplane/production/openpci2-backplane-gerbers.pdf

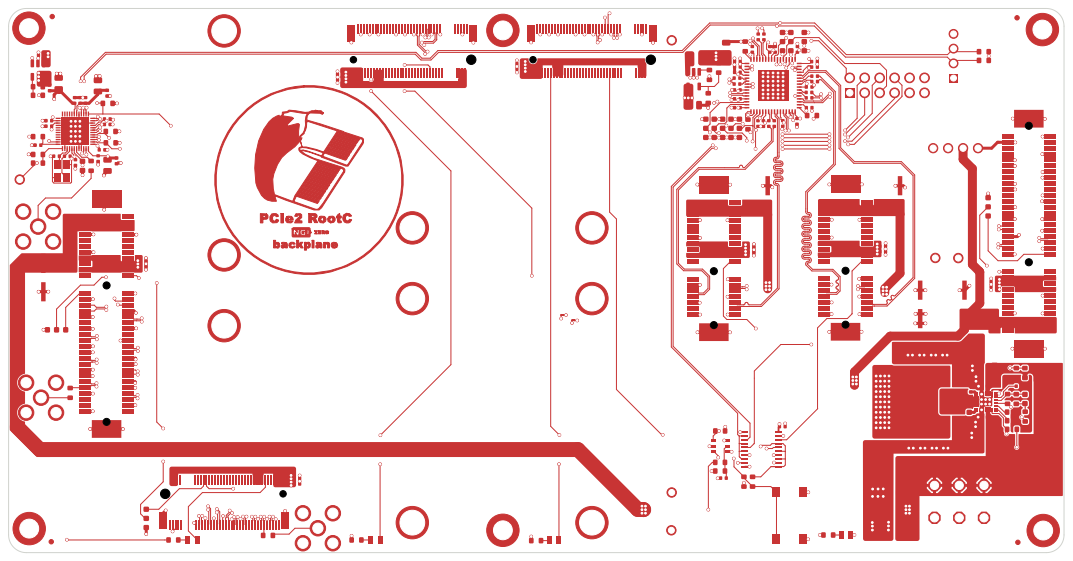
[picture p361: page 1]

COPYRIGHT (C) CHILI.CHIPS.LLC
Sheet:
File: openpci2-backplane.kicad_pcb
Title: openPCIE2 Backplane

Size: A4 | Rev: RevB
KiCad E.D.A. 10.0.6 | Id: 1/11

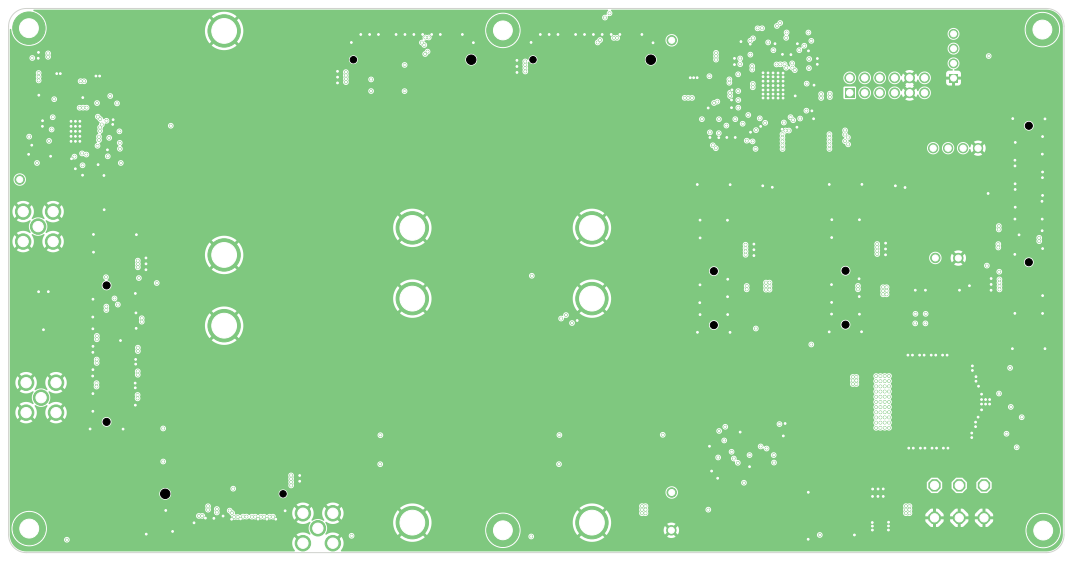
[picture p362: page 2]

COPYRIGHT (C) CHILI.CHIPS.LLC
Sheet:
File: openpci2-backplane.kicad_pcb
Title: openPCIE2 Backplane

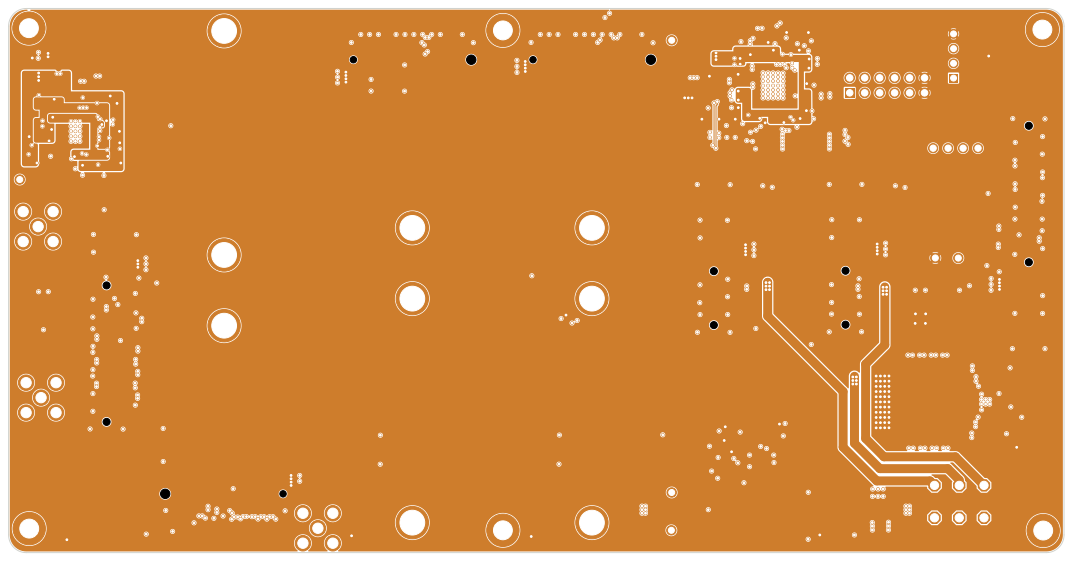
[picture p363: page 3]

COPYRIGHT (C) CHILI.CHIPS.LLC
Sheet:
File: openpci2-backplane.kicad_pcb
Title: openPCIE2 Backplane

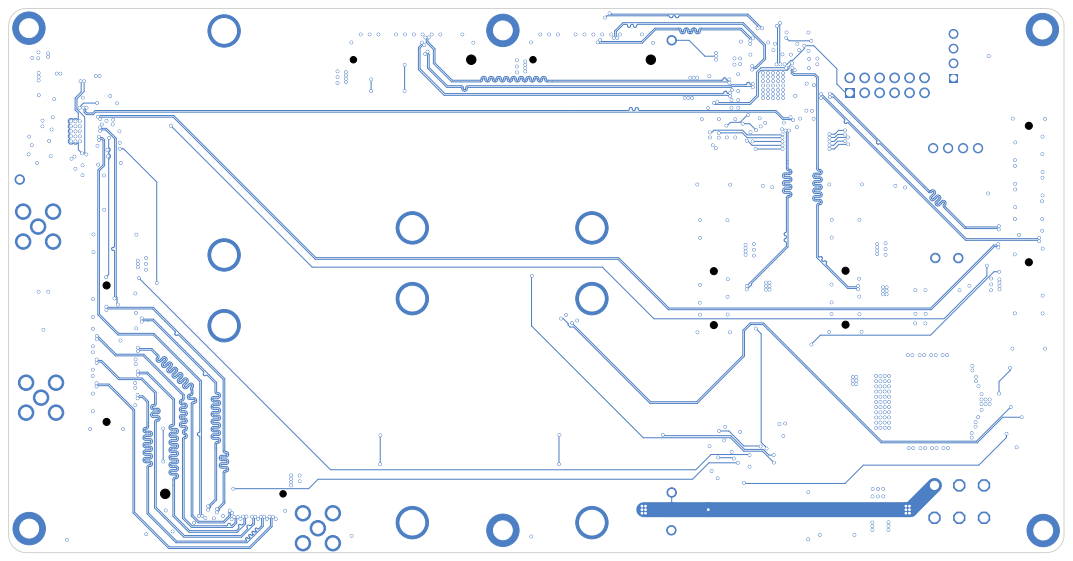
[picture p364: page 4]

COPYRIGHT (C) CHILI.CHIPS.LLC
Sheet:
File: openpci2-backplane.kicad_pcb
Title: openPCIE2 Backplane

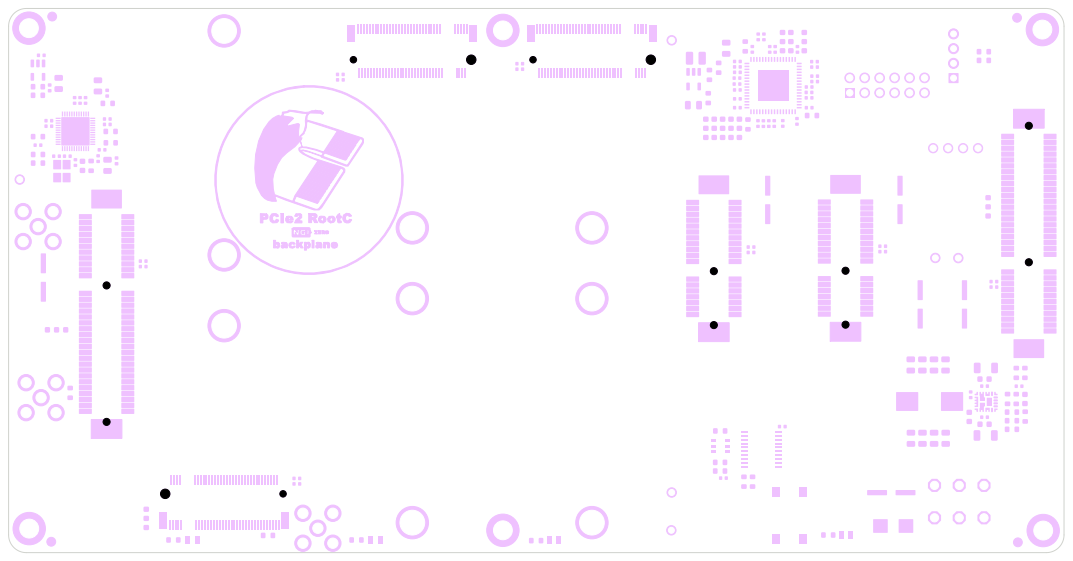
[picture p365: page 5]

COPYRIGHT (C) CHILI.CHIPS.LLC
Sheet:
File: openpci2-backplane.kicad_pcb
Title: openPCIE2 Backplane

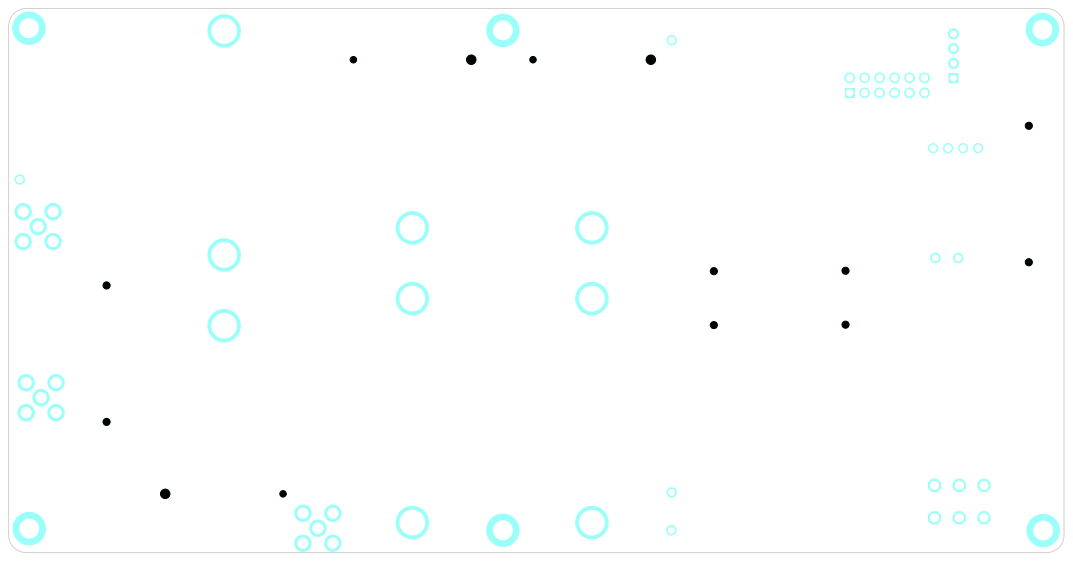
[picture p366: page 6]

COPYRIGHT (C) CHILI.CHIPS.LLC
Sheet:
File: openpci2-backplane.kicad_pcb
Title: openPCIE2 Backplane

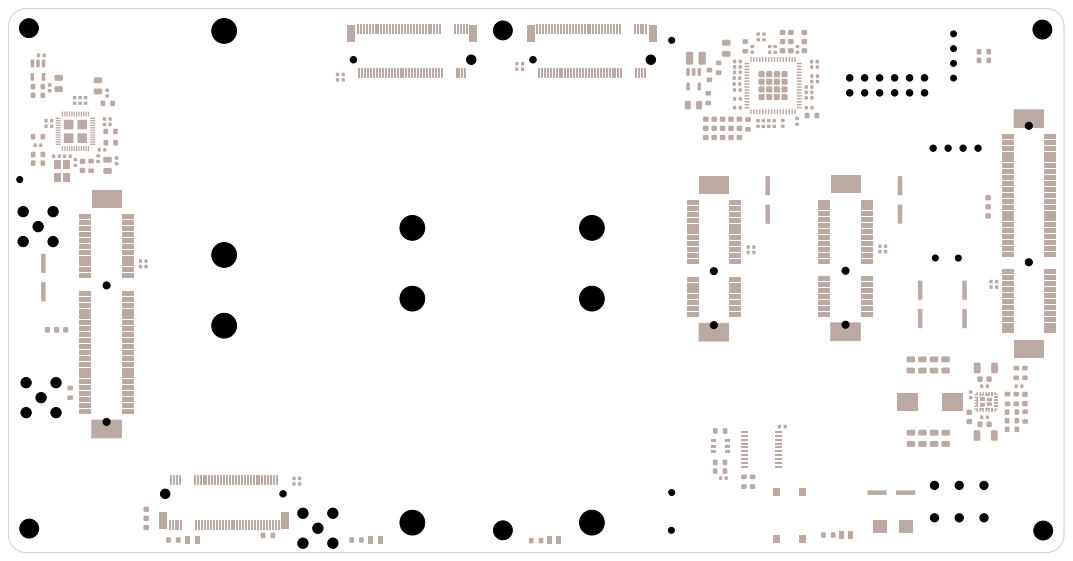
[picture p367: page 7]

COPYRIGHT (C) CHILI.CHIPS.LLC
Sheet:
File: openpci2-backplane.kicad_pcb
Title: openPCIE2 Backplane

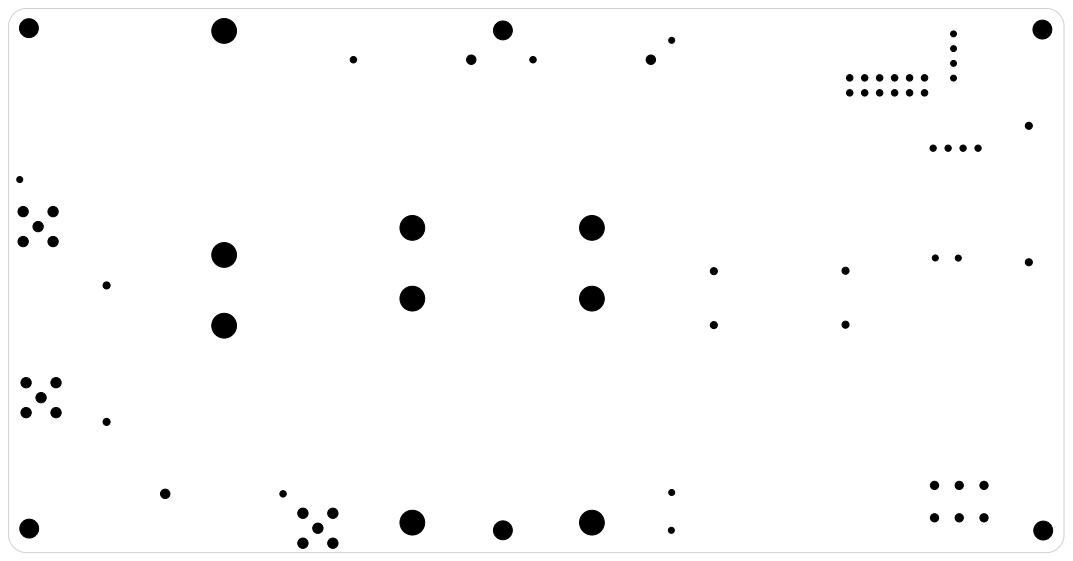
[picture p368: page 8]

COPYRIGHT (C) CHILI.CHIPS.LLC
Sheet:
File: openpci2-backplane.kicad_pcb
Title: openPCIE2 Backplane

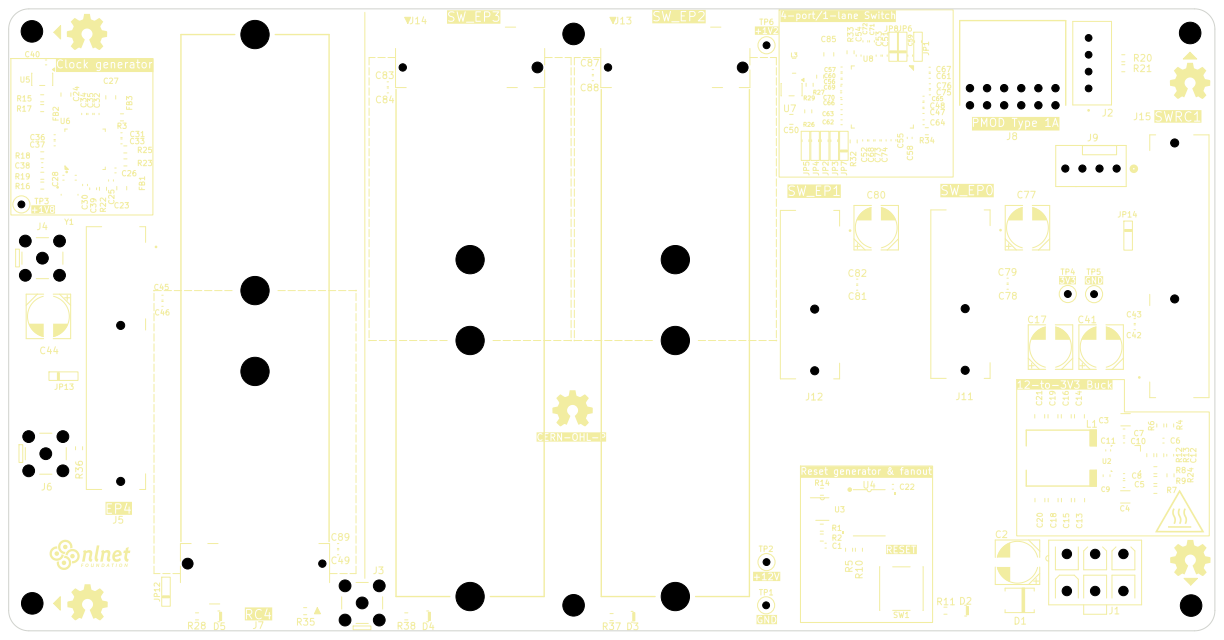
[picture p369: page 9]

COPYRIGHT (C) CHILI.CHIPS.LLC
Sheet:
File: openpci2-backplane.kicad_pcb
Title: openPCIE2 Backplane

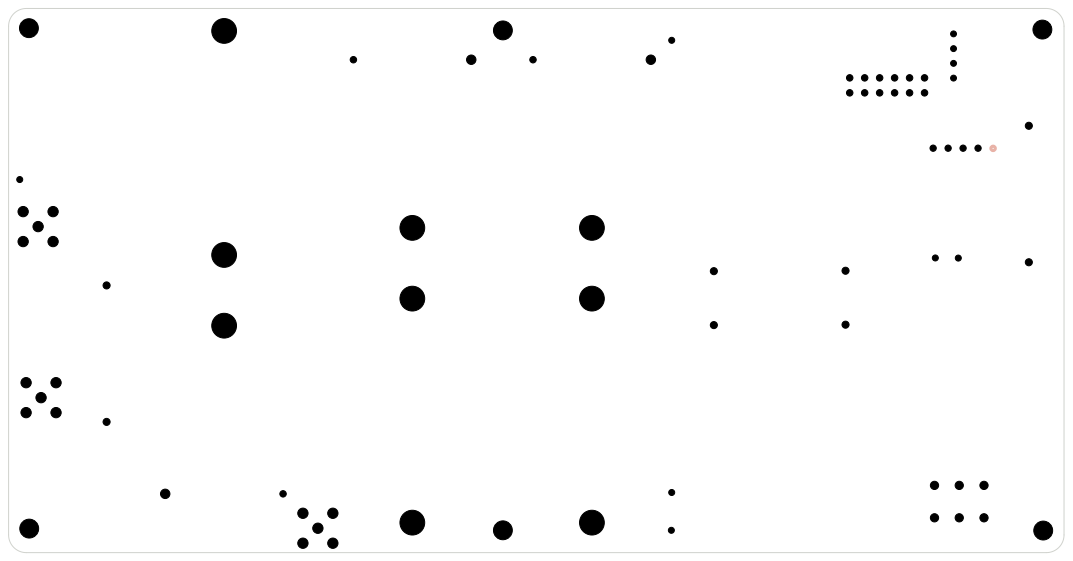
[picture p370: page 10]

COPYRIGHT (C) CHILI.CHIPS.LLC
Sheet:
File: openpci2-backplane.kicad_pcb
Title: openPCIE2 Backplane

COPYRIGHT (C) CHILI.CHIPS.LLC
Sheet:
File: openpci2-backplane.kicad_pcb
Title: openPCIE2 Backplane
