chili-chips-ba/openPCIE/2.rtl/0.common.opensource/src/riscv_pcie_soc.sv

// SPDX-FileCopyrightText: 2026 Chili.CHIPS
//
// SPDX-License-Identifier: BSD-3-Clause

//==========================================================================
// openPCIE * NLnet-sponsored open-source implementation
//--------------------------------------------------------------------------
//                   Copyright (C) 2026 Chili.CHIPS
//
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
// 1. Redistributions of source code must retain the above copyright
// notice, this list of conditions and the following disclaimer.
//
// 2. Redistributions in binary form must reproduce the above copyright
// notice, this list of conditions and the following disclaimer in the
// documentation and/or other materials provided with the distribution.
//
// 3. Neither the name of the copyright holder nor the names of its
// contributors may be used to endorse or promote products derived
// from this software without specific prior written permission.
//
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
//              https://opensource.org/license/bsd-3-clause
//--------------------------------------------------------------------------

`timescale 1ns / 1ps

module riscv_pcie_soc (
    input  logic        clk,
    input  logic        resetn,

    output logic [63:0] s_axis_tx_tdata,
    output logic [7:0]  s_axis_tx_tkeep,
    output logic        s_axis_tx_tlast,
    output logic        s_axis_tx_tvalid,
    input  logic        s_axis_tx_tready,

    input  logic [63:0] m_axis_rx_tdata,
    input  logic [7:0]  m_axis_rx_tkeep,
    input  logic        m_axis_rx_tlast,
    input  logic        m_axis_rx_tvalid,
    output logic        m_axis_rx_tready,

    // TODO (SV interface): cfg sideband shared by host_bridge and the SOC
    // (cfg_status, cfg_command, cfg_msg_received_err_fatal, tx_buf_av). Candidate for a small cfg_if.
    input  logic [15:0] cfg_status,
    input  logic [15:0] cfg_command,
    input  logic        cfg_msg_received_err_fatal,

    input  logic [5:0]  tx_buf_av
);

    logic        mem_valid;
    logic        mem_ready;
    logic [31:0] mem_addr;
    logic [31:0] mem_wdata;
    logic [3:0]  mem_wstrb;
    logic [31:0] mem_rdata;

    logic        ram_ready;
    logic [31:0] ram_rdata;

    logic [31:0] tx_packet_counter;

    logic is_ram;
    logic is_bridge;

    assign is_ram    = (mem_addr[31:24] == 8'h00);
    assign is_bridge = (mem_addr[31:24] == 8'h30);

    // -------------------------------------------------------------------------
    // The CPU -- two interchangeable implementations
    //
    //   default             : the picorv32 RTL core, executing firmware.hex out
    //                         of the instruction RAM below. This is what goes
    //                         into the bitstream.
    //   `define SOC_CPU_VPROC : the VProc virtual processor, so that a native
    //                         C/C++ program or the rv32 ISS drives the very
    //                         same bus. Co-simulation only -- see
    //                         5.sim/models/soc_cpu.VPROC.picorv32.sv and
    //                         "make CPU=vproc" / "make CPU=iss" in 5.sim.
    //
    // Nothing else in the SOC changes: the address decode, the CSR and the PCIe
    // stack see an identical memory interface either way.
    // -------------------------------------------------------------------------
`ifdef SOC_CPU_VPROC
    soc_cpu_vproc #(
        .NODE      (4'd0)
    ) cpu (
        .clk       (clk),
        .resetn    (resetn),
        .mem_valid (mem_valid),
        .mem_ready (mem_ready),
        .mem_addr  (mem_addr),
        .mem_wdata (mem_wdata),
        .mem_wstrb (mem_wstrb),
        .mem_rdata (mem_rdata)
    );
`else
    picorv32 #(
        .PROGADDR_RESET(32'h0000_0000),
        .STACKADDR(32'h0000_2000),
        .BARREL_SHIFTER(1),
        .ENABLE_COUNTERS(1)
    ) cpu (
        .clk       (clk),
        .resetn    (resetn),
        .mem_valid (mem_valid),
        .mem_ready (mem_ready),
        .mem_addr  (mem_addr),
        .mem_wdata (mem_wdata),
        .mem_wstrb (mem_wstrb),
        .mem_rdata (mem_rdata)
    );
`endif

    logic [31:0] ram [0:2047];
    initial begin
        $readmemh("firmware.hex", ram);
    end
    logic [31:0] ram_rdata_reg;
    logic        ram_ready_reg;

    always_ff @(posedge clk) begin
        ram_ready_reg <= 1'b0;
        if (mem_valid && is_ram) begin
            if (mem_wstrb == '0) begin
                ram_rdata_reg <= ram[mem_addr[12:2]];
                ram_ready_reg <= 1'b1;
            end else begin
                if (mem_wstrb[0]) ram[mem_addr[12:2]][7:0]   <= mem_wdata[7:0];
                if (mem_wstrb[1]) ram[mem_addr[12:2]][15:8]  <= mem_wdata[15:8];
                if (mem_wstrb[2]) ram[mem_addr[12:2]][23:16] <= mem_wdata[23:16];
                if (mem_wstrb[3]) ram[mem_addr[12:2]][31:24] <= mem_wdata[31:24];
                ram_ready_reg <= 1'b1;
            end
        end
    end
    assign ram_rdata = ram_rdata_reg;
    assign ram_ready = ram_ready_reg;

    // -------------------------------------------------------------------------
    // PCIe bridge CSR -- two interchangeable implementations
    //
    //   default              : the CSR is generated by PeakRDL out of
    //                          4.build/csr_build/csr.rdl (module "csr", wrapped
    //                          by soc_csr.sv)
    //   `define SOC_CSR_LEGACY : the original hand-written register block, kept
    //                          here as the reference implementation
    //
    // Both present the very same register map to the firmware -- see the
    // address table at the top of csr.rdl.
    // -------------------------------------------------------------------------
    logic [31:0] bridge_rdat;
    logic        bridge_rdy;

    logic [31:0] tx_header0;
    logic [31:0] tx_header1;
    logic [31:0] tx_header2;
    logic [31:0] tx_data;

    typedef enum logic [1:0] {
        IDLE         = 2'd0,
        SEND_CYCLE_1 = 2'd1,
        SEND_CYCLE_2 = 2'd2
    } tx_state_e;
    tx_state_e tx_state;

    logic rx_phase;

    // Switched topology: the target of a Configuration TLP is no longer fixed.
    // The bus number is taken from the address dword the software wrote into
    // tx_header2, and the Type 0 / Type 1 code is derived from it, exactly as
    // the AMD packet generator does it:
    //   bus == 1  -> Type 0, the device sits on the link-attached bus
    //   bus  > 1  -> Type 1, the request has to cross one or more bridges
    // Fmt/Type occupies tx_header0[31:24]; bits [28:25] == 4'b0010 mark a
    // Configuration request and bit [24] is the Type 0 / Type 1 selector.
    // The device number needs no such treatment -- it already travels in
    // tx_header2[23:19], where the completer expects it.
    logic [7:0]  pkt_bus_num;
    logic        pkt_is_cfg;
    logic [31:0] tx_header0_routed;

    assign pkt_bus_num       = tx_header2[31:24];
    assign pkt_is_cfg        = (tx_header0[28:25] == 4'b0010);
    assign tx_header0_routed = pkt_is_cfg
                             ? {tx_header0[31:25], (pkt_bus_num > 8'd1), tx_header0[23:0]}
                             : tx_header0;

`ifdef SOC_CSR_LEGACY
    //=========================================================================
    // Hand-written CSR
    //=========================================================================
    logic [31:0] rx_status_reg;
    logic [31:0] rx_data_reg;
    logic [31:0] rx_header_info_reg;
    logic [31:0] pcie_err_status_reg;

    logic [31:0] pcie_phy_status_reg;

    logic bridge_ready_reg;

    always_ff @(posedge clk) begin
        if (!resetn) begin
            pcie_err_status_reg <= '0;
            pcie_phy_status_reg <= '0;
        end else begin
            pcie_err_status_reg <= {15'b0, cfg_msg_received_err_fatal, cfg_status};
            pcie_phy_status_reg <= {24'b0, tx_state, tx_buf_av};
        end
    end

    always_ff @(posedge clk) begin
        if (!resetn) begin
            tx_state           <= IDLE;
            bridge_ready_reg   <= 1'b0;
            s_axis_tx_tvalid   <= 1'b0;
            rx_status_reg      <= '0;
            rx_data_reg        <= '0;
            rx_header_info_reg <= '0;
            rx_phase           <= 1'b0;

            tx_packet_counter  <= '0;

        end else begin
            bridge_ready_reg <= 1'b0;

            if (mem_valid && is_bridge && !bridge_ready_reg) begin
                bridge_ready_reg <= 1'b1;

                if (mem_wstrb != '0) begin
                    case (mem_addr[4:2])
                        3'b000: tx_header0 <= mem_wdata;
                        3'b001: tx_header1 <= mem_wdata;
                        3'b010: tx_header2 <= mem_wdata;
                        3'b011: begin
                                tx_data  <= mem_wdata;
                                tx_state <= SEND_CYCLE_1;

                                tx_packet_counter <= tx_packet_counter + 32'd1;
                                end
                        default: ;
                    endcase
                end
            end

            case (tx_state)
                IDLE: begin
                    s_axis_tx_tvalid <= 1'b0;
                end
                SEND_CYCLE_1: begin
                    s_axis_tx_tdata  <= {tx_header1, tx_header0_routed};
                    s_axis_tx_tkeep  <= 8'hFF;
                    s_axis_tx_tvalid <= 1'b1;
                    s_axis_tx_tlast  <= 1'b0;
                    if (s_axis_tx_tready) tx_state <= SEND_CYCLE_2;
                end
                SEND_CYCLE_2: begin
                    s_axis_tx_tdata  <= {tx_data, tx_header2};
                    s_axis_tx_tkeep  <= (tx_header0[30] == 1'b1) ? 8'hFF : 8'h0F;
                    s_axis_tx_tvalid <= 1'b1;
                    s_axis_tx_tlast  <= 1'b1;

                    if (s_axis_tx_tready) begin
                        tx_state <= IDLE;
                    end
                end
                default: ;
            endcase

            if (m_axis_rx_tvalid) begin
                if (rx_phase == 1'b0) begin
                    if (m_axis_rx_tdata[28:24] == 5'b01010) begin
                         rx_status_reg <= {29'b0, m_axis_rx_tdata[47:45]};
                         rx_phase <= 1'b1;
                    end
                end
                else begin
                    rx_header_info_reg <= m_axis_rx_tdata[31:0];
                    rx_data_reg        <= m_axis_rx_tdata[63:32];
                    if (m_axis_rx_tlast) begin
                        rx_phase <= 1'b0;
                    end
                end
            end
        end
    end

    always_comb begin
        if (mem_addr[5]) begin
             bridge_rdat = pcie_phy_status_reg;
        end else begin

            case (mem_addr[4:2])
                3'b100:  bridge_rdat = rx_status_reg;
                3'b101:  bridge_rdat = rx_data_reg;
                3'b110:  bridge_rdat = rx_header_info_reg;
                3'b111:  bridge_rdat = pcie_err_status_reg;
                default: bridge_rdat = '0;
            endcase
        end
    end

    assign bridge_rdy = bridge_ready_reg;

`else
    //=========================================================================
    // PeakRDL-generated CSR
    //
    // The register storage, the read mux and the bus handshake all live in the
    // generated block now. What stays here is the logic that the registers
    // drive and that drives them back: the Tx FSM and the Rx capture.
    //=========================================================================
    csr_pkg::csr__in_t  hwif_in;
    csr_pkg::csr__out_t hwif_out;

    soc_csr u_soc_csr (
        .clk      (clk),
        .resetn   (resetn),

        .sel      (is_bridge),
        .vld      (mem_valid),
        .we       (mem_wstrb),
        .addr     (mem_addr[5:2]),
        .wdat     (mem_wdata),
        .rdat     (bridge_rdat),
        .rdy      (bridge_rdy),

        .hwif_in  (hwif_in),
        .hwif_out (hwif_out)
    );

    // ---- Tx: the CPU-written registers feed the FSM -------------------------
    // Writing tx.data is what launches a transfer, hence "swmod" -- the strobe
    // PeakRDL raises on the cycle software modifies that field.
    logic tx_start;

    assign tx_header0 = hwif_out.tx.header0.hdr.value;
    assign tx_header1 = hwif_out.tx.header1.hdr.value;
    assign tx_header2 = hwif_out.tx.header2.hdr.value;
    assign tx_data    = hwif_out.tx.data.payload.value;
    assign tx_start   = hwif_out.tx.data.payload.swmod;

    always_ff @(posedge clk) begin
        if (!resetn) begin
            tx_state          <= IDLE;
            s_axis_tx_tvalid  <= 1'b0;
            tx_packet_counter <= '0;

        end else begin
            if (tx_start) begin
                tx_state          <= SEND_CYCLE_1;
                tx_packet_counter <= tx_packet_counter + 32'd1;
            end

            case (tx_state)
                IDLE: begin
                    s_axis_tx_tvalid <= 1'b0;
                end
                SEND_CYCLE_1: begin
                    s_axis_tx_tdata  <= {tx_header1, tx_header0_routed};
                    s_axis_tx_tkeep  <= 8'hFF;
                    s_axis_tx_tvalid <= 1'b1;
                    s_axis_tx_tlast  <= 1'b0;
                    if (s_axis_tx_tready) tx_state <= SEND_CYCLE_2;
                end
                SEND_CYCLE_2: begin
                    s_axis_tx_tdata  <= {tx_data, tx_header2};
                    s_axis_tx_tkeep  <= (tx_header0[30] == 1'b1) ? 8'hFF : 8'h0F;
                    s_axis_tx_tvalid <= 1'b1;
                    s_axis_tx_tlast  <= 1'b1;

                    if (s_axis_tx_tready) begin
                        tx_state <= IDLE;
                    end
                end
                default: ;
            endcase
        end
    end

    // ---- Rx: the completion TLP is written straight into the CSR fields -----
    // 1st beat carries the Completion header DW0/DW1 (Fmt/Type 5'b01010 marks a
    // Completion), the 2nd one DW2 and the payload DWORD.
    logic rx_cpl_dw0;
    logic rx_cpl_dw2;

    assign rx_cpl_dw0 =  m_axis_rx_tvalid & (rx_phase == 1'b0)
                       & (m_axis_rx_tdata[28:24] == 5'b01010);
    assign rx_cpl_dw2 =  m_axis_rx_tvalid & (rx_phase == 1'b1);

    always_ff @(posedge clk) begin
        if (!resetn) begin
            rx_phase <= 1'b0;
        end else if (rx_cpl_dw0) begin
            rx_phase <= 1'b1;
        end else if (rx_cpl_dw2 && m_axis_rx_tlast) begin
            rx_phase <= 1'b0;
        end
    end

    assign hwif_in.rx.status.cpl_status.we          = rx_cpl_dw0;
    assign hwif_in.rx.status.cpl_status.next        = m_axis_rx_tdata[47:45];

    assign hwif_in.rx.data.payload.we               = rx_cpl_dw2;
    assign hwif_in.rx.data.payload.next             = m_axis_rx_tdata[63:32];

    assign hwif_in.rx.header_info.requester_id.we   = rx_cpl_dw2;
    assign hwif_in.rx.header_info.requester_id.next = m_axis_rx_tdata[31:16];
    assign hwif_in.rx.header_info.tag.we            = rx_cpl_dw2;
    assign hwif_in.rx.header_info.tag.next          = m_axis_rx_tdata[15:8];
    assign hwif_in.rx.header_info.lower_addr.we     = rx_cpl_dw2;
    assign hwif_in.rx.header_info.lower_addr.next   = m_axis_rx_tdata[6:0];

    // ---- Status: straight from the hard macro, no shadow registers ----------
    assign hwif_in.status.err.cfg_status.next       = cfg_status;
    assign hwif_in.status.err.msg_err_fatal.next    = cfg_msg_received_err_fatal;

    assign hwif_in.status.phy.tx_state.next         = tx_state;
    assign hwif_in.status.phy.tx_buf_av.next        = tx_buf_av;

`endif

    assign m_axis_rx_tready = 1'b1;

    always_comb begin
        if (is_ram) begin
            mem_rdata = ram_rdata;
        end else if (is_bridge) begin
            mem_rdata = bridge_rdat;
        end else begin
            mem_rdata = 32'hDEADBEEF;
        end
    end

    assign mem_ready = ram_ready || bridge_rdy;

endmodule

// -----------------------------------------------------------------------------
// Project:     openPCIE
// Description: NLnet-sponsored open-source implementation
// Version:     1.0
// Date:        May 24, 2024
// -----------------------------------------------------------------------------
