chili-chips-ba/openPCIE/2.rtl/0.common.opensource/src/pcie/stream_rx_path.sv

// SPDX-FileCopyrightText: 2026 Chili.CHIPS
//
// SPDX-License-Identifier: BSD-3-Clause

//==========================================================================
// openPCIE * NLnet-sponsored open-source implementation
//--------------------------------------------------------------------------
//                   Copyright (C) 2026 Chili.CHIPS
//
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
// 1. Redistributions of source code must retain the above copyright
// notice, this list of conditions and the following disclaimer.
//
// 2. Redistributions in binary form must reproduce the above copyright
// notice, this list of conditions and the following disclaimer in the
// documentation and/or other materials provided with the distribution.
//
// 3. Neither the name of the copyright holder nor the names of its
// contributors may be used to endorse or promote products derived
// from this software without specific prior written permission.
//
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
//              https://opensource.org/license/bsd-3-clause
//--------------------------------------------------------------------------

module stream_rx_path #(
  localparam int C_DATA_WIDTH = 64,
  localparam int KEEP_WIDTH   = 8,
  localparam int REM_WIDTH    = 1
  ) (

  output logic [C_DATA_WIDTH-1:0] m_axis_rx_tdata,
  output logic                    m_axis_rx_tvalid,
  input                         m_axis_rx_tready,
  output       [KEEP_WIDTH-1:0] m_axis_rx_tkeep,
  output                        m_axis_rx_tlast,
  output logic             [21:0] m_axis_rx_tuser,

  input      [C_DATA_WIDTH-1:0] trn_rd,
  input                         trn_rsof,
  input                         trn_reof,
  input                         trn_rsrc_rdy,
  output logic                    trn_rdst_rdy,
  input                         trn_rsrc_dsc,
  input         [REM_WIDTH-1:0] trn_rrem,
  input                         trn_rerrfwd,
  input                   [6:0] trn_rbar_hit,
  input                         trn_recrc_err,

  input                         null_rx_tvalid,
  input                         null_rx_tlast,
  input        [KEEP_WIDTH-1:0] null_rx_tkeep,
  input                         null_rdst_rdy,
  input                   [4:0] null_is_eof,

  output                  [2:0] np_counter,
  input                         user_clk,
  input                         user_rst
);


wire              [4:0] is_sof;
wire              [4:0] is_sof_prev;

wire              [4:0] is_eof;
wire              [4:0] is_eof_prev;

logic    [KEEP_WIDTH-1:0] reg_tkeep;
wire   [KEEP_WIDTH-1:0] tkeep;
wire   [KEEP_WIDTH-1:0] tkeep_prev;

logic                     reg_tlast;
wire                    rsrc_rdy_filtered;

wire [C_DATA_WIDTH-1:0] trn_rd_DW_swapped;
logic  [C_DATA_WIDTH-1:0] trn_rd_prev;

wire                    data_hold;
logic                     data_prev;

logic                     trn_reof_prev;
logic     [REM_WIDTH-1:0] trn_rrem_prev;
logic                     trn_rsrc_rdy_prev;
logic                     trn_rsrc_dsc_prev;
logic                     trn_rsof_prev;
logic               [6:0] trn_rbar_hit_prev;
logic                     trn_rerrfwd_prev;
logic                     trn_recrc_err_prev;

logic                     null_mux_sel;
logic                     trn_in_packet;
wire                    dsc_flag;
wire                    dsc_detect;
logic                     reg_dsc_detect;
logic                     trn_rsrc_dsc_d;


assign rsrc_rdy_filtered = trn_rsrc_rdy &&
                                 (trn_in_packet || (trn_rsof && !trn_rsrc_dsc));
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
